Exprezz0/F-18C_Simulator/ECAD/PCBs/ABSIS/ABSIS_ALE/Assets/ABSIS_ALE-TOP_ISO.png

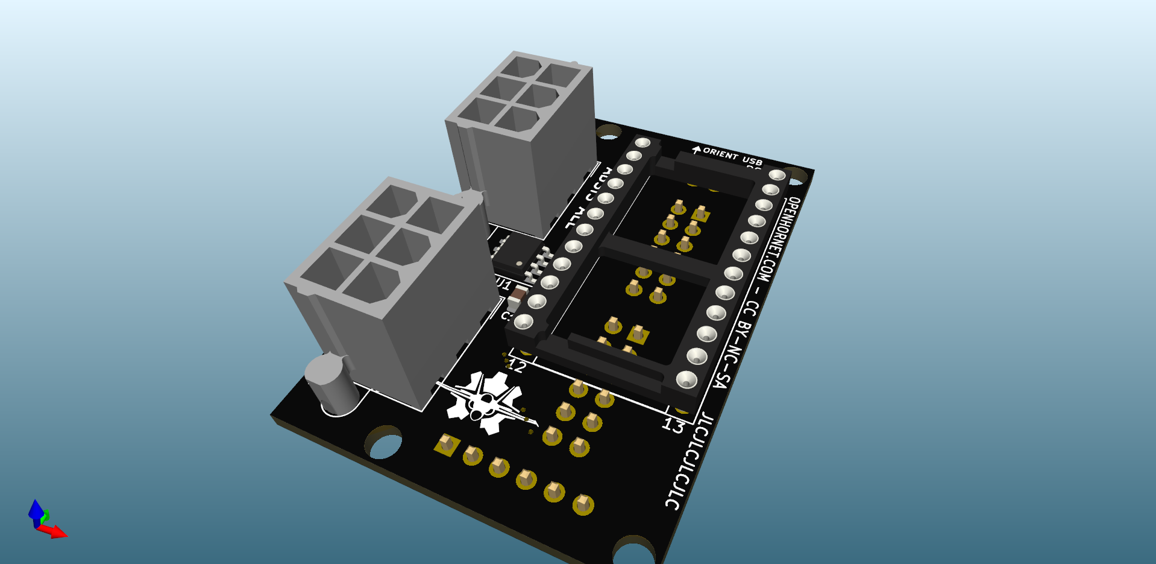
ECAD/PCBs/ABSIS/ABSIS_ALE/Assets/ABSIS_ALE-TOP_ISO.png
