Exprezz0/F-18C_Simulator/ECAD/PCBs/ABSIS/ABSIS_ALE_Relay_Module/meta/brd.png

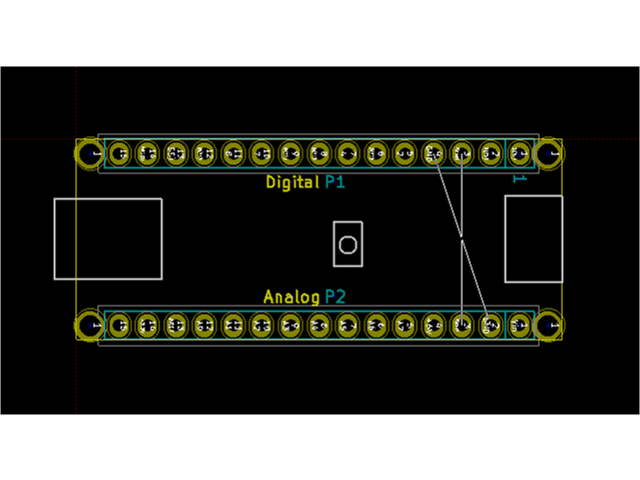
ECAD/PCBs/ABSIS/ABSIS_ALE_Relay_Module/meta/brd.png
