Exprezz0/F-18C_Simulator/ECAD/PCBs/ABSIS/ABSIS_Pit Management System/Assets/ABSIS_Pit Management System-BOT.png

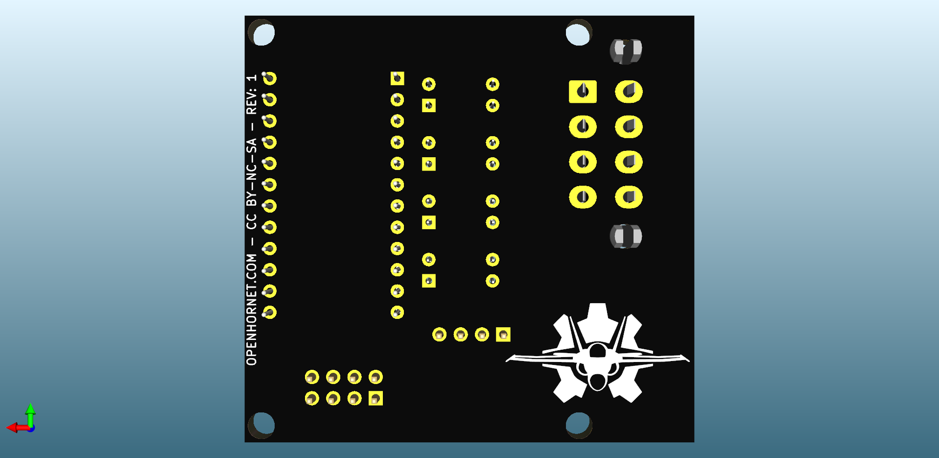
ECAD/PCBs/ABSIS/ABSIS_Pit Management System/Assets/ABSIS_Pit Management System-BOT.png
