Exprezz0/F-18C_Simulator/ECAD/PCBs/ABSIS/ABSIS_Pit Management System/Assets/ABSIS_Pit Management System-BOT_ISO.png

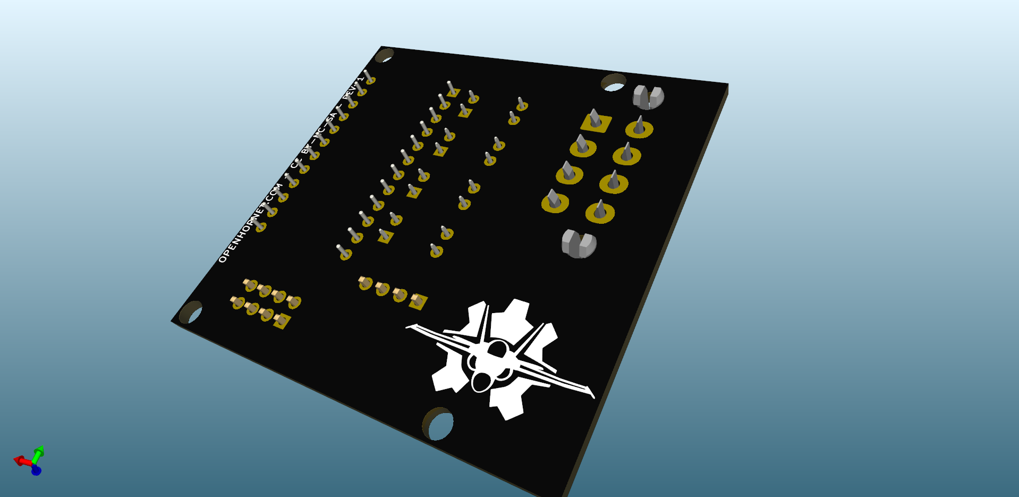
ECAD/PCBs/ABSIS/ABSIS_Pit Management System/Assets/ABSIS_Pit Management System-BOT_ISO.png
