Exprezz0/F-18C_Simulator/ECAD/PCBs/Backlight PCBs/Backlighting_Type A/ANT SEL PANEL/Assets/ANT SEL PANEL-TOP.png

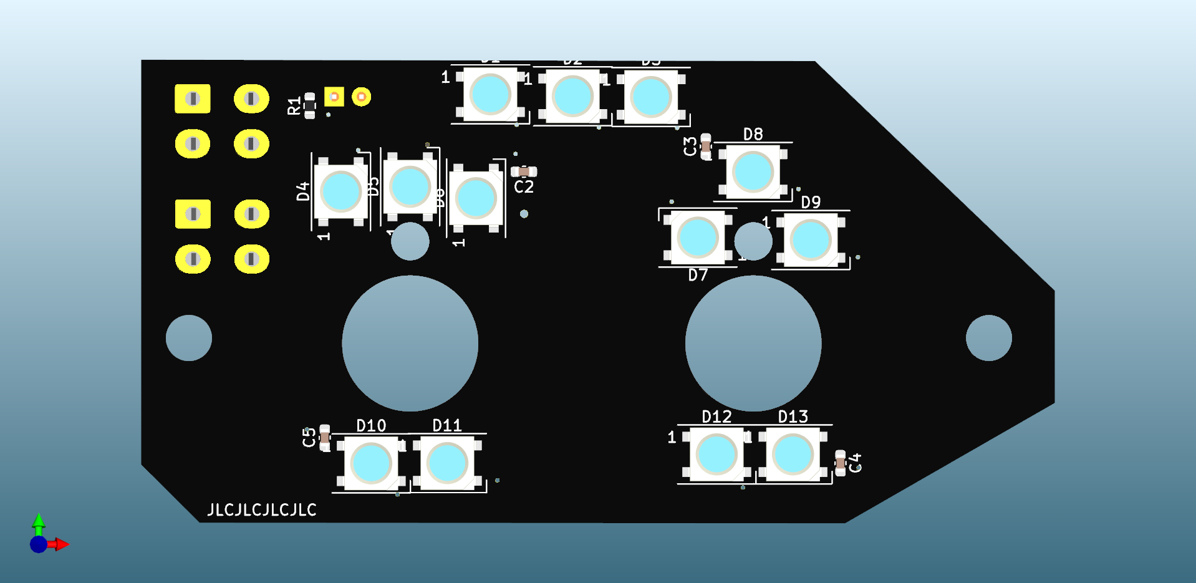
ECAD/PCBs/Backlight PCBs/Backlighting_Type A/ANT SEL PANEL/Assets/ANT SEL PANEL-TOP.png
