Exprezz0/F-18C_Simulator/ECAD/PCBs/Backlight PCBs/Backlighting_Type A/APU PANEL/Assets/APU PANEL-BOT_ISO.png

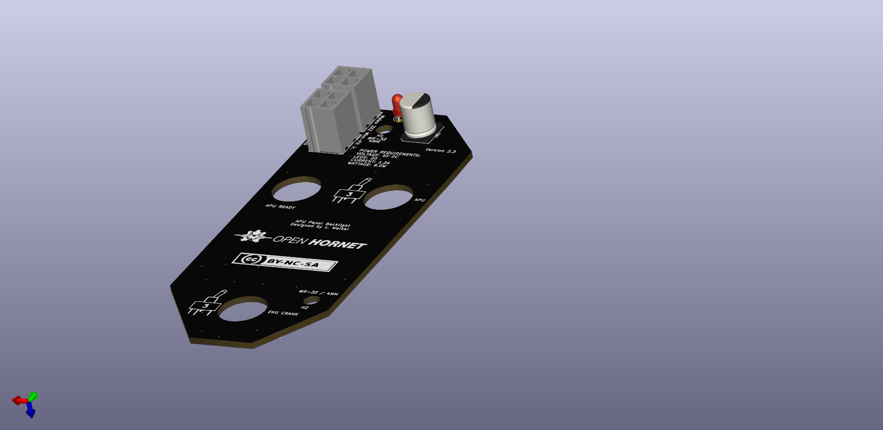
ECAD/PCBs/Backlight PCBs/Backlighting_Type A/APU PANEL/Assets/APU PANEL-BOT_ISO.png
