Exprezz0/F-18C_Simulator/ECAD/PCBs/Backlight PCBs/Backlighting_Type A/AV COOL PANEL/Assets/AV COOL PANEL-TOP_ISO.png

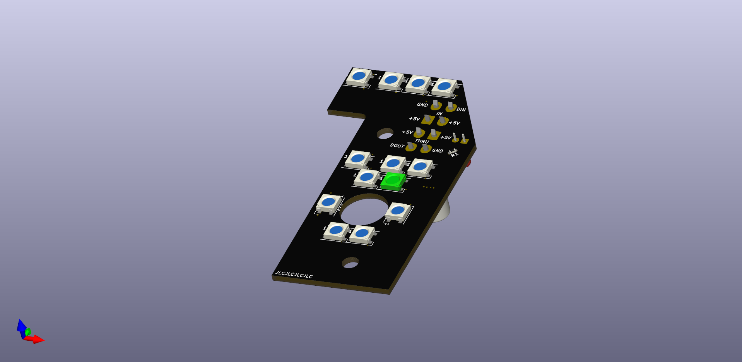
ECAD/PCBs/Backlight PCBs/Backlighting_Type A/AV COOL PANEL/Assets/AV COOL PANEL-TOP_ISO.png
