Exprezz0/F-18C_Simulator/ECAD/PCBs/Backlight PCBs/Backlighting_Type A/CAUTION LIGHTS PANEL/Assets/CAUTION LIGHTS PANEL-TOP.png

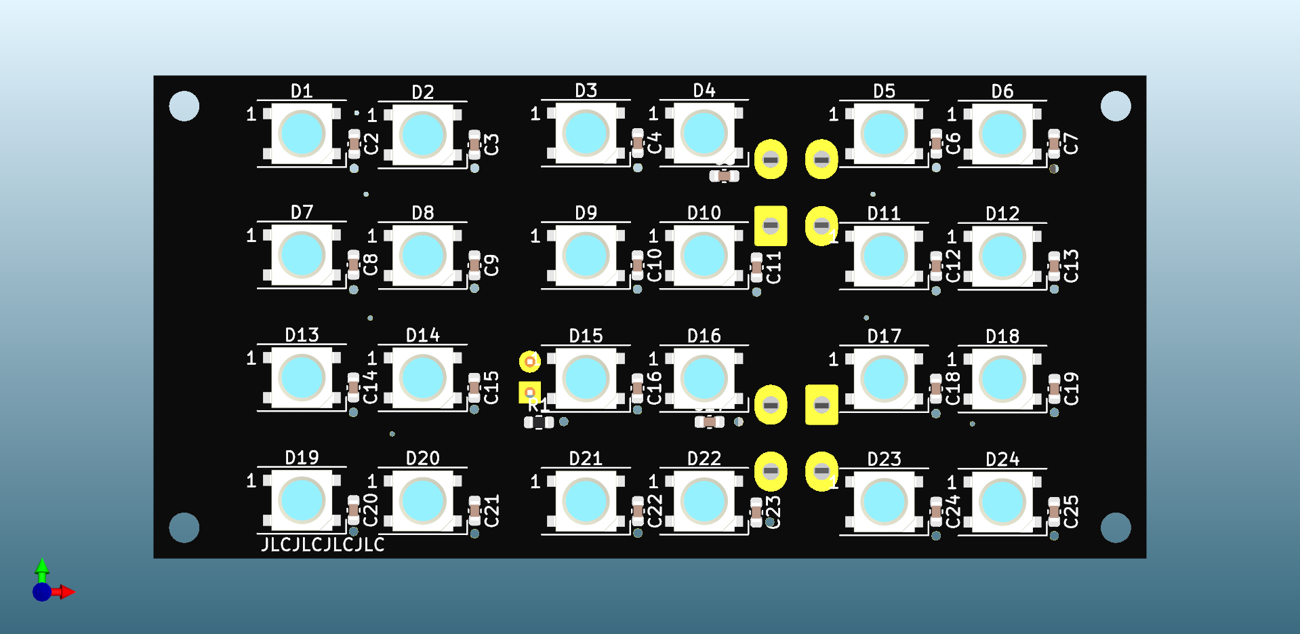
ECAD/PCBs/Backlight PCBs/Backlighting_Type A/CAUTION LIGHTS PANEL/Assets/CAUTION LIGHTS PANEL-TOP.png
