Exprezz0/F-18C_Simulator/ECAD/PCBs/Backlight PCBs/Backlighting_Type A/COMM PANEL/Assets/COMM PANEL-BOT.png

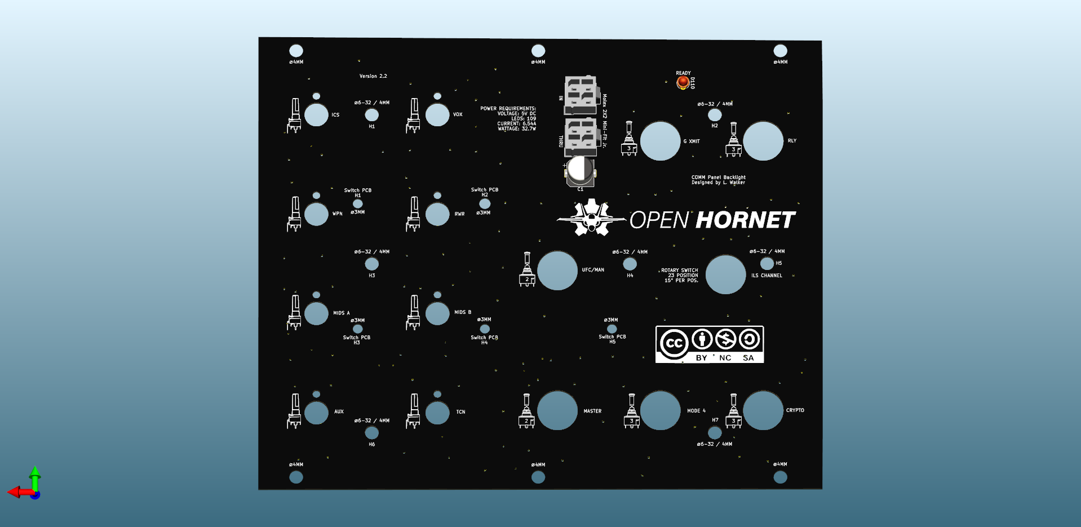
ECAD/PCBs/Backlight PCBs/Backlighting_Type A/COMM PANEL/Assets/COMM PANEL-BOT.png
