Exprezz0/F-18C_Simulator/ECAD/PCBs/Backlight PCBs/Backlighting_Type A/DEFOG PANEL/Assets/DEFOG PANEL_TOP-ISO.png

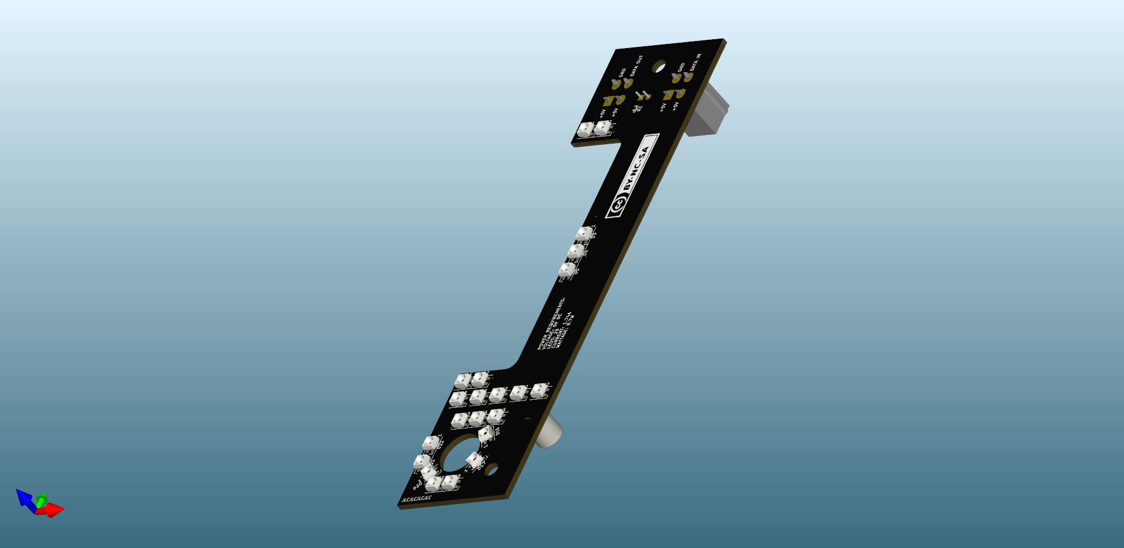
ECAD/PCBs/Backlight PCBs/Backlighting_Type A/DEFOG PANEL/Assets/DEFOG PANEL_TOP-ISO.png
