Exprezz0/F-18C_Simulator/ECAD/PCBs/Backlight PCBs/Backlighting_Type A/ECM DISP PANEL/Assets/ECM DISP PANEL_TOP-ISO.png

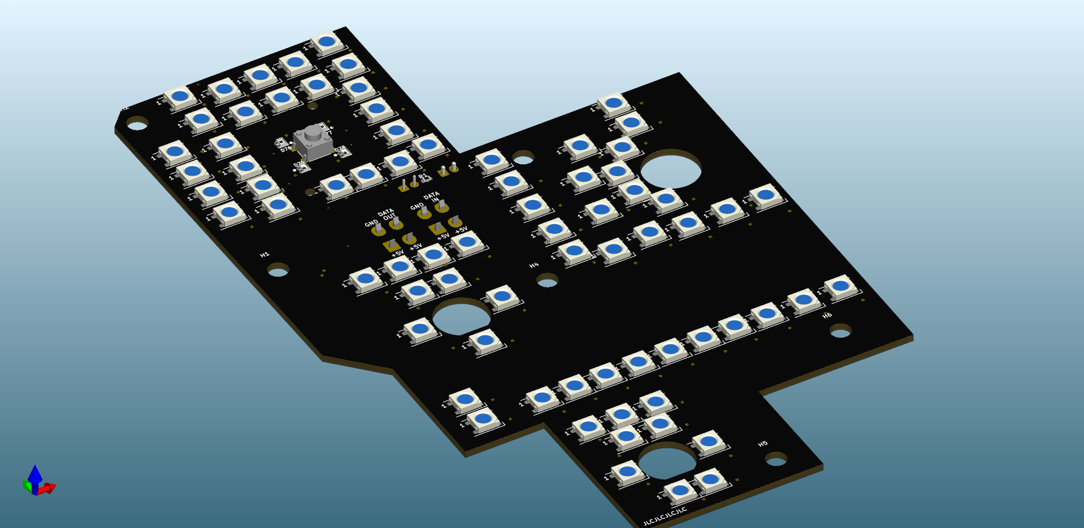
ECAD/PCBs/Backlight PCBs/Backlighting_Type A/ECM DISP PANEL/Assets/ECM DISP PANEL_TOP-ISO.png
