Exprezz0/F-18C_Simulator/ECAD/PCBs/Backlight PCBs/Backlighting_Type A/ELEC PANEL/Assets/ELEC PANEL_BOT.png

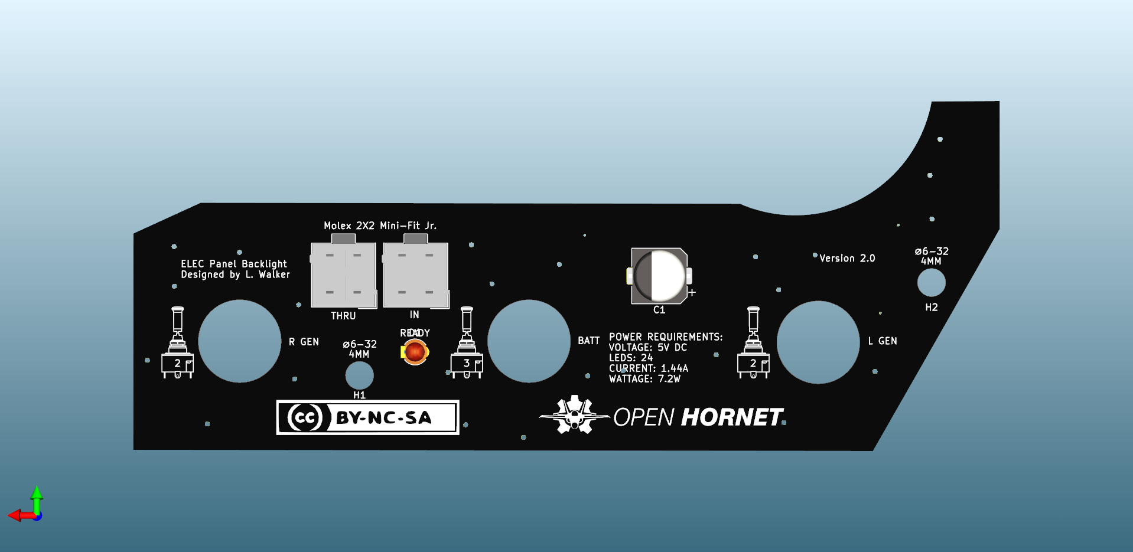
ECAD/PCBs/Backlight PCBs/Backlighting_Type A/ELEC PANEL/Assets/ELEC PANEL_BOT.png
