Exprezz0/F-18C_Simulator/ECAD/PCBs/Backlight PCBs/Backlighting_Type A/FUEL PANEL/Assets/FUEL PANEL_TOP-ISO.png

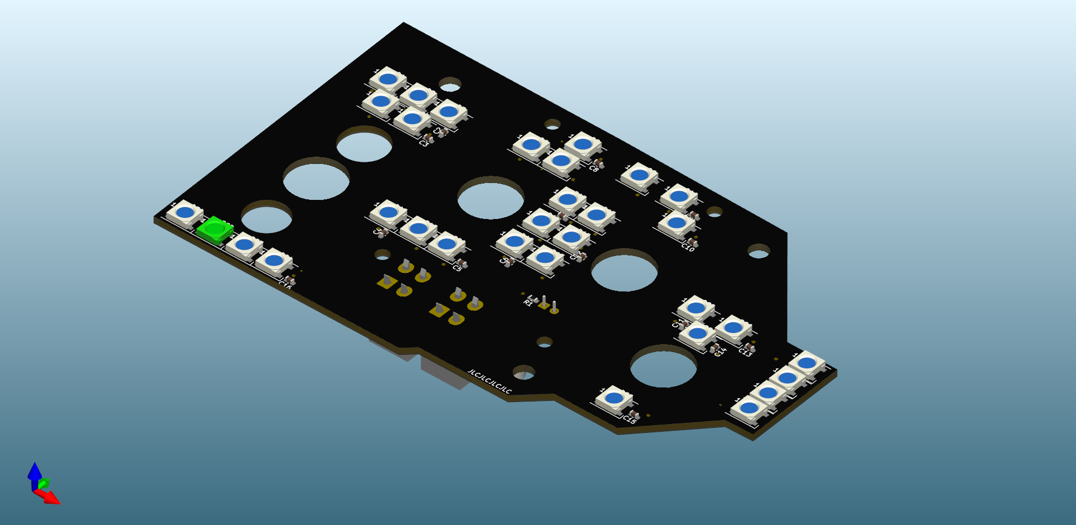
ECAD/PCBs/Backlight PCBs/Backlighting_Type A/FUEL PANEL/Assets/FUEL PANEL_TOP-ISO.png
