Exprezz0/F-18C_Simulator/ECAD/PCBs/Backlight PCBs/Backlighting_Type A/GEN TIE PANEL/Assets/GEN TIE PANEL_BOT.png

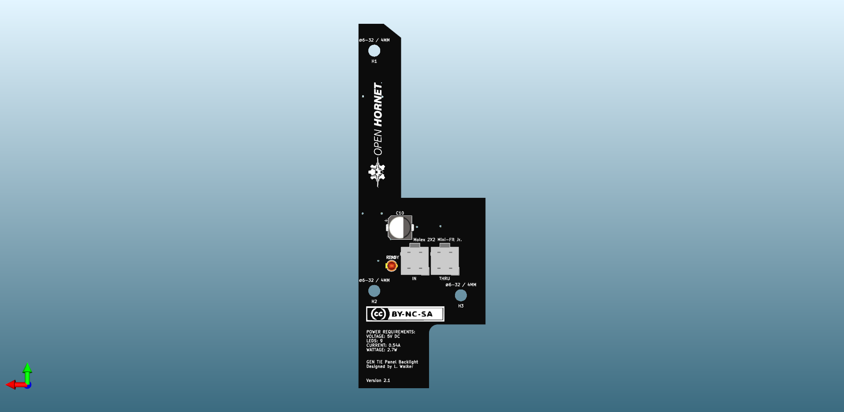
ECAD/PCBs/Backlight PCBs/Backlighting_Type A/GEN TIE PANEL/Assets/GEN TIE PANEL_BOT.png
