Exprezz0/F-18C_Simulator/ECAD/PCBs/Backlight PCBs/Backlighting_Type A/HUD PANEL/Assets/HUD PANEL_TOP.png

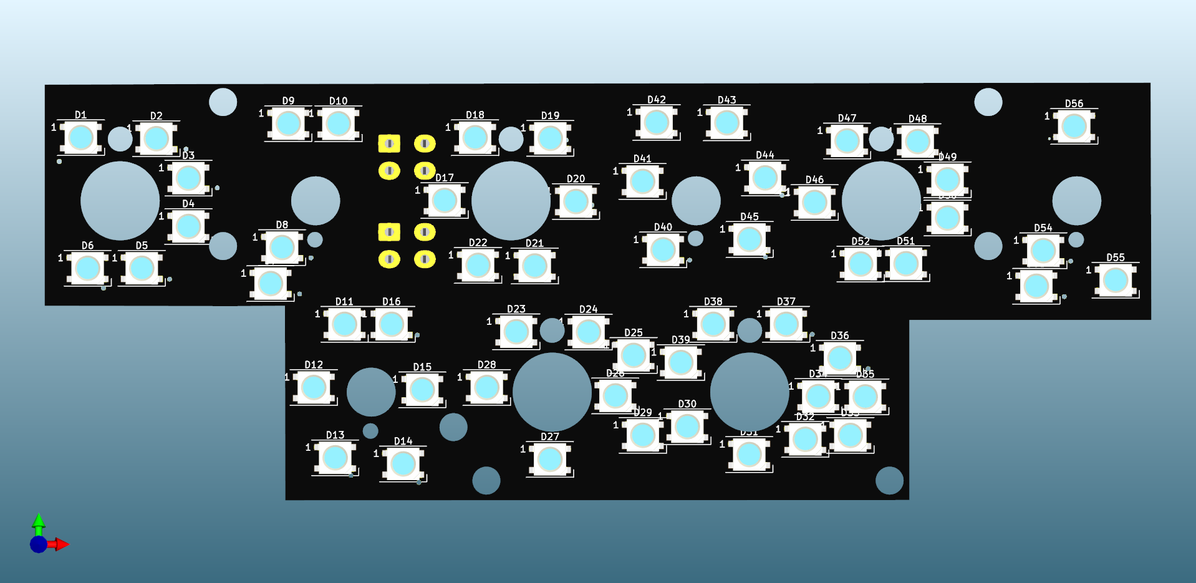
ECAD/PCBs/Backlight PCBs/Backlighting_Type A/HUD PANEL/Assets/HUD PANEL_TOP.png
