Exprezz0/F-18C_Simulator/ECAD/PCBs/Backlight PCBs/Backlighting_Type A/HUD VID RCD PANEL/Assets/HUD VID RCD PANEL_BOT.png

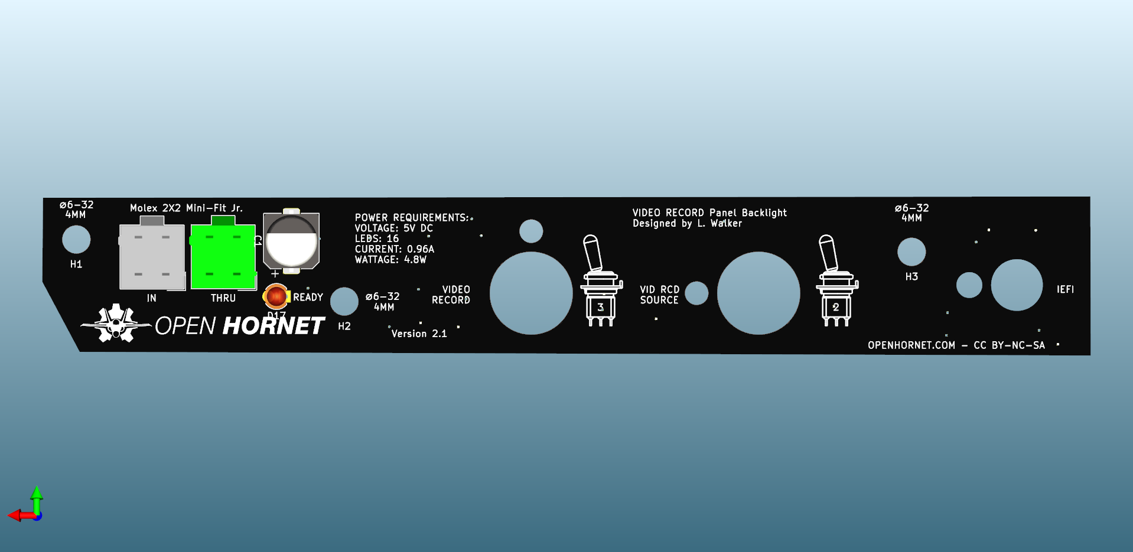
ECAD/PCBs/Backlight PCBs/Backlighting_Type A/HUD VID RCD PANEL/Assets/HUD VID RCD PANEL_BOT.png
