Exprezz0/F-18C_Simulator/ECAD/PCBs/Backlight PCBs/Backlighting_Type A/HYD ISO PANEL/Assets/HYD ISO PANEL_BOT.png

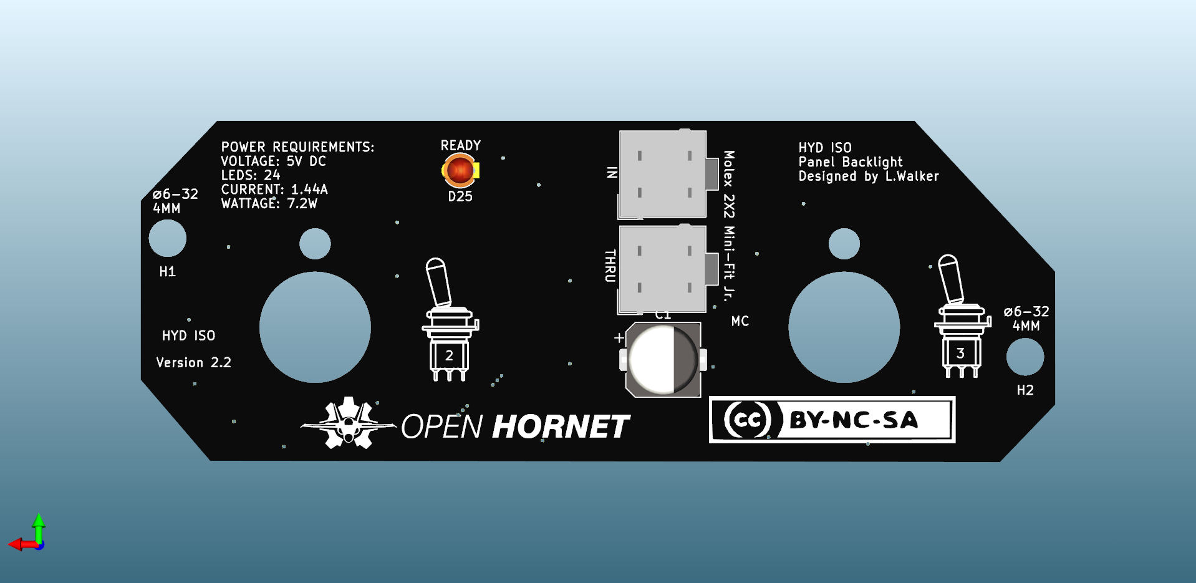
ECAD/PCBs/Backlight PCBs/Backlighting_Type A/HYD ISO PANEL/Assets/HYD ISO PANEL_BOT.png
