Exprezz0/F-18C_Simulator/ECAD/PCBs/Backlight PCBs/Backlighting_Type A/INTR LT PANEL/Assets/INTR LT PANEL-BOT_ISO.png

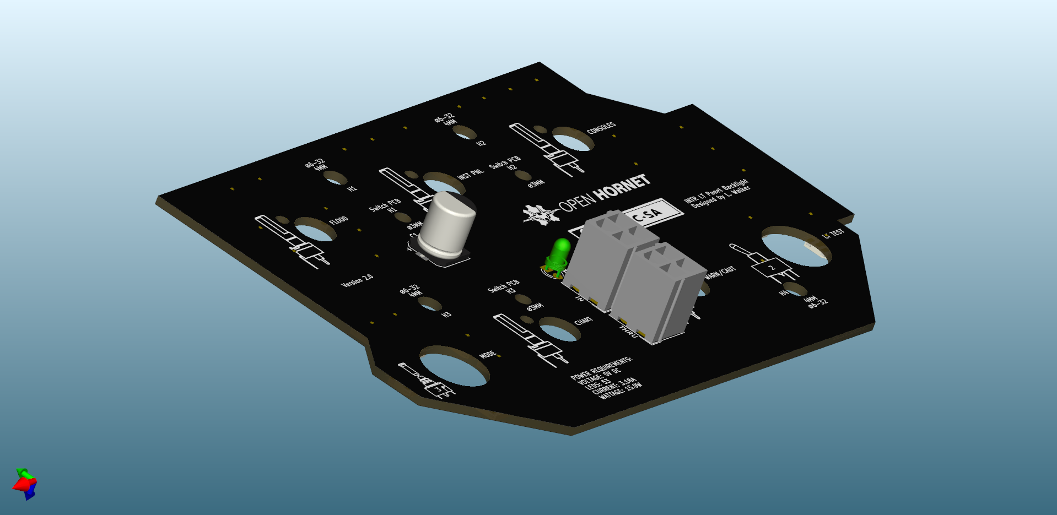
ECAD/PCBs/Backlight PCBs/Backlighting_Type A/INTR LT PANEL/Assets/INTR LT PANEL-BOT_ISO.png
