Exprezz0/F-18C_Simulator/ECAD/PCBs/Backlight PCBs/Backlighting_Type A/JETT STATION SELECT PLACARD/Assets/JETT STATION SELECT PLACARD_BOT.png

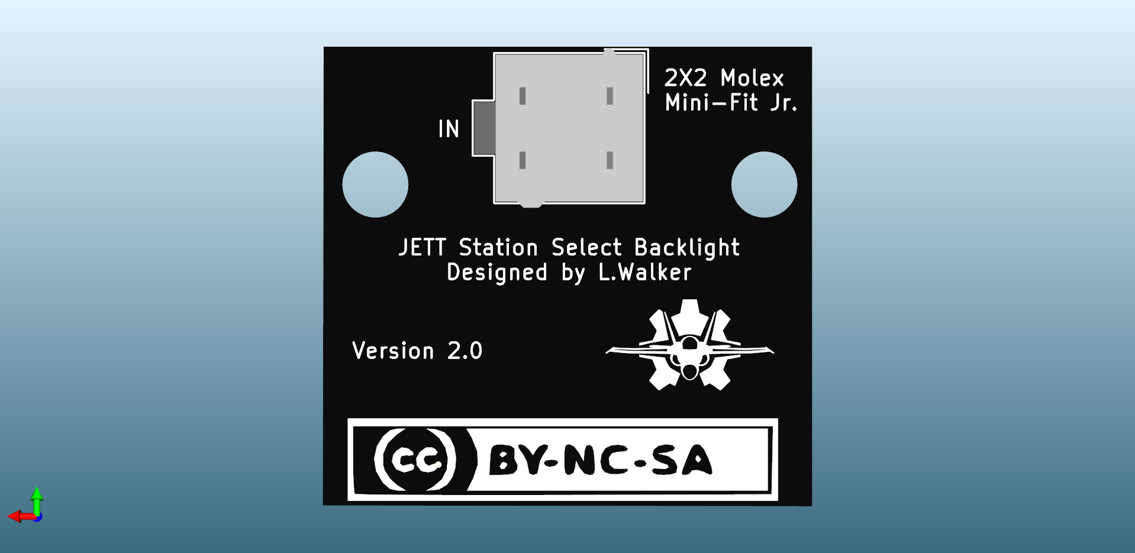
ECAD/PCBs/Backlight PCBs/Backlighting_Type A/JETT STATION SELECT PLACARD/Assets/JETT STATION SELECT PLACARD_BOT.png
