Exprezz0/F-18C_Simulator/ECAD/PCBs/Backlight PCBs/Backlighting_Type A/KY-58 PANEL/Assets/KY-58 PANEL_TOP-ISO.png

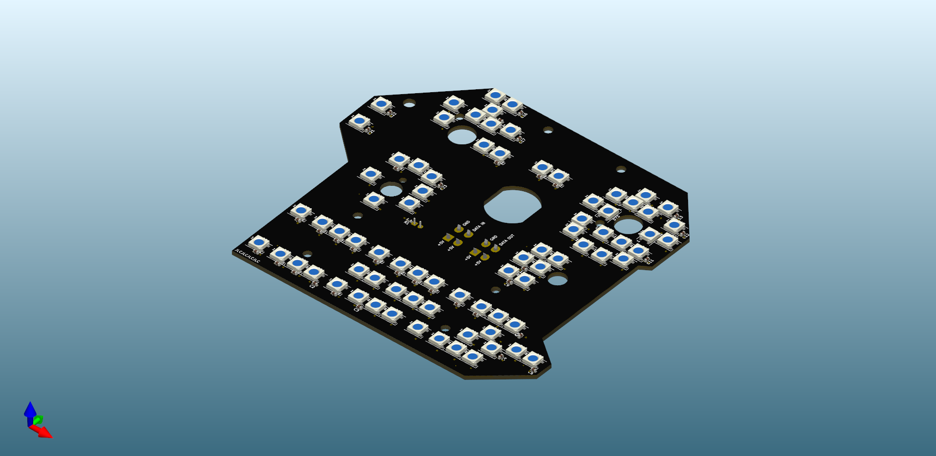
ECAD/PCBs/Backlight PCBs/Backlighting_Type A/KY-58 PANEL/Assets/KY-58 PANEL_TOP-ISO.png
