Exprezz0/F-18C_Simulator/ECAD/PCBs/Backlight PCBs/Backlighting_Type A/LANDING GEAR PANEL/Assets/LANDING GEAR PANEL_BOT.png

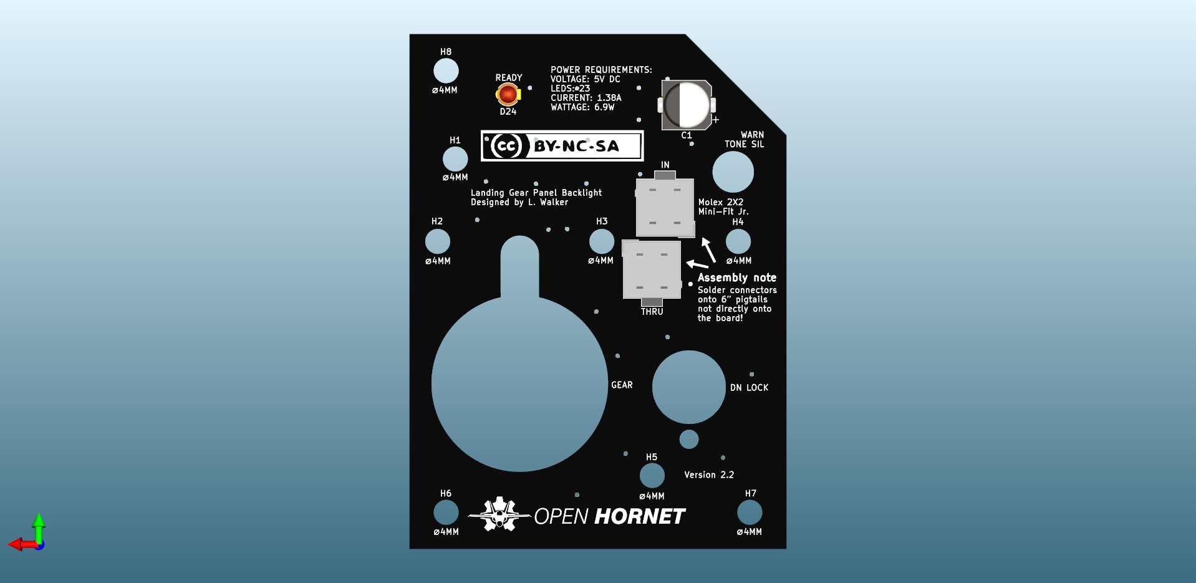
ECAD/PCBs/Backlight PCBs/Backlighting_Type A/LANDING GEAR PANEL/Assets/LANDING GEAR PANEL_BOT.png
