Exprezz0/F-18C_Simulator/ECAD/PCBs/Backlight PCBs/Backlighting_Type A/LDG WING FOLD PLACARD/Assets/LDG WING FOLD PLACARD_BOT-ISO.png

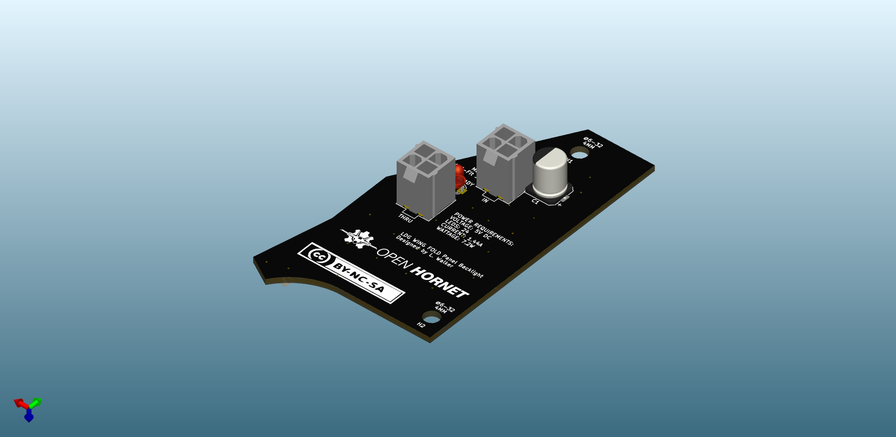
ECAD/PCBs/Backlight PCBs/Backlighting_Type A/LDG WING FOLD PLACARD/Assets/LDG WING FOLD PLACARD_BOT-ISO.png
