Exprezz0/F-18C_Simulator/ECAD/PCBs/Backlight PCBs/Backlighting_Type A/MASTER ARM PANEL/Assets/MASTER ARM PANEL_TOP-ISO.png

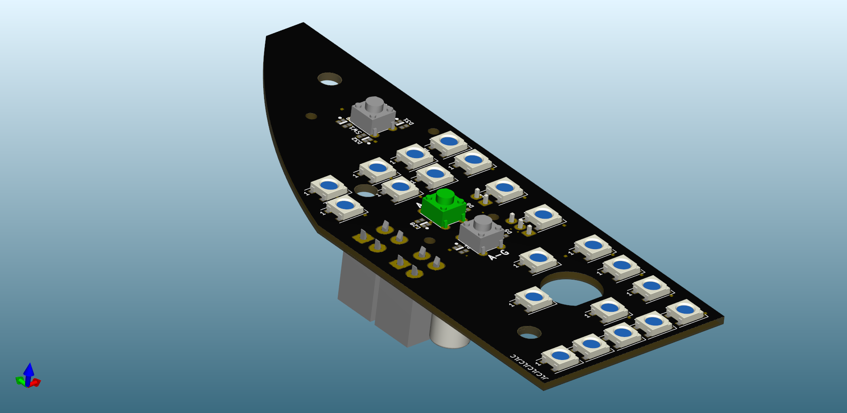
ECAD/PCBs/Backlight PCBs/Backlighting_Type A/MASTER ARM PANEL/Assets/MASTER ARM PANEL_TOP-ISO.png
