Exprezz0/F-18C_Simulator/ECAD/PCBs/Backlight PCBs/Backlighting_Type A/OBOGS PANEL/Assets/OBOGS PANEL_TOP-ISO.png

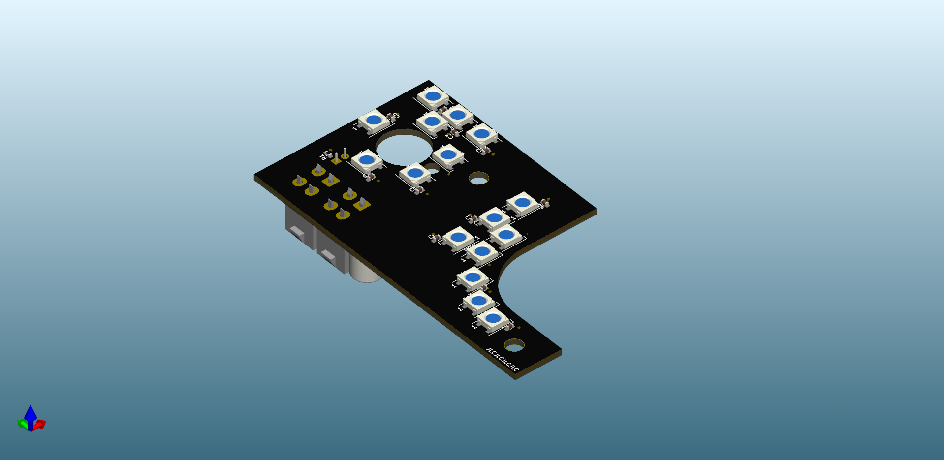
ECAD/PCBs/Backlight PCBs/Backlighting_Type A/OBOGS PANEL/Assets/OBOGS PANEL_TOP-ISO.png
