Exprezz0/F-18C_Simulator/ECAD/PCBs/Backlight PCBs/Backlighting_Type A/SELECT JETT PANEL/Assets/SELECT JETT PANEL_BOT-ISO.png

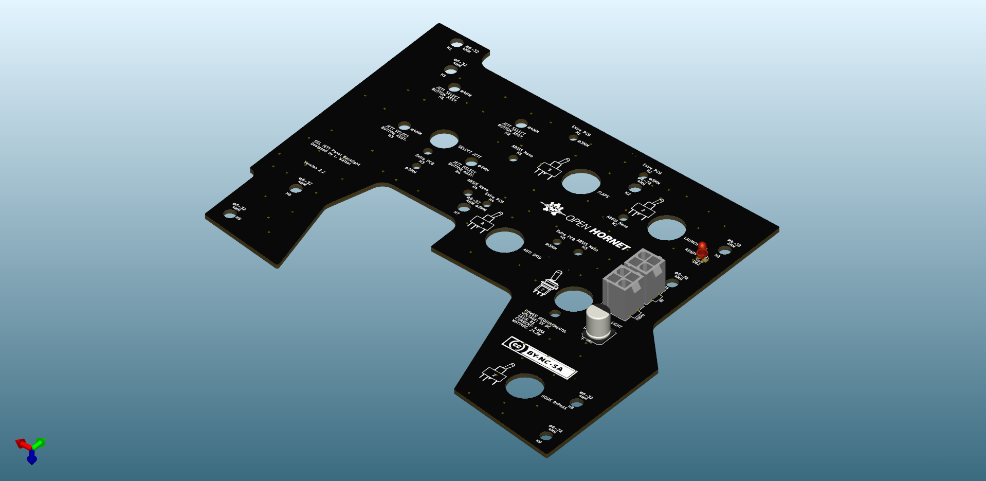
ECAD/PCBs/Backlight PCBs/Backlighting_Type A/SELECT JETT PANEL/Assets/SELECT JETT PANEL_BOT-ISO.png
