Exprezz0/F-18C_Simulator/ECAD/PCBs/Backlight PCBs/Backlighting_Type A/SIM CONTROL PANEL/Assets/SIM CONTROL PANEL_TOP-ISO.png

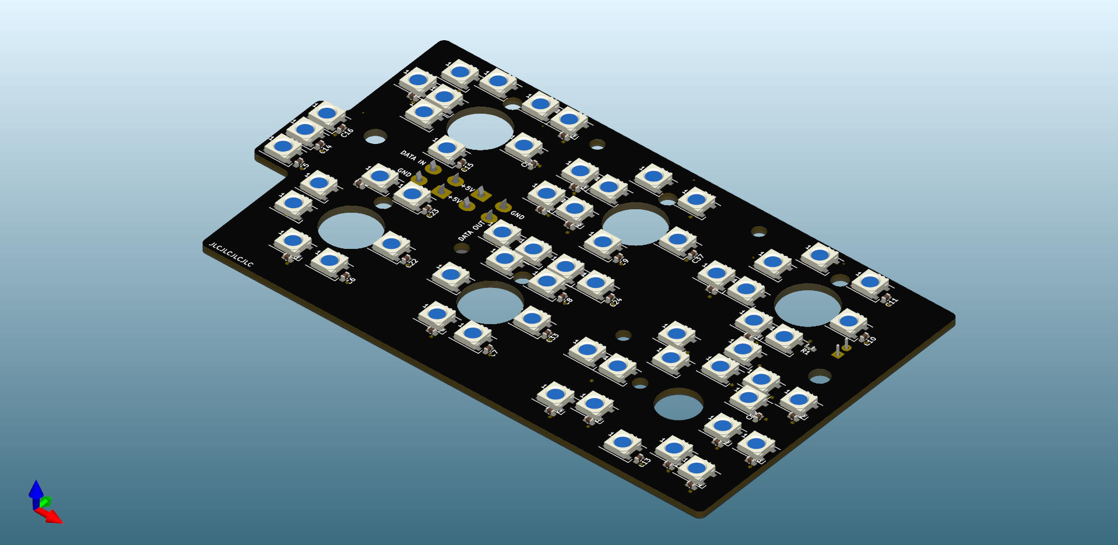
ECAD/PCBs/Backlight PCBs/Backlighting_Type A/SIM CONTROL PANEL/Assets/SIM CONTROL PANEL_TOP-ISO.png
