Exprezz0/F-18C_Simulator/ECAD/PCBs/Backlight PCBs/Backlighting_Type A/SIM POWER PANEL/Assets/SIM POWER PANEL_BOT-ISO.png

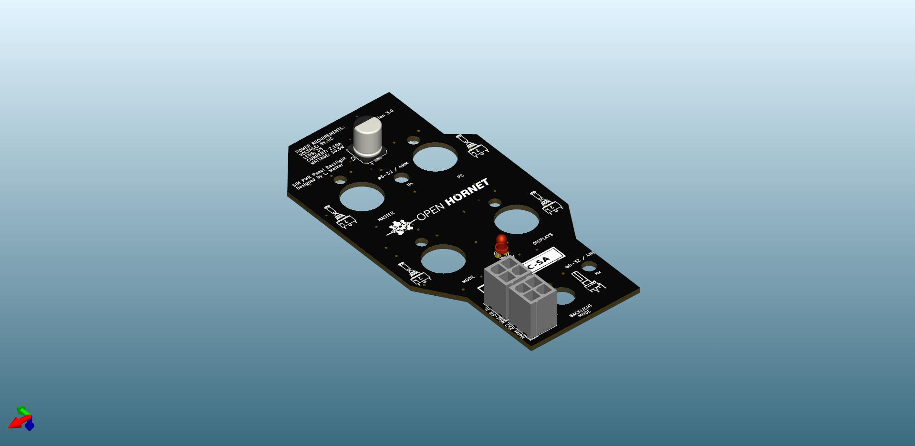
ECAD/PCBs/Backlight PCBs/Backlighting_Type A/SIM POWER PANEL/Assets/SIM POWER PANEL_BOT-ISO.png
