Exprezz0/F-18C_Simulator/ECAD/PCBs/Backlight PCBs/Backlighting_Type A/SPIN RCV PANEL/Assets/SPIN RCV PANEL_BOT-ISO.png

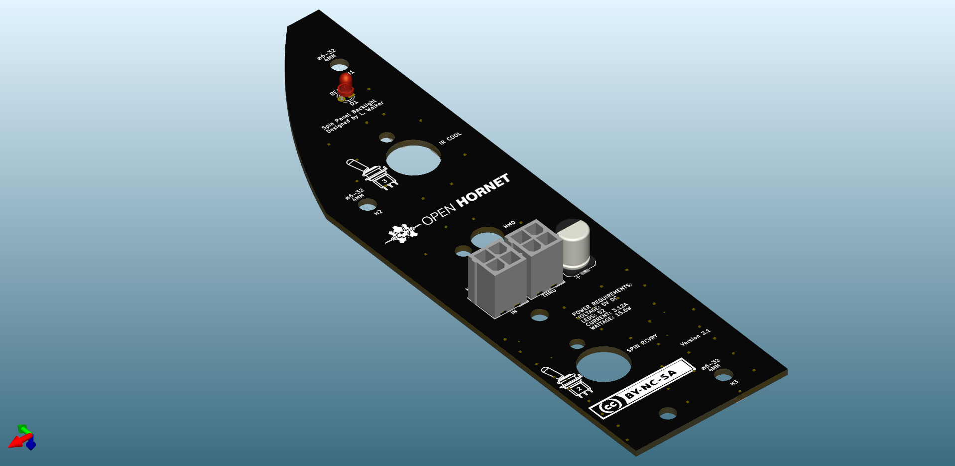
ECAD/PCBs/Backlight PCBs/Backlighting_Type A/SPIN RCV PANEL/Assets/SPIN RCV PANEL_BOT-ISO.png
