Exprezz0/F-18C_Simulator/ECAD/PCBs/Functional PCBs/AMPCD/Assets/AMPCD-BOT_ISO.png

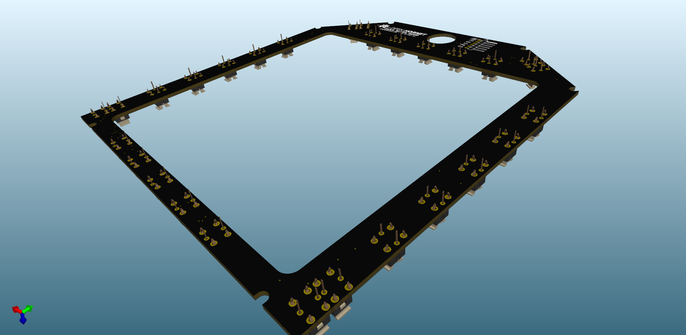
ECAD/PCBs/Functional PCBs/AMPCD/Assets/AMPCD-BOT_ISO.png
