Exprezz0/F-18C_Simulator/ECAD/PCBs/Functional PCBs/CONTROLLER_AMPCD DDI/Assets/CONTROLLER_AMPCD DDI-TOP.png

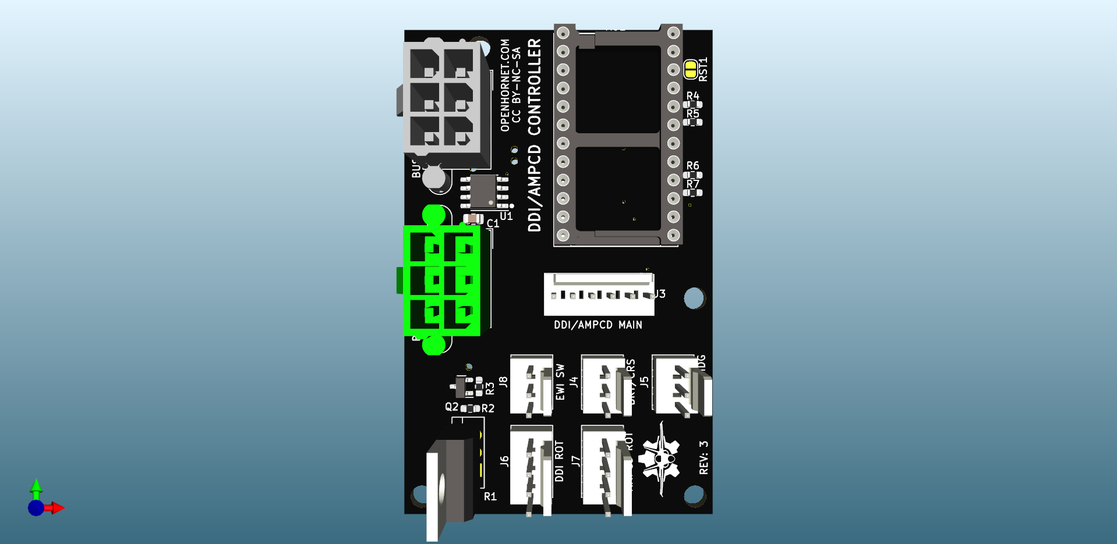
ECAD/PCBs/Functional PCBs/CONTROLLER_AMPCD DDI/Assets/CONTROLLER_AMPCD DDI-TOP.png
