Exprezz0/F-18C_Simulator/ECAD/PCBs/Functional PCBs/CONTROLLER_Radar Altimeter/Assets/CONTROLLER_Radar Altimeter-BOT_ISO.png

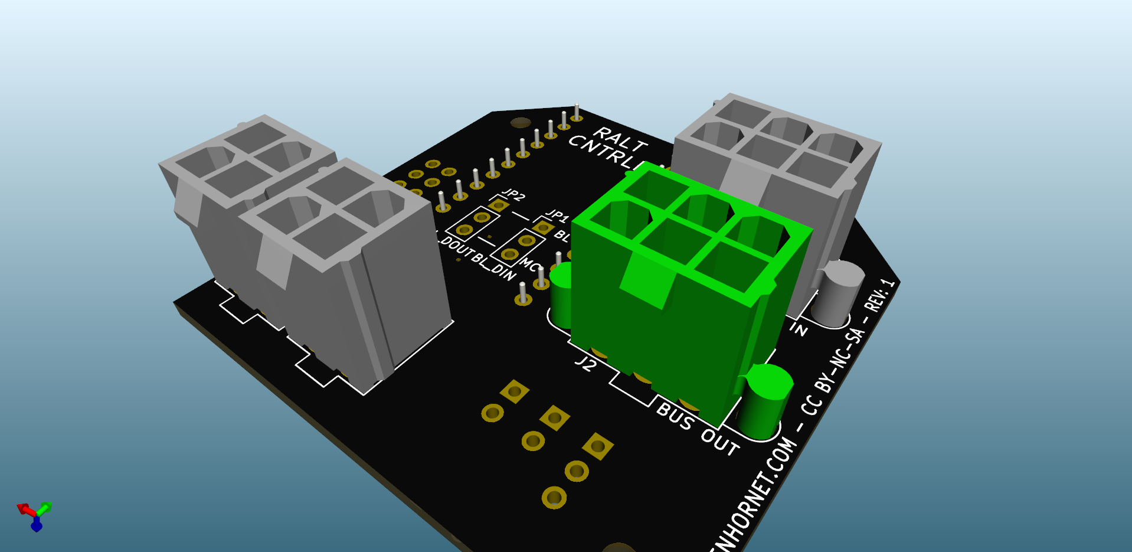
ECAD/PCBs/Functional PCBs/CONTROLLER_Radar Altimeter/Assets/CONTROLLER_Radar Altimeter-BOT_ISO.png
