Exprezz0/F-18C_Simulator/ECAD/PCBs/Functional PCBs/CONTROLLER_Standby Instrument/Assets/CONTROLLER_Standby Instrument-BOT.png

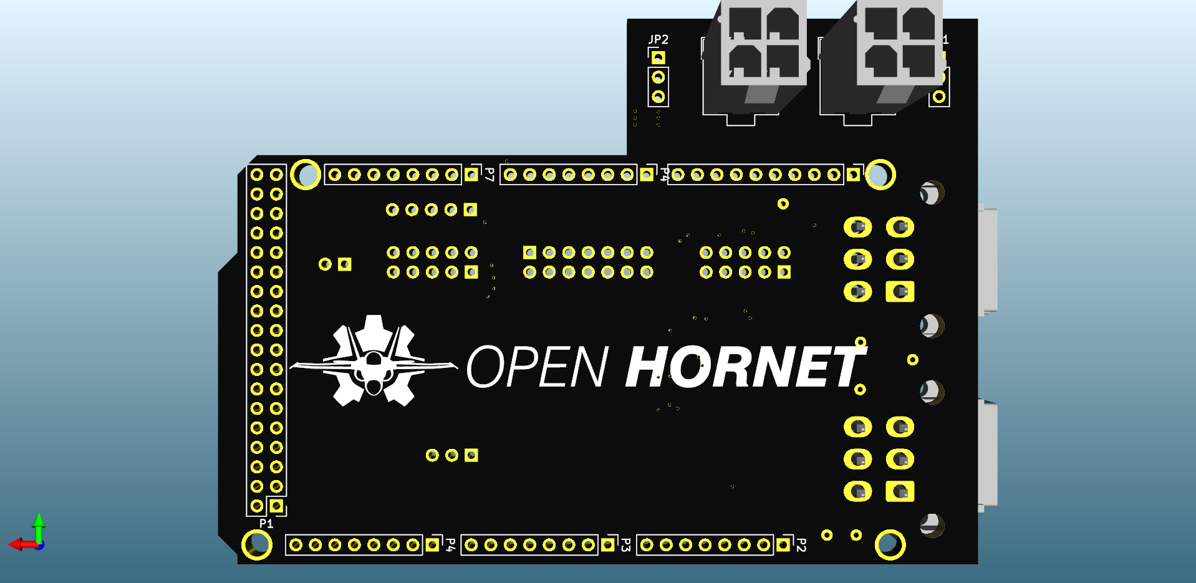
ECAD/PCBs/Functional PCBs/CONTROLLER_Standby Instrument/Assets/CONTROLLER_Standby Instrument-BOT.png
