Exprezz0/F-18C_Simulator/ECAD/PCBs/Functional PCBs/CONTROLLER_Stick/Assets/CONTROLLER_Stick-BOT_ISO.png

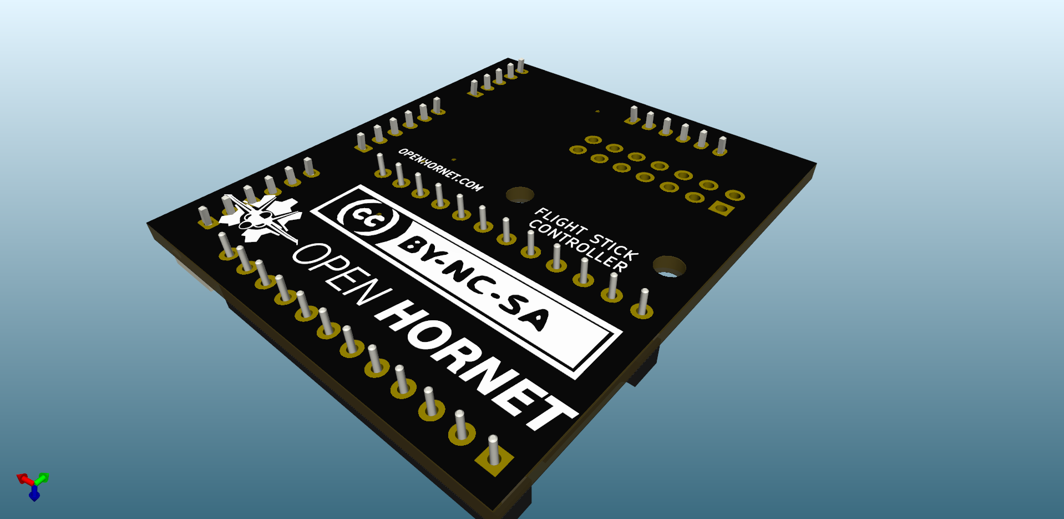
ECAD/PCBs/Functional PCBs/CONTROLLER_Stick/Assets/CONTROLLER_Stick-BOT_ISO.png
