Exprezz0/F-18C_Simulator/ECAD/PCBs/Functional PCBs/CONTROLLER_Throttle/Assets/CONTROLLER_Throttle-BOT_ISO.png

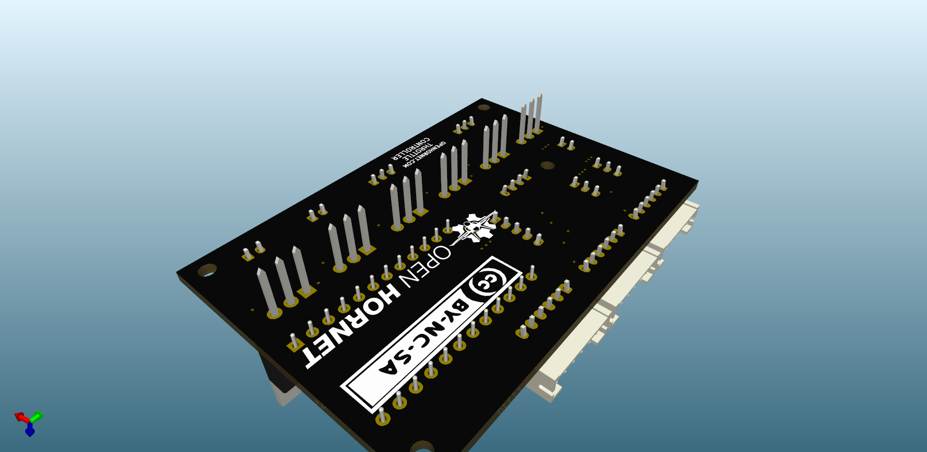
ECAD/PCBs/Functional PCBs/CONTROLLER_Throttle/Assets/CONTROLLER_Throttle-BOT_ISO.png
