Exprezz0/F-18C_Simulator/ECAD/PCBs/Functional PCBs/CONTROLLER_Throttle/Assets/CONTROLLER_Throttle-TOP.png

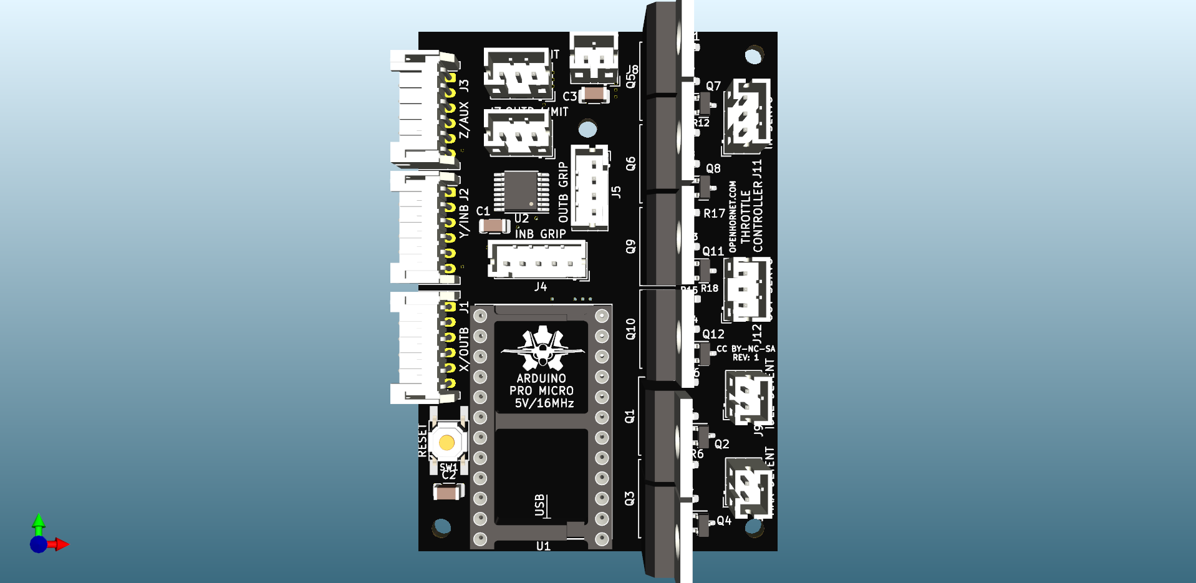
ECAD/PCBs/Functional PCBs/CONTROLLER_Throttle/Assets/CONTROLLER_Throttle-TOP.png
