Exprezz0/F-18C_Simulator/ECAD/PCBs/Functional PCBs/CONTROLLER_Throttle/Assets/CONTROLLER_Throttle-TOP_ISO.png

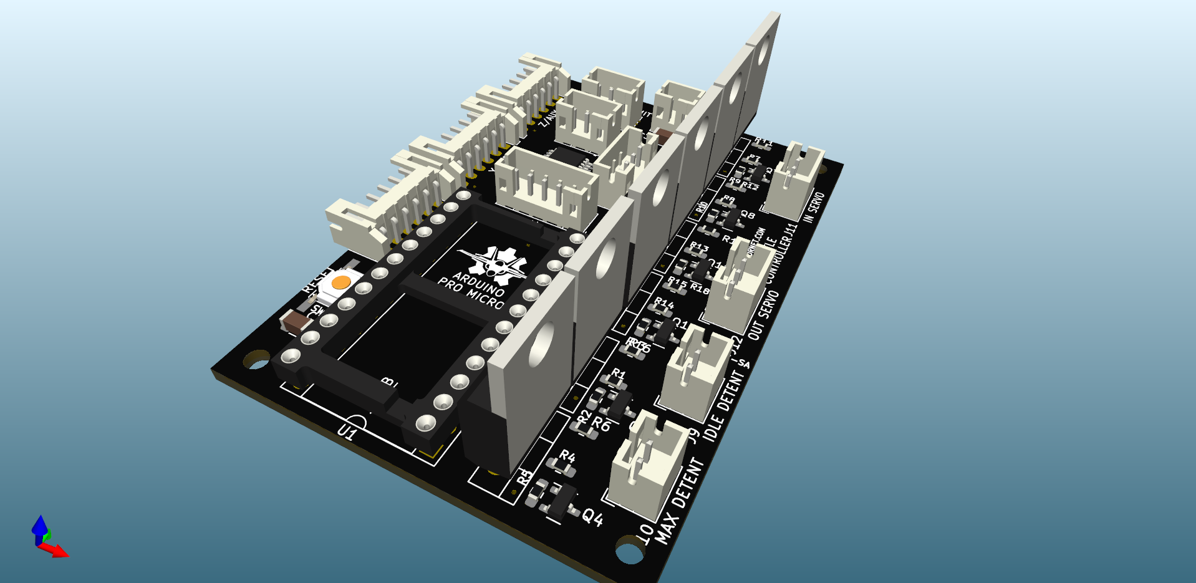
ECAD/PCBs/Functional PCBs/CONTROLLER_Throttle/Assets/CONTROLLER_Throttle-TOP_ISO.png
