Exprezz0/F-18C_Simulator/ECAD/PCBs/Functional PCBs/DDI/Assets/DDI-BOT_ISO.png

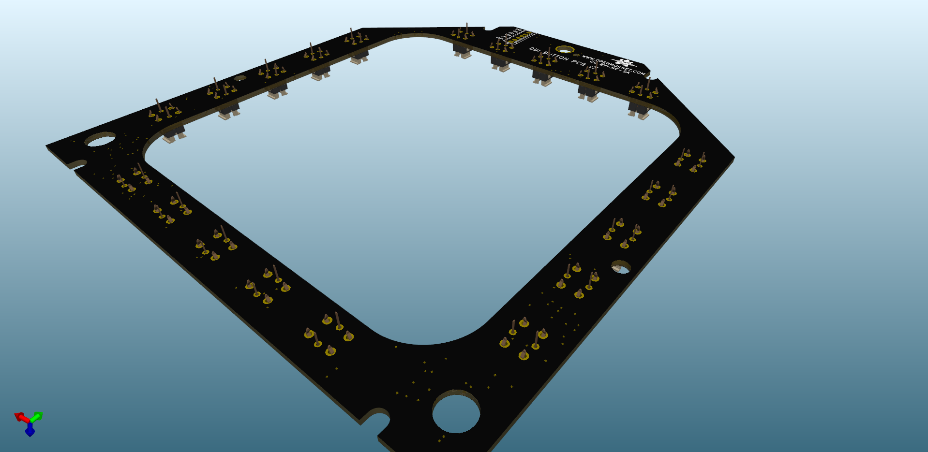
ECAD/PCBs/Functional PCBs/DDI/Assets/DDI-BOT_ISO.png
