Exprezz0/F-18C_Simulator/ECAD/PCBs/Functional PCBs/DDI/Assets/DDI-TOP_ISO.png

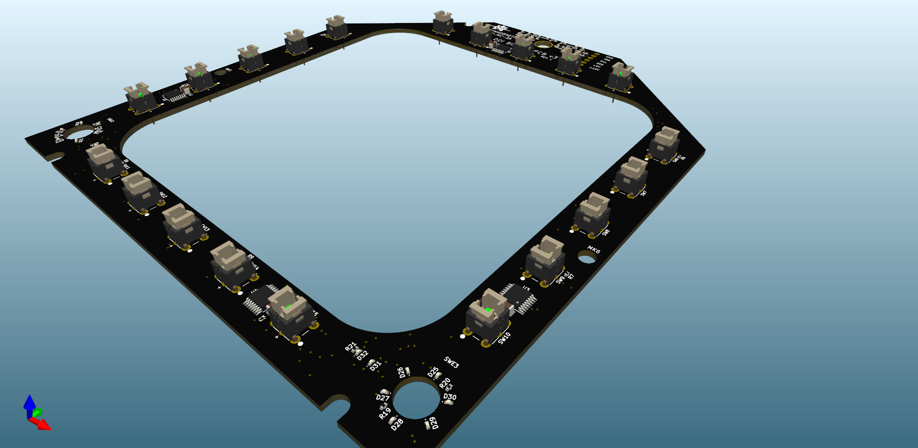
ECAD/PCBs/Functional PCBs/DDI/Assets/DDI-TOP_ISO.png
