Exprezz0/F-18C_Simulator/ECAD/PCBs/Functional PCBs/ewi_v3/ewi_v3 Left Front.png

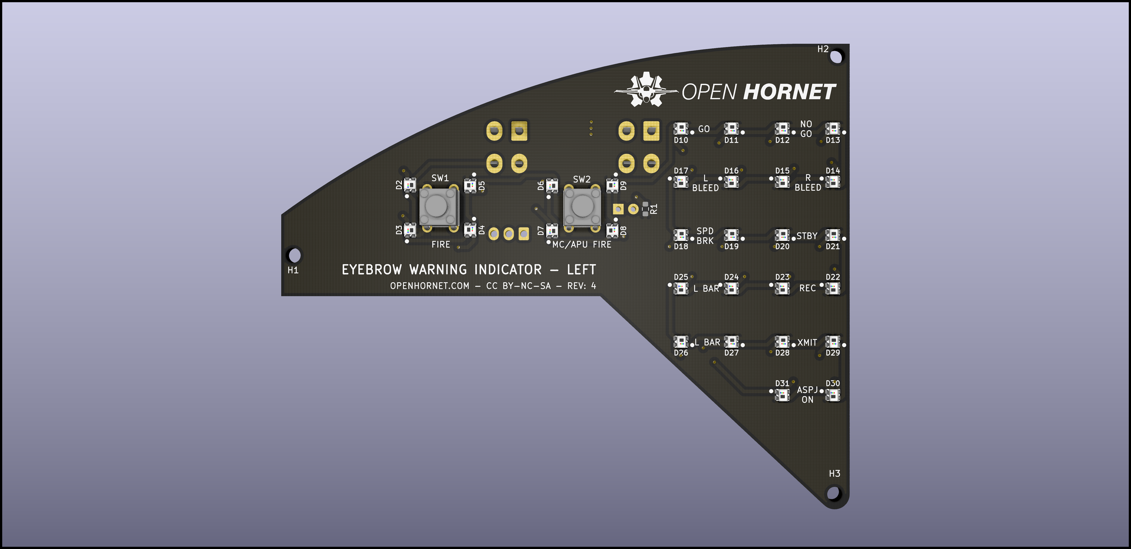
ECAD/PCBs/Functional PCBs/ewi_v3/ewi_v3 Left Front.png
