Exprezz0/F-18C_Simulator/ECAD/PCBs/Functional PCBs/EYEBROW WARNING INDICATOR_LEFT/Assets/EYEBROW WARNING INDICATOR_LEFT-TOP.png

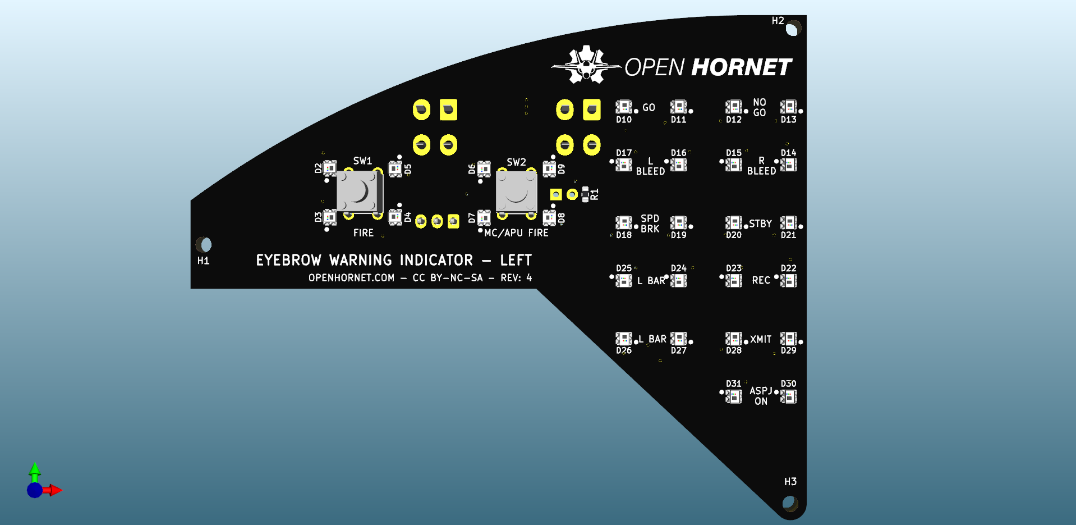
ECAD/PCBs/Functional PCBs/EYEBROW WARNING INDICATOR_LEFT/Assets/EYEBROW WARNING INDICATOR_LEFT-TOP.png
