Exprezz0/F-18C_Simulator/ECAD/PCBs/Functional PCBs/EYEBROW WARNING INDICATOR_RIGHT/Assets/EYEBROW WARNING INDICATOR_RIGHT-BOT.png

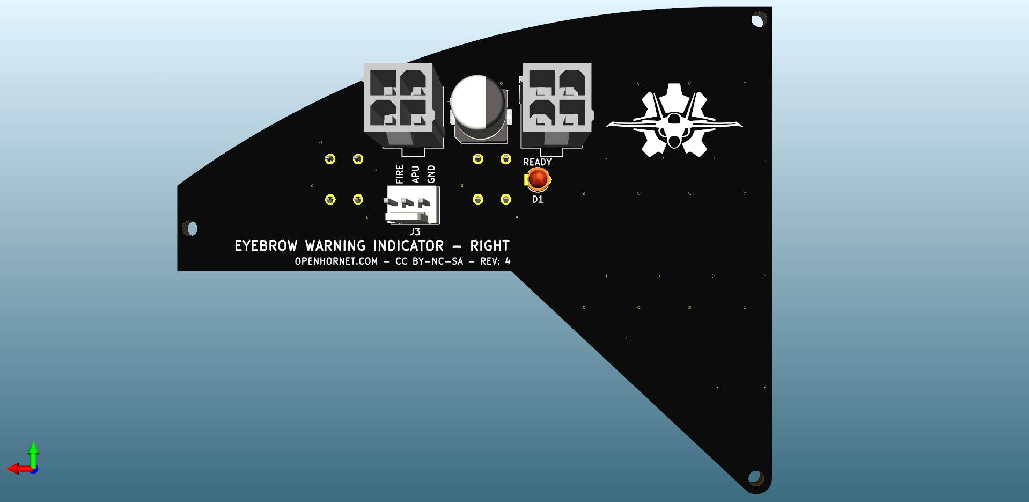
ECAD/PCBs/Functional PCBs/EYEBROW WARNING INDICATOR_RIGHT/Assets/EYEBROW WARNING INDICATOR_RIGHT-BOT.png
