Exprezz0/F-18C_Simulator/ECAD/PCBs/Functional PCBs/GAUGE_Analog Instruments/Assets/GAUGE_Analog Instruments-BOT_ISO.png

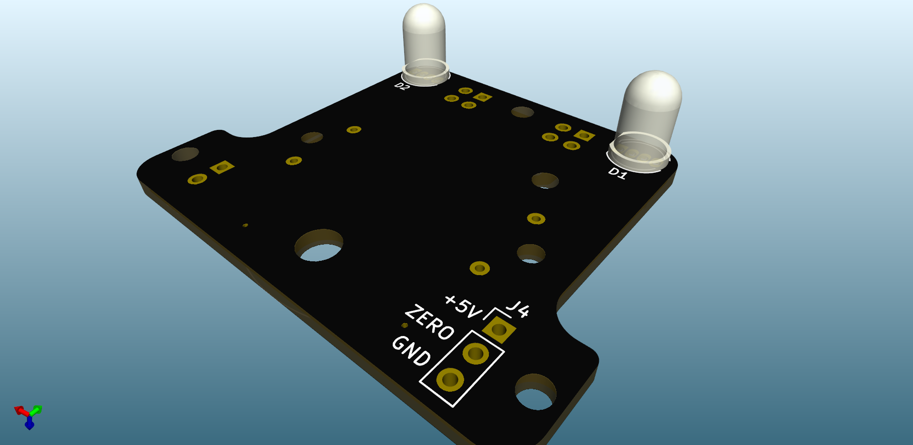
ECAD/PCBs/Functional PCBs/GAUGE_Analog Instruments/Assets/GAUGE_Analog Instruments-BOT_ISO.png
