Exprezz0/F-18C_Simulator/ECAD/PCBs/Functional PCBs/GAUGE_Dual Needle Instruments/Assets/GAUGE_Dual Needle Instruments-TOP.png

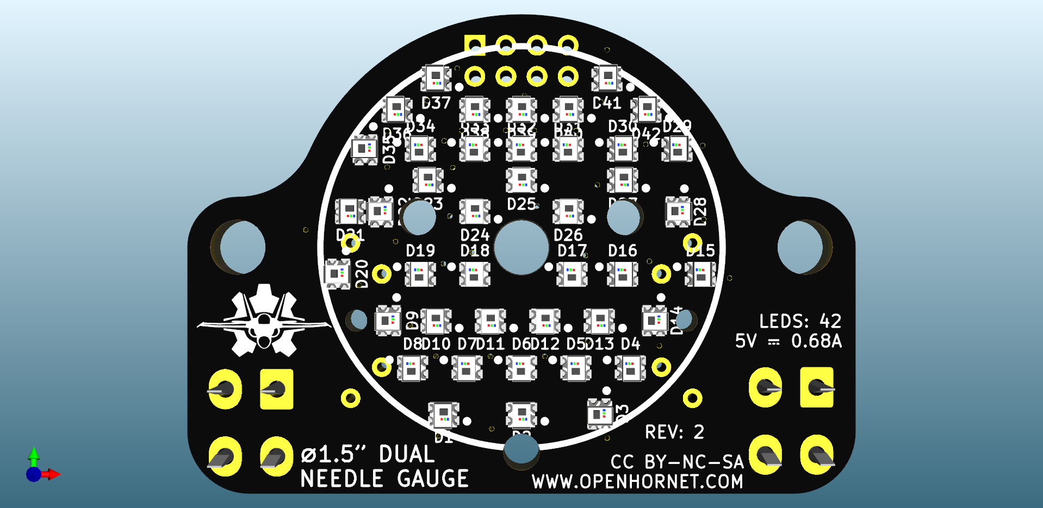
ECAD/PCBs/Functional PCBs/GAUGE_Dual Needle Instruments/Assets/GAUGE_Dual Needle Instruments-TOP.png
