Exprezz0/F-18C_Simulator/ECAD/PCBs/Functional PCBs/GAUGE_Standby Altimeter/Assets/GAUGE_Standby Altimeter-BOT_ISO.png

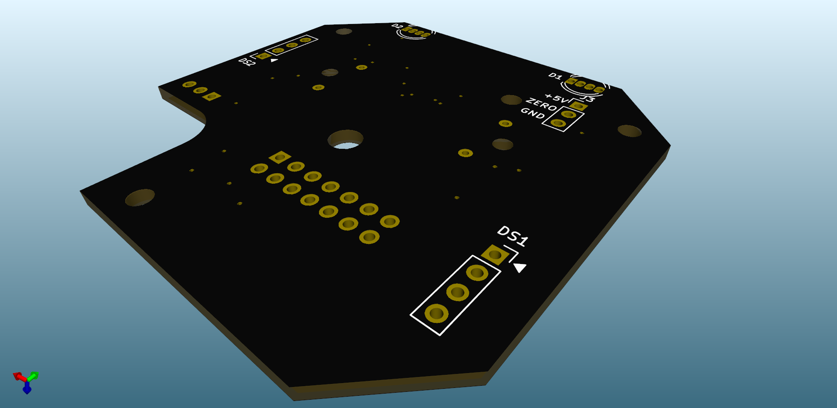
ECAD/PCBs/Functional PCBs/GAUGE_Standby Altimeter/Assets/GAUGE_Standby Altimeter-BOT_ISO.png
