Exprezz0/F-18C_Simulator/ECAD/PCBs/Functional PCBs/IFEI/Assets/IFEI-BOT_ISO.png

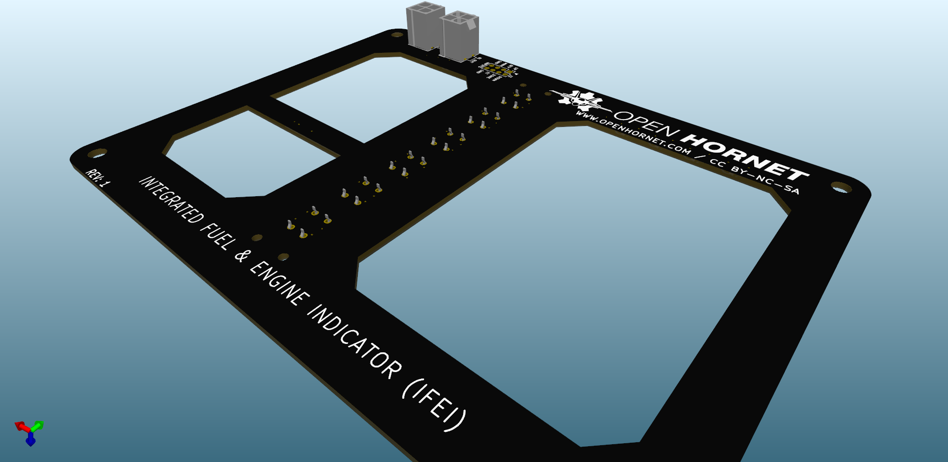
ECAD/PCBs/Functional PCBs/IFEI/Assets/IFEI-BOT_ISO.png
