Exprezz0/F-18C_Simulator/ECAD/PCBs/Functional PCBs/IFEI/Assets/IFEI-TOP.png

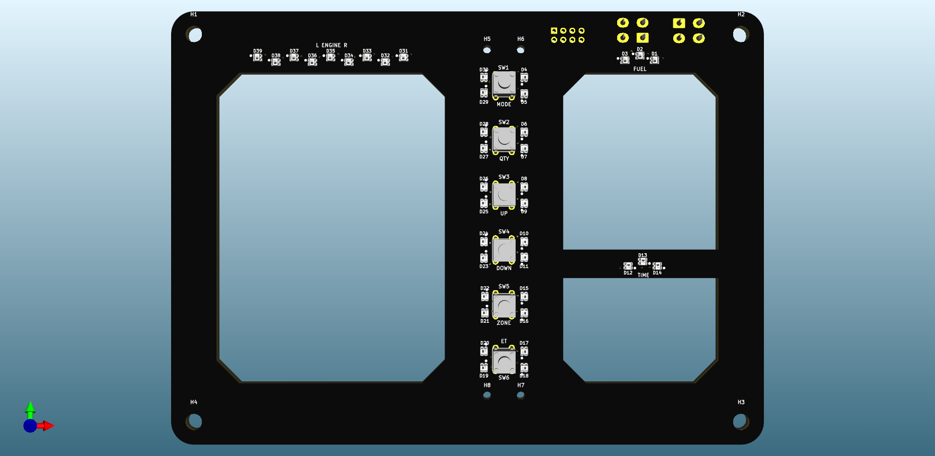
ECAD/PCBs/Functional PCBs/IFEI/Assets/IFEI-TOP.png
