Exprezz0/F-18C_Simulator/ECAD/PCBs/Functional PCBs/RWR CONTROL PANEL/Assets/RWR CONTROL PANEL-TOP.png

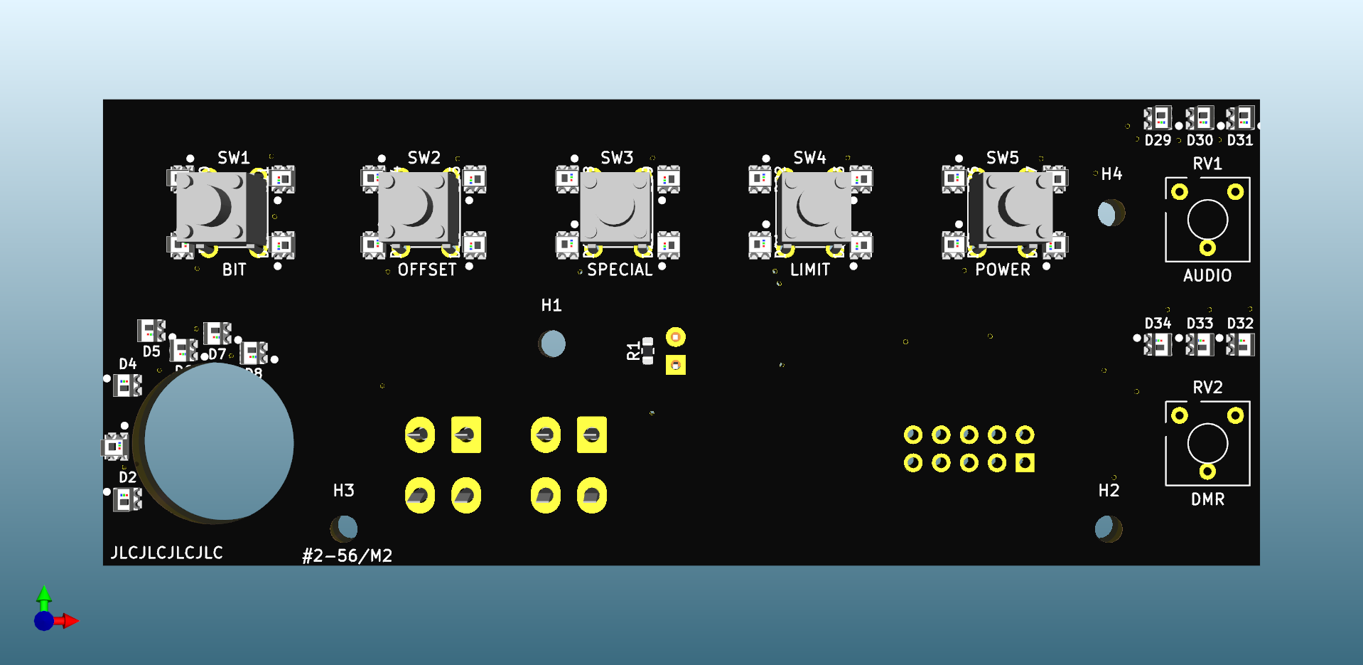
ECAD/PCBs/Functional PCBs/RWR CONTROL PANEL/Assets/RWR CONTROL PANEL-TOP.png
