Exprezz0/F-18C_Simulator/MCAD/ADDITIONAL RESOURCES/Dupont Connector Housing/images/Box_T.png

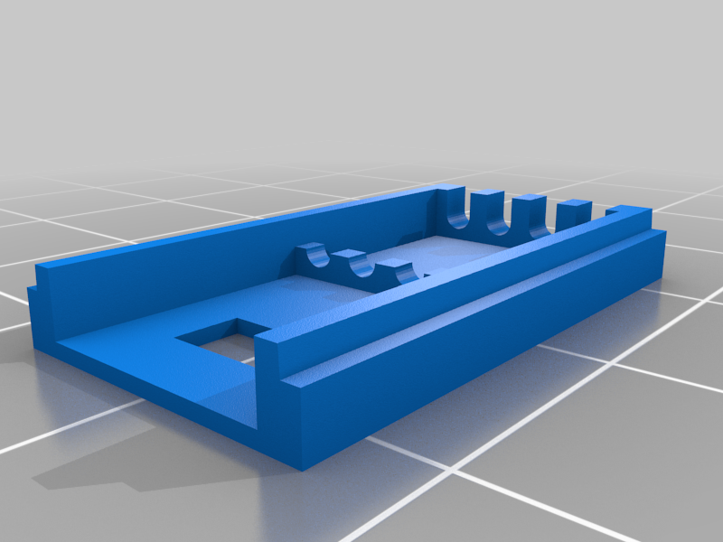
MCAD/ADDITIONAL RESOURCES/Dupont Connector Housing/images/Box_T.png
