Exprezz0/F-18C_Simulator/MCAD/ADDITIONAL RESOURCES/Dupont Connector Housing/images/cover.png

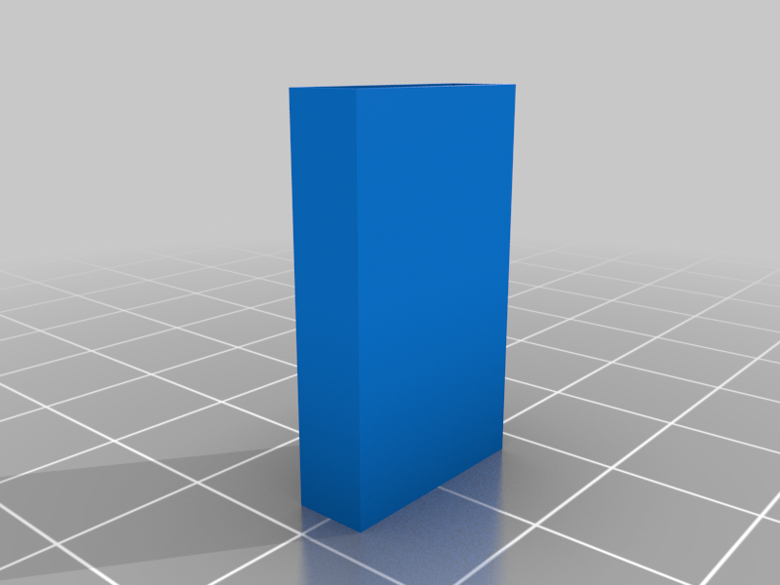
MCAD/ADDITIONAL RESOURCES/Dupont Connector Housing/images/cover.png
