Exprezz0/F-18C_Simulator/MCAD/ADDITIONAL RESOURCES/Dupont Connector Housing/images/d1_Resized.jpg

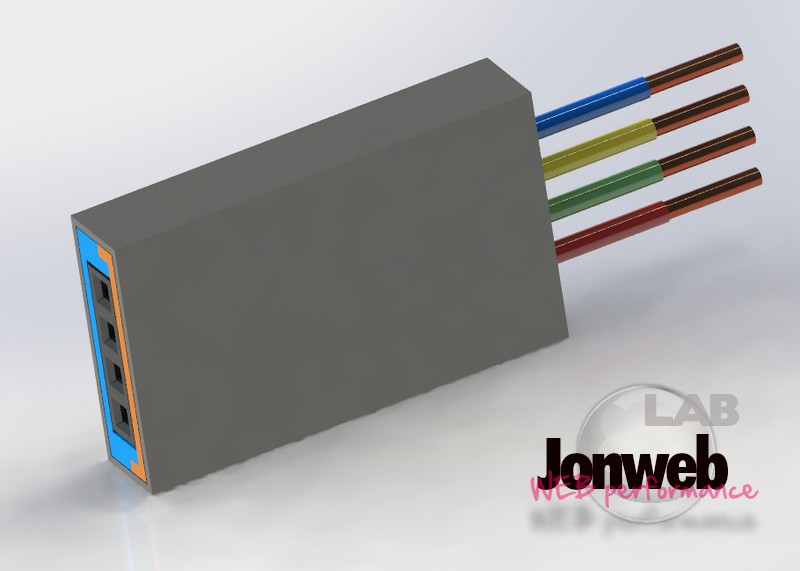
MCAD/ADDITIONAL RESOURCES/Dupont Connector Housing/images/d1_Resized.jpg
