Exprezz0/F-18C_Simulator/MCAD/ADDITIONAL RESOURCES/Dupont Connector Housing/images/d2_Resized.jpg

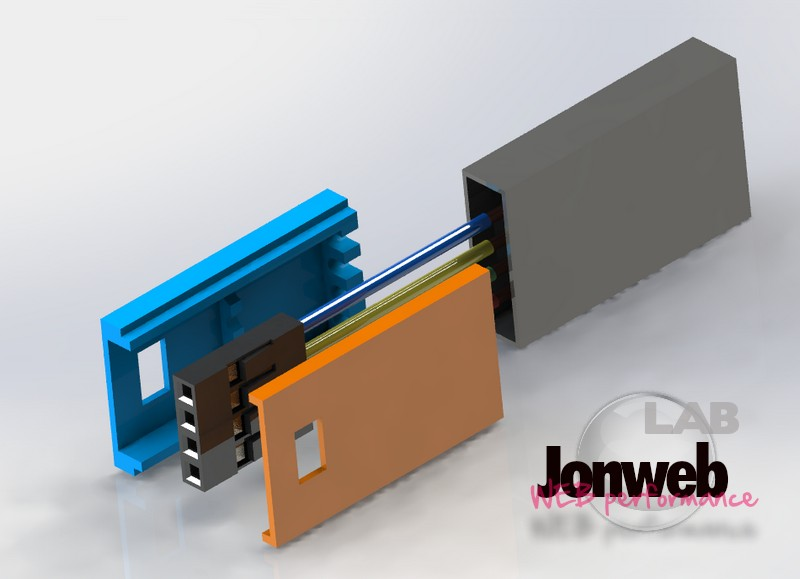
MCAD/ADDITIONAL RESOURCES/Dupont Connector Housing/images/d2_Resized.jpg
