Exprezz0/F-18C_Simulator/MCAD/ADDITIONAL RESOURCES/images/DSC05767.JPG

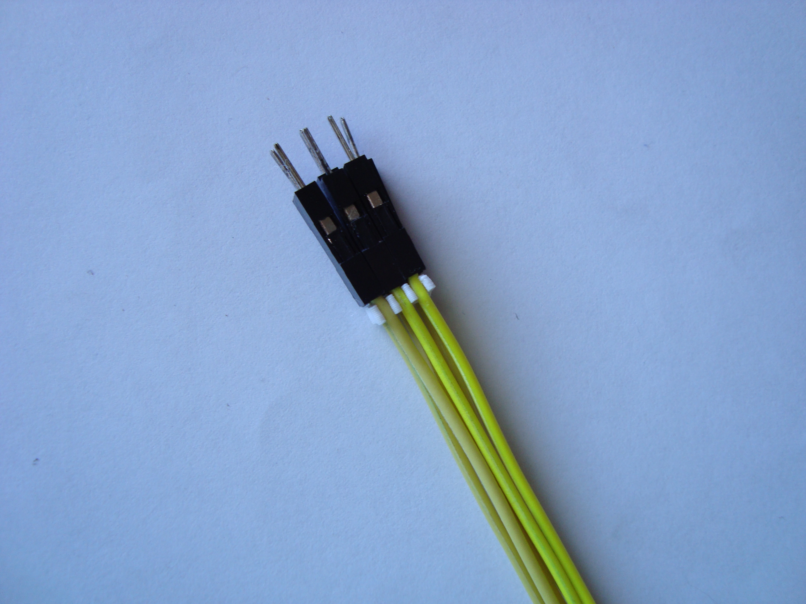
MCAD/ADDITIONAL RESOURCES/images/DSC05767.JPG
