Exprezz0/F-18C_Simulator/MCAD/ADDITIONAL RESOURCES/images/dupon3.jpg

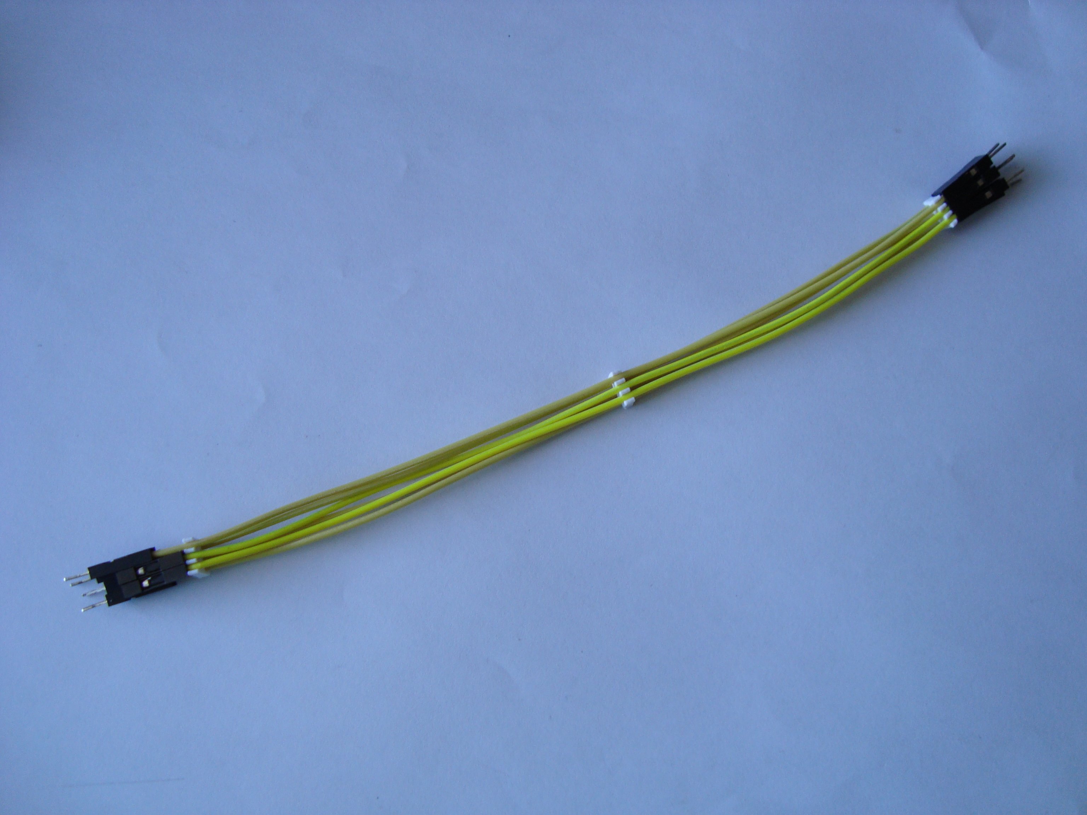
MCAD/ADDITIONAL RESOURCES/images/dupon3.jpg
