Exprezz0/F-18C_Simulator/MCAD/ADDITIONAL RESOURCES/images/dupont_organizer.png

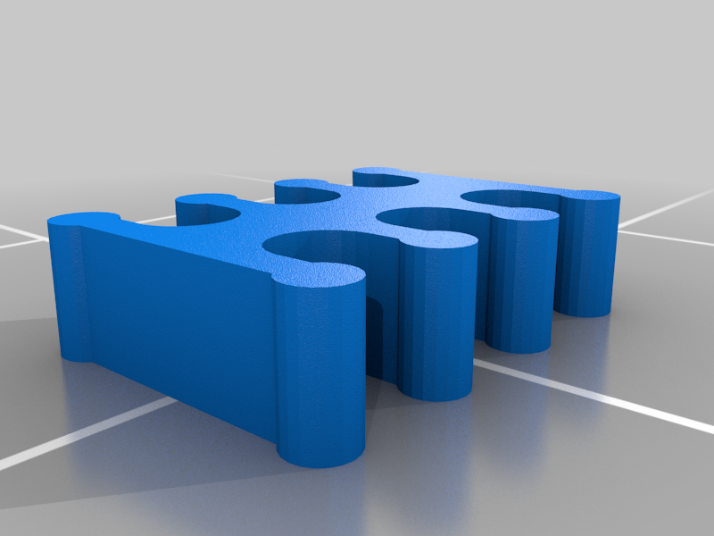
MCAD/ADDITIONAL RESOURCES/images/dupont_organizer.png
