Exprezz0/F-18C_Simulator/ECAD/PCBs/Functional PCBs/AMPCD/JLCPCB/production_files/BOM_BOTTOM-AMPCD.csv

Comment | Designator | Footprint | LCSC
Conn_01x06 | J1 | PinHeader_1x06_P2.54mm_Horizontal
