Exprezz0/F-18C_Simulator/ECAD/PCBs/Functional PCBs/CONTROLLER_Radar Altimeter/JLCPCB/production_files/BOM_BOTTOM-CONTROLLER_Radar Altimeter.csv

Comment | Designator | Footprint | LCSC
BL IN | J3,J4 | Molex_Mini-Fit_Jr_5566-04A_2x02_P4.20mm_Vertical | C293502
BUS IN | J1,J2 | Molex_Mini-Fit_Jr_5566-06A2_2x03_P4.20mm_Vertical | C505177
BL_DOUT | JP2 | PinHeader_1x03_P2.54mm_Vertical
BL_DIN | JP1 | PinHeader_1x03_P2.54mm_Vertical
