Exprezz0/F-18C_Simulator/ECAD/PCBs/Functional PCBs/CONTROLLER_Radar Altimeter/JLCPCB/production_files/BOM_TOP-CONTROLLER_Radar Altimeter.csv

Comment | Designator | Footprint | LCSC
MAX487EESA+T | U1 | SOIC-8_3.9x4.9mm_P1.27mm | C116539
120 | R1,R2 | R_0805_2012Metric | C17437
0.1uF | C1 | C_0805_2012Metric | C49678
ProMicro | U0 | DIP-24_W15.24mm_Socket | C72120
POT | J17 | PinHeader_1x03_P2.54mm_Vertical
PUSH | J16 | PinHeader_1x02_P2.54mm_Vertical
SERVO | J15 | PinHeader_1x03_P2.54mm_Vertical
RED LED | J14 | PinHeader_1x02_P2.54mm_Vertical
GRN LED | J13 | PinHeader_1x02_P2.54mm_Vertical
STEPPER | J5 | PinHeader_2x05_P2.54mm_Vertical
