Exprezz0/F-18C_Simulator/ECAD/PCBs/Functional PCBs/CONTROLLER_Standby Instrument/JLCPCB/production_files/BOM_BOTTOM-CONTROLLER_Standby Instrument.csv

Comment | Designator | Footprint | LCSC
BL IN | J3,J4 | Molex_Mini-Fit_Jr_5566-04A_2x02_P4.20mm_Vertical | C293502
BL_DOUT_SEL | JP2 | PinHeader_1x03_P2.54mm_Vertical
BL_DIN_SEL | JP1 | PinHeader_1x03_P2.54mm_Vertical
Digital | P1 | PinHeader_2x18_P2.54mm_Vertical
PWM | P5 | PinHeader_1x10_P2.54mm_Vertical
Communication | P7 | PinHeader_1x08_P2.54mm_Vertical
Power | P2 | PinHeader_1x08_P2.54mm_Vertical
Analog | P3 | PinHeader_1x08_P2.54mm_Vertical
PWM | P4 | PinHeader_1x08_P2.54mm_Vertical
