Exprezz0/F-18C_Simulator/ECAD/PCBs/Functional PCBs/DDI/JLCPCB/production_files/BOM_BOTTOM-DDI.csv

Comment | Designator | Footprint | LCSC
Conn_01x06 | J1 | Molex_KK-254_AE-6410-06A_1x06_P2.54mm_Vertical | C504992
