Exprezz0/F-18C_Simulator/ECAD/PCBs/Functional PCBs/EYEBROW WARNING INDICATOR_LEFT/JLCPCB/production_files/BOM_BOTTOM-EYEBROW WARNING INDICATOR_LEFT.csv

Comment | Designator | Footprint | LCSC
BL IN | J1,J2 | Molex_Mini-Fit_Jr_5566-04A_2x02_P4.20mm_Vertical | C293502
1000 nF | C1 | CP_Elec_8x10 | C445083
SW | J3 | Molex_KK-254_AE-6410-03A_1x03_P2.54mm_Vertical | C471416
PWR | D1 | LED_D3.0mm
