Exprezz0/F-18C_Simulator/ECAD/PCBs/Functional PCBs/EYEBROW WARNING INDICATOR_LEFT/JLCPCB/production_files/BOM_TOP-EYEBROW WARNING INDICATOR_LEFT.csv

Comment | Designator | Footprint | LCSC
R | R1 | R_0603_1608Metric | C23138
LED | D10,D11,D12,D13,D14,D15,D16,D17,D18,D19,D2,D20,D21,D22,D23,D24,D25,D26,D27,D28,D29,D3,D30,D31,D4,D5,D6,D7,D8,D9 | WS2812-2020 | C965555
MC/APU FIRE | SW2 | SW_TH_Tactile_Omron_B3F-10xx
FIRE | SW1 | SW_TH_Tactile_Omron_B3F-10xx
