Exprezz0/F-18C_Simulator/ECAD/PCBs/Functional PCBs/GAUGE_Analog Instruments/JLCPCB/production_files/BOM_BOTTOM-GAUGE_Analog Instruments.csv

Comment | Designator | Footprint | LCSC
1938 | D2 | LED_D5.0mm-4_RGB
1938 | D1 | LED_D5.0mm-4_RGB
ZERO | J4 | PinHeader_1x03_P2.54mm_Vertical
