Exprezz0/F-18C_Simulator/ECAD/PCBs/Functional PCBs/GAUGE_Dual Needle Instruments/JLCPCB/production_files/BOM_BOTTOM-GAUGE_Dual Needle Instruments.csv

Comment | Designator | Footprint | LCSC
BL IN | J1,J3 | Molex_Mini-Fit_Jr_5566-04A_2x02_P4.20mm_Vertical | C293502
DATA | J2 | PinHeader_2x04_P2.54mm_Vertical
