Exprezz0/F-18C_Simulator/ECAD/PCBs/Functional PCBs/HOTAS_Analog Stick Breakout/JLCPCB/production_files/BOM_BOTTOM-HOTAS_Analog Stick Breakout.csv

Comment | Designator | Footprint | LCSC
ANALOGSTICK_CENTERPUSH | JOY1 | RKJXV12 | C2687349
