Exprezz0/F-18C_Simulator/ECAD/PCBs/Functional PCBs/HOTAS_Analog Stick Breakout/JLCPCB/production_files/BOM_TOP-HOTAS_Analog Stick Breakout.csv

Comment | Designator | Footprint | LCSC
10k | R1 | R_0603_1608Metric | C25804
4.7uF | C1 | C_1206_3216Metric | C29823
