Exprezz0/F-18C_Simulator/ECAD/PCBs/Functional PCBs/HOTAS_Hat Switch Breakout/JLCPCB/production_files/BOM_BOTTOM-HOTAS_Hat Switch Breakout.csv

Comment | Designator | Footprint | LCSC
8WayHat_CenterPush | S1 | RKJXM10 | C97432
