Exprezz0/F-18C_Simulator/ECAD/PCBs/Functional PCBs/IFEI/JLCPCB/production_files/BOM_BOTTOM-IFEI.csv

Comment | Designator | Footprint | LCSC
BL IN | J1,J2 | Molex_Mini-Fit_Jr_5566-04A_2x02_P4.20mm_Vertical | C293502
INPUTS | J3 | PinHeader_2x04_P2.54mm_Vertical
