Exprezz0/F-18C_Simulator/ECAD/PCBs/Functional PCBs/JETT STATION SELECT/JLCPCB/production_files/BOM_BOTTOM-JETT STATION SELECT.csv

Comment | Designator | Footprint | LCSC
BL IN | J1,J2 | Molex_Mini-Fit_Jr_5566-04A_2x02_P4.20mm_Vertical | C293502
1000 nF | C1 | CP_Elec_8x10 | C445083
INPUTS | J3 | PinHeader_2x03_P2.54mm_Vertical
READY | D1 | LED_D3.0mm
