Exprezz0/F-18C_Simulator/ECAD/PCBs/Functional PCBs/RWR CONTROL PANEL/JLCPCB/production_files/BOM_BOTTOM-RWR CONTROL PANEL.csv

Comment | Designator | Footprint | LCSC
BL IN | J1,J2 | Molex_Mini-Fit_Jr_5566-04A_2x02_P4.20mm_Vertical | C293502
1000 nF | C1 | CP_Elec_8x10 | C445083
READY | D1 | LED_D3.0mm
INPUTS | J3 | PinHeader_2x05_P2.54mm_Vertical
