Exprezz0/F-18C_Simulator/ECAD/PCBs/ABSIS/ABSIS_ALE Relay Module/JLCPCB/production_files/BOM_BOTTOM-ABSIS_ALE Relay Module.csv

Comment | Designator | Footprint | LCSC
CH1 OUT | J3,J4 | JST_PH_B2B-PH-K_1x02_P2.00mm_Vertical | C131337
IRFB3206PBF | Q1,Q4 | TO-220-3_Vertical | C2642
CH1 PWR SEL | JP1 | PinHeader_1x03_P2.54mm_Vertical
CH1 SEL A | JP2 | PinHeader_1x03_P2.54mm_Vertical
CH2 SEL A | JP5 | PinHeader_1x03_P2.54mm_Vertical
CH2 PWR SEL | JP4 | PinHeader_1x03_P2.54mm_Vertical
