Exprezz0/F-18C_Simulator/ECAD/PCBs/ABSIS/ABSIS_ALE/JLCPCB/production_files/BOM_BOTTOM-ABSIS_ALE.csv

Comment | Designator | Footprint | LCSC
I/O #1 | J3,J4 | PinHeader_2x06_P2.54mm_Vertical | C124388
GND | J5 | PinHeader_1x06_P2.54mm_Vertical | C37208
ACC PWR | J6 | PinHeader_2x02_P2.54mm_Vertical | C66690
