Exprezz0/F-18C_Simulator/ECAD/PCBs/ABSIS/ABSIS_ALE/JLCPCB/production_files/BOM_TOP-ABSIS_ALE.csv

Comment | Designator | Footprint | LCSC
MAX487EESA+T | U1 | SOIC-8_3.9x4.9mm_P1.27mm | C116539
0.1uF | C1 | C_0805_2012Metric | C49678
BUS IN | J1,J2 | Molex_Mini-Fit_Jr_5566-06A2_2x03_P4.20mm_Vertical | C505177
ProMicro_5V/16Hz | XU1 | DIP-24_W15.24mm_Socket | C72120
RST | RST1 | SolderJumper-2_P1.3mm_Open_RoundedPad1.0x1.5mm
