Exprezz0/F-18C_Simulator/ECAD/PCBs/ABSIS/ABSIS_Backlight Controller/JLCPCB/production_files/BOM_BOTTOM-ABSIS_Backlight Controller.csv

Comment | Designator | Footprint | LCSC
Digital | P1 | PinHeader_2x18_P2.54mm_Vertical
Power | P2 | PinHeader_1x08_P2.54mm_Vertical
Analog | P3 | PinHeader_1x08_P2.54mm_Vertical
Analog | P4 | PinHeader_1x08_P2.54mm_Vertical
PWM | P5 | PinHeader_1x10_P2.54mm_Vertical
PWM | P6 | PinHeader_1x08_P2.54mm_Vertical
Communication | P7 | PinHeader_1x08_P2.54mm_Vertical
