Exprezz0/F-18C_Simulator/ECAD/PCBs/ABSIS/ABSIS_Hall Sensor/JLCPCB/production_files/BOM_BOTTOM-ABSIS_Hall Sensor.csv

Comment | Designator | Footprint | LCSC
IN | J1 | JST_PH_S6B-PH-K_1x06_P2.00mm_Horizontal | C265105
