Exprezz0/F-18C_Simulator/ECAD/PCBs/Backlight PCBs/Backlighting_Type B/ECS PANEL/Manufacturing/ECS Panel PCB V2 BOM.xlsx

Comment | Designator | Footprint | LCSC Part #
LED | D2-64 | LED-4_5050 | C114586
Resistor 470 ohm | R1 | 0603 | C23179
Capacitor | C2-62 | 0603 | C14663
