Exprezz0/F-18C_Simulator/ECAD/PCBs/OH_Specific/Backlighting_Type A/PCB, LEFT CIRCUIT BREAKER/Manufacturing/Left Circuit Breaker PCB V1 BOM.xlsx

Comment | Designator | Footprint | LCSC Part #
LED | D1-14 | LED-4_5050 | C114586
Capacitor | C2-7 | 0603 | C14663
