Exprezz0/F-18C_Simulator/ECAD/PCBs/Backlight PCBs/Backlighting_Type A/APU PANEL/JLCPCB/production_files/BOM_BOTTOM-APU PANEL.csv

Comment | Designator | Footprint | LCSC
Conn_01x04_Female | J1,J2 | Molex_Mini-Fit_Jr_5566-04A_2x02_P4.20mm_Vertical | C293502
C_Polarized | C1 | CP_Elec_8x10 | C445083
LED | D21 | LED_D3.0mm
