Exprezz0/F-18C_Simulator/ECAD/PCBs/Backlight PCBs/Backlighting_Type A/LEFT CIRCUIT BREAKER/JLCPCB/production_files/BOM_TOP-LEFT CIRCUIT BREAKER.csv

Comment | Designator | Footprint | LCSC
C | C10,C11,C12,C13,C14,C15,C2,C3,C4,C5,C6,C7,C8,C9 | C_0603_1608Metric | C14663
WS2812B | D1,D10,D11,D12,D13,D14,D2,D3,D4,D5,D6,D7,D8,D9 | LED_WS2812B_PLCC4_5.0x5.0mm_P3.2mm | C2761795
