Exprezz0/F-18C_Simulator/ECAD/PCBs/Functional PCBs/CONTROLLER_Stick/JLCPCB/production_files/BOM_TOP-CONTROLLER_Stick.csv

Comment | Designator | Footprint | LCSC
TM GRIP | J4 | JST_PH_S5B-PH-K_1x05_P2.00mm_Horizontal | C157923
33 | R2 | R_0402_1005Metric | C25105
10k | R1 | R_0603_1608Metric | C25804
IRLML6402TRPBF | Q1,Q2 | SOT-23 | C2593
X/ROLL | J1,J2,J3 | JST_PH_S6B-PH-K_1x06_P2.00mm_Horizontal | C265105
RESET | SW1 | SMD-SW-4_5.1x5.1 | C318884
ProMicro | U1 | DIP-24_W15.24mm_Socket | C72120
2N7002 | Q3 | SOT-23 | C8545
AUX I/O | J5 | PinHeader_2x07_P2.54mm_Vertical
