Exprezz0/F-18C_Simulator/ECAD/PCBs/Backlight PCBs/Backlighting_Type A/ECM DISP PANEL/MCAD/ECM DISP PANEL.step

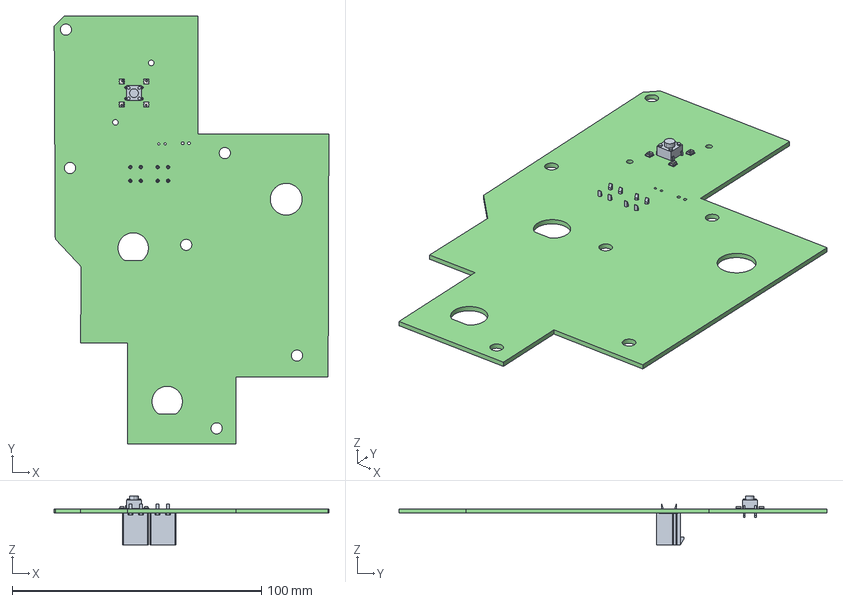
[picture p198: CAD file, 2023-01-10]
ECAD/PCBs/Backlight PCBs/Backlighting_Type A/ECM DISP PANEL/MCAD/ECM DISP PANEL.step
110.3 x 171.8 x 19.5 mm
ECM DISP PANEL PCB
