Exprezz0/F-18C_Simulator/ECAD/PCBs/Backlight PCBs/Backlighting_Type A/EXT LT PANEL/MCAD/EXT LT PANEL.step

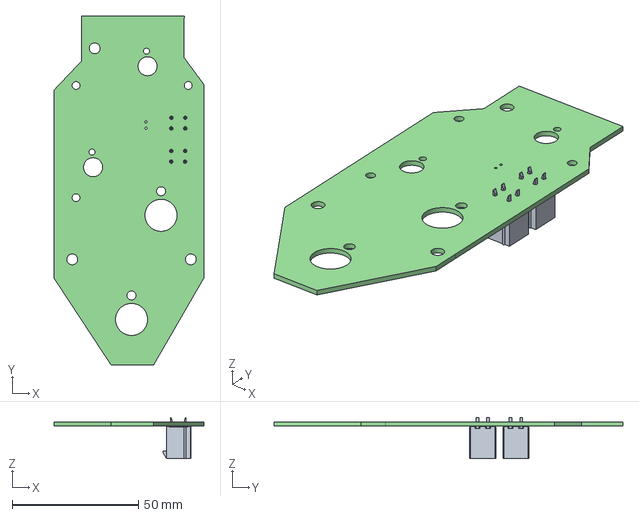
[picture p199: CAD file, 2023-01-10]
ECAD/PCBs/Backlight PCBs/Backlighting_Type A/EXT LT PANEL/MCAD/EXT LT PANEL.step
59.4 x 138.3 x 16.3 mm
EXT LT PANEL PCB
