Exprezz0/F-18C_Simulator/ECAD/PCBs/Backlight PCBs/Backlighting_Type A/FCS PANEL/MCAD/FCS PANEL.step

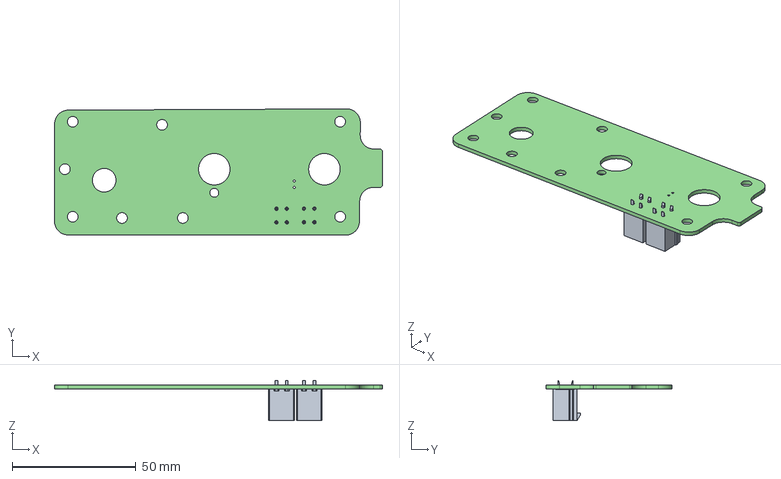
[picture p200: CAD file, 2023-01-10]
ECAD/PCBs/Backlight PCBs/Backlighting_Type A/FCS PANEL/MCAD/FCS PANEL.step
132.4 x 51.0 x 16.3 mm
FCS PANEL PCB
