Exprezz0/F-18C_Simulator/ECAD/PCBs/Backlight PCBs/Backlighting_Type A/HUD PANEL/MCAD/HUD PANEL.step

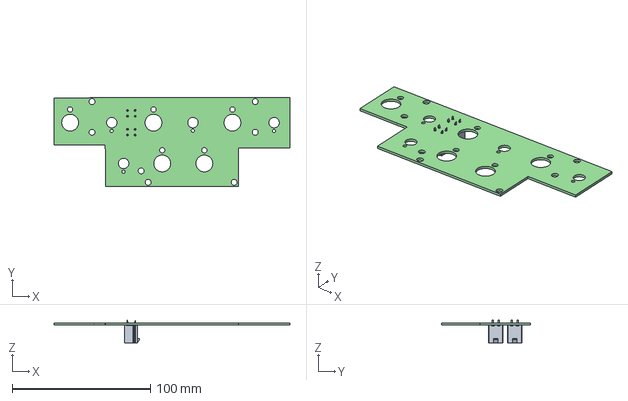
[picture p201: CAD file, 2023-01-10]
ECAD/PCBs/Backlight PCBs/Backlighting_Type A/HUD PANEL/MCAD/HUD PANEL.step
170.8 x 64.5 x 16.3 mm
HUD PANEL PCB
