Exprezz0/F-18C_Simulator/ECAD/PCBs/Backlight PCBs/Backlighting_Type A/JETT STATION SELECT PLACARD/MCAD/JETT STATION SELECT PLACARD.step

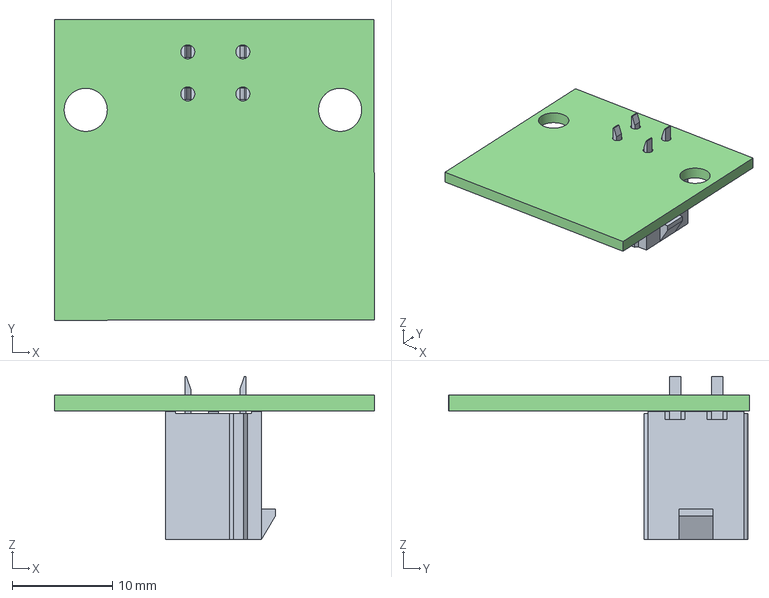
[picture p202: CAD file, 2023-01-10]
ECAD/PCBs/Backlight PCBs/Backlighting_Type A/JETT STATION SELECT PLACARD/MCAD/JETT STATION SELECT PLACARD.step
32.0 x 30.0 x 16.3 mm
JETT STATION SELECT PLACARD PCB
