Exprezz0/F-18C_Simulator/ECAD/PCBs/Backlight PCBs/Backlighting_Type A/KY-58 PANEL/MCAD/KY-58 PANEL.step

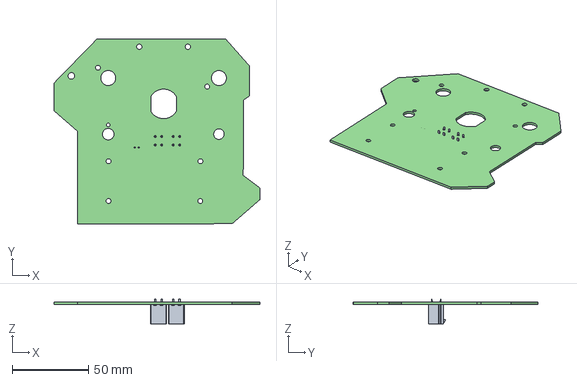
[picture p203: CAD file, 2023-01-10]
ECAD/PCBs/Backlight PCBs/Backlighting_Type A/KY-58 PANEL/MCAD/KY-58 PANEL.step
134.7 x 120.8 x 16.3 mm
KY-58 PANEL PCB
