Exprezz0/F-18C_Simulator/ECAD/PCBs/Backlight PCBs/Backlighting_Type A/LANDING GEAR PANEL/MCAD/LANDING GEAR PANEL.step

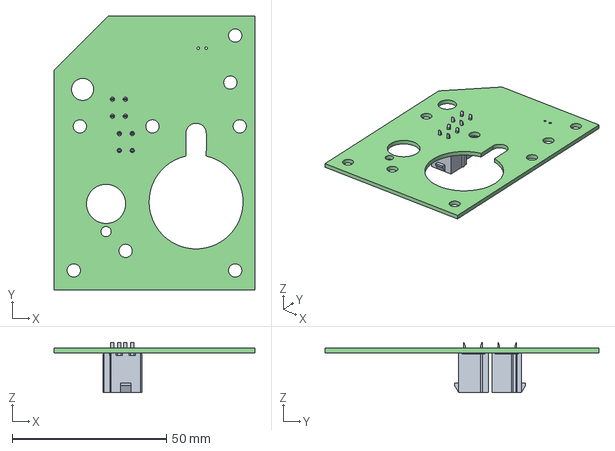
[picture p204: CAD file, 2023-01-10]
ECAD/PCBs/Backlight PCBs/Backlighting_Type A/LANDING GEAR PANEL/MCAD/LANDING GEAR PANEL.step
65.1 x 88.9 x 16.3 mm
_autosave-LANDING GEAR PANEL PCB
