Exprezz0/F-18C_Simulator/ECAD/PCBs/Backlight PCBs/Backlighting_Type A/LEFT CIRCUIT BREAKER/MCAD/LEFT CIRCUIT BREAKER.step

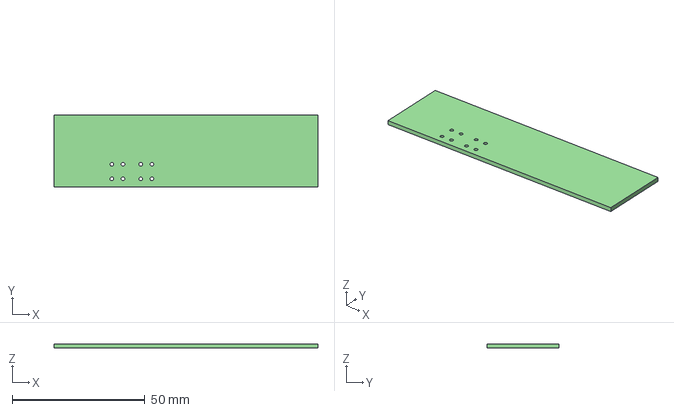
[picture p205: CAD file, 2023-01-10]
ECAD/PCBs/Backlight PCBs/Backlighting_Type A/LEFT CIRCUIT BREAKER/MCAD/LEFT CIRCUIT BREAKER.step
99.5 x 27.0 x 1.60 mm
