Exprezz0/F-18C_Simulator/ECAD/PCBs/Backlight PCBs/Backlighting_Type A/MASTER ARM PANEL/MCAD/MASTER ARM PANEL.step

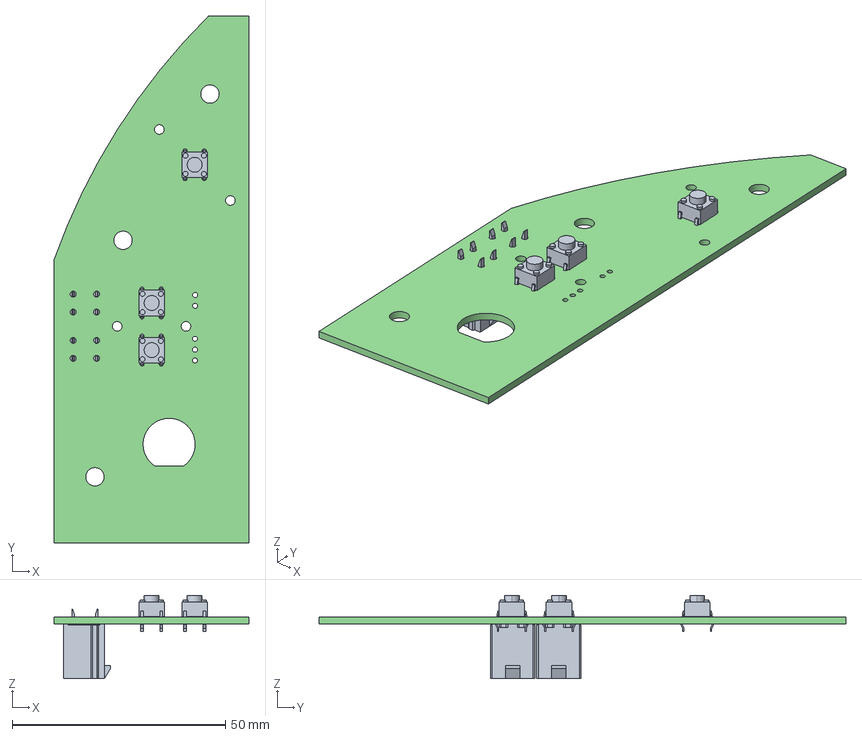
[picture p206: CAD file, 2023-01-10]
ECAD/PCBs/Backlight PCBs/Backlighting_Type A/MASTER ARM PANEL/MCAD/MASTER ARM PANEL.step
45.7 x 123.5 x 19.5 mm
MASTER ARM PANEL PCB
