Exprezz0/F-18C_Simulator/ECAD/PCBs/Backlight PCBs/Backlighting_Type A/SIM CONTROL PANEL/MCAD/SIM CONTROL PANEL.step

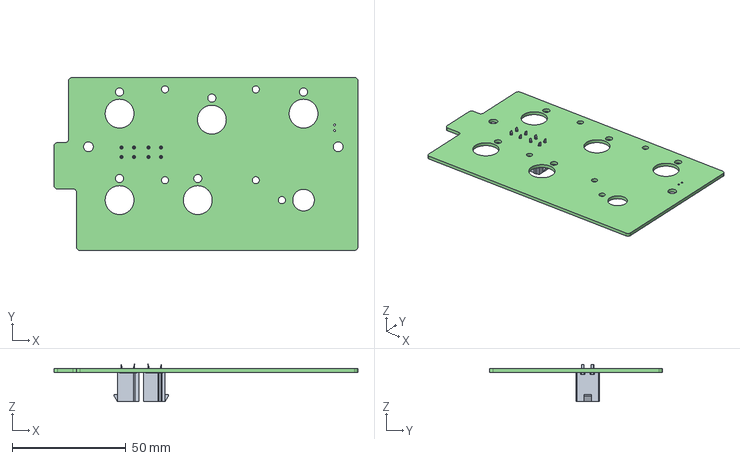
[picture p207: CAD file, 2023-01-10]
ECAD/PCBs/Backlight PCBs/Backlighting_Type A/SIM CONTROL PANEL/MCAD/SIM CONTROL PANEL.step
133.9 x 76.2 x 16.3 mm
SIM CONTROL PANEL PCB
