Exprezz0/F-18C_Simulator/ECAD/PCBs/Backlight PCBs/Backlighting_Type A/SIM POWER PANEL/MCAD/SIM POWER PANEL.step

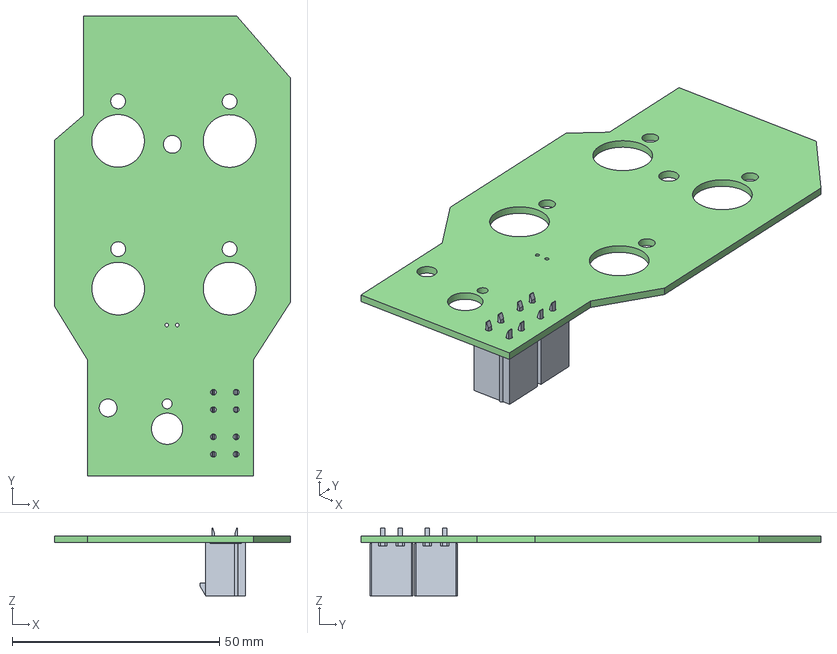
[picture p208: CAD file, 2023-01-10]
ECAD/PCBs/Backlight PCBs/Backlighting_Type A/SIM POWER PANEL/MCAD/SIM POWER PANEL.step
57.0 x 111.0 x 16.3 mm
SIM POWER PANEL PCB
