Exprezz0/F-18C_Simulator/ECAD/PCBs/Backlight PCBs/Backlighting_Type A/SNSR PANEL/MCAD/SNSR PANEL.step

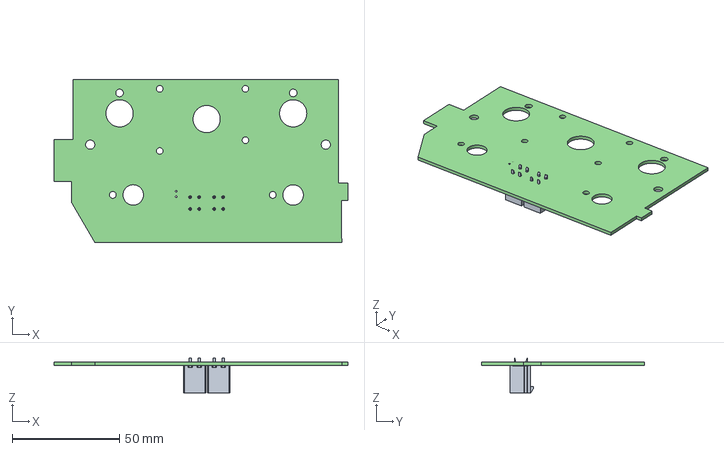
[picture p209: CAD file, 2023-01-10]
ECAD/PCBs/Backlight PCBs/Backlighting_Type A/SNSR PANEL/MCAD/SNSR PANEL.step
137.2 x 76.2 x 16.3 mm
SNSR PANEL PCB
