Exprezz0/F-18C_Simulator/ECAD/PCBs/Backlight PCBs/Backlighting_Type A/SPIN RCV PANEL/MCAD/SPIN RCV PANEL.step

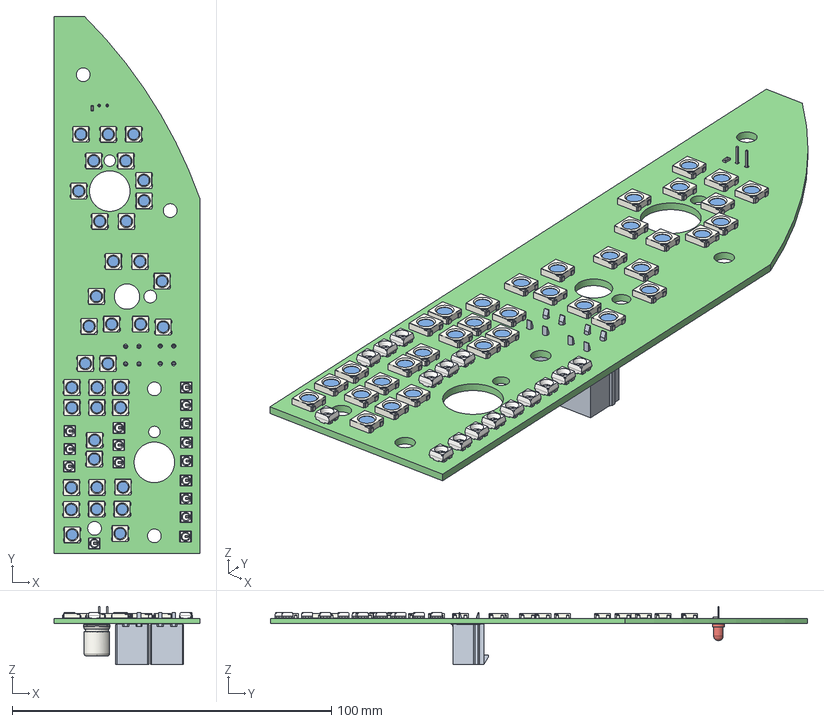
[picture p210: CAD file, 2023-04-01]
ECAD/PCBs/Backlight PCBs/Backlighting_Type A/SPIN RCV PANEL/MCAD/SPIN RCV PANEL.step
45.7 x 168.3 x 18.3 mm
SPIN RCV PANEL PCB
