Exprezz0/F-18C_Simulator/ECAD/PCBs/Backlight PCBs/Backlighting_Type B/ECS PANEL/Assets/ECS Panel Legend Plate.DXF

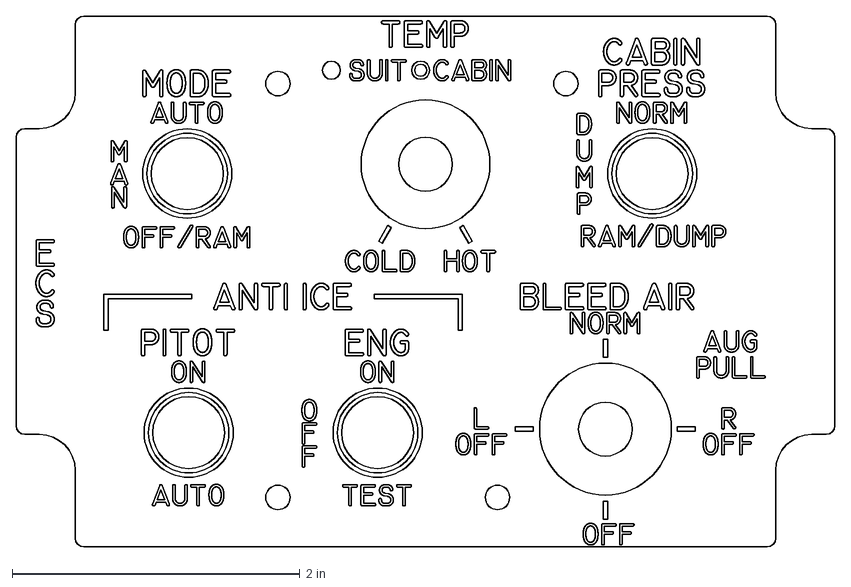
[picture p211: CAD file, 2023-01-02]
ECAD/PCBs/Backlight PCBs/Backlighting_Type B/ECS PANEL/Assets/ECS Panel Legend Plate.DXF
5.69 x 3.69 in
