Exprezz0/F-18C_Simulator/ECAD/PCBs/Functional PCBs/AMPCD/MCAD/AMPCD.step

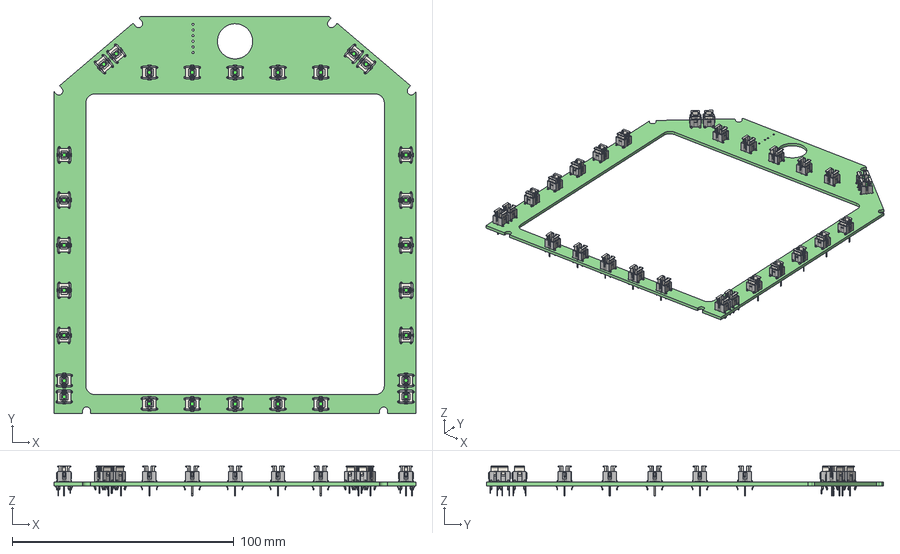
[picture p212: CAD file, 2023-02-10]
ECAD/PCBs/Functional PCBs/AMPCD/MCAD/AMPCD.step
162.9 x 178.9 x 13.4 mm
AMPCD PCB
