Exprezz0/F-18C_Simulator/ECAD/PCBs/Functional PCBs/CONTROLLER_AMPCD DDI/MCAD/CONTROLLER_AMPCD DDI.step

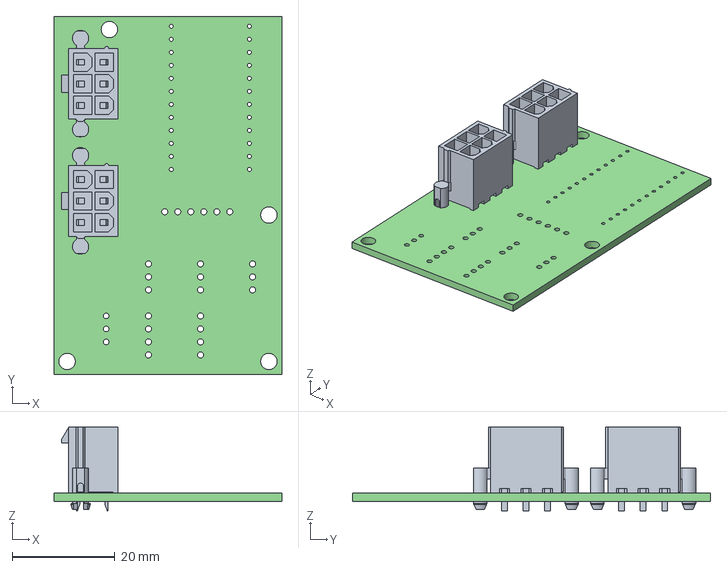
[picture p213: CAD file, 2023-02-10]
ECAD/PCBs/Functional PCBs/CONTROLLER_AMPCD DDI/MCAD/CONTROLLER_AMPCD DDI.step
44.5 x 69.8 x 16.3 mm
CONTROLLER, AMPCD_DDI PCB
