Exprezz0/F-18C_Simulator/ECAD/PCBs/Functional PCBs/CONTROLLER_Radar Altimeter/MCAD/CONTROLLER_Radar Altimeter.step

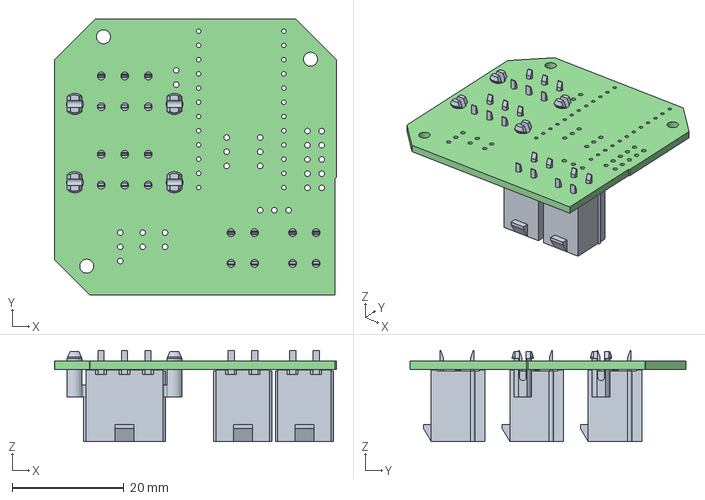
[picture p214: CAD file, 2023-02-10]
ECAD/PCBs/Functional PCBs/CONTROLLER_Radar Altimeter/MCAD/CONTROLLER_Radar Altimeter.step
50.4 x 49.4 x 16.3 mm
CONTROLLER_Radar Altimeter PCB
