Exprezz0/F-18C_Simulator/ECAD/PCBs/Functional PCBs/CONTROLLER_Standby Instrument/MCAD/CONTROLLER_Standby Instrument.step

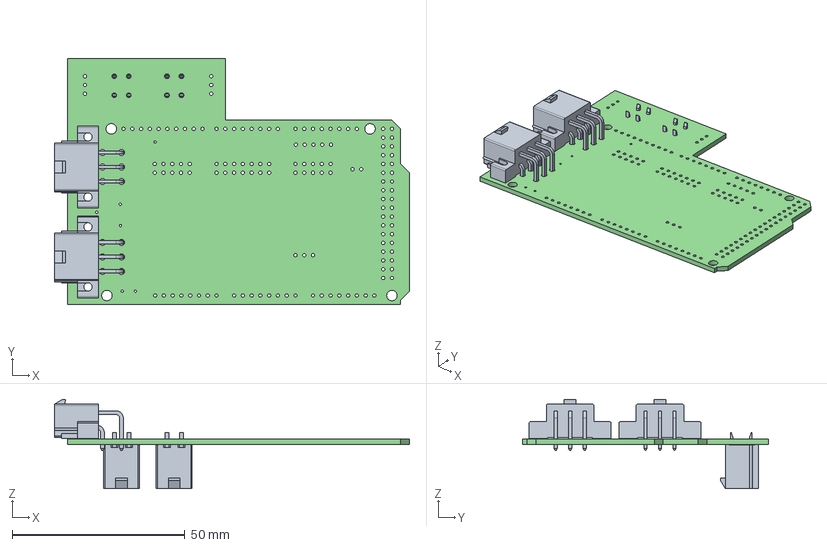
[picture p215: CAD file, 2023-02-10]
ECAD/PCBs/Functional PCBs/CONTROLLER_Standby Instrument/MCAD/CONTROLLER_Standby Instrument.step
102.8 x 71.1 x 25.9 mm
CONTROLLER_Standby Instrument PCB
