Exprezz0/F-18C_Simulator/ECAD/PCBs/Functional PCBs/CONTROLLER_Stick/MCAD/CONTROLLER_Stick.step

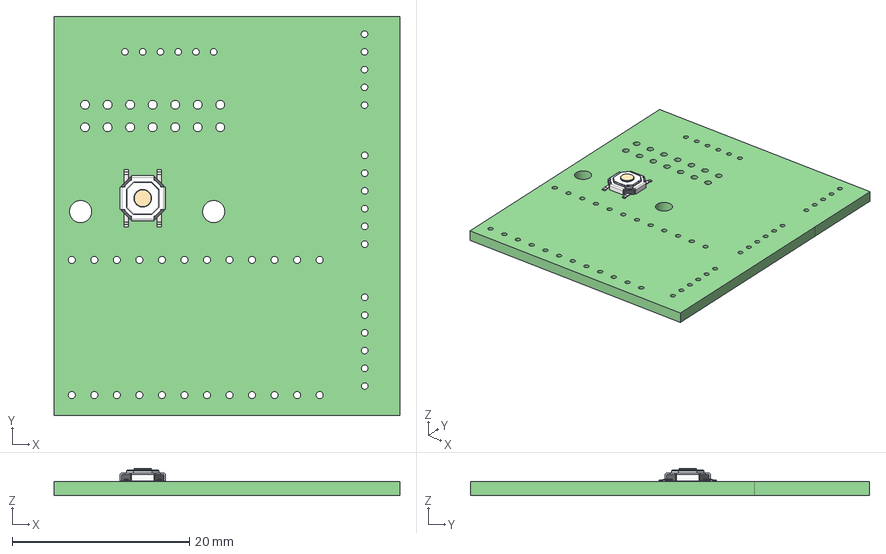
[picture p216: CAD file, 2023-02-10]
ECAD/PCBs/Functional PCBs/CONTROLLER_Stick/MCAD/CONTROLLER_Stick.step
39.0 x 45.0 x 3.05 mm
CONTROLLER_Stick PCB
