Exprezz0/F-18C_Simulator/ECAD/PCBs/Functional PCBs/CONTROLLER_Throttle/MCAD/CONTROLLER_Throttle.step

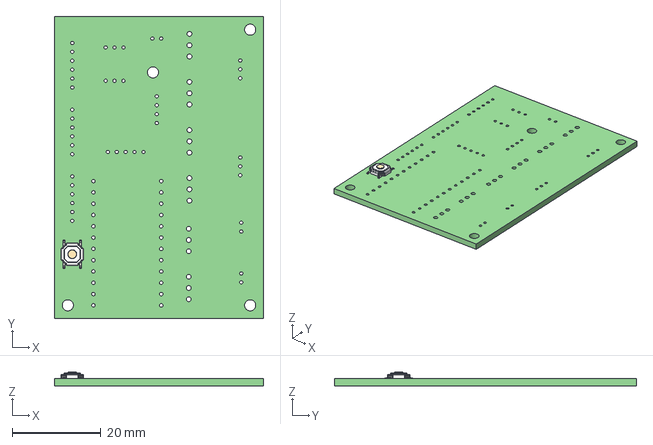
[picture p217: CAD file, 2023-02-10]
ECAD/PCBs/Functional PCBs/CONTROLLER_Throttle/MCAD/CONTROLLER_Throttle.step
47.0 x 68.0 x 3.05 mm
CONTROLLER_Throttle PCB
