Exprezz0/F-18C_Simulator/ECAD/PCBs/Functional PCBs/DDI/MCAD/DDI.step

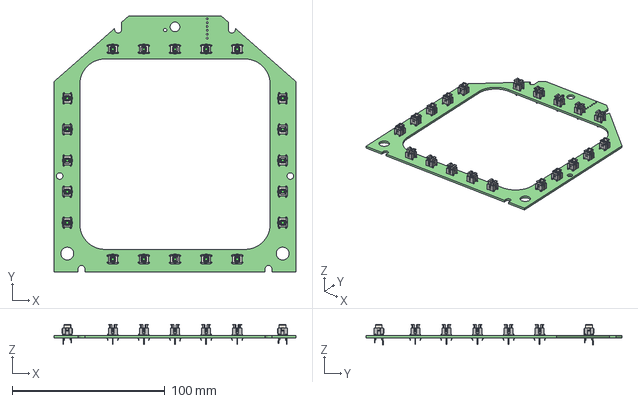
[picture p218: CAD file, 2023-02-10]
ECAD/PCBs/Functional PCBs/DDI/MCAD/DDI.step
158.2 x 167.4 x 13.4 mm
DDI PCB
