Exprezz0/F-18C_Simulator/ECAD/PCBs/Functional PCBs/ddi_button_board/docs/DDI_PCB.DXF

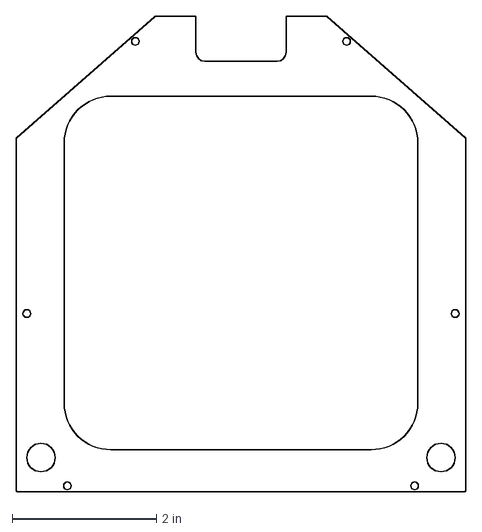
[picture p219: CAD file, 2023-01-02]
ECAD/PCBs/Functional PCBs/ddi_button_board/docs/DDI_PCB.DXF
6.23 x 6.59 in
