Exprezz0/F-18C_Simulator/ECAD/PCBs/Functional PCBs/dual_needle_gauge/dual_needle_gauge.step

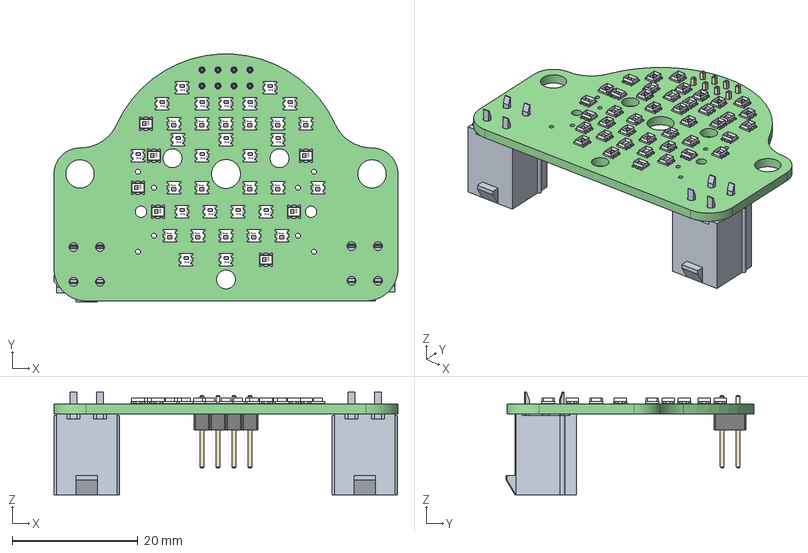
[picture p220: CAD file, 2023-01-02]
ECAD/PCBs/Functional PCBs/dual_needle_gauge/dual_needle_gauge.step
54.6 x 39.3 x 16.3 mm
_autosave-dual_needle_gauge PCB
