Exprezz0/F-18C_Simulator/ECAD/PCBs/Functional PCBs/dual_needle_gauge/ref/dual needle gauge.DXF

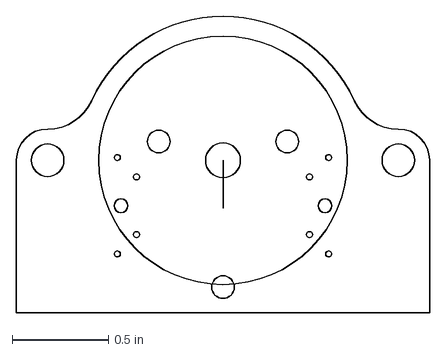
[picture p221: CAD file, 2023-01-02]
ECAD/PCBs/Functional PCBs/dual_needle_gauge/ref/dual needle gauge.DXF
2.15 x 1.54 in
