Exprezz0/F-18C_Simulator/ECAD/PCBs/Functional PCBs/ewi_v3/mcad/ewi_v3_right.step

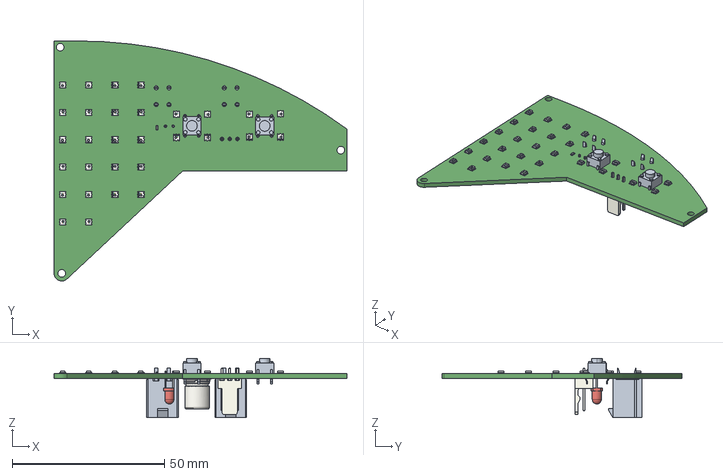
[picture p222: CAD file, 2023-01-02]
ECAD/PCBs/Functional PCBs/ewi_v3/mcad/ewi_v3_right.step
96.1 x 78.8 x 19.5 mm
