Exprezz0/F-18C_Simulator/ECAD/PCBs/Functional PCBs/ewi_v3/ref/EWI PCB - Left.DXF

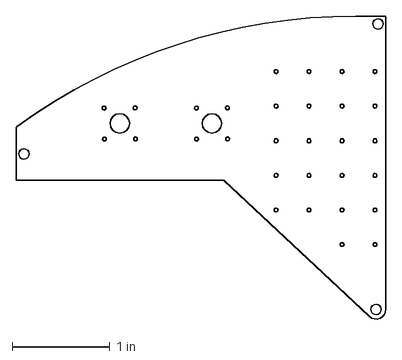
[picture p223: CAD file, 2023-01-02]
ECAD/PCBs/Functional PCBs/ewi_v3/ref/EWI PCB - Left.DXF
3.79 x 3.11 in
