Exprezz0/F-18C_Simulator/ECAD/PCBs/Functional PCBs/EYEBROW WARNING INDICATOR_LEFT/MCAD/EYEBROW WARNING INDICATOR_LEFT.step

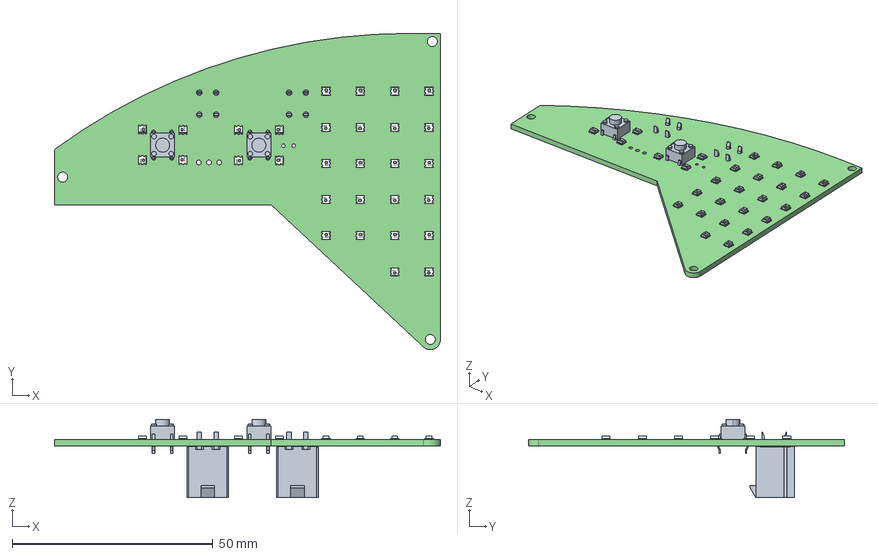
[picture p224: CAD file, 2023-02-10]
ECAD/PCBs/Functional PCBs/EYEBROW WARNING INDICATOR_LEFT/MCAD/EYEBROW WARNING INDICATOR_LEFT.step
96.1 x 78.8 x 19.5 mm
EYEBROW WARNING INDICATOR_LEFT PCB
