Exprezz0/F-18C_Simulator/ECAD/PCBs/Functional PCBs/GAUGE_Analog Instruments/MCAD/GAUGE_Analog Instruments.step

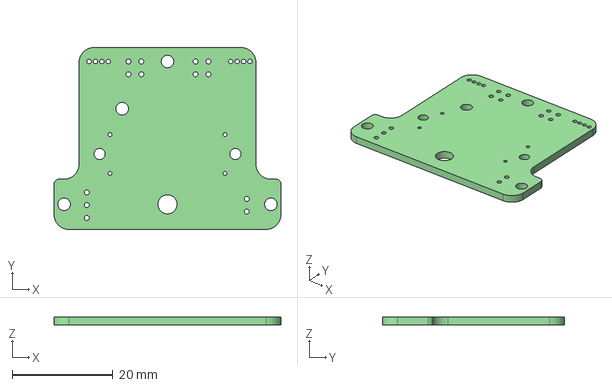
[picture p225: CAD file, 2023-02-10]
ECAD/PCBs/Functional PCBs/GAUGE_Analog Instruments/MCAD/GAUGE_Analog Instruments.step
45.1 x 36.2 x 1.60 mm
