Exprezz0/F-18C_Simulator/ECAD/PCBs/Functional PCBs/GAUGE_Dual Needle Instruments/MCAD/GAUGE_Dual Needle Instruments.step

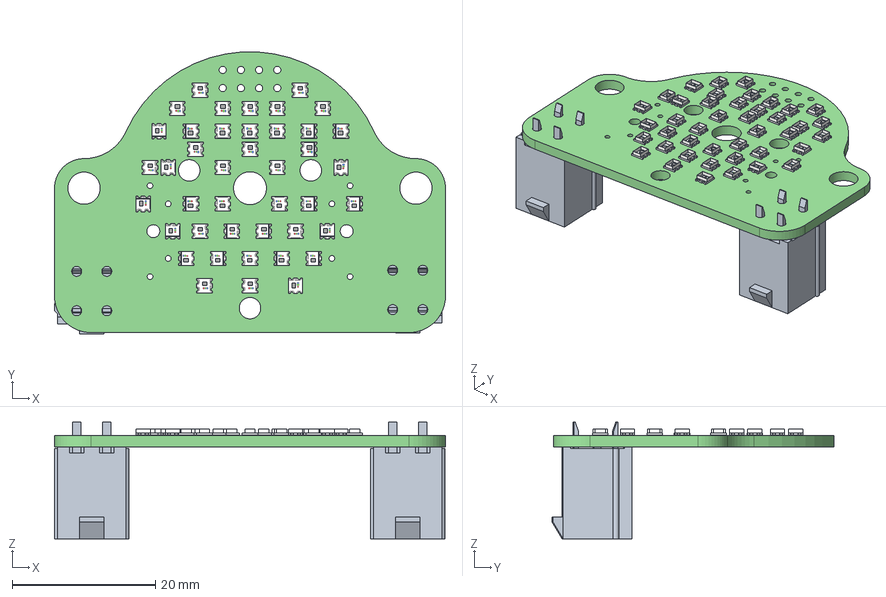
[picture p226: CAD file, 2023-02-10]
ECAD/PCBs/Functional PCBs/GAUGE_Dual Needle Instruments/MCAD/GAUGE_Dual Needle Instruments.step
54.6 x 39.4 x 16.3 mm
_autosave-GAUGE_Dual Needle Instruments PCB
