Exprezz0/F-18C_Simulator/ECAD/PCBs/Functional PCBs/GAUGE_Standby Altimeter/MCAD/GAUGE_Standby Altimeter.step

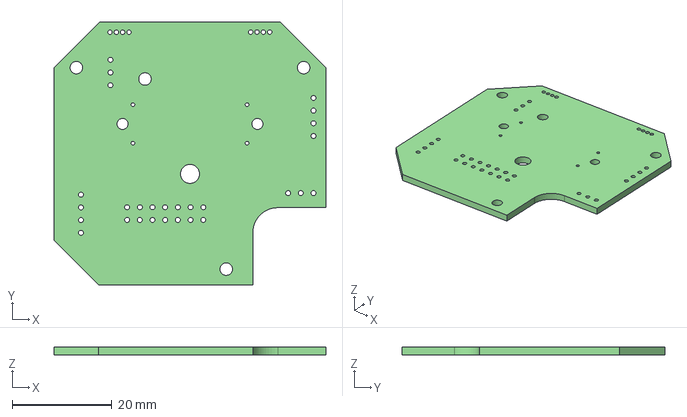
[picture p227: CAD file, 2023-02-10]
ECAD/PCBs/Functional PCBs/GAUGE_Standby Altimeter/MCAD/GAUGE_Standby Altimeter.step
54.4 x 52.6 x 1.60 mm
