Exprezz0/F-18C_Simulator/ECAD/PCBs/Functional PCBs/ifei/mcad/ifei.step

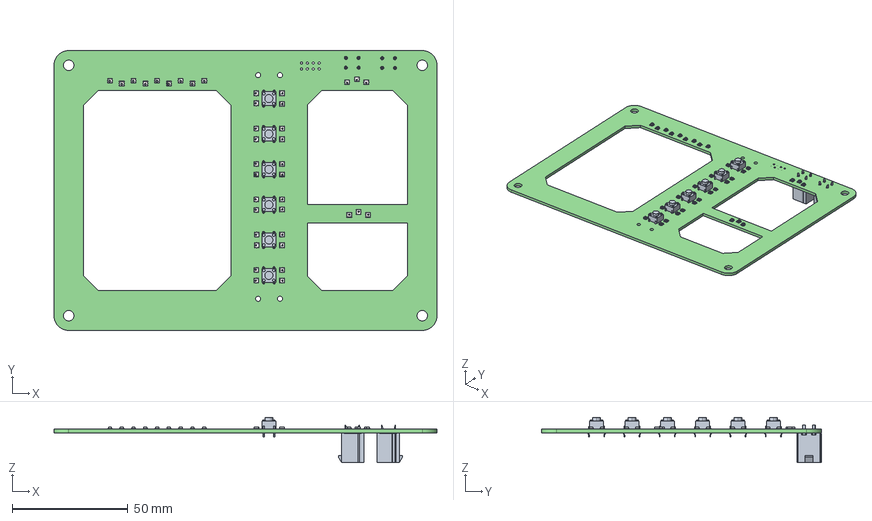
[picture p228: CAD file, 2023-02-10]
ECAD/PCBs/Functional PCBs/ifei/mcad/ifei.step
165.1 x 120.7 x 19.5 mm
_autosave-IFEI PCB
