Exprezz0/F-18C_Simulator/ECAD/PCBs/Functional PCBs/ifei/ref/IFEI.DXF

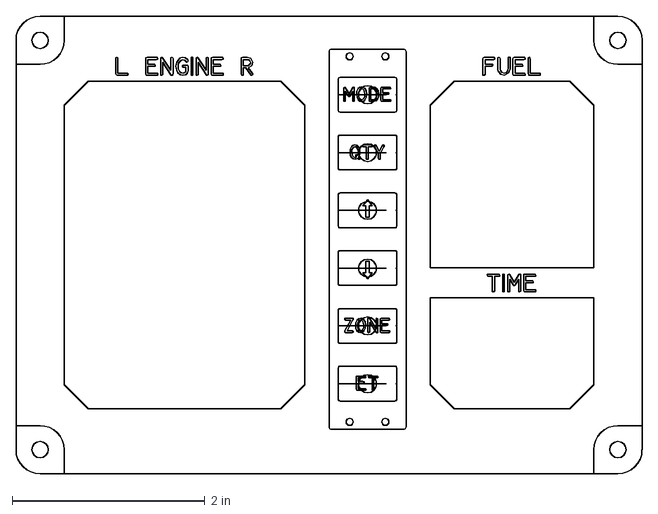
[picture p229: CAD file, 2023-01-02]
ECAD/PCBs/Functional PCBs/ifei/ref/IFEI.DXF
6.50 x 4.75 in
