Exprezz0/F-18C_Simulator/ECAD/PCBs/Functional PCBs/JETT STATION SELECT/MCAD/JETT STATION SELECT.step

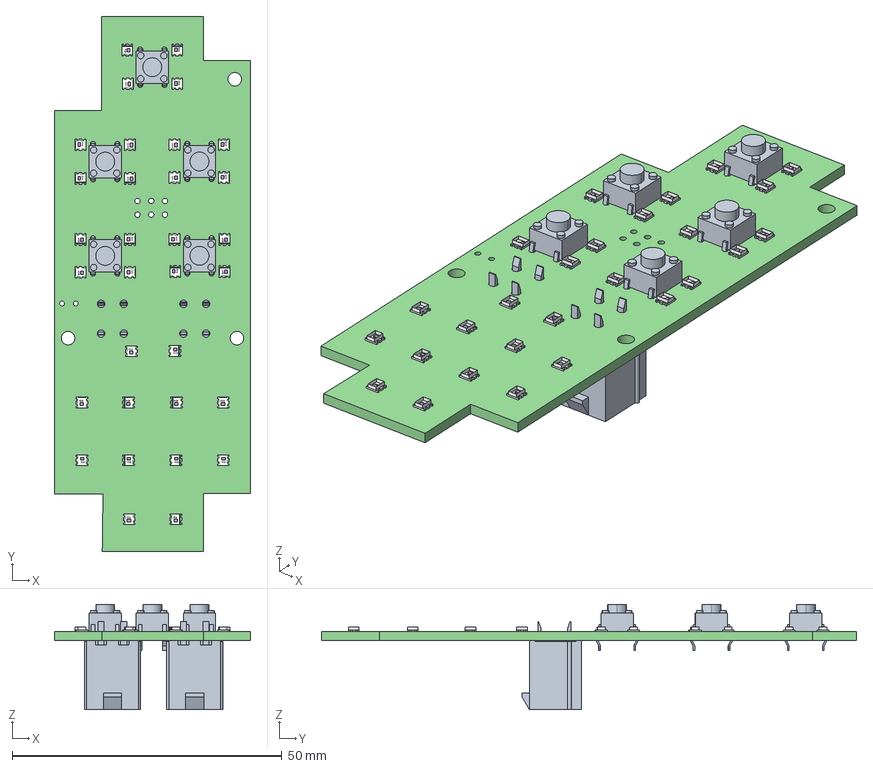
[picture p230: CAD file, 2023-02-10]
ECAD/PCBs/Functional PCBs/JETT STATION SELECT/MCAD/JETT STATION SELECT.step
36.3 x 99.1 x 19.5 mm
_autosave-JETT STATION SELECT PCB
