Exprezz0/F-18C_Simulator/ECAD/PCBs/Functional PCBs/jett_station_select/ref/JETT Select PCB.DXF

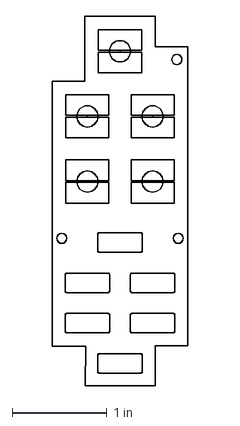
[picture p231: CAD file, 2023-01-02]
ECAD/PCBs/Functional PCBs/jett_station_select/ref/JETT Select PCB.DXF
1.43 x 3.90 in
