Exprezz0/F-18C_Simulator/ECAD/PCBs/Functional PCBs/ralt_controller/Radar Altimeter Case.DXF

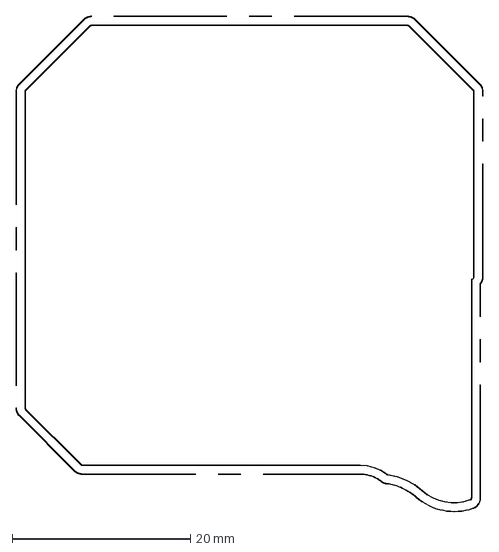
[picture p232: CAD file, 2023-01-02]
ECAD/PCBs/Functional PCBs/ralt_controller/Radar Altimeter Case.DXF
52.4 x 55.6 mm
