Exprezz0/F-18C_Simulator/ECAD/PCBs/Functional PCBs/RWR CONTROL PANEL/MCAD/RWR CONTROL PANEL.step

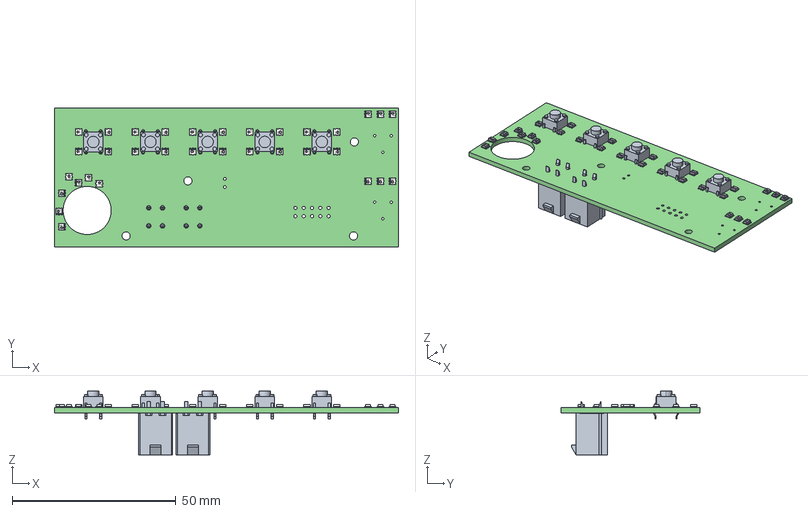
[picture p233: CAD file, 2023-02-10]
ECAD/PCBs/Functional PCBs/RWR CONTROL PANEL/MCAD/RWR CONTROL PANEL.step
105.2 x 42.4 x 19.5 mm
_autosave-RWR CONTROL PANEL PCB
