Exprezz0/F-18C_Simulator/ECAD/PCBs/Functional PCBs/RWR_Panel_PCB_V2/mcad/RWR_Control_Panel V2.5.step

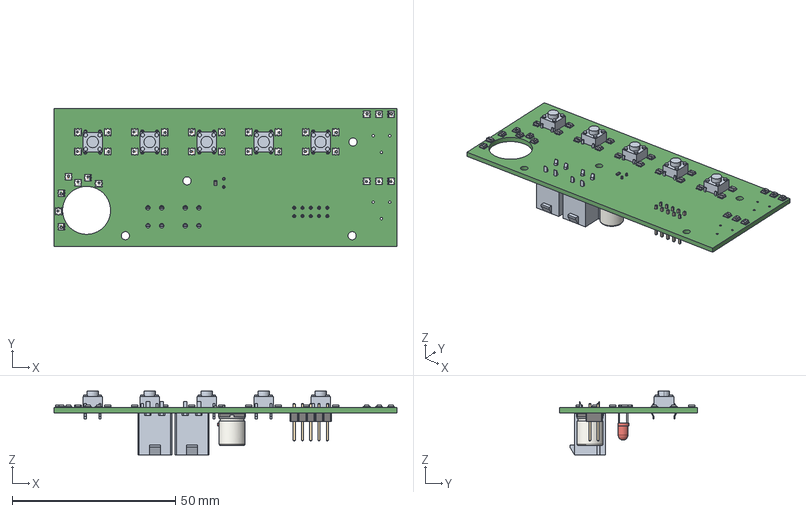
[picture p234: CAD file, 2023-01-02]
ECAD/PCBs/Functional PCBs/RWR_Panel_PCB_V2/mcad/RWR_Control_Panel V2.5.step
105.2 x 42.4 x 19.5 mm
