Exprezz0/F-18C_Simulator/ECAD/PCBs/Functional PCBs/RWR_Panel_PCB_V2/ref/Part9^RWR Control Panel.DXF

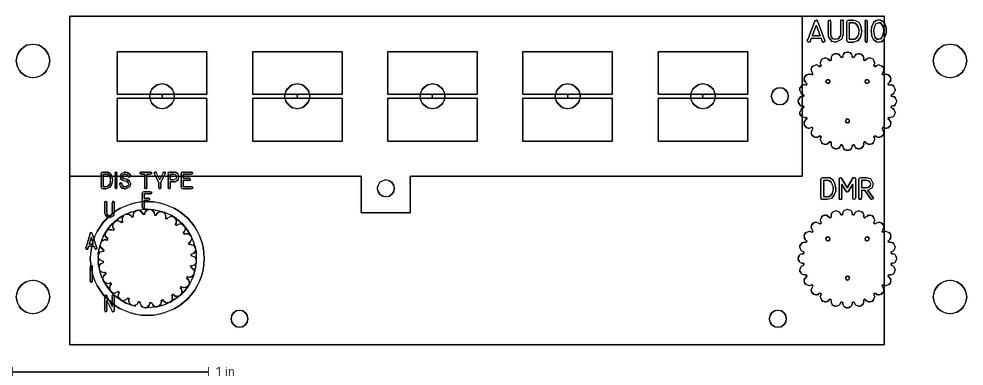
[picture p235: CAD file, 2023-01-02]
ECAD/PCBs/Functional PCBs/RWR_Panel_PCB_V2/ref/Part9^RWR Control Panel.DXF
4.83 x 1.67 in
