Exprezz0/F-18C_Simulator/ECAD/PCBs/Functional PCBs/standby_airspeed_vvi/mcad/standby_airspeed_vvi.step

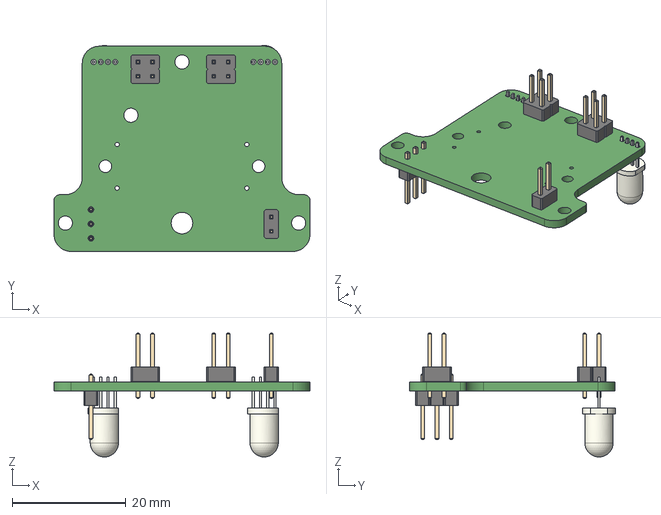
[picture p236: CAD file, 2023-01-02]
ECAD/PCBs/Functional PCBs/standby_airspeed_vvi/mcad/standby_airspeed_vvi.step
45.1 x 36.3 x 21.8 mm
