Exprezz0/F-18C_Simulator/ECAD/PCBs/Functional PCBs/standby_airspeed_vvi/ref/standby_airspeed_vvi.DXF

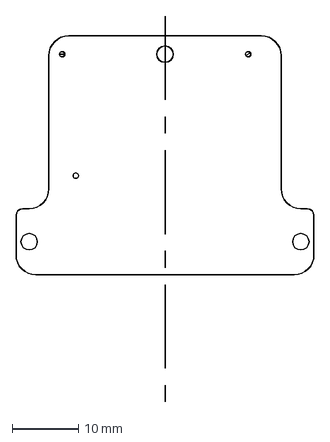
[picture p237: CAD file, 2023-01-02]
ECAD/PCBs/Functional PCBs/standby_airspeed_vvi/ref/standby_airspeed_vvi.DXF
45.1 x 58.4 mm
