Exprezz0/F-18C_Simulator/ECAD/PCBs/Functional PCBs/standby_altimeter/mcad/standby_altimeter.step

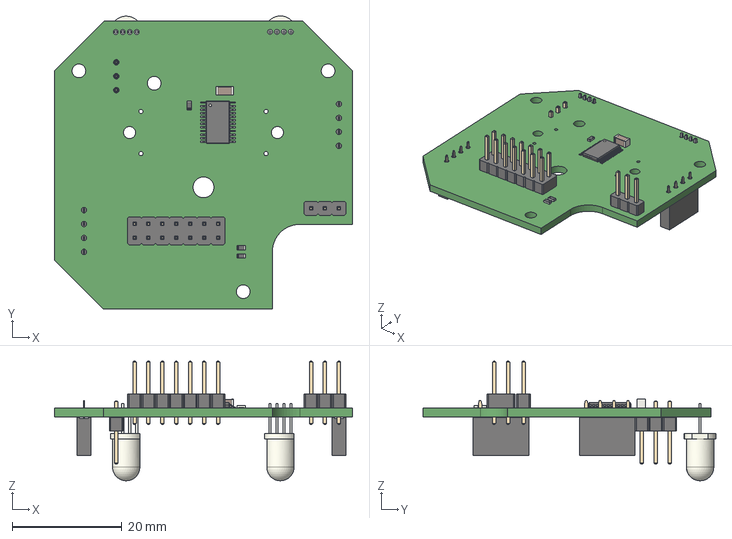
[picture p238: CAD file, 2023-01-02]
ECAD/PCBs/Functional PCBs/standby_altimeter/mcad/standby_altimeter.step
54.4 x 53.5 x 21.8 mm
