Exprezz0/F-18C_Simulator/ECAD/PCBs/Functional PCBs/standby_altimeter/ref/standby_altimeter.DXF

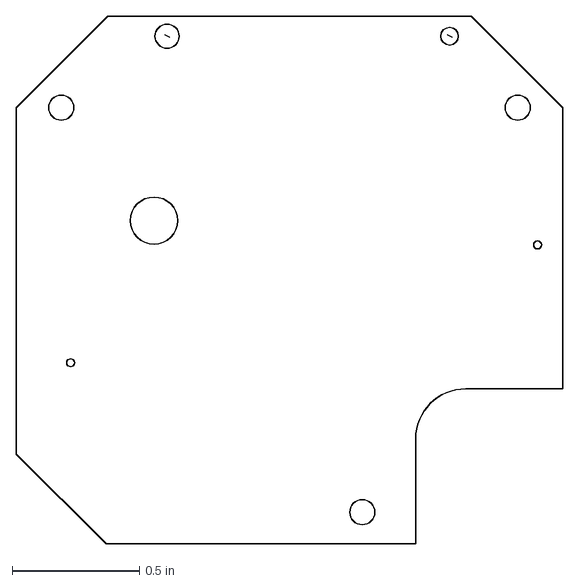
[picture p239: CAD file, 2023-01-02]
ECAD/PCBs/Functional PCBs/standby_altimeter/ref/standby_altimeter.DXF
2.14 x 2.07 in
