Exprezz0/F-18C_Simulator/ECAD/PCBs/Functional PCBs/ufc_v5_ap/ref/AP Switch Module.dxf

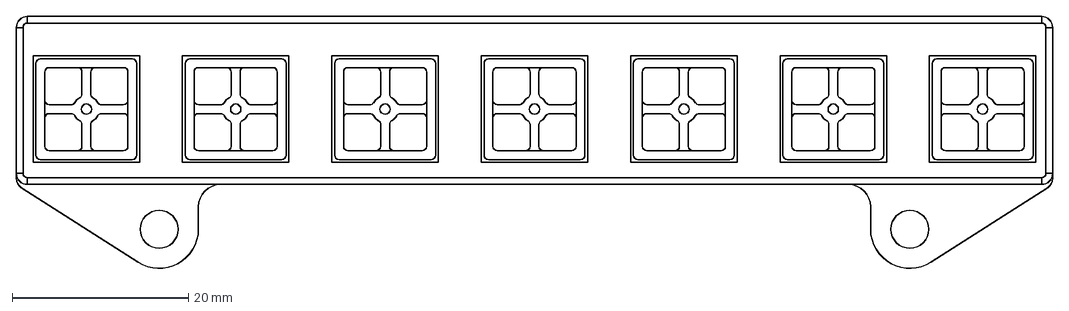
[picture p240: CAD file, 2023-01-02]
ECAD/PCBs/Functional PCBs/ufc_v5_ap/ref/AP Switch Module.dxf
117.5 x 28.8 mm
