Exprezz0/F-18C_Simulator/ECAD/PCBs/Functional PCBs/util_photoswitch/opb61x.DXF

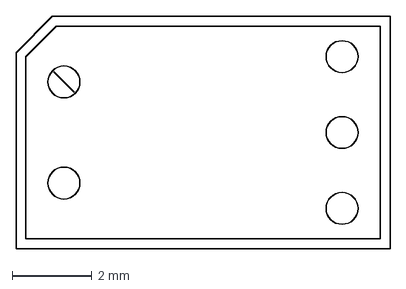
[picture p241: CAD file, 2023-01-02]
ECAD/PCBs/Functional PCBs/util_photoswitch/opb61x.DXF
9.39 x 5.83 mm
