Exprezz0/F-18C_Simulator/MCAD/ADDITIONAL RESOURCES/2.54 Pin Headers/22x1_Pin_Header_2.54mm.STEP

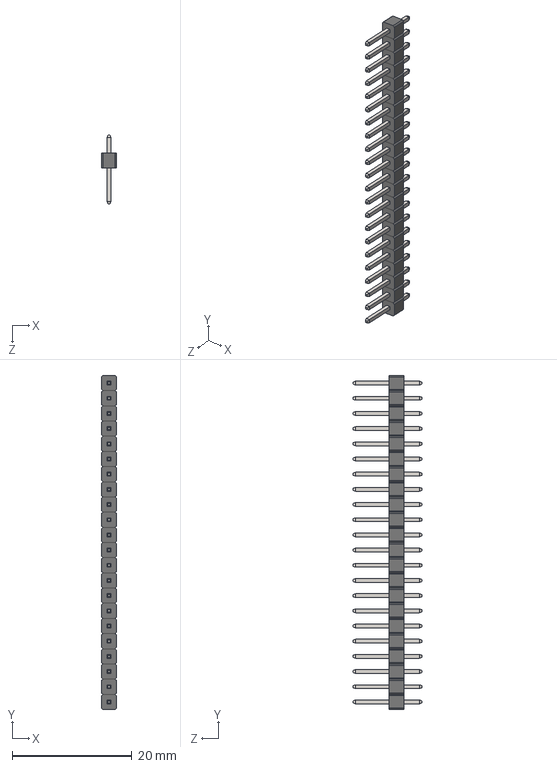
[picture p242: CAD file, 2023-01-02]
MCAD/ADDITIONAL RESOURCES/2.54 Pin Headers/22x1_Pin_Header_2.54mm.STEP
2.54 x 55.9 x 11.5 mm
1x1_Pin_Header_2.54mm x 22
