Exprezz0/F-18C_Simulator/MCAD/ADDITIONAL RESOURCES/Dupont Connector Housing/files/Box_T.STL

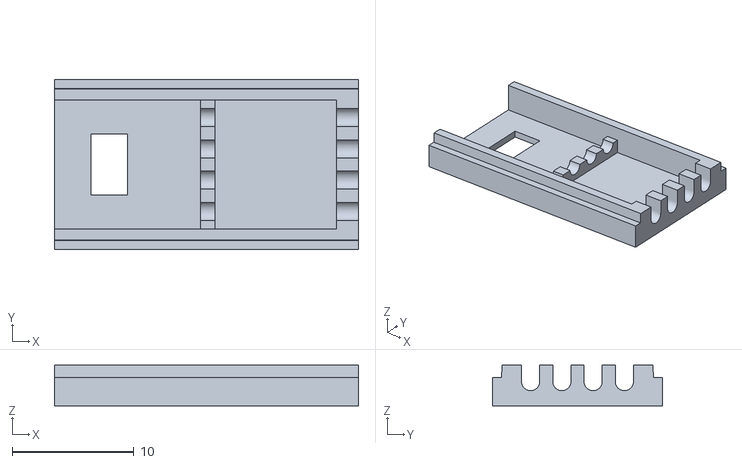
[picture p243: CAD file, 2023-01-02]
MCAD/ADDITIONAL RESOURCES/Dupont Connector Housing/files/Box_T.STL
25.0 x 14.0 x 3.35
