Exprezz0/F-18C_Simulator/MCAD/ADDITIONAL RESOURCES/DuPont/1.stl

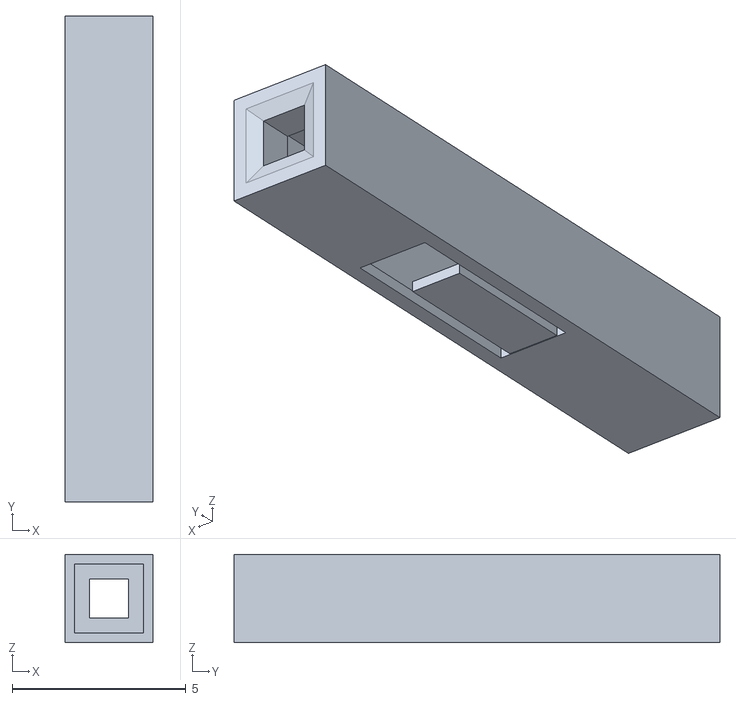
[picture p244: CAD file, 2023-01-02]
MCAD/ADDITIONAL RESOURCES/DuPont/1.stl
2.54 x 14.0 x 2.54
