Exprezz0/F-18C_Simulator/MCAD/ADDITIONAL RESOURCES/DuPont/DS1071-1xN (BLS)/DS1071-1x12.STEP

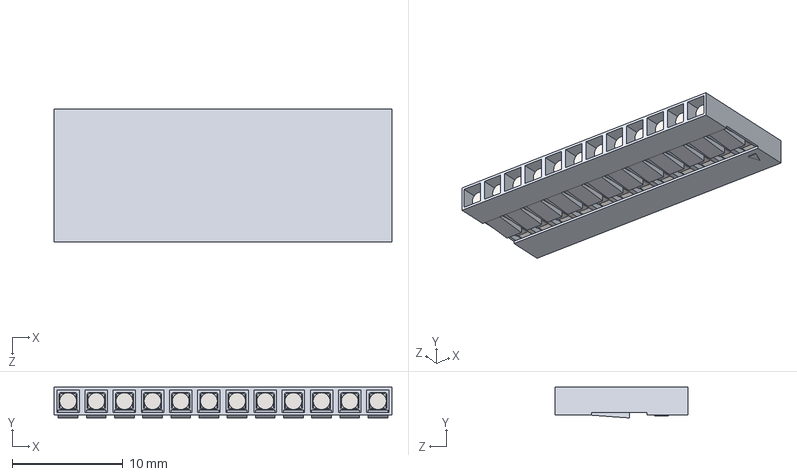
[picture p245: CAD file, 2023-01-02]
MCAD/ADDITIONAL RESOURCES/DuPont/DS1071-1xN (BLS)/DS1071-1x12.STEP
30.5 x 2.79 x 12.0 mm
