Exprezz0/F-18C_Simulator/MCAD/ADDITIONAL RESOURCES/DuPont/DS1071-2xN (BLD)/DS1071-2x8.STEP

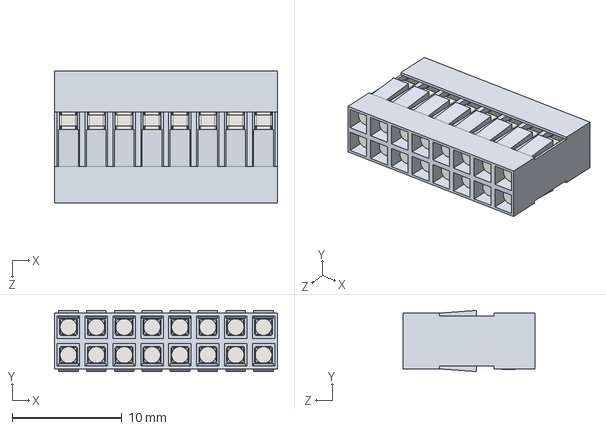
[picture p246: CAD file, 2023-01-02]
MCAD/ADDITIONAL RESOURCES/DuPont/DS1071-2xN (BLD)/DS1071-2x8.STEP
20.3 x 5.57 x 12.0 mm
