Exprezz0/F-18C_Simulator/MCAD/ADDITIONAL RESOURCES/dupont_organizer.stl

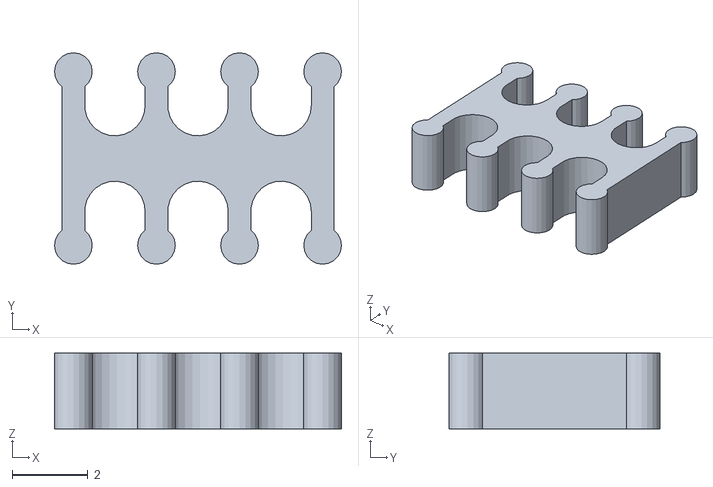
[picture p247: CAD file, 2023-01-02]
MCAD/ADDITIONAL RESOURCES/dupont_organizer.stl
7.60 x 5.60 x 2.00
