Exprezz0/F-18C_Simulator/MCAD/ADDITIONAL RESOURCES/Housing for connectors/Bottom 2x5.stl

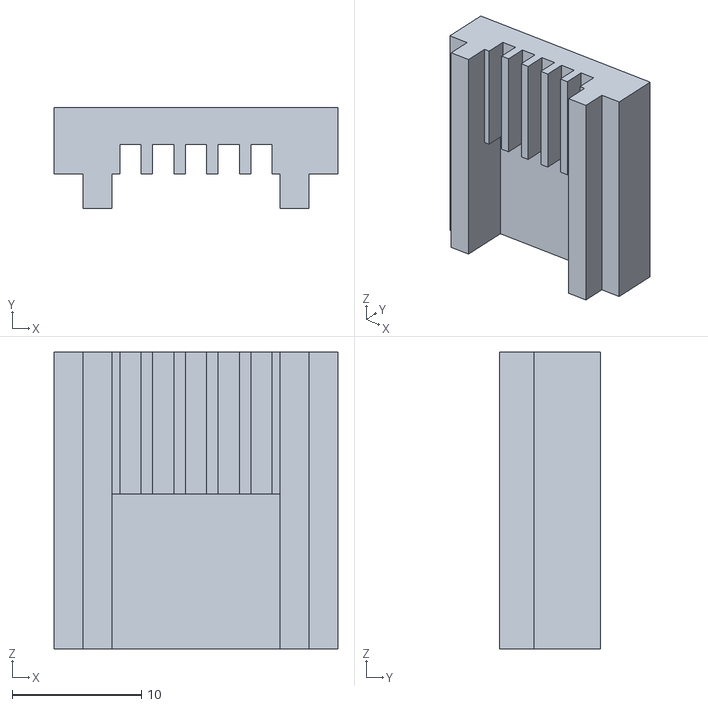
[picture p248: CAD file, 2023-01-02]
MCAD/ADDITIONAL RESOURCES/Housing for connectors/Bottom 2x5.stl
22.0 x 7.80 x 23.0
