Exprezz0/F-18C_Simulator/MCAD/ADDITIONAL RESOURCES/Housing for connectors/files/Dupont_holder_x5.stl

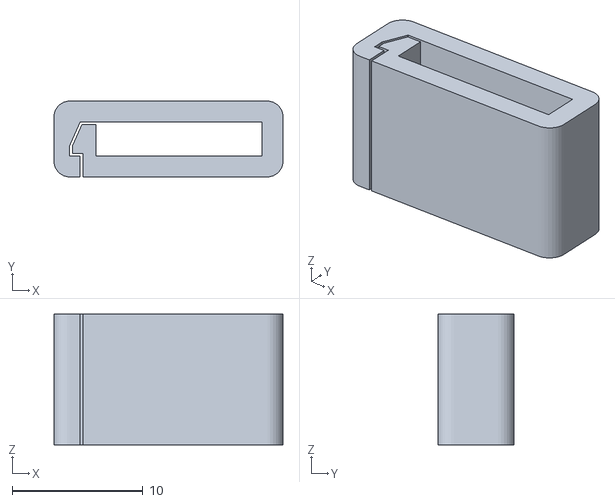
[picture p249: CAD file, 2023-01-02]
MCAD/ADDITIONAL RESOURCES/Housing for connectors/files/Dupont_holder_x5.stl
17.5 x 5.80 x 10.0
