Exprezz0/F-18C_Simulator/MCAD/ASSY, LEFT CONSOLE/ALL KNOBS/LDG GEAR PANEL, Warn Tone Silence Switch Cap.stl

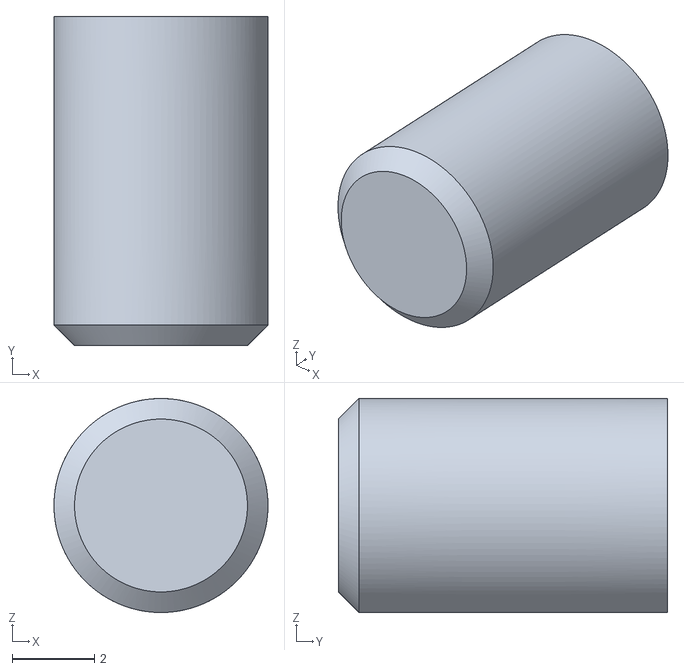
[picture p250: CAD file, 2023-01-02]
MCAD/ASSY, LEFT CONSOLE/ALL KNOBS/LDG GEAR PANEL, Warn Tone Silence Switch Cap.stl
5.20 x 8.00 x 5.20
