Exprezz0/F-18C_Simulator/MCAD/ASSY, LEFT CONSOLE/ALL PANEL PLATES/BACK PLATE (.125)/OH4A3A1-11 - SELECT JETT BACKPLATE.dxf

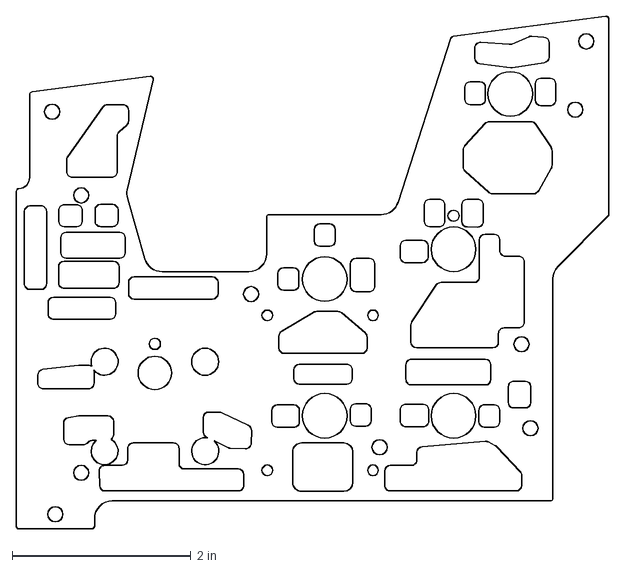
[picture p251: CAD file, 2023-04-01]
MCAD/ASSY, LEFT CONSOLE/ALL PANEL PLATES/BACK PLATE (.125)/OH4A3A1-11 - SELECT JETT BACKPLATE.dxf
6.63 x 5.73 in
