Exprezz0/F-18C_Simulator/MCAD/ASSY, LEFT CONSOLE/ALL PANEL PLATES/LEGEND PLATE (.0625)/OH4A7A4-13 - ANT SEL LEGEND PLATE.dxf

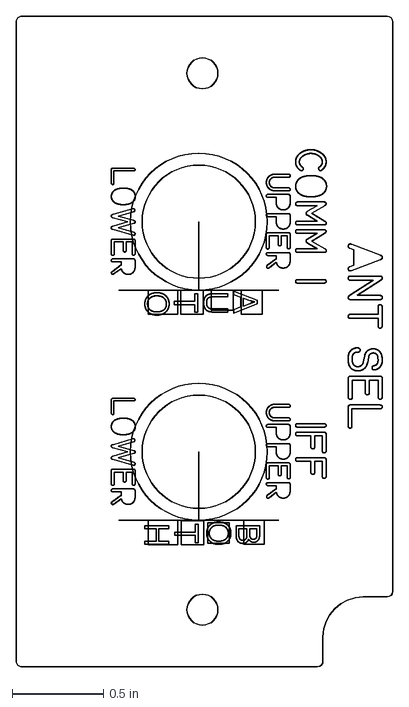
[picture p252: CAD file, 2023-04-22]
MCAD/ASSY, LEFT CONSOLE/ALL PANEL PLATES/LEGEND PLATE (.0625)/OH4A7A4-13 - ANT SEL LEGEND PLATE.dxf
2.06 x 3.56 in
