Exprezz0/F-18C_Simulator/MCAD/ASSY, LEFT CONSOLE/ALL PANEL PLATES/LIGHT PLATE (.1875)/OH4A1A1-12 - SEL JETT PANEL LIGHTPLATE.dxf

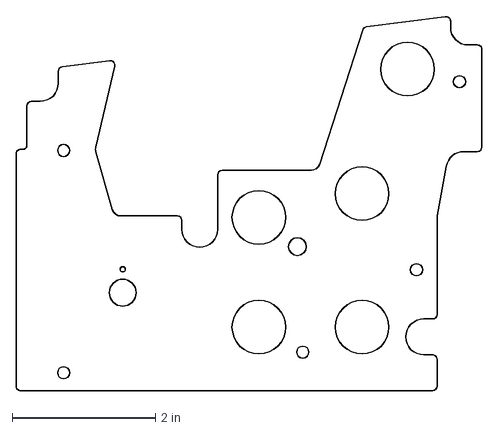
[picture p253: CAD file, 2023-01-02]
MCAD/ASSY, LEFT CONSOLE/ALL PANEL PLATES/LIGHT PLATE (.1875)/OH4A1A1-12 - SEL JETT PANEL LIGHTPLATE.dxf
6.50 x 5.22 in
