Exprezz0/F-18C_Simulator/MCAD/ASSY, LEFT CONSOLE/OH4A1A1-1 - ASSY, LEFT CONSOLE STRUCTURE/ACRYLIC/Left AUX Panel_2ACRYLIC.DXF

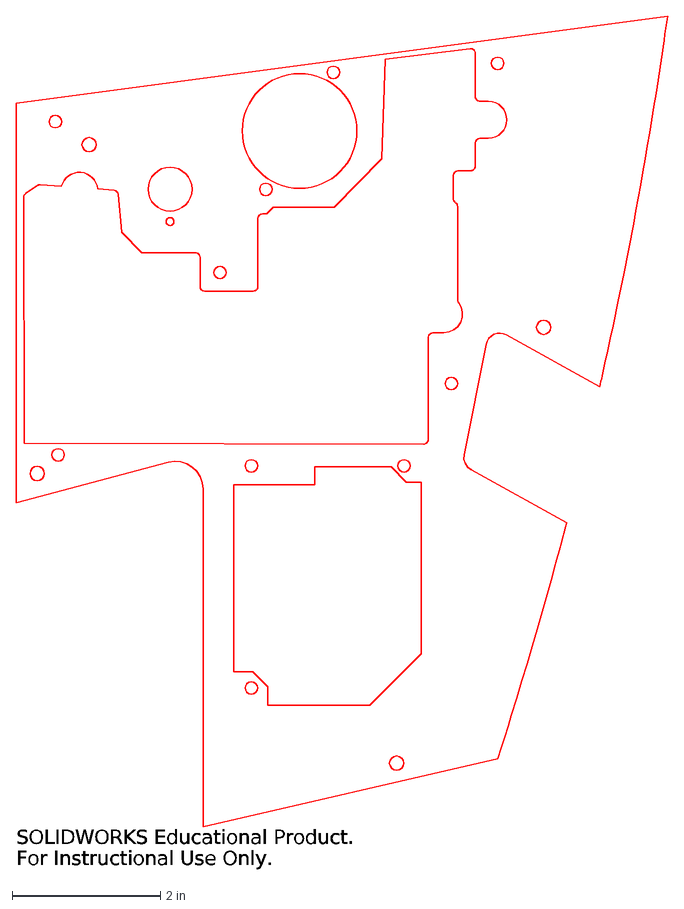
[picture p254: CAD file, 2023-01-02]
MCAD/ASSY, LEFT CONSOLE/OH4A1A1-1 - ASSY, LEFT CONSOLE STRUCTURE/ACRYLIC/Left AUX Panel_2ACRYLIC.DXF
SOLIDWORKS Educational Product.
For Instructional Use Only.
