Exprezz0/F-18C_Simulator/MCAD/ASSY, LEFT CONSOLE/OH4A1A1-1 - ASSY, LEFT CONSOLE STRUCTURE/MDF/.25/Left AUX Panel Edge Test (Entity_0).DXF

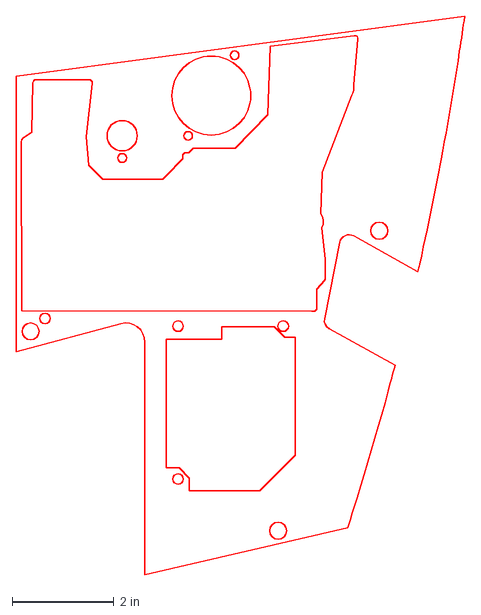
[picture p255: CAD file, 2023-01-02]
MCAD/ASSY, LEFT CONSOLE/OH4A1A1-1 - ASSY, LEFT CONSOLE STRUCTURE/MDF/.25/Left AUX Panel Edge Test (Entity_0).DXF
8.80 x 11.0 in
