Exprezz0/F-18C_Simulator/MCAD/ASSY, LEFT CONSOLE/OH4A1A1-1 - ASSY, LEFT CONSOLE STRUCTURE/MDF/.75/Primary Rib E.DXF

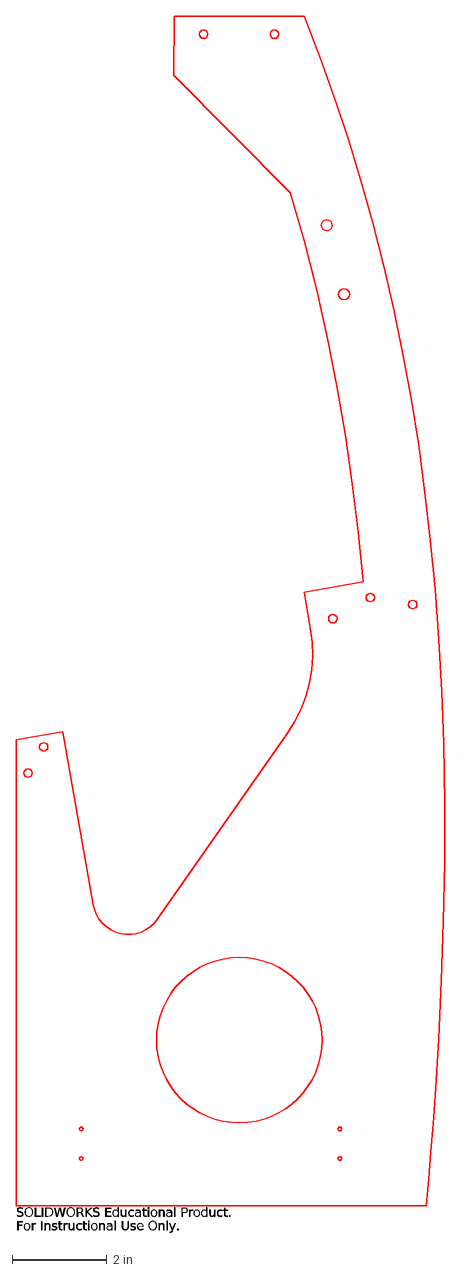
[picture p256: CAD file, 2023-01-02]
MCAD/ASSY, LEFT CONSOLE/OH4A1A1-1 - ASSY, LEFT CONSOLE STRUCTURE/MDF/.75/Primary Rib E.DXF
SOLIDWORKS Educational Product.
For Instructional Use Only.
