Exprezz0/F-18C_Simulator/MCAD/ASSY, LEFT CONSOLE/OH4A1A1-1 - ASSY, LEFT CONSOLE STRUCTURE/OH4A1A1-37 - INBOARD WALL SUPPORT.stl

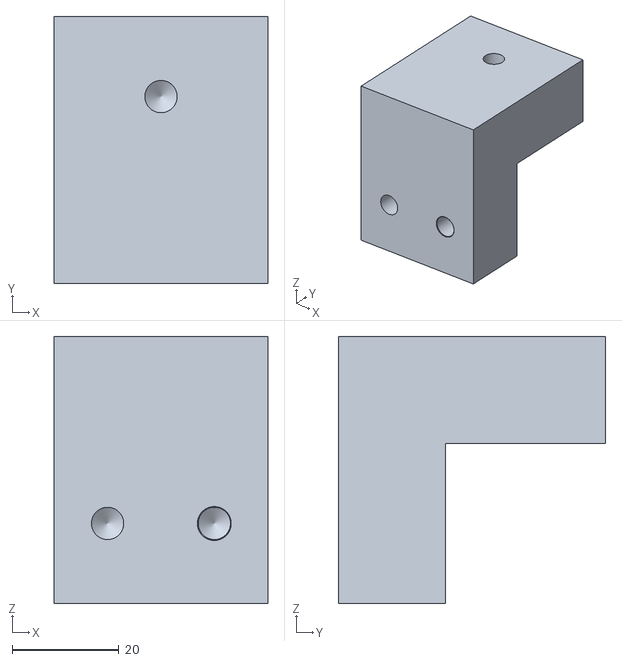
[picture p257: CAD file, 2023-01-03]
MCAD/ASSY, LEFT CONSOLE/OH4A1A1-1 - ASSY, LEFT CONSOLE STRUCTURE/OH4A1A1-37 - INBOARD WALL SUPPORT.stl
40.0 x 50.0 x 50.0
