Exprezz0/F-18C_Simulator/MCAD/ASSY, LEFT CONSOLE/OH4A1A1-1 - ASSY, LEFT CONSOLE STRUCTURE/PETG/C-D Left Outboard Spacer.STL

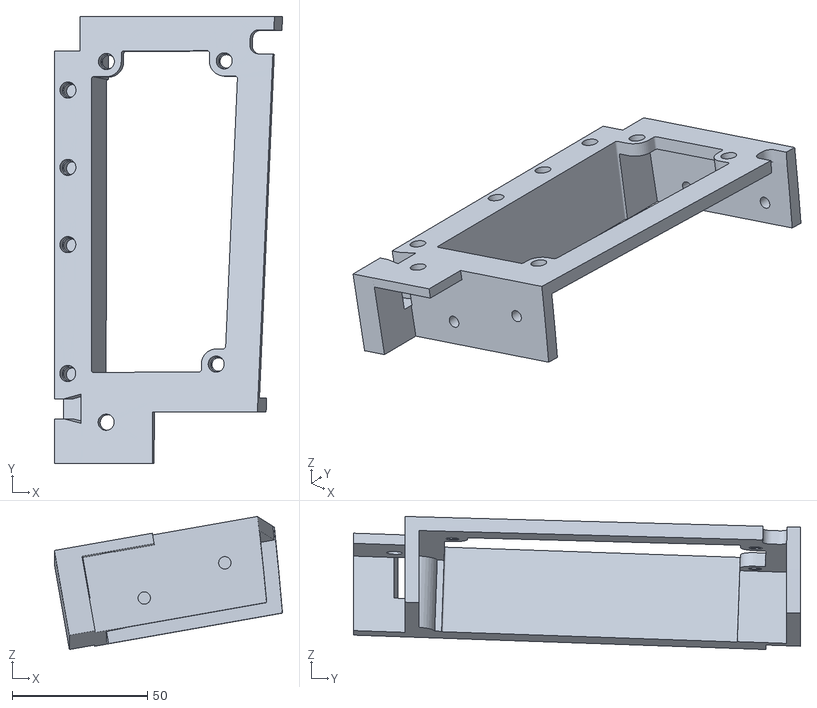
[picture p258: CAD file, 2023-01-02]
MCAD/ASSY, LEFT CONSOLE/OH4A1A1-1 - ASSY, LEFT CONSOLE STRUCTURE/PETG/C-D Left Outboard Spacer.STL
84.3 x 165.2 x 49.2
