Exprezz0/F-18C_Simulator/MCAD/ASSY, LEFT CONSOLE/OH4A1A1-1 - ASSY, LEFT CONSOLE STRUCTURE/WINWING Throttle Mod/OH4A1A1-48 - LEFT AUX SUPPORT BRACKET, LOWER, OUTBOARD.stl

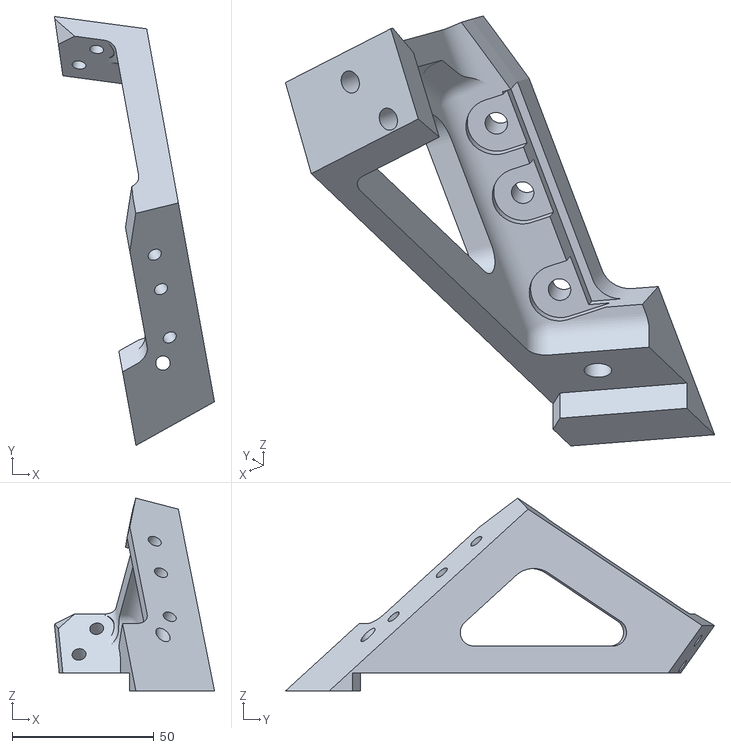
[picture p259: CAD file, 2023-01-03]
MCAD/ASSY, LEFT CONSOLE/OH4A1A1-1 - ASSY, LEFT CONSOLE STRUCTURE/WINWING Throttle Mod/OH4A1A1-48 - LEFT AUX SUPPORT BRACKET, LOWER, OUTBOARD.stl
56.5 x 151.5 x 68.1
