Exprezz0/F-18C_Simulator/MCAD/ASSY, LEFT CONSOLE/OH4A2A1-1 - ASSY, LANDING GEAR LEVER PANEL/landing gear_upper tube.stl

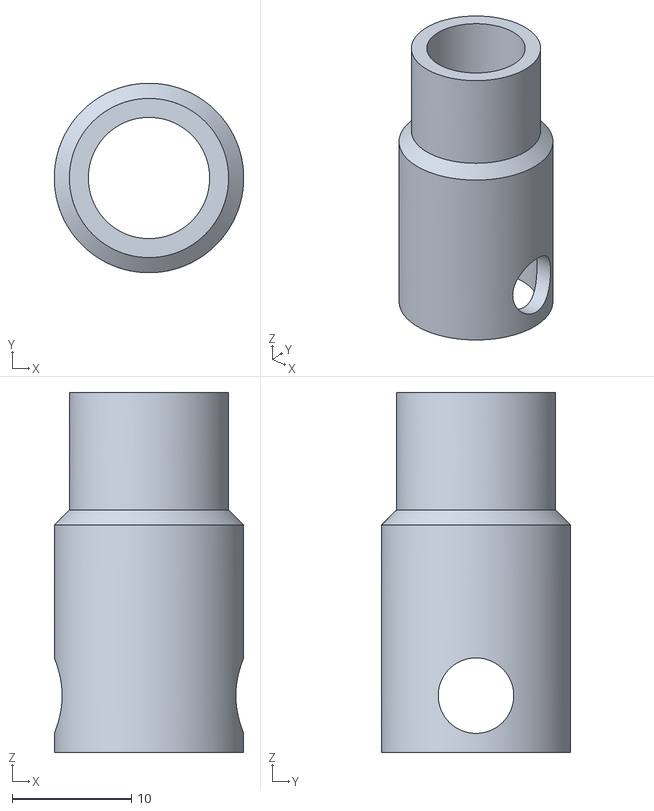
[picture p260: CAD file, 2023-01-02]
MCAD/ASSY, LEFT CONSOLE/OH4A2A1-1 - ASSY, LANDING GEAR LEVER PANEL/landing gear_upper tube.stl
15.9 x 15.9 x 30.2
