Exprezz0/F-18C_Simulator/MCAD/ASSY, LEFT CONSOLE/OH4A2A1-1 - ASSY, LANDING GEAR LEVER PANEL/RESIN/Landing Gear Level Lollipop Cover.STL

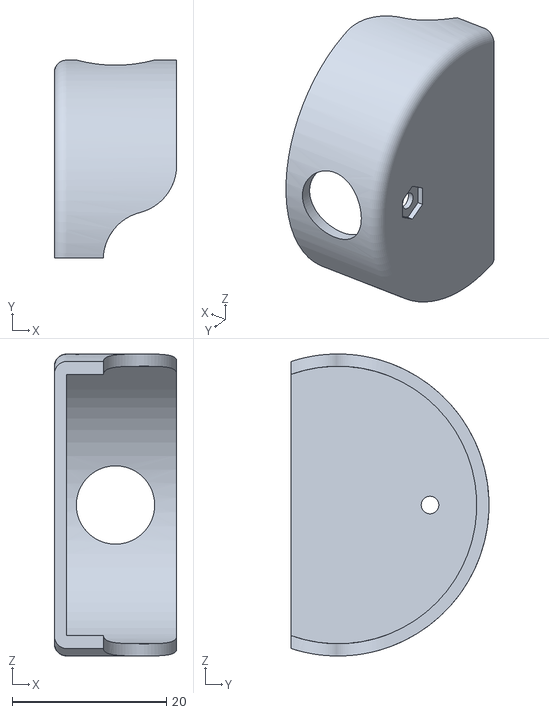
[picture p261: CAD file, 2023-01-02]
MCAD/ASSY, LEFT CONSOLE/OH4A2A1-1 - ASSY, LANDING GEAR LEVER PANEL/RESIN/Landing Gear Level Lollipop Cover.STL
15.9 x 25.7 x 39.2
