Exprezz0/F-18C_Simulator/MCAD/ASSY, LEFT CONSOLE/OH4A3A1-1 - ASSY, SELECT JETT PANEL/RESIN/OH4A3A1-103 - SELECT JETT SWITCH BRACKET_v2.stl

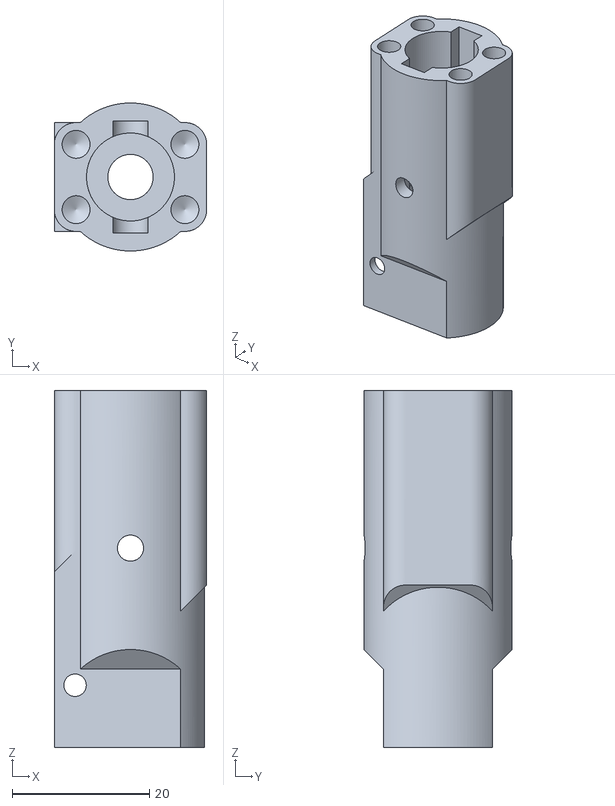
[picture p262: CAD file, 2023-01-02]
MCAD/ASSY, LEFT CONSOLE/OH4A3A1-1 - ASSY, SELECT JETT PANEL/RESIN/OH4A3A1-103 - SELECT JETT SWITCH BRACKET_v2.stl
22.2 x 21.6 x 52.1
