Exprezz0/F-18C_Simulator/MCAD/ASSY, LEFT CONSOLE/OH4A3A3-1 - ASSY, BRAKE PRESSURE INDICATOR/PETG/OH4A3A3-10 - 1.5 IN Case.stl

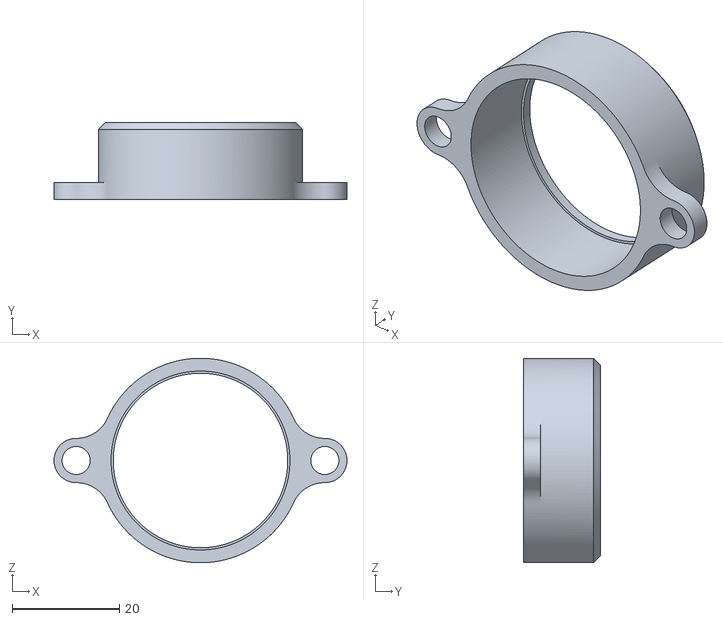
[picture p263: CAD file, 2023-01-02]
MCAD/ASSY, LEFT CONSOLE/OH4A3A3-1 - ASSY, BRAKE PRESSURE INDICATOR/PETG/OH4A3A3-10 - 1.5 IN Case.stl
54.6 x 14.3 x 38.1
