Exprezz0/F-18C_Simulator/MCAD/ASSY, LEFT CONSOLE/OH4A3A3-1 - ASSY, BRAKE PRESSURE INDICATOR/RESIN/OH4A3A3-13 - BRAKE PRESSURE INDICATOR SPACER.stl

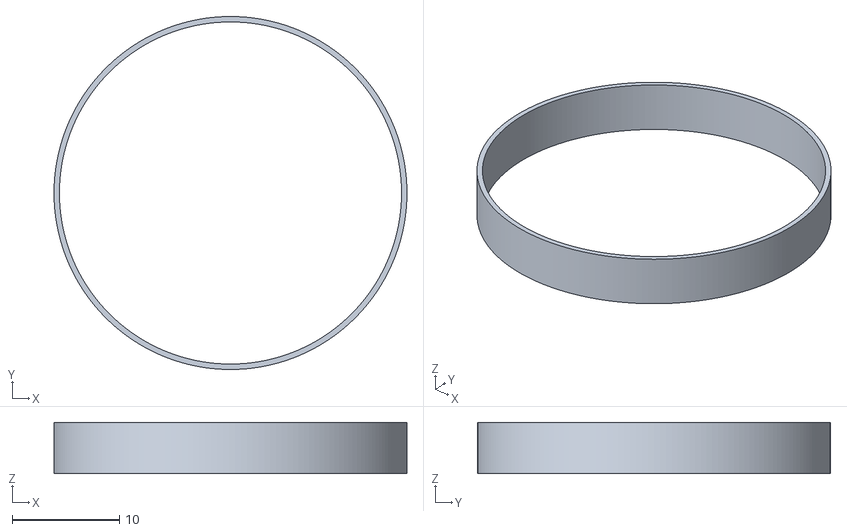
[picture p264: CAD file, 2023-01-02]
MCAD/ASSY, LEFT CONSOLE/OH4A3A3-1 - ASSY, BRAKE PRESSURE INDICATOR/RESIN/OH4A3A3-13 - BRAKE PRESSURE INDICATOR SPACER.stl
32.8 x 32.8 x 4.76
