Exprezz0/F-18C_Simulator/MCAD/ASSY, LEFT CONSOLE/OH4A4A2-1 - ASSY, EXTERNAL LT PANEL/OH4A4A2-14 - EXT LT ABSIS ADAPTER PLATE.stl

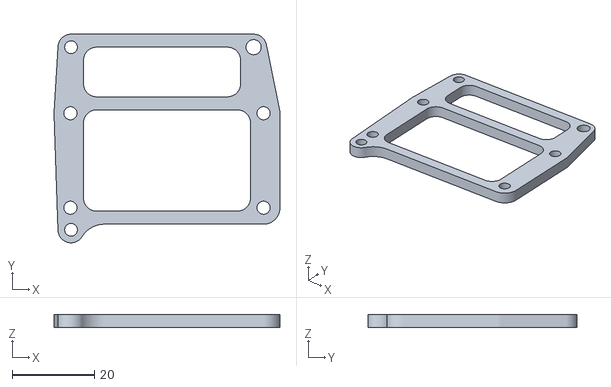
[picture p265: CAD file, 2023-01-02]
MCAD/ASSY, LEFT CONSOLE/OH4A4A2-1 - ASSY, EXTERNAL LT PANEL/OH4A4A2-14 - EXT LT ABSIS ADAPTER PLATE.stl
55.0 x 50.8 x 3.17
