Exprezz0/F-18C_Simulator/MCAD/ASSY, LEFT CONSOLE/OH4A5A1-1 - ASSY, FUEL PANEL/OH4A5A1-15 - FUEL ABSIS ADAPTER PLATE.stl

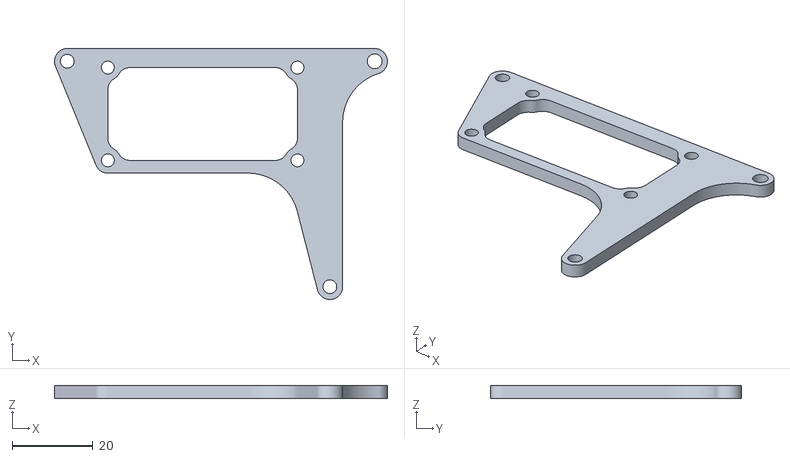
[picture p266: CAD file, 2023-01-02]
MCAD/ASSY, LEFT CONSOLE/OH4A5A1-1 - ASSY, FUEL PANEL/OH4A5A1-15 - FUEL ABSIS ADAPTER PLATE.stl
82.5 x 62.2 x 3.17
