Exprezz0/F-18C_Simulator/MCAD/ASSY, LEFT CONSOLE/OH4A6A1-1 - ASSY, FCS PANEL/OH4A6A1-102-RUD TRIM, UPPER BRACKET.stl

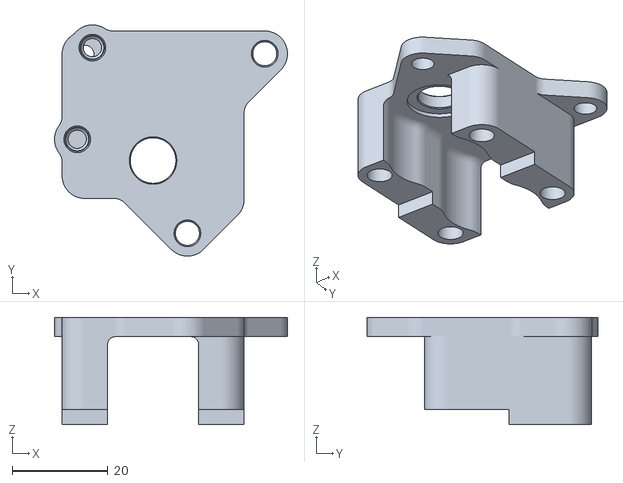
[picture p267: CAD file, 2023-01-02]
MCAD/ASSY, LEFT CONSOLE/OH4A6A1-1 - ASSY, FCS PANEL/OH4A6A1-102-RUD TRIM, UPPER BRACKET.stl
48.8 x 48.4 x 22.5
