Exprezz0/F-18C_Simulator/MCAD/ASSY, LEFT CONSOLE/OH4A6A1-1 - ASSY, FCS PANEL/RESIN/TO_Trim Button.stl

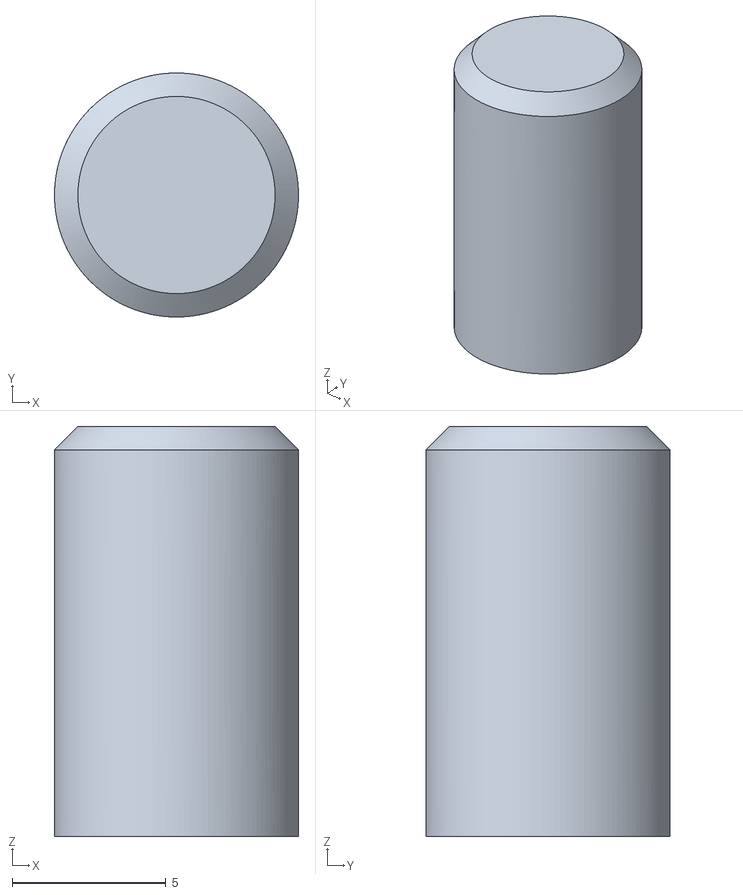
[picture p268: CAD file, 2023-01-02]
MCAD/ASSY, LEFT CONSOLE/OH4A6A1-1 - ASSY, FCS PANEL/RESIN/TO_Trim Button.stl
7.94 x 7.94 x 13.3
