Exprezz0/F-18C_Simulator/MCAD/ASSY, LEFT CONSOLE/OH4A7A1-1 - ASSY, COMM PANEL/comm_adapter_plate.stl

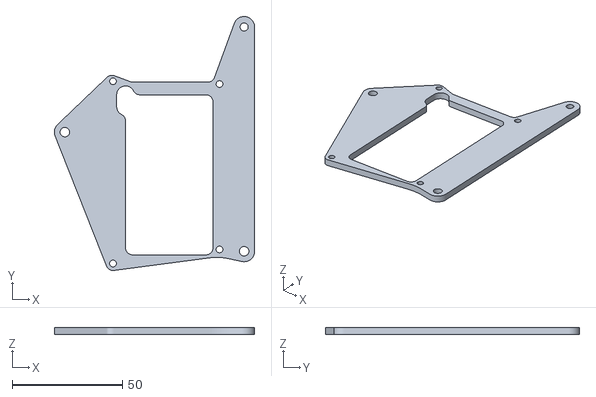
[picture p269: CAD file, 2023-01-02]
MCAD/ASSY, LEFT CONSOLE/OH4A7A1-1 - ASSY, COMM PANEL/comm_adapter_plate.stl
90.7 x 115.1 x 3.18
