Exprezz0/F-18C_Simulator/MCAD/ASSY, LEFT CONSOLE/OH4A7A2-1 - ASSY, OBOGS PANEL/obogs_adapter_plate.stl

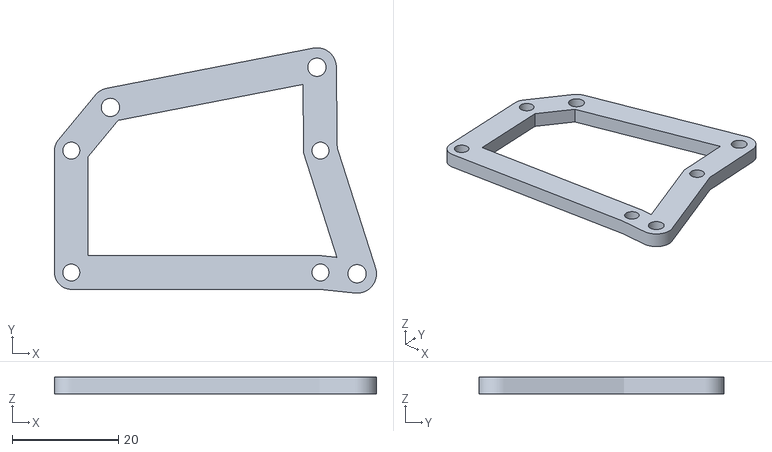
[picture p270: CAD file, 2023-01-02]
MCAD/ASSY, LEFT CONSOLE/OH4A7A2-1 - ASSY, OBOGS PANEL/obogs_adapter_plate.stl
60.7 x 46.3 x 3.18
