Exprezz0/F-18C_Simulator/MCAD/ASSY, LEFT CONSOLE/OH4A7A2-1 - ASSY, OBOGS PANEL/RESIN/OBOGS Regulator.stl

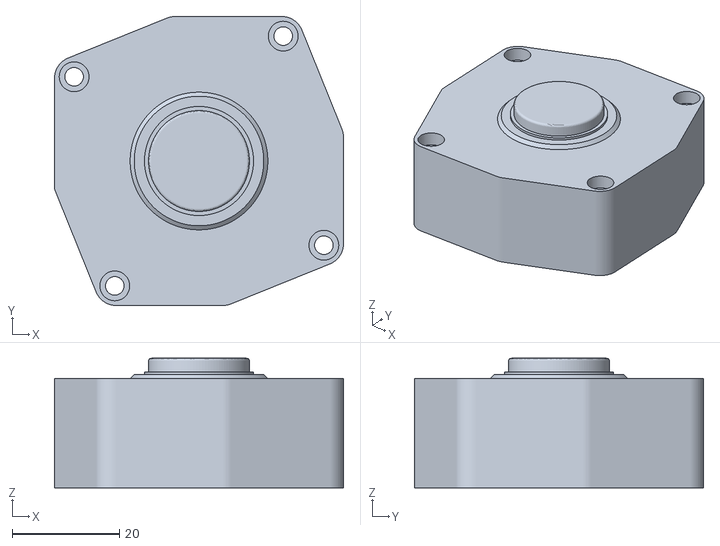
[picture p271: CAD file, 2023-01-02]
MCAD/ASSY, LEFT CONSOLE/OH4A7A2-1 - ASSY, OBOGS PANEL/RESIN/OBOGS Regulator.stl
53.8 x 53.8 x 24.1
