Exprezz0/F-18C_Simulator/MCAD/ASSY, LEFT CONSOLE/OH4A8A1-10 - LEFT CIRCUIT BREAKER/PETG/OH4A8A1-10 - LEFT CIRCUIT BREAKER BRACKET.stl

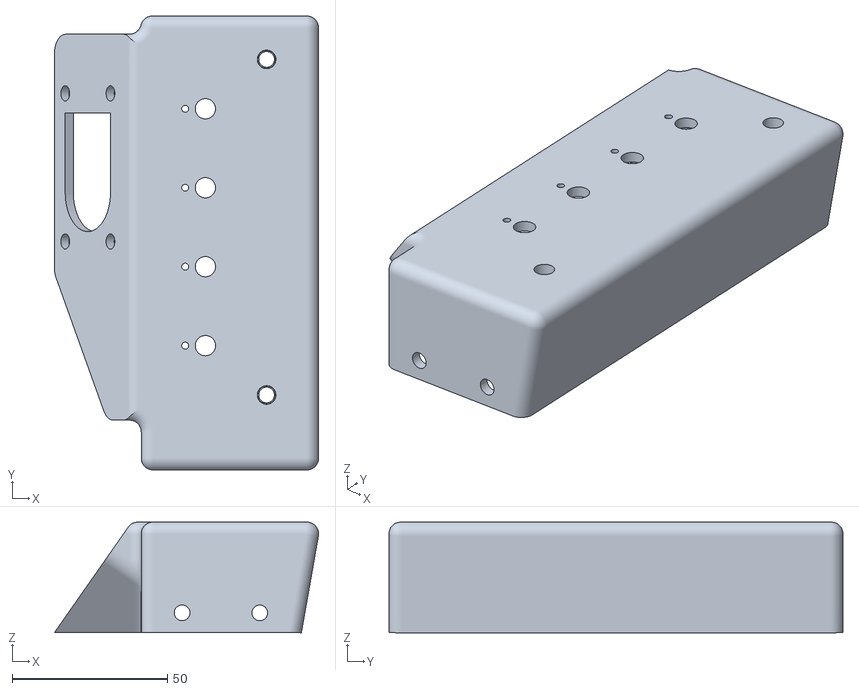
[picture p272: CAD file, 2023-01-02]
MCAD/ASSY, LEFT CONSOLE/OH4A8A1-10 - LEFT CIRCUIT BREAKER/PETG/OH4A8A1-10 - LEFT CIRCUIT BREAKER BRACKET.stl
85.0 x 146.0 x 35.7
