Exprezz0/F-18C_Simulator/MCAD/ASSY, LEFT CONSOLE/OH4A8A2-1 - ASSY, DISPENSE BUTTON/RESIN/OH4A8A2-100 - DISP_BUTTON_HEAD (1).stl

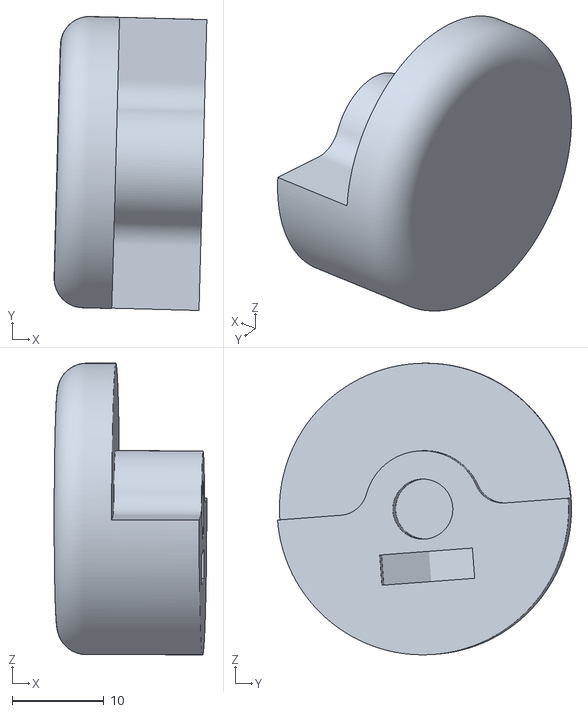
[picture p273: CAD file, 2023-01-02]
MCAD/ASSY, LEFT CONSOLE/OH4A8A2-1 - ASSY, DISPENSE BUTTON/RESIN/OH4A8A2-100 - DISP_BUTTON_HEAD (1).stl
16.6 x 32.0 x 31.8
