Exprezz0/F-18C_Simulator/MCAD/ASSY, LEFT CONSOLE/RANDOM COTS PARTS/Hex Standoff 3D Print.stl

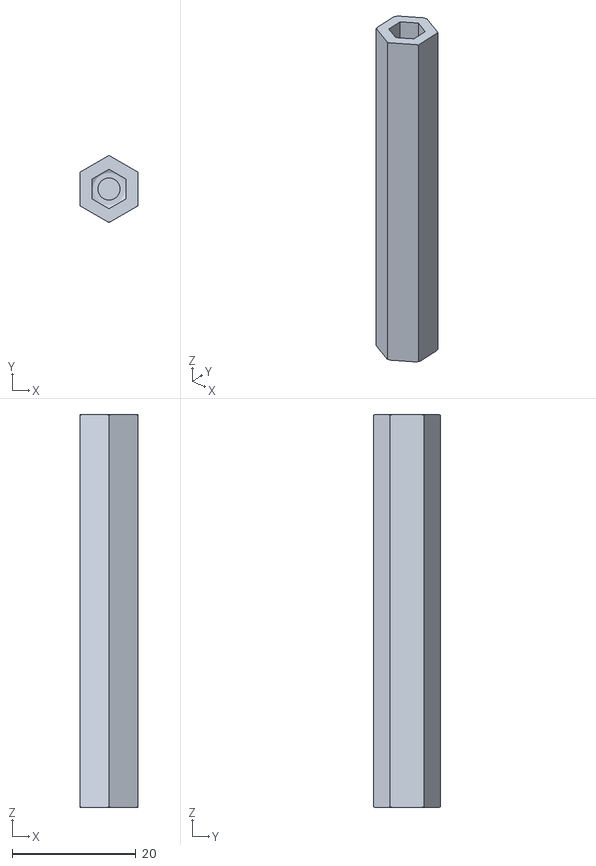
[picture p274: CAD file, 2023-01-02]
MCAD/ASSY, LEFT CONSOLE/RANDOM COTS PARTS/Hex Standoff 3D Print.stl
9.40 x 10.9 x 63.5
