Exprezz0/F-18C_Simulator/MCAD/ASSY, LOWER INSTRUMENT PANEL/ACRYLIC/BACKLIGHT PLATE (.125)/JETT Station Select Backplate.DXF

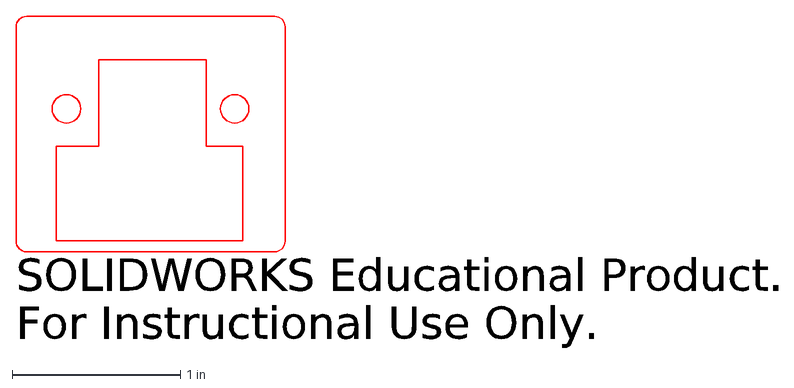
[picture p275: CAD file, 2023-01-02]
MCAD/ASSY, LOWER INSTRUMENT PANEL/ACRYLIC/BACKLIGHT PLATE (.125)/JETT Station Select Backplate.DXF
SOLIDWORKS Educational Product.
For Instructional Use Only.
