Exprezz0/F-18C_Simulator/MCAD/ASSY, LOWER INSTRUMENT PANEL/ACRYLIC/LEGEND PLATE (.0625)/CABIN PRESS Dial Face.DXF

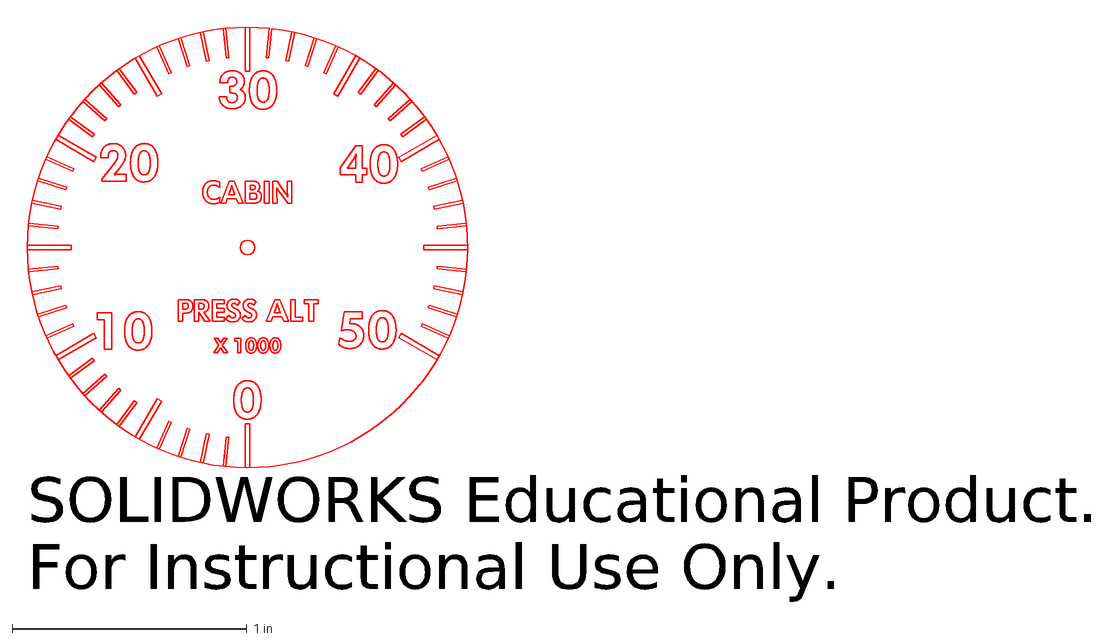
[picture p276: CAD file, 2023-01-02]
MCAD/ASSY, LOWER INSTRUMENT PANEL/ACRYLIC/LEGEND PLATE (.0625)/CABIN PRESS Dial Face.DXF
SOLIDWORKS Educational Product.
For Instructional Use Only.
