Exprezz0/F-18C_Simulator/MCAD/ASSY, LOWER INSTRUMENT PANEL/ACRYLIC/LEGEND PLATE (.0625)/no words/DISP-EMC Panel Legendplate_no words.DXF

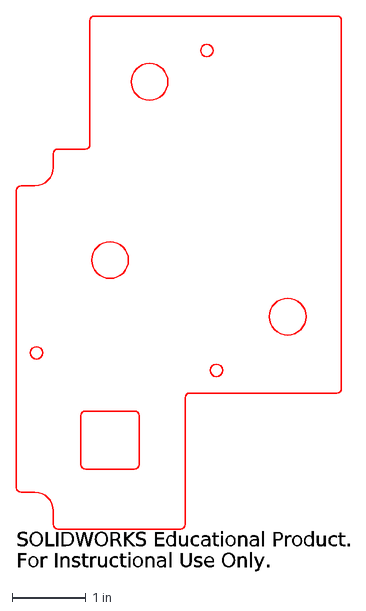
[picture p277: CAD file, 2023-01-02]
MCAD/ASSY, LOWER INSTRUMENT PANEL/ACRYLIC/LEGEND PLATE (.0625)/no words/DISP-EMC Panel Legendplate_no words.DXF
SOLIDWORKS Educational Product.
For Instructional Use Only.
