Exprezz0/F-18C_Simulator/MCAD/ASSY, LOWER INSTRUMENT PANEL/ACRYLIC/LIGHT PLATE (.1875)/HDG-CRS Set Spacer Lightplate.DXF

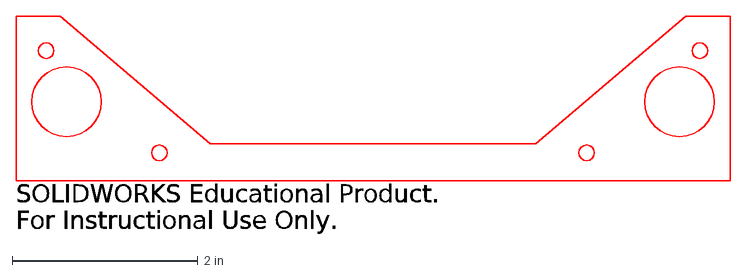
[picture p278: CAD file, 2023-01-02]
MCAD/ASSY, LOWER INSTRUMENT PANEL/ACRYLIC/LIGHT PLATE (.1875)/HDG-CRS Set Spacer Lightplate.DXF
SOLIDWORKS Educational Product.
For Instructional Use Only.
