Exprezz0/F-18C_Simulator/MCAD/ASSY, LOWER INSTRUMENT PANEL/MDF/.50in/Left Outboard Bulkhead.DXF

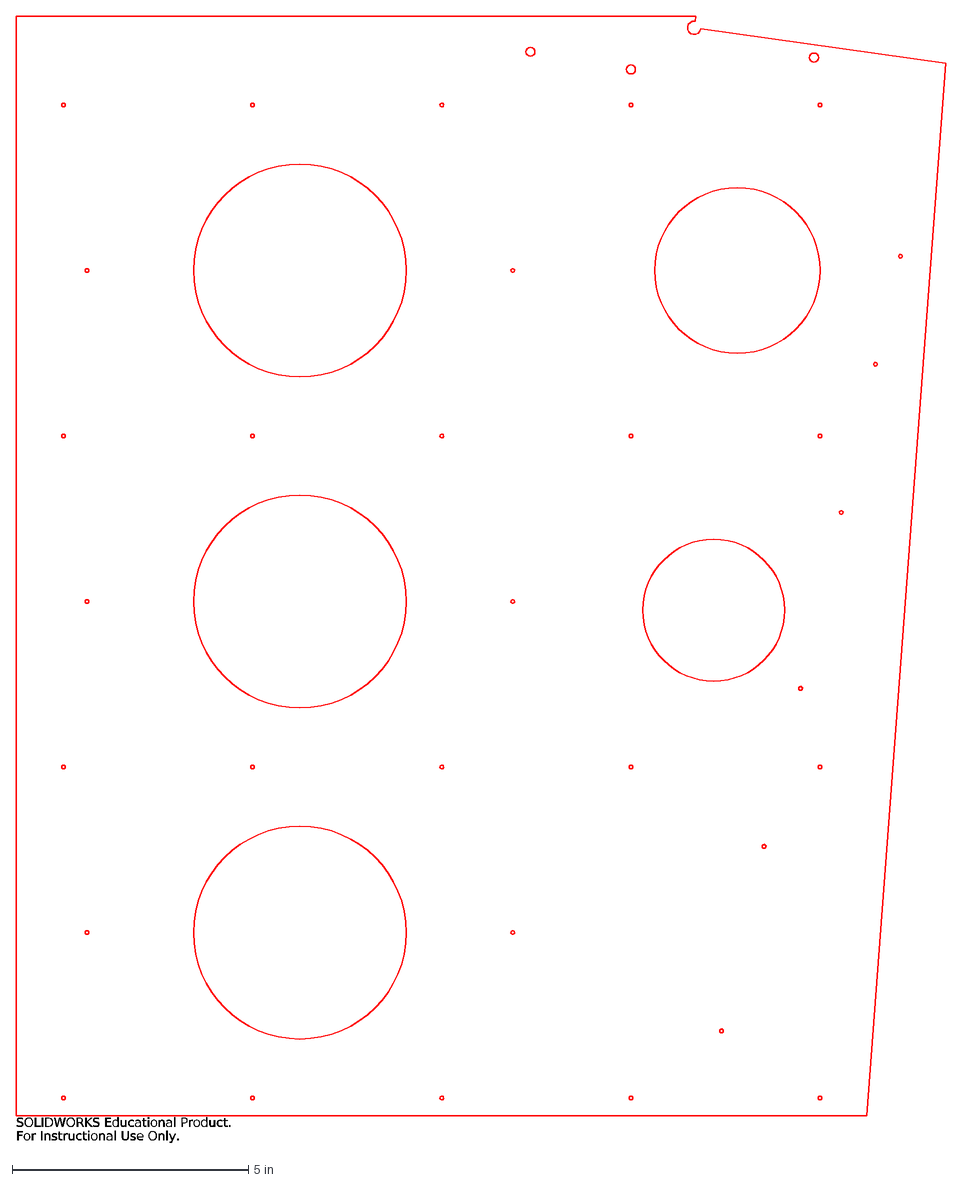
[picture p279: CAD file, 2023-01-02]
MCAD/ASSY, LOWER INSTRUMENT PANEL/MDF/.50in/Left Outboard Bulkhead.DXF
SOLIDWORKS Educational Product.
For Instructional Use Only.
