Exprezz0/F-18C_Simulator/MCAD/ASSY, LOWER INSTRUMENT PANEL/MDF/.75in/Upper Instrument Panel Mount.DXF

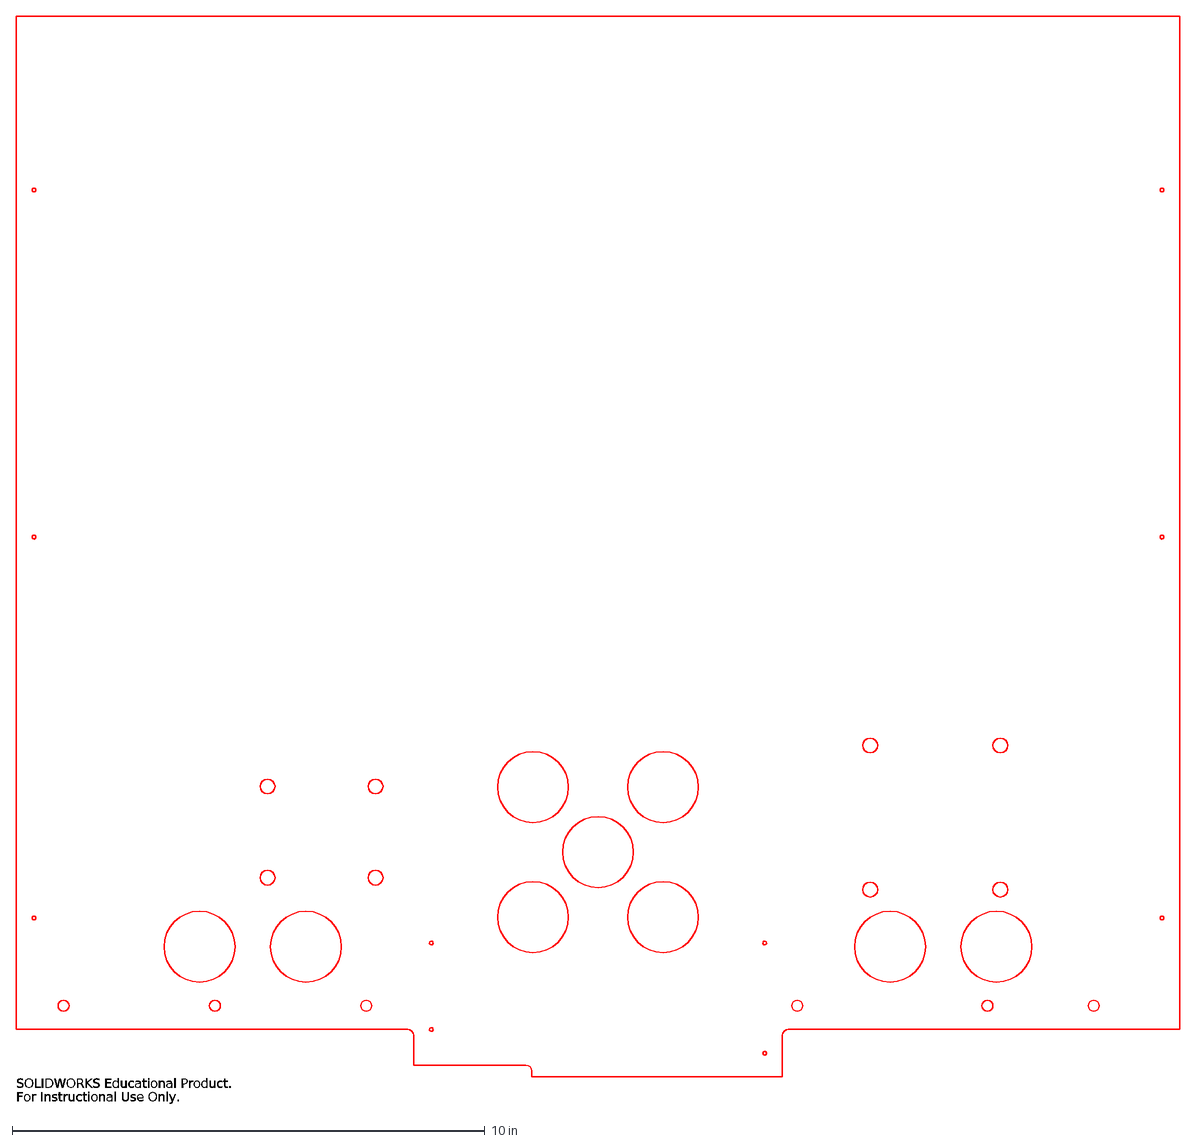
[picture p280: CAD file, 2023-01-02]
MCAD/ASSY, LOWER INSTRUMENT PANEL/MDF/.75in/Upper Instrument Panel Mount.DXF
SOLIDWORKS Educational Product.
For Instructional Use Only.
