Exprezz0/F-18C_Simulator/MCAD/ASSY, LOWER INSTRUMENT PANEL/PETG/Lower Right LIP AUX Support Bracket.STL

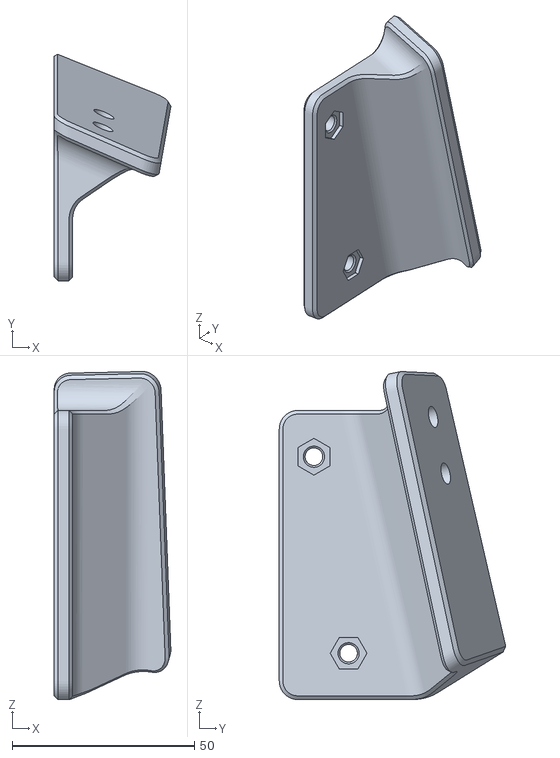
[picture p281: CAD file, 2023-01-02]
MCAD/ASSY, LOWER INSTRUMENT PANEL/PETG/Lower Right LIP AUX Support Bracket.STL
32.0 x 62.2 x 90.1
