Exprezz0/F-18C_Simulator/MCAD/ASSY, LOWER INSTRUMENT PANEL/RESIN/.55 SQ Indicator Actuator.STL

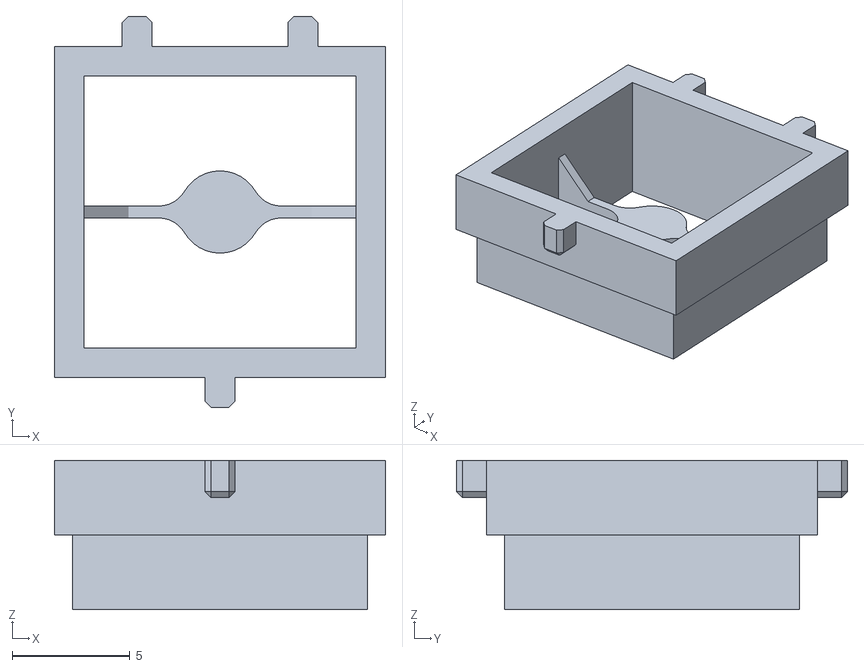
[picture p282: CAD file, 2023-01-02]
MCAD/ASSY, LOWER INSTRUMENT PANEL/RESIN/.55 SQ Indicator Actuator.STL
14.1 x 16.6 x 6.35
