Exprezz0/F-18C_Simulator/MCAD/ASSY, MAIN CENTER TUB/MDF/.75/OH3A1-106 - Center Tub FWD Bulkhead.stl

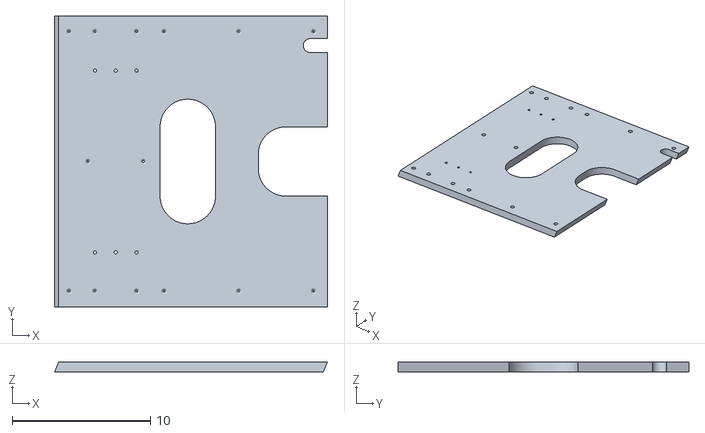
[picture p283: CAD file, 2023-01-09]
MCAD/ASSY, MAIN CENTER TUB/MDF/.75/OH3A1-106 - Center Tub FWD Bulkhead.stl
19.7 x 21.0 x 0.75
