Exprezz0/F-18C_Simulator/MCAD/ASSY, RIGHT CONSOLE/ALL KNOBS/SNSR PANEL, INS Blackground.stl

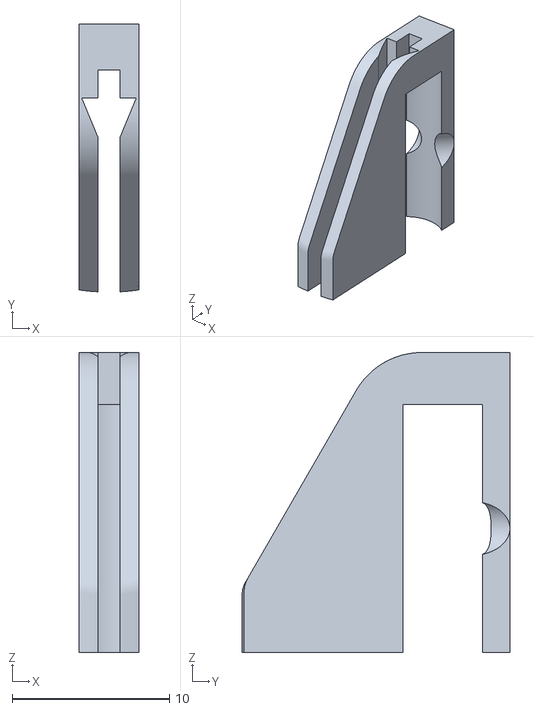
[picture p284: CAD file, 2023-01-13]
MCAD/ASSY, RIGHT CONSOLE/ALL KNOBS/SNSR PANEL, INS Blackground.stl
3.81 x 17.0 x 19.0
