Exprezz0/F-18C_Simulator/MCAD/ASSY, RIGHT CONSOLE/ALL PANEL PLATES/LIGHT PLATE (.1875)/BUNO Placard Lightplate.DXF

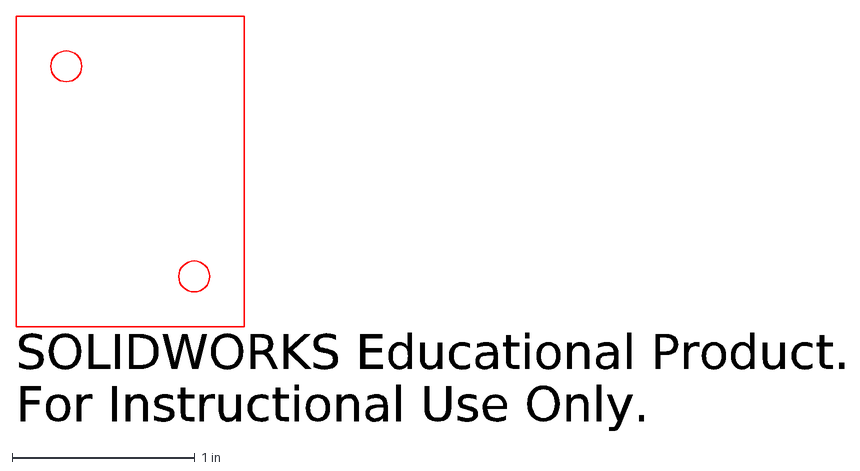
[picture p285: CAD file, 2023-01-02]
MCAD/ASSY, RIGHT CONSOLE/ALL PANEL PLATES/LIGHT PLATE (.1875)/BUNO Placard Lightplate.DXF
SOLIDWORKS Educational Product.
For Instructional Use Only.
