Exprezz0/F-18C_Simulator/MCAD/ASSY, RIGHT CONSOLE/ALL PANEL PLATES/Resin Printed - Gauge Faces/OH5A2A4-13 - RALT DIAL FACE.stl

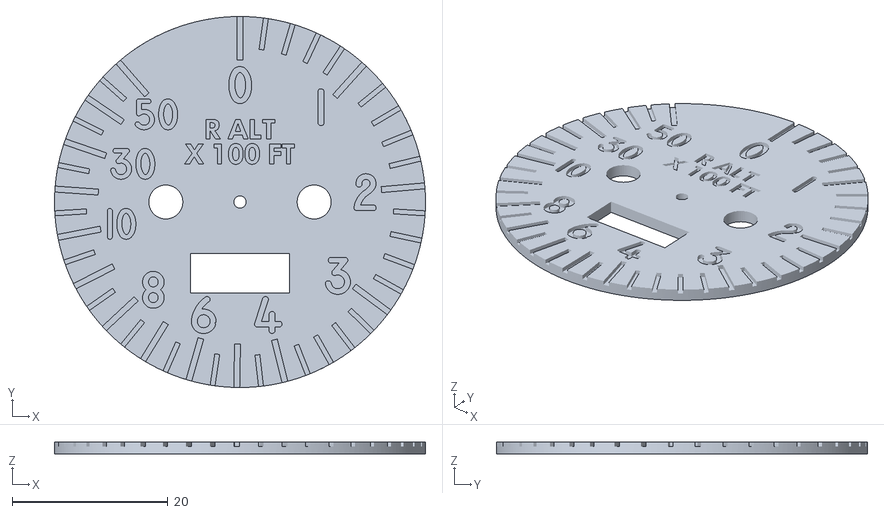
[picture p286: CAD file, 2023-01-04]
MCAD/ASSY, RIGHT CONSOLE/ALL PANEL PLATES/Resin Printed - Gauge Faces/OH5A2A4-13 - RALT DIAL FACE.stl
47.7 x 47.7 x 1.59
