Exprezz0/F-18C_Simulator/MCAD/ASSY, RIGHT CONSOLE/OH5A10A1-1 - ASSY, RIGHT CIRCUIT BREAKERS/PETG/OH5A10A1-12 - CIRCUIT BREAKER BRACKET.stl

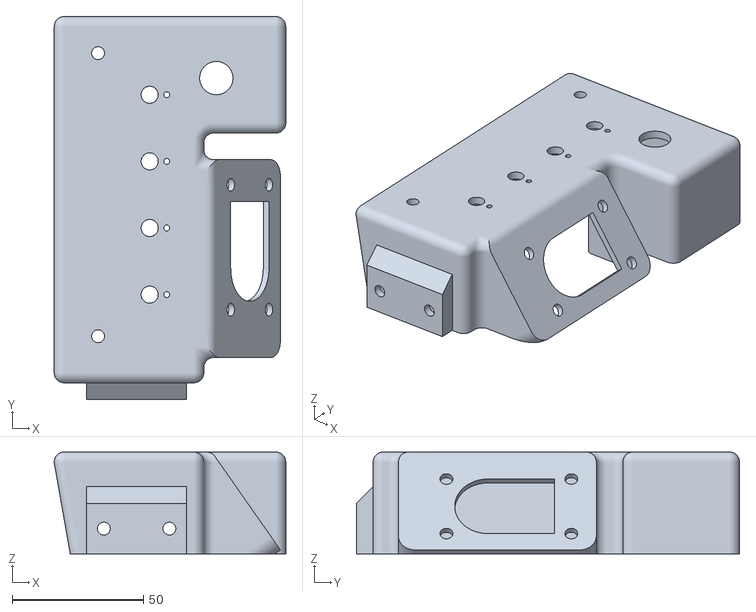
[picture p287: CAD file, 2023-01-02]
MCAD/ASSY, RIGHT CONSOLE/OH5A10A1-1 - ASSY, RIGHT CIRCUIT BREAKERS/PETG/OH5A10A1-12 - CIRCUIT BREAKER BRACKET.stl
88.3 x 146.0 x 38.9
