Exprezz0/F-18C_Simulator/MCAD/ASSY, RIGHT CONSOLE/OH5A1A1-1 - ASSY, RIGHT CONSOLE STRUCTURE/ACRYLIC/Right AUX Panel.STL

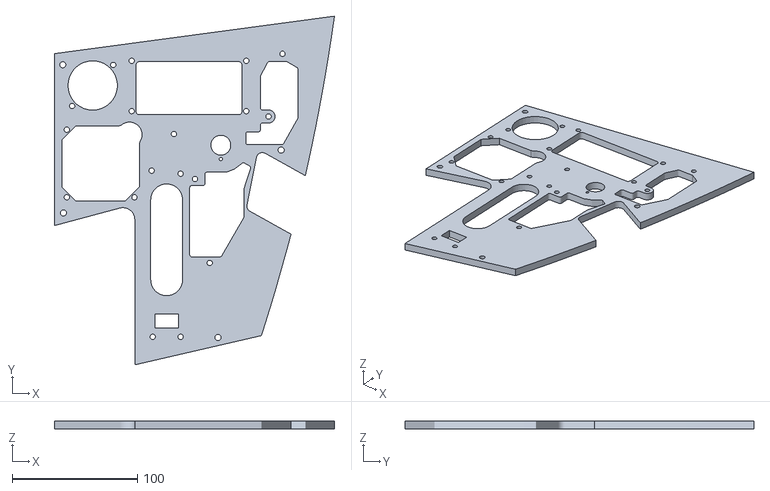
[picture p288: CAD file, 2023-01-02]
MCAD/ASSY, RIGHT CONSOLE/OH5A1A1-1 - ASSY, RIGHT CONSOLE STRUCTURE/ACRYLIC/Right AUX Panel.STL
223.4 x 278.2 x 6.35
