Exprezz0/F-18C_Simulator/MCAD/ASSY, RIGHT CONSOLE/OH5A1A1-1 - ASSY, RIGHT CONSOLE STRUCTURE/MDF/.25/Right Console Inboard Wall.DXF

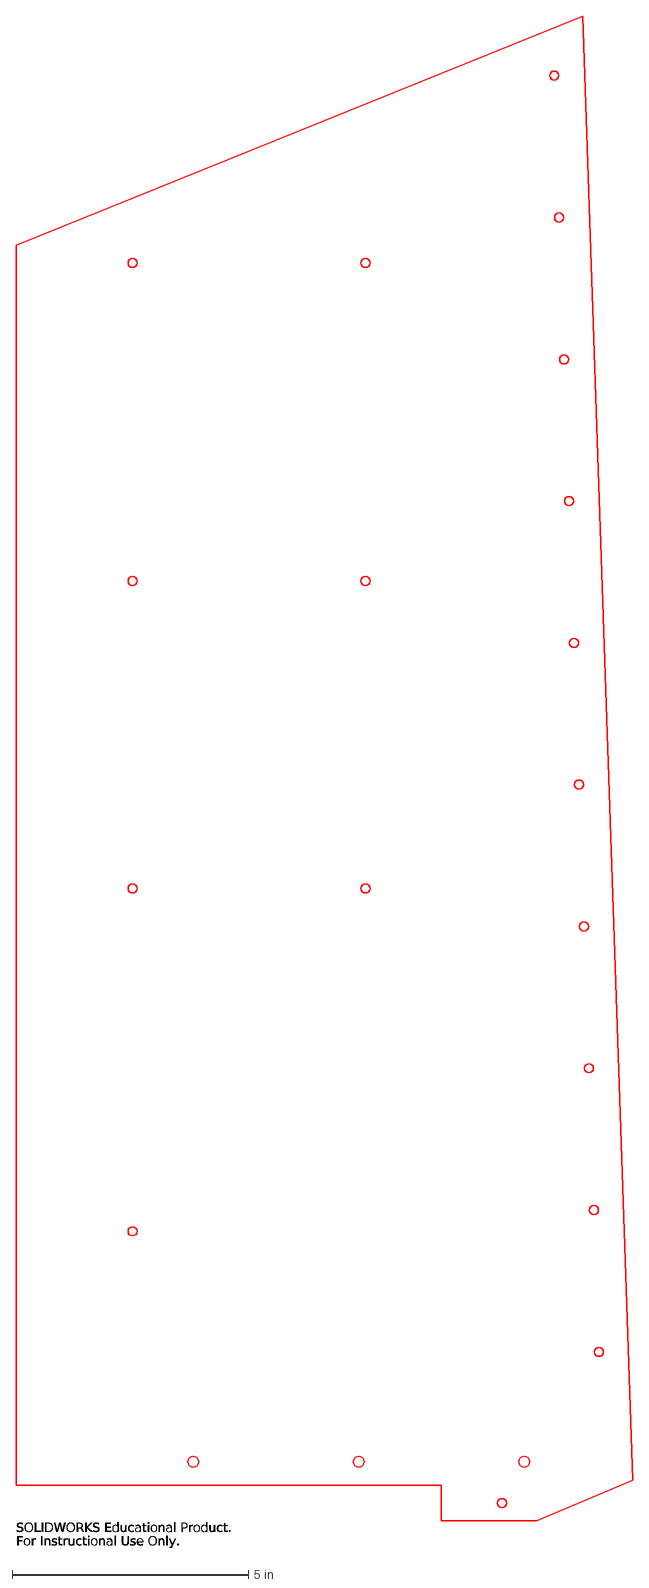
[picture p289: CAD file, 2023-01-02]
MCAD/ASSY, RIGHT CONSOLE/OH5A1A1-1 - ASSY, RIGHT CONSOLE STRUCTURE/MDF/.25/Right Console Inboard Wall.DXF
SOLIDWORKS Educational Product.
For Instructional Use Only.
