Exprezz0/F-18C_Simulator/MCAD/ASSY, RIGHT CONSOLE/OH5A1A1-1 - ASSY, RIGHT CONSOLE STRUCTURE/MDF/.75/Primary Rib G.DXF

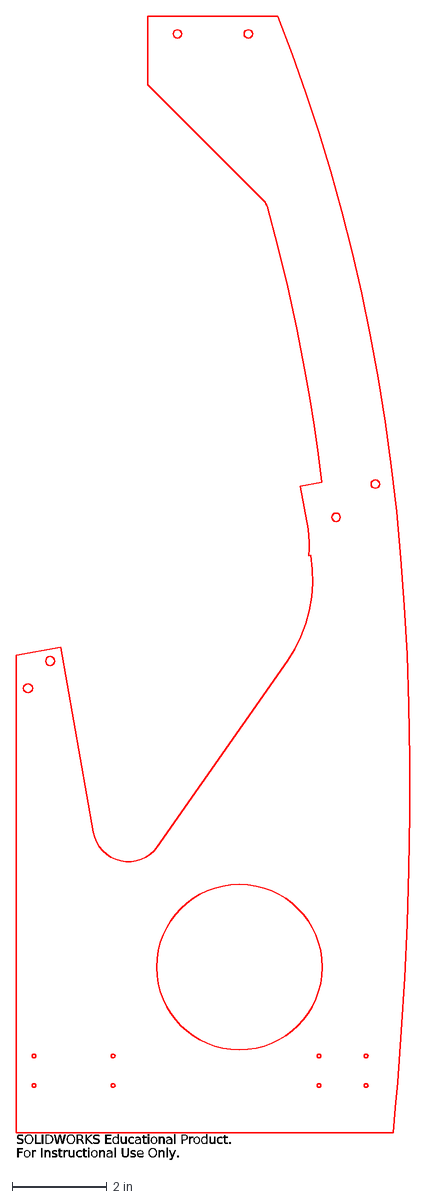
[picture p290: CAD file, 2023-01-02]
MCAD/ASSY, RIGHT CONSOLE/OH5A1A1-1 - ASSY, RIGHT CONSOLE STRUCTURE/MDF/.75/Primary Rib G.DXF
SOLIDWORKS Educational Product.
For Instructional Use Only.
