Exprezz0/F-18C_Simulator/MCAD/ASSY, RIGHT CONSOLE/OH5A1A1-1 - ASSY, RIGHT CONSOLE STRUCTURE/PETG/I-J Right Outboard Spacer.STL

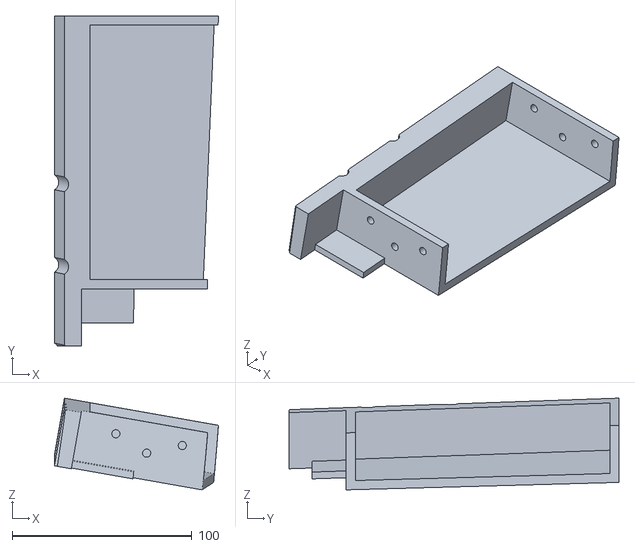
[picture p291: CAD file, 2023-01-02]
MCAD/ASSY, RIGHT CONSOLE/OH5A1A1-1 - ASSY, RIGHT CONSOLE STRUCTURE/PETG/I-J Right Outboard Spacer.STL
91.3 x 183.6 x 51.1
