Exprezz0/F-18C_Simulator/MCAD/ASSY, RIGHT CONSOLE/OH5A2A1-1 - ASSY, HOOK LEVER & INDICATOR/Hook Lever Chassis Body-Left.STL

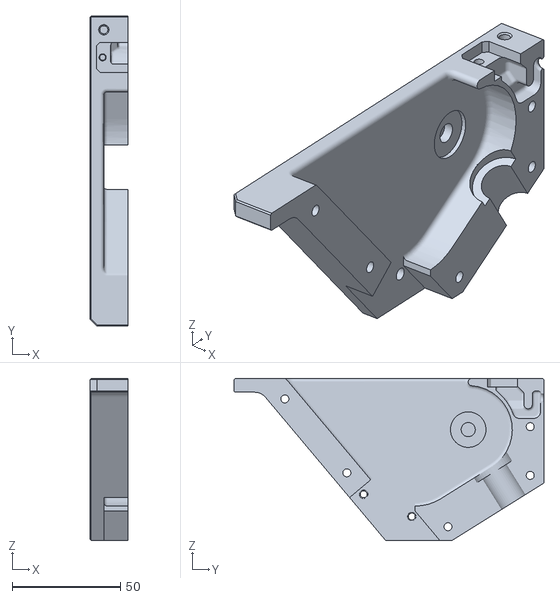
[picture p292: CAD file, 2023-01-02]
MCAD/ASSY, RIGHT CONSOLE/OH5A2A1-1 - ASSY, HOOK LEVER & INDICATOR/Hook Lever Chassis Body-Left.STL
17.5 x 142.9 x 74.7
