Exprezz0/F-18C_Simulator/MCAD/ASSY, RIGHT CONSOLE/OH5A2A2-1 - ASSY, WING FOLD HANDLE/Wing Fold Mechanism Rotary Detents.STL

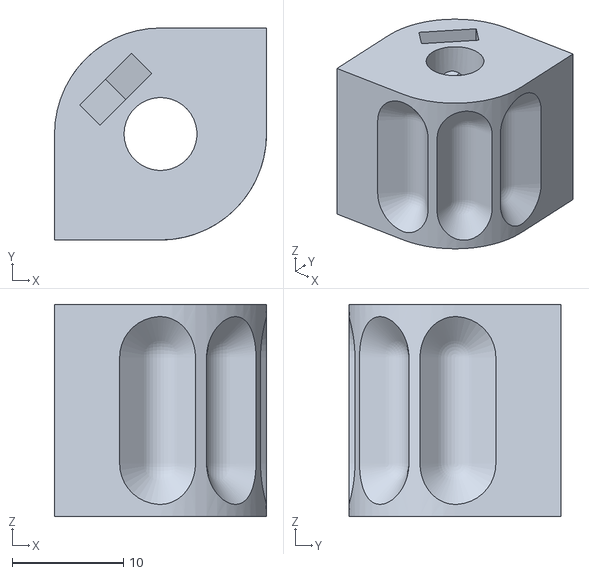
[picture p293: CAD file, 2023-01-02]
MCAD/ASSY, RIGHT CONSOLE/OH5A2A2-1 - ASSY, WING FOLD HANDLE/Wing Fold Mechanism Rotary Detents.STL
19.1 x 19.1 x 19.1
