Exprezz0/F-18C_Simulator/MCAD/ASSY, RIGHT CONSOLE/OH5A2A4-1 - ASSY, RADAR ALTIMETER GAUGE/PETG/Radar Altimeter Bezel.STL

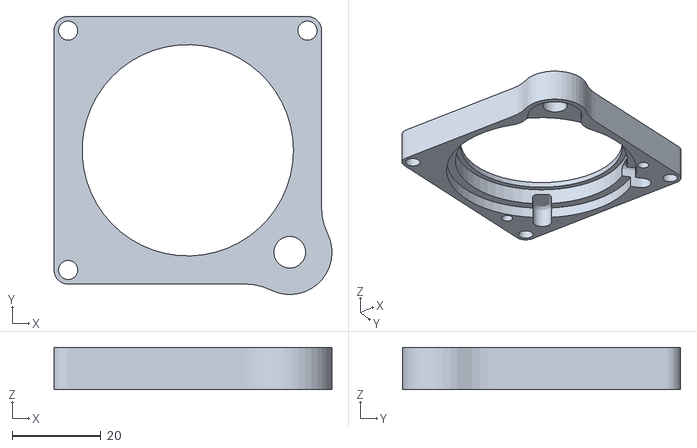
[picture p294: CAD file, 2023-01-02]
MCAD/ASSY, RIGHT CONSOLE/OH5A2A4-1 - ASSY, RADAR ALTIMETER GAUGE/PETG/Radar Altimeter Bezel.STL
62.7 x 62.7 x 9.53
