Exprezz0/F-18C_Simulator/MCAD/ASSY, RIGHT CONSOLE/OH5A4A1-100 - BATTERY VOLTAGE INDICATOR/PETG or RESIN/OH5A4A1-106 - BATT VOLT NEEDLE #2.stl

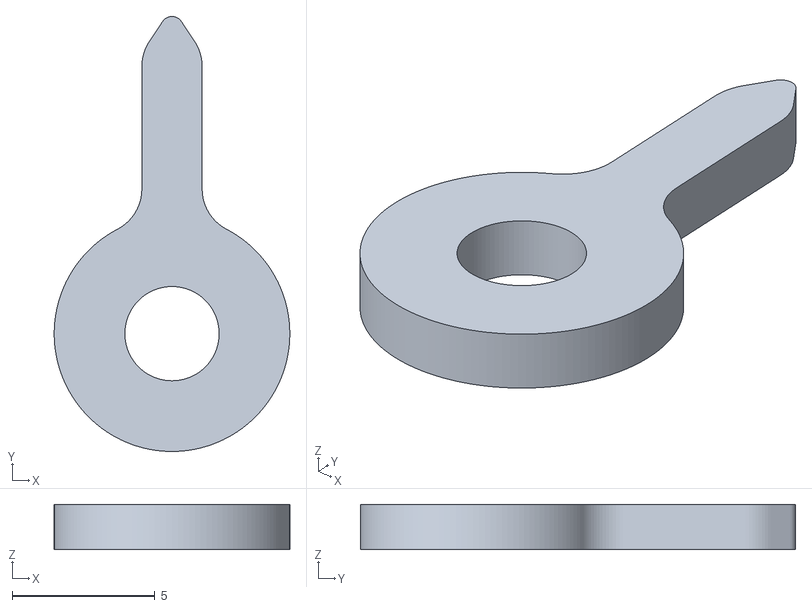
[picture p295: CAD file, 2023-04-02]
MCAD/ASSY, RIGHT CONSOLE/OH5A4A1-100 - BATTERY VOLTAGE INDICATOR/PETG or RESIN/OH5A4A1-106 - BATT VOLT NEEDLE #2.stl
8.25 x 15.2 x 1.59
