Exprezz0/F-18C_Simulator/MCAD/ASSY, RIGHT CONSOLE/OH5A5A1-100 - ASSY, DUAL CONCENTRIC SHAFT POTENTIOMETER/OH5A5A1-106 - UPPER MOUNT PLATE.stl

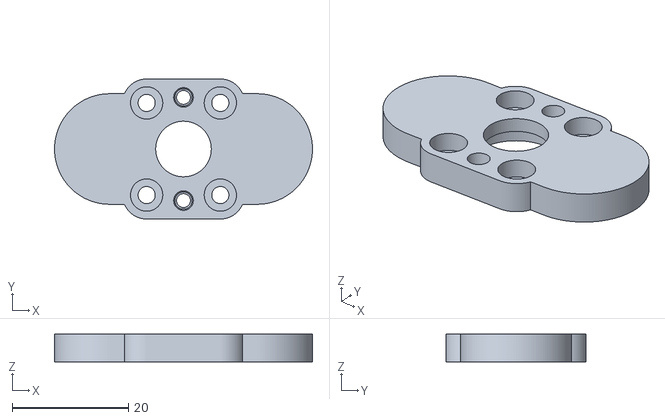
[picture p296: CAD file, 2023-01-03]
MCAD/ASSY, RIGHT CONSOLE/OH5A5A1-100 - ASSY, DUAL CONCENTRIC SHAFT POTENTIOMETER/OH5A5A1-106 - UPPER MOUNT PLATE.stl
44.5 x 24.1 x 4.76
