Exprezz0/F-18C_Simulator/MCAD/ASSY, RIGHT CONSOLE/OH5A5A1-200 - ASSY, BLEED AIR KNOB MECHANISM/OH5A5A1-208 - PULL SHAFT COUPLER.stl

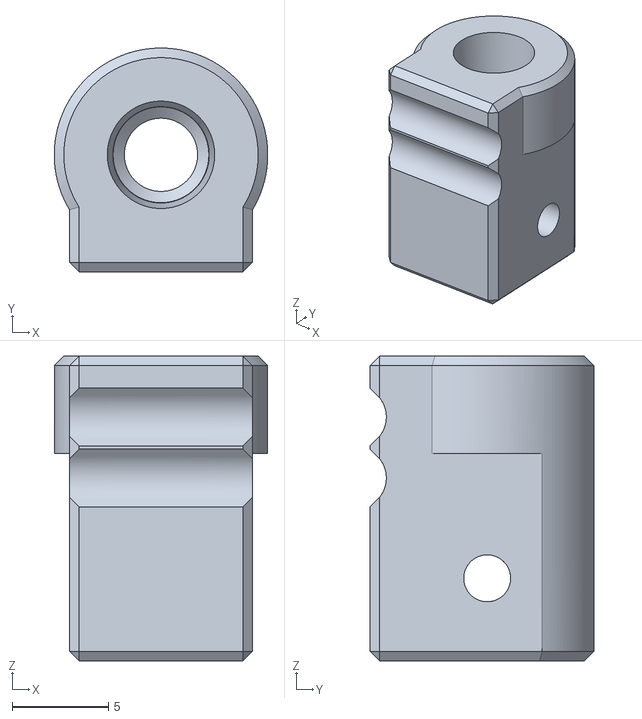
[picture p297: CAD file, 2023-04-25]
MCAD/ASSY, RIGHT CONSOLE/OH5A5A1-200 - ASSY, BLEED AIR KNOB MECHANISM/OH5A5A1-208 - PULL SHAFT COUPLER.stl
11.1 x 11.7 x 15.9
