Exprezz0/F-18C_Simulator/MCAD/ASSY, RIGHT CONSOLE/RANDOM COTS PARTS/COTS - OH5A5A1-100/OH5A5A1-104 - SPACER BUSHING, .125 ID, .25 OD.stl

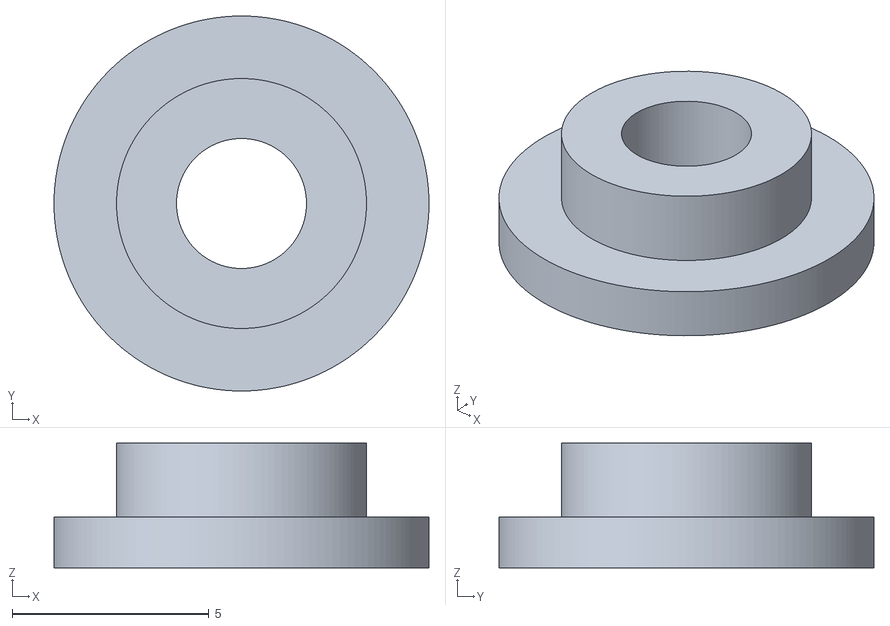
[picture p298: CAD file, 2023-01-03]
MCAD/ASSY, RIGHT CONSOLE/RANDOM COTS PARTS/COTS - OH5A5A1-100/OH5A5A1-104 - SPACER BUSHING, .125 ID, .25 OD.stl
9.52 x 9.52 x 3.17
