Exprezz0/F-18C_Simulator/MCAD/ASSY, RIGHT CONSOLE/Switch Bats/OHC0001-20 - BAT, CONICAL, FOR NKK SxAL SWITCH v1.stl

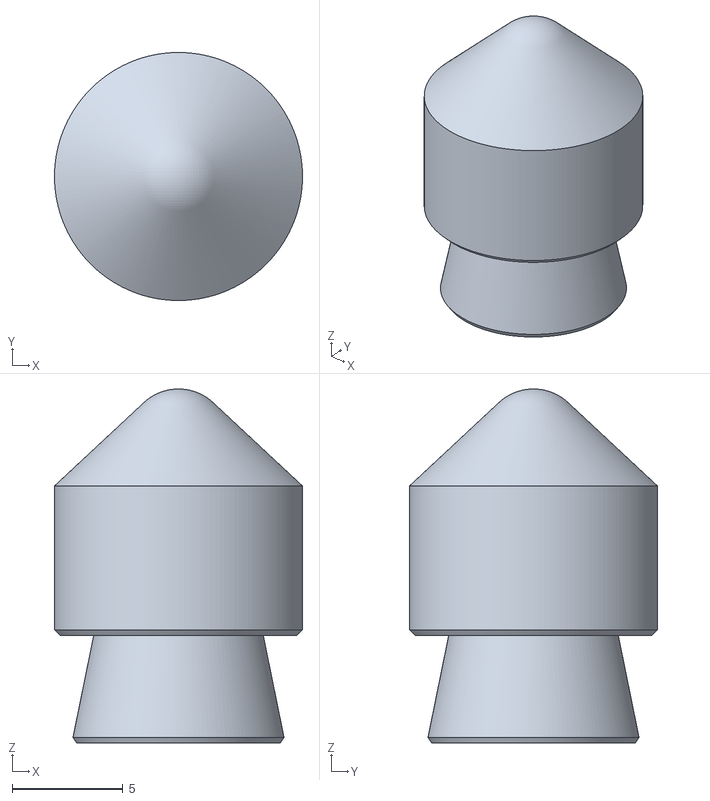
[picture p299: CAD file, 2023-01-02]
MCAD/ASSY, RIGHT CONSOLE/Switch Bats/OHC0001-20 - BAT, CONICAL, FOR NKK SxAL SWITCH v1.stl
11.2 x 11.2 x 15.9
