Exprezz0/F-18C_Simulator/MCAD/ASSY, UPPER INSTRUMENT PANEL/ALL PANEL PLATES/BACKLIGHT PLATE (.125)/UFC Backplate.DXF

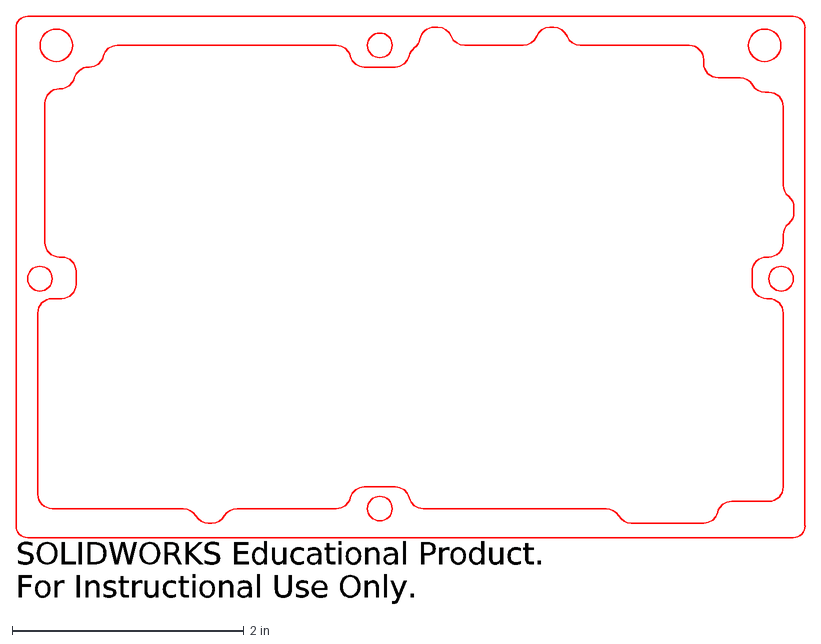
[picture p300: CAD file, 2023-01-02]
MCAD/ASSY, UPPER INSTRUMENT PANEL/ALL PANEL PLATES/BACKLIGHT PLATE (.125)/UFC Backplate.DXF
SOLIDWORKS Educational Product.
For Instructional Use Only.
