Exprezz0/F-18C_Simulator/MCAD/ASSY, UPPER INSTRUMENT PANEL/ALL PANEL PLATES/LEGEND PLATE (.0625)/Master Arm Legend Plate.DXF

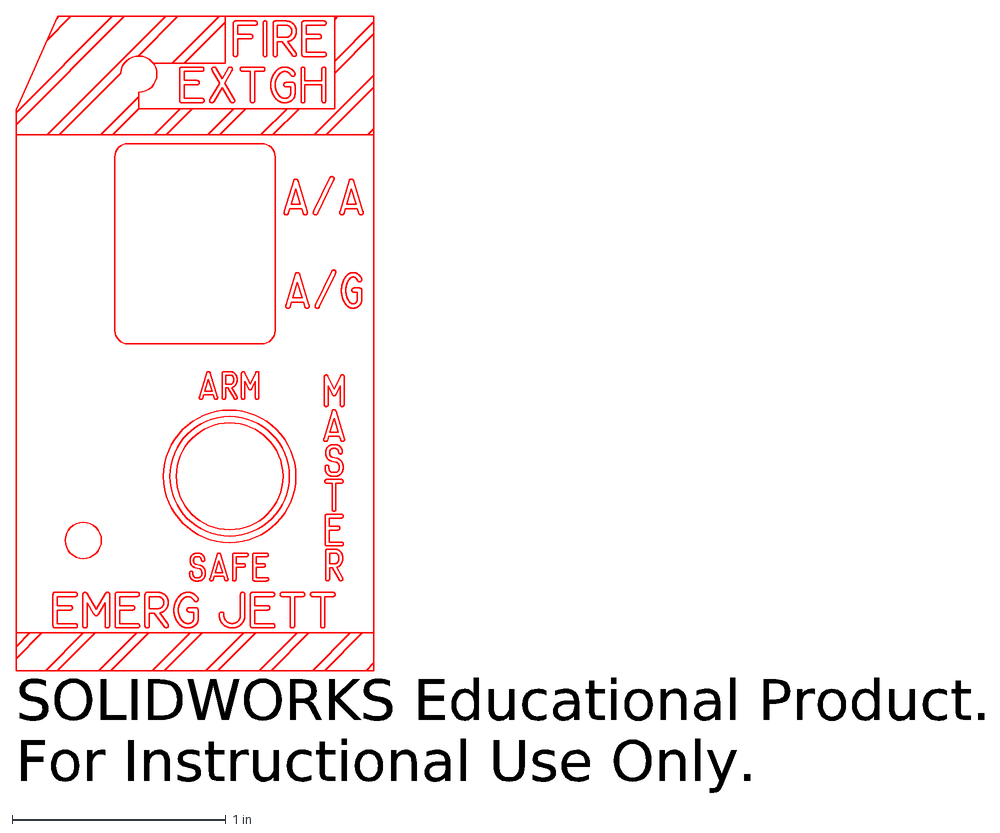
[picture p301: CAD file, 2023-01-02]
MCAD/ASSY, UPPER INSTRUMENT PANEL/ALL PANEL PLATES/LEGEND PLATE (.0625)/Master Arm Legend Plate.DXF
SOLIDWORKS Educational Product.
For Instructional Use Only.
