Exprezz0/F-18C_Simulator/MCAD/ASSY, UPPER INSTRUMENT PANEL/ALL PANEL PLATES/LEGEND PLATE (.0625)/no words/Master Arm Legend Plate_no words.DXF

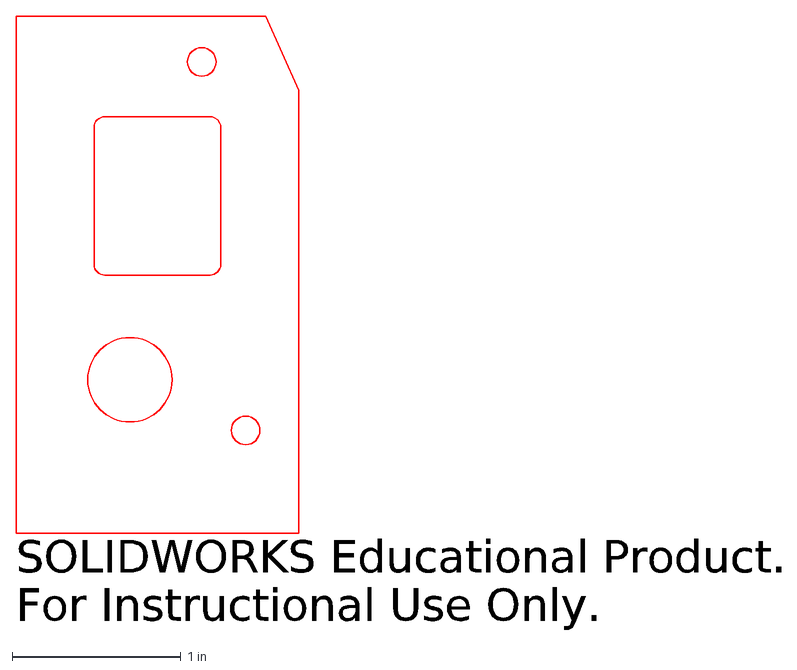
[picture p302: CAD file, 2023-01-02]
MCAD/ASSY, UPPER INSTRUMENT PANEL/ALL PANEL PLATES/LEGEND PLATE (.0625)/no words/Master Arm Legend Plate_no words.DXF
SOLIDWORKS Educational Product.
For Instructional Use Only.
