Exprezz0/F-18C_Simulator/MCAD/ASSY, UPPER INSTRUMENT PANEL/ALL PANEL PLATES/LIGHT PLATE (.1875)/UFC Inner Spacer Plate.DXF

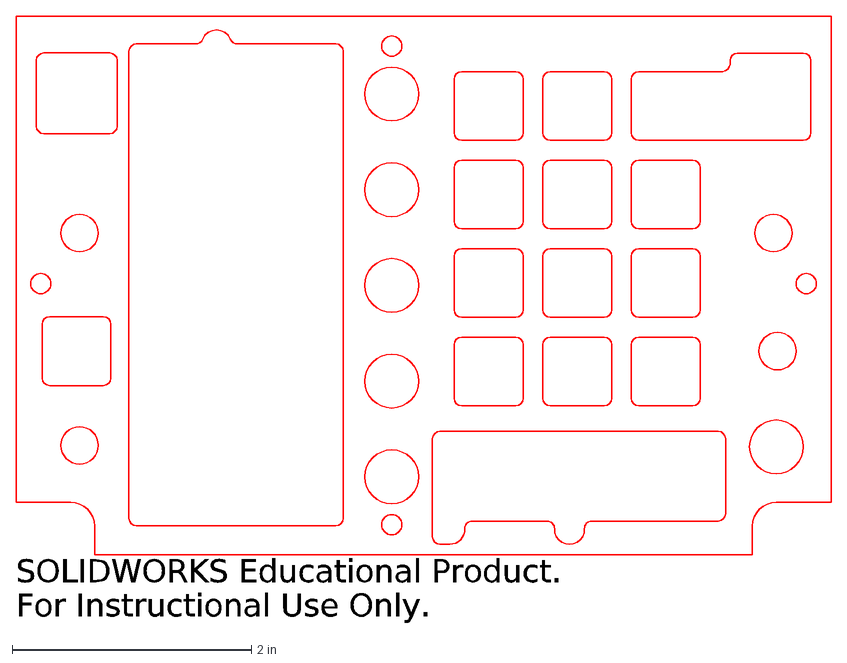
[picture p303: CAD file, 2023-01-02]
MCAD/ASSY, UPPER INSTRUMENT PANEL/ALL PANEL PLATES/LIGHT PLATE (.1875)/UFC Inner Spacer Plate.DXF
SOLIDWORKS Educational Product.
For Instructional Use Only.
