Exprezz0/F-18C_Simulator/MCAD/ASSY, UPPER INSTRUMENT PANEL/MDF/.25/Upper Instrument Panel Face.DXF

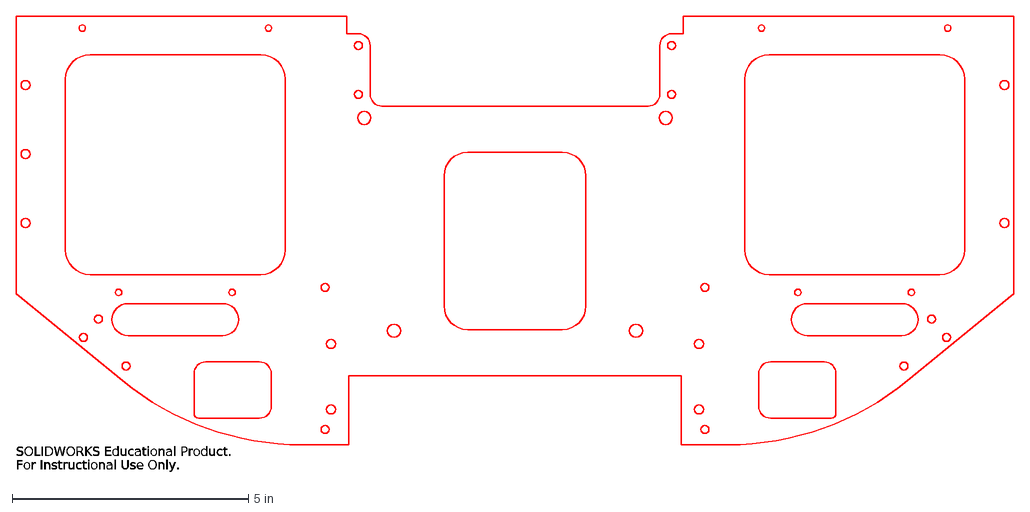
[picture p304: CAD file, 2023-01-02]
MCAD/ASSY, UPPER INSTRUMENT PANEL/MDF/.25/Upper Instrument Panel Face.DXF
SOLIDWORKS Educational Product.
For Instructional Use Only.
