Exprezz0/F-18C_Simulator/MCAD/ASSY, UPPER INSTRUMENT PANEL/MDF/.50/UIP Left Outboard Longeron.DXF

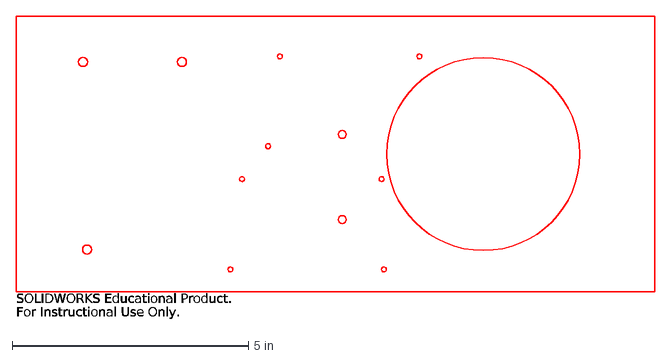
[picture p305: CAD file, 2023-01-02]
MCAD/ASSY, UPPER INSTRUMENT PANEL/MDF/.50/UIP Left Outboard Longeron.DXF
SOLIDWORKS Educational Product.
For Instructional Use Only.
