Exprezz0/F-18C_Simulator/MCAD/ASSY, UPPER INSTRUMENT PANEL/MDF/.75/UIP Right Inboard Longeron.DXF

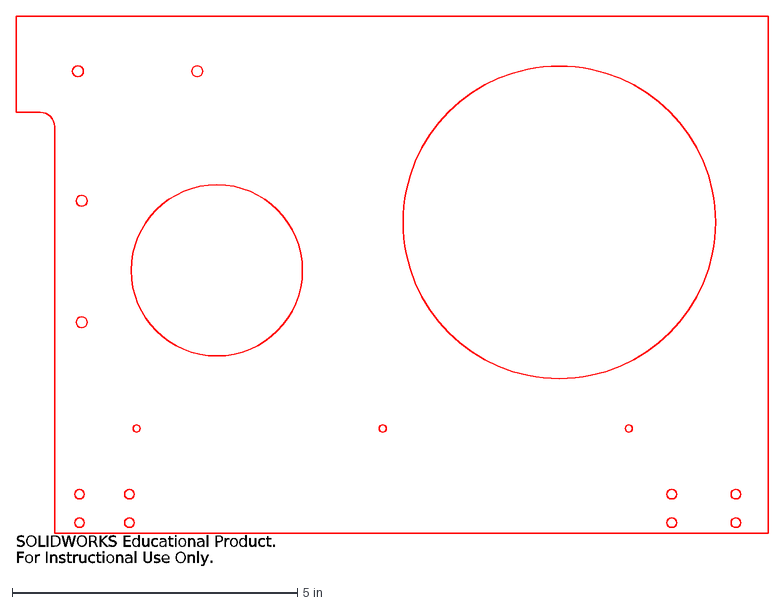
[picture p306: CAD file, 2023-01-02]
MCAD/ASSY, UPPER INSTRUMENT PANEL/MDF/.75/UIP Right Inboard Longeron.DXF
SOLIDWORKS Educational Product.
For Instructional Use Only.
