Exprezz0/F-18C_Simulator/MCAD/ASSY, UPPER INSTRUMENT PANEL/PETG/UFC Panel Support Structure.STL

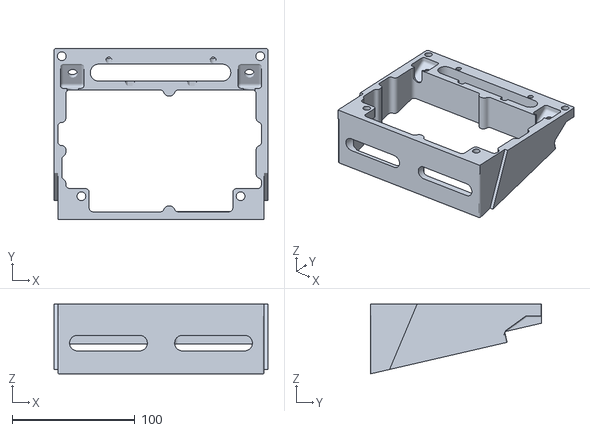
[picture p307: CAD file, 2023-01-02]
MCAD/ASSY, UPPER INSTRUMENT PANEL/PETG/UFC Panel Support Structure.STL
174.6 x 139.7 x 56.8
