Exprezz0/F-18C_Simulator/ECAD/PCBs/ABSIS/ABSIS_Hall Sensor/MCAD/ABSIS_Hall Sensor.step

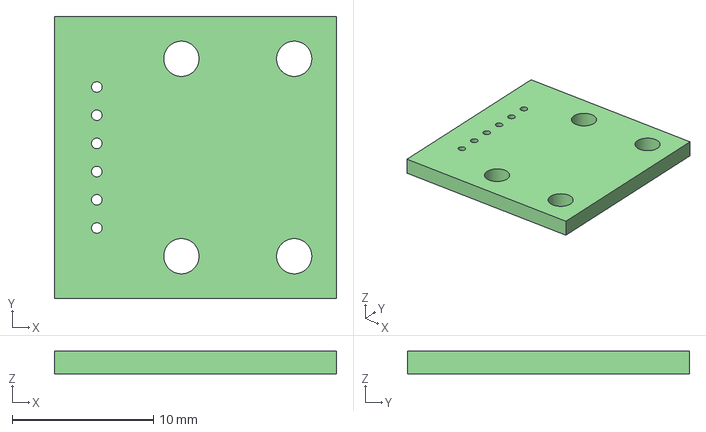
[picture p308: CAD file, 2023-01-10]
ECAD/PCBs/ABSIS/ABSIS_Hall Sensor/MCAD/ABSIS_Hall Sensor.step
20.0 x 20.0 x 1.60 mm
