Exprezz0/F-18C_Simulator/ECAD/PCBs/ABSIS/ABSIS_Pit Management System/MCAD/ABSIS_Pit Management System.step

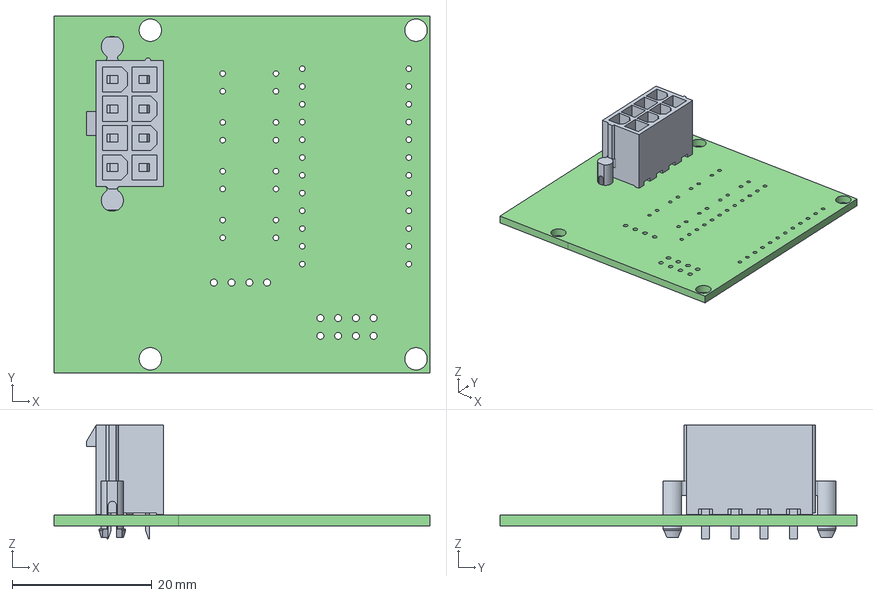
[picture p309: CAD file, 2023-01-10]
ECAD/PCBs/ABSIS/ABSIS_Pit Management System/MCAD/ABSIS_Pit Management System.step
53.8 x 51.0 x 16.3 mm
ABSIS_Pit Management System PCB
