Exprezz0/F-18C_Simulator/ECAD/PCBs/Backlight PCBs/Backlighting_Type A/FIRE TEST PANEL/Assets/FIRE TEST PANEL_TOP-ISO.png

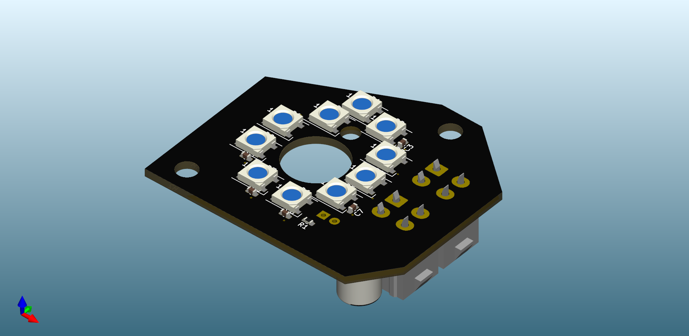
ECAD/PCBs/Backlight PCBs/Backlighting_Type A/FIRE TEST PANEL/Assets/FIRE TEST PANEL_TOP-ISO.png
