Exprezz0/F-18C_Simulator/ECAD/PCBs/ABSIS/ABSIS_Mega/ABSIS_Mega.kicad_pcb

## KiCad design ECAD/PCBs/ABSIS/ABSIS_Mega/ABSIS_Mega.kicad_pcb (2023-02-10)

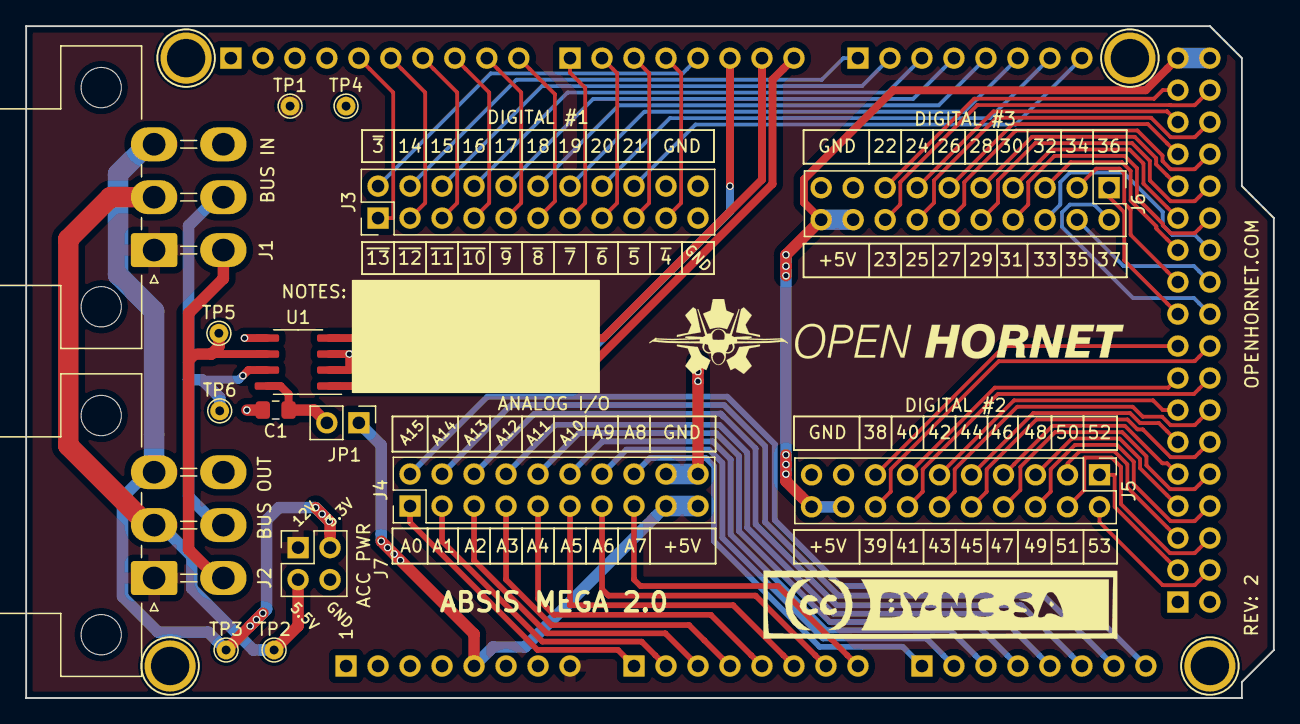
[picture p327: board ABSIS_Mega.kicad_pcb from above]

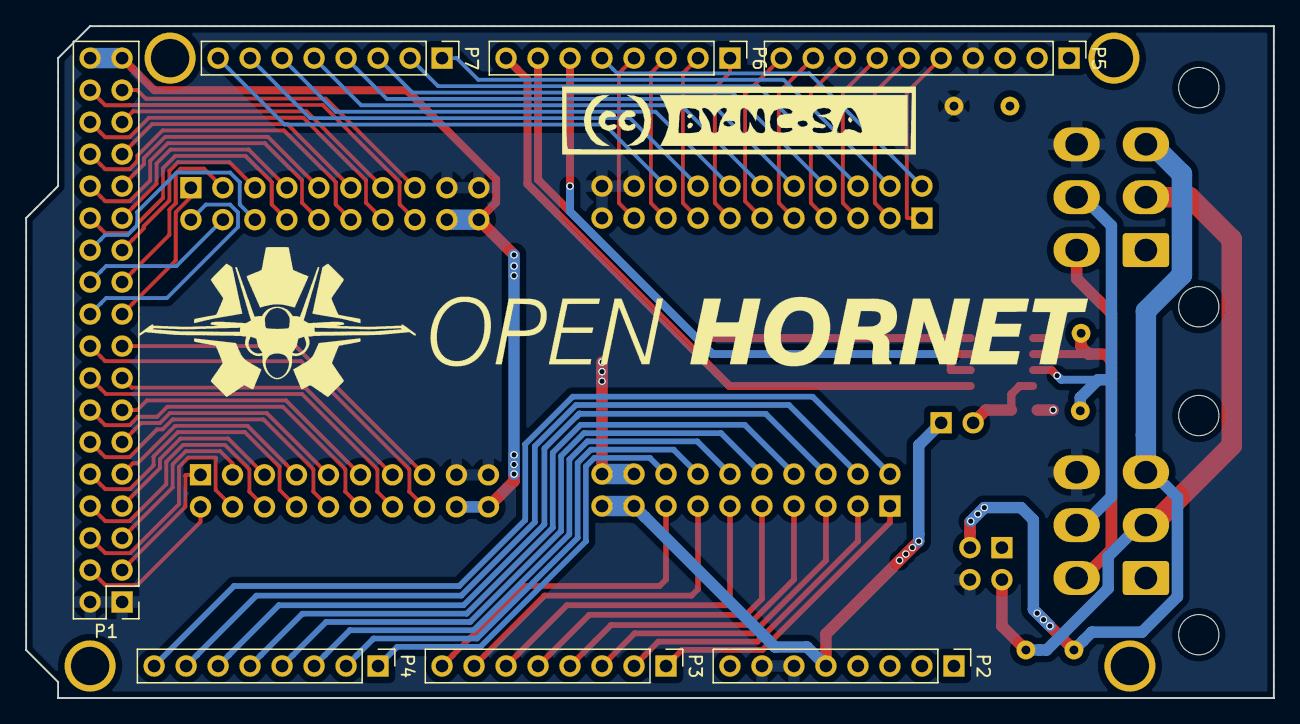
[picture p328: board ABSIS_Mega.kicad_pcb from below]

Board: 2 copper layers, 99.1 x 53.3 mm, 27 parts (7 on the bottom side), 79 nets.

Parts:
C1: 0.1uF; C_0805_2012Metric_Pad1.15x1.40mm_HandSolder
J1: BUS IN; Molex_Mini-Fit_Jr_5569-06A1_2x03_P4.20mm_Horizontal
J2: BUS OUT; Molex_Mini-Fit_Jr_5569-06A1_2x03_P4.20mm_Horizontal
J3: DIGITAL #1; PinHeader_2x11_P2.54mm_Vertical
J4: ANALOG I/O; PinHeader_2x10_P2.54mm_Vertical
J5: DIGITAL #2; PinHeader_2x10_P2.54mm_Vertical
J6: DIGITAL #3; PinHeader_2x10_P2.54mm_Vertical
J7: ACC PWR; PinHeader_2x02_P2.54mm_Vertical
JP1: BUS ENABLE; PinHeader_1x02_P2.54mm_Vertical
MK1, MK3, MK4, MK6: MH; Arduino_1pin
P1: Digital; PinHeader_2x18_P2.54mm_Vertical
P2: Power; PinHeader_1x08_P2.54mm_Vertical
P3, P4: Analog; PinHeader_1x08_P2.54mm_Vertical
P5: PWM; PinHeader_1x10_P2.54mm_Vertical
P6: PWM; PinHeader_1x08_P2.54mm_Vertical
P7: Communication; PinHeader_1x08_P2.54mm_Vertical
TP1: TP-12; TestPoint_THTPad_D1.5mm_Drill0.7mm
TP2: TP-5V; TestPoint_THTPad_D1.5mm_Drill0.7mm
TP3: TP-3.3V; TestPoint_THTPad_D1.5mm_Drill0.7mm
TP4: TP-GND; TestPoint_THTPad_D1.5mm_Drill0.7mm
TP5: TP-A; TestPoint_THTPad_D1.5mm_Drill0.7mm
TP6: TP-B; TestPoint_THTPad_D1.5mm_Drill0.7mm
U1: MAX487EESA+T; SOIC-8_3.9x4.9mm_P1.27mm

Connections:
+5V: J4.17, J4.19, JP1.1, P2.5
+5VD: J5.18, J5.20, J6.18, J6.20, P1.35, P1.36
/0(Rx0): P6.8, U1.1
/1(Tx0): P6.7, U1.4
/2(**): P6.6, U1.2, U1.3
/3(**): J3.2, P6.5
/4(**): J3.19, P6.4
/5(**): J3.17, P6.3
/6(**): J3.15, P6.2
/7(**): J3.13, P6.1
/8(**): J3.11, P5.10
/9(**): J3.9, P5.9
/10(**): J3.7, P5.8
/11(**): J3.5, P5.7
/12(**): J3.3, P5.6
/13(**): J3.1, P5.5
/14(Tx3): J3.4, P7.1
/15(Rx3): J3.6, P7.2
/16(Tx2): J3.8, P7.3
/17(Rx2): J3.10, P7.4
/18(Tx1): J3.12, P7.5
/19(Rx1): J3.14, P7.6
/20(SDA): J3.16, P7.7
/21(SCL): J3.18, P7.8
/22: J6.15, P1.33
/23: J6.16, P1.34
/24: J6.13, P1.31
/25: J6.14, P1.32
/26: J6.11, P1.29
/27: J6.12, P1.30
/28: J6.9, P1.27
/29: J6.10, P1.28
/30: J6.7, P1.25
/31: J6.8, P1.26
/32: J6.5, P1.23
/33: J6.6, P1.24
/34: J6.3, P1.21
/35: J6.4, P1.22
/36: J6.1, P1.19
/37: J6.2, P1.20
/38: J5.15, P1.17
/39: J5.16, P1.18
/40: J5.13, P1.15
/41: J5.14, P1.16
/42: J5.11, P1.13
/43: J5.12, P1.14
/44: J5.9, P1.11
/45: J5.10, P1.12
/46: J5.7, P1.9
/47: J5.8, P1.10
/48: J5.5, P1.7
/49: J5.6, P1.8
/50(MISO): J5.3, P1.5
/51(MOSI): J5.4, P1.6
/52(SCK): J5.1, P1.3
/53(SS): J5.2, P1.4
/+3.3V_SUPPLY: J1.3, J2.3, J7.2, TP3.1
/+5V_SUPPLY: J1.2, J2.2, J7.3, TP2.1
/+12V_SUPPLY: J1.1, J2.1, J7.1, P2.8, TP1.1
/A0: J4.1, P3.1
/A1: J4.3, P3.2
/A2: J4.5, P3.3
/A3: J4.7, P3.4
/A4: J4.9, P3.5
/A5: J4.11, P3.6
/A6: J4.13, P3.7
/A7: J4.15, P3.8
/A8: J4.16, P4.1
/A9: J4.14, P4.2
/A10: J4.12, P4.3
/A11: J4.10, P4.4
/A12: J4.8, P4.5
/A13: J4.6, P4.6
/A14: J4.4, P4.7
/A15: J4.2, P4.8
/BUS-A: J1.4, J2.4, TP5.1, U1.6
/BUS-B: J1.5, J2.5, TP6.1, U1.7
/BUS-ENABLE: C1.1, JP1.2, U1.8
GND: C1.2, J1.6, J2.6, J3.20, J3.21, J3.22, J4.18, J4.20, J5.17, J5.19, J6.17, J6.19, J7.4, P1.1, P1.2, P2.6, P2.7, P5.4, TP4.1, U1.5
