Exprezz0/F-18C_Simulator/ECAD/PCBs/Functional PCBs/CONTROLLER_Radar Altimeter/CONTROLLER_Radar Altimeter.kicad_pcb

## KiCad design ECAD/PCBs/Functional PCBs/CONTROLLER_Radar Altimeter/CONTROLLER_Radar Altimeter.kicad_pcb (2023-02-10)

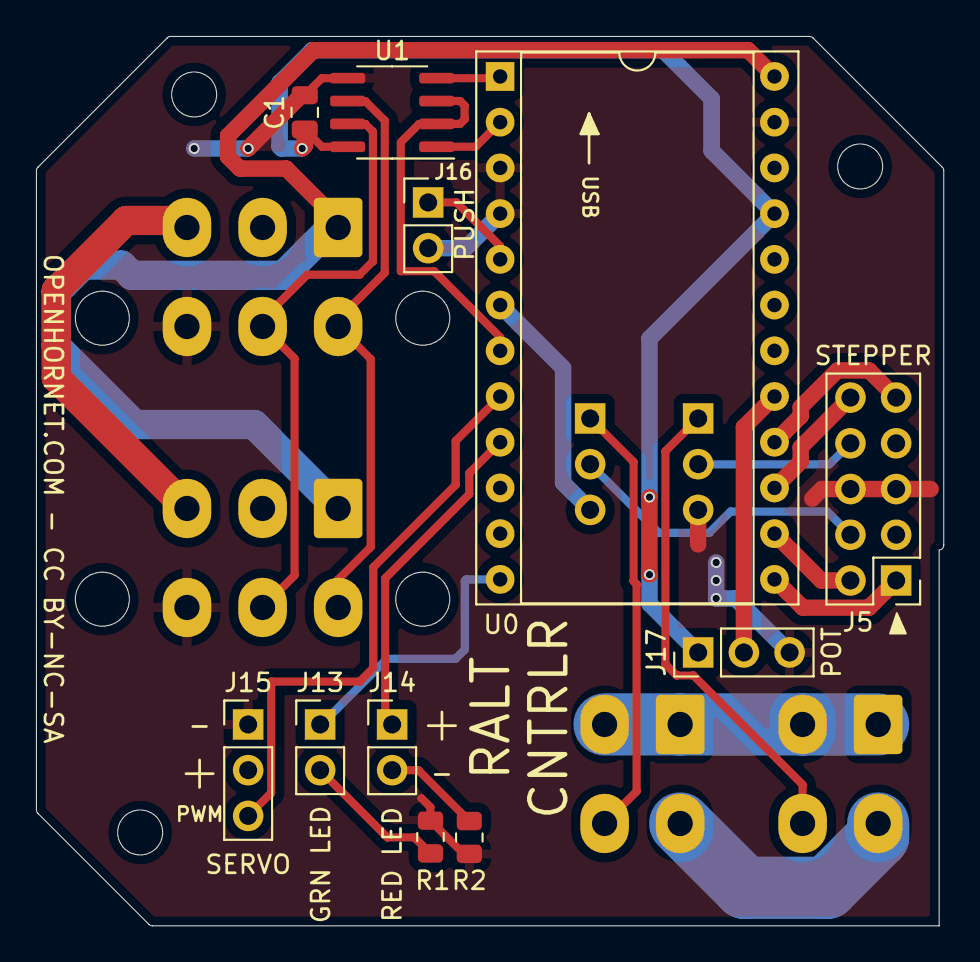
[picture p329: board CONTROLLER_Radar Altimeter.kicad_pcb from above]

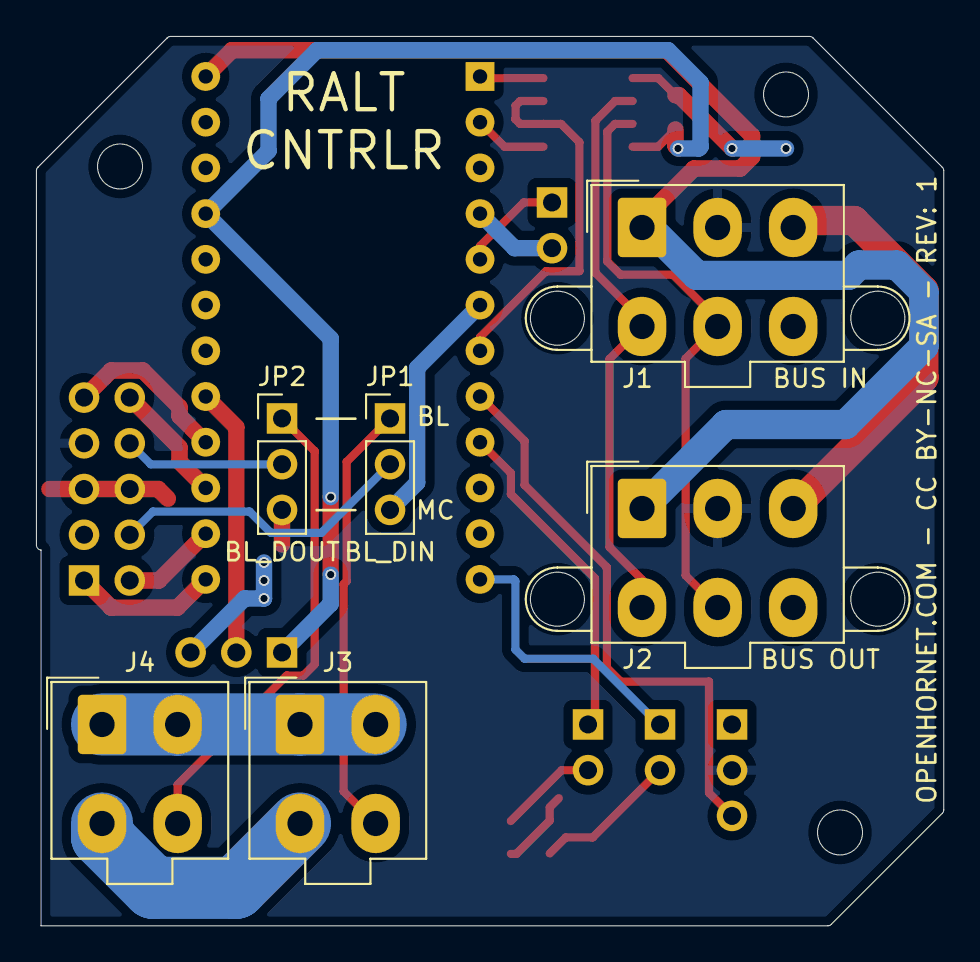
[picture p330: board CONTROLLER_Radar Altimeter.kicad_pcb from below]

Board: 2 copper layers, 50.4 x 49.4 mm, 20 parts (6 on the bottom side), 28 nets.

Parts:
C1: 0.1uF; C_0805_2012Metric
J1: BUS IN; Molex_Mini-Fit_Jr_5566-06A2_2x03_P4.20mm_Vertical
J2: BUS OUT; Molex_Mini-Fit_Jr_5566-06A2_2x03_P4.20mm_Vertical
J3: BL IN; Molex_Mini-Fit_Jr_5566-04A_2x02_P4.20mm_Vertical
J4: BL OUT; Molex_Mini-Fit_Jr_5566-04A_2x02_P4.20mm_Vertical
J5: STEPPER; PinHeader_2x05_P2.54mm_Vertical
J13: GRN LED; PinHeader_1x02_P2.54mm_Vertical
J14: RED LED; PinHeader_1x02_P2.54mm_Vertical
J15: SERVO; PinHeader_1x03_P2.54mm_Vertical
J16: PUSH; PinHeader_1x02_P2.54mm_Vertical
J17: POT; PinHeader_1x03_P2.54mm_Vertical
JP1: BL_DIN; PinHeader_1x03_P2.54mm_Vertical
JP2: BL_DOUT; PinHeader_1x03_P2.54mm_Vertical
MK1, MK2, MK3: MH; MountingHole_2.5mm
R1, R2: 120; R_0805_2012Metric
U0: ProMicro; DIP-24_W15.24mm_Socket
U1: MAX487EESA+T; SOIC-8_3.9x4.9mm_P1.27mm

Connections:
+5V: C1.1, J17.1, U0.21, U1.8
/+3.3V_SUPPLY: J1.3, J2.3
/+5V_SUPPLY: J1.2, J2.2, J5.7, J15.2
/+12V_SUPPLY: J1.1, J2.1, U0.24
/A0: J17.2, U0.17
/BUS-A: J1.4, J2.4, U1.6
/BUS-B: J1.5, J2.5, U1.7
/D4A6: U0.7, U1.2, U1.3
/D14MISO: J5.10, U0.15
/D15SCK: J5.9, U0.16
/D16MOSI: J5.2, U0.14
/DATAIN: J3.4, JP1.1
/DATAOUT: J4.4, JP2.1
/LED+5V: J3.1, J3.2, J4.1, J4.2
/LEDGND: J3.3, J4.3
/LED_DIN: J5.4, JP1.2
/LED_DOUT: J5.8, JP2.2
/RX1D0: U0.2, U1.1
/SDAD2: J16.1, U0.5
/TX0D1: U0.1, U1.4
/~D5: J15.3, U0.8
/~D6A7: J14.1, U0.9
/~D9A9: J13.1, U0.12
/~D10A10: J5.1, U0.13
/~SCLD3: JP1.3, U0.6
GND: C1.2, J1.6, J2.6, J5.5, J5.6, J15.1, J16.2, J17.3, JP2.3, R1.1, R2.1, U0.3, U0.4, U0.23, U1.5
unnamed: J13.2, R1.2
unnamed: J14.2, R2.2
