Exprezz0/F-18C_Simulator/ECAD/PCBs/Functional PCBs/GAUGE_Standby Altimeter/GAUGE_Standby Altimeter.kicad_pcb

## KiCad design ECAD/PCBs/Functional PCBs/GAUGE_Standby Altimeter/GAUGE_Standby Altimeter.kicad_pcb (2023-02-10)

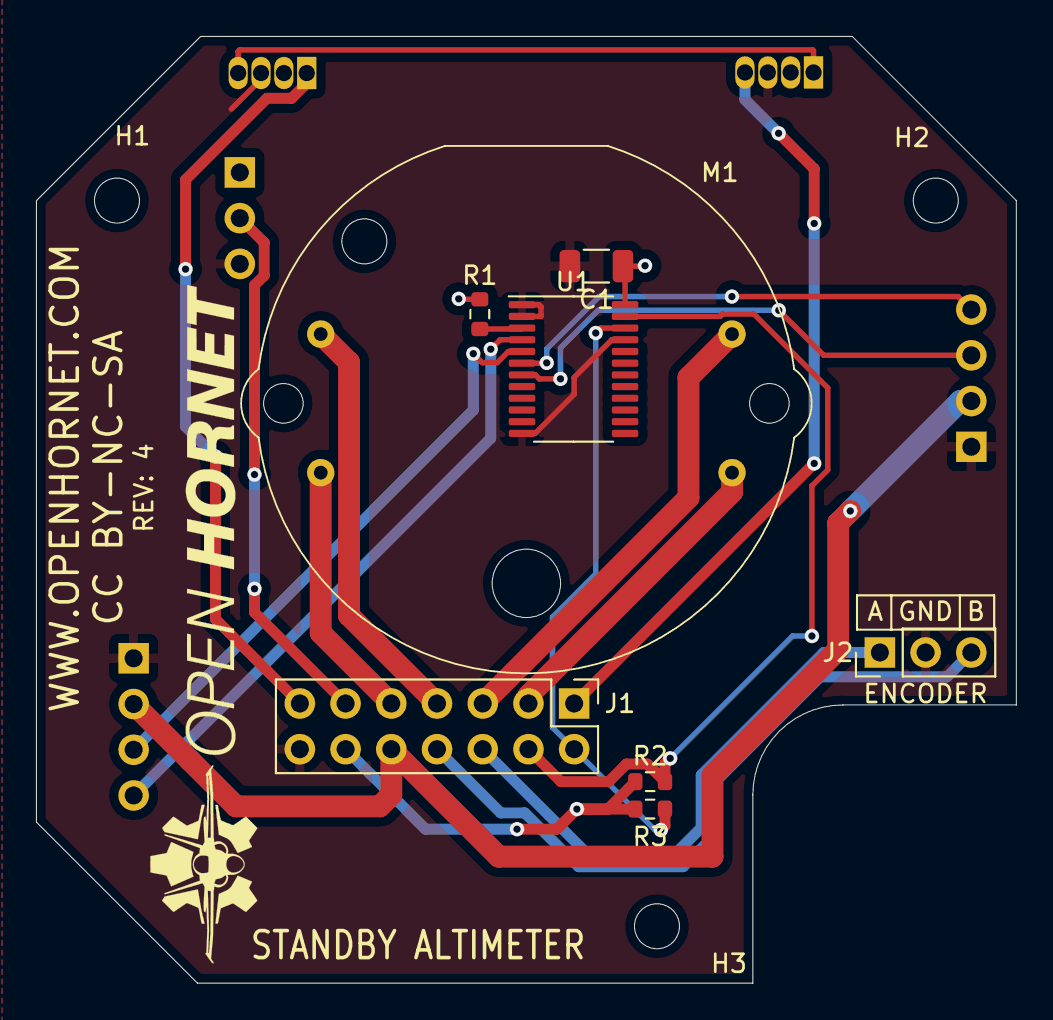
[picture p333: board GAUGE_Standby Altimeter.kicad_pcb from above]

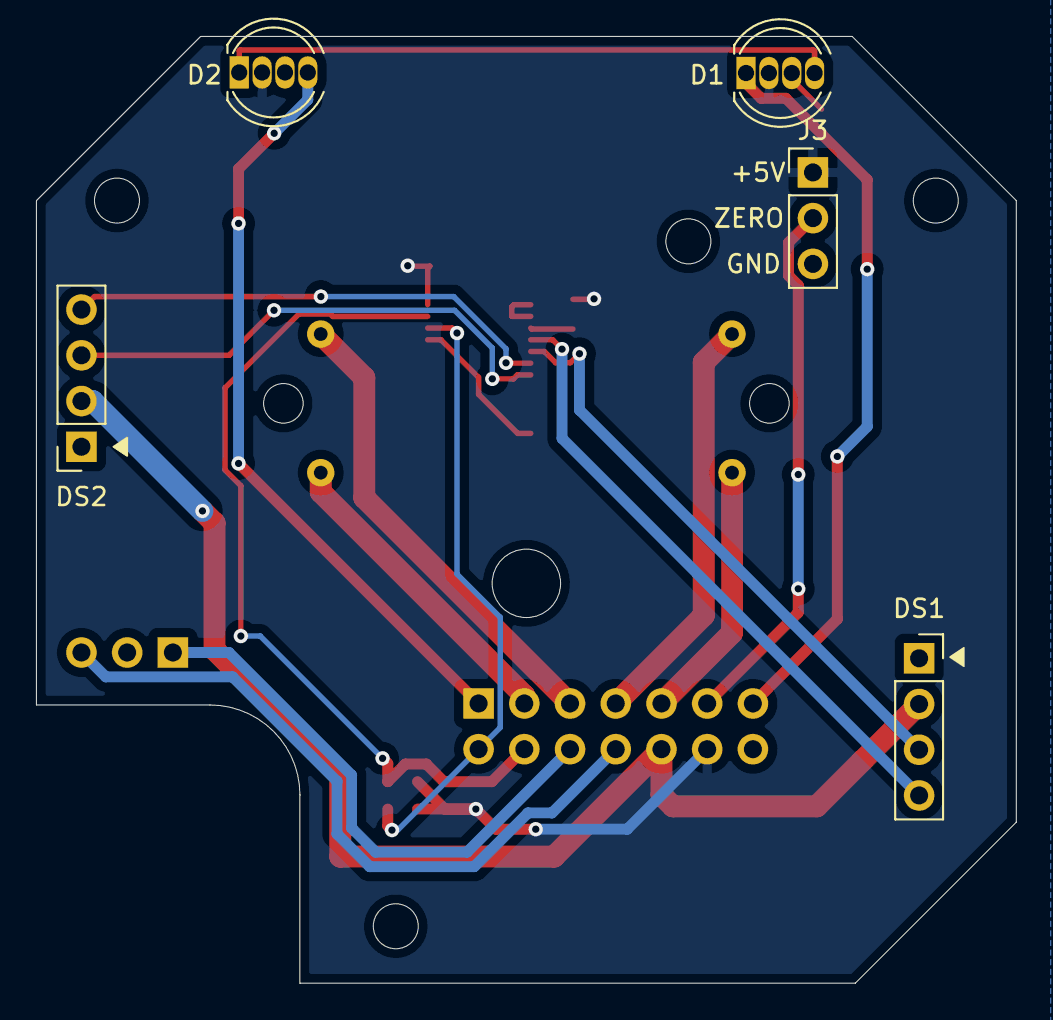
[picture p334: board GAUGE_Standby Altimeter.kicad_pcb from below]

Board: 2 copper layers, 54.4 x 52.6 mm, 16 parts (5 on the bottom side), 20 nets.

Parts:
C1: 47uF; C_1206_3216Metric
D1, D2: 1938; LED_D5.0mm-4_RGB
DS1: 10K_ALT_DISP; PinSocket_1x04_P2.54mm_Vertical
DS2: PRESS_DISP; PinSocket_1x04_P2.54mm_Vertical
H1, H2, H3: MountingHole; MountingHole_2.5mm
J1: ALT_CONN; PinHeader_2x07_P2.54mm_Vertical
J2: ENCODER; PinHeader_1x03_P2.54mm_Vertical
J3: ZERO; PinHeader_1x03_P2.54mm_Vertical
M1: VID29-02
R1, R2, R3: 10K; R_0603_1608Metric
U1: TCA9548APWR; TSSOP-24_4.4x7.8mm_P0.65mm

Connections:
+3V3: DS1.2, DS2.2, J1.10
+5V: C1.1, D1.2, D2.2, J1.12, J3.1, R1.1, R2.1, R3.1, U1.24
/CH_A: J1.6, J2.1
/CH_B: J1.8, J2.3
/COIL1: J1.7, M1.1
/COIL2: J1.9, M1.2
/COIL3: J1.3, M1.3
/COIL4: J1.5, M1.4
/LED_DIN: D1.1, J1.13
/LED_DOUT: D2.4, J1.1
/SC0: DS1.3, U1.5
/SC1: DS2.3, U1.7
/SCL: J1.2, R3.2, U1.22
/SD0: DS1.4, U1.4
/SD1: DS2.4, U1.6
/SDA: J1.4, R2.2, U1.23
/ZERO_DETECT: J1.11, J3.2
GND: C1.2, D1.3, D2.3, DS1.1, DS2.1, J1.14, J2.2, J3.3, U1.1, U1.2, U1.12, U1.21
unnamed: D1.4, D2.1
unnamed: R1.2, U1.3
