Exprezz0/F-18C_Simulator/ECAD/PCBs/Functional PCBs/JETT STATION SELECT/JETT STATION SELECT.kicad_pcb

## KiCad design ECAD/PCBs/Functional PCBs/JETT STATION SELECT/JETT STATION SELECT.kicad_pcb (2023-02-10)

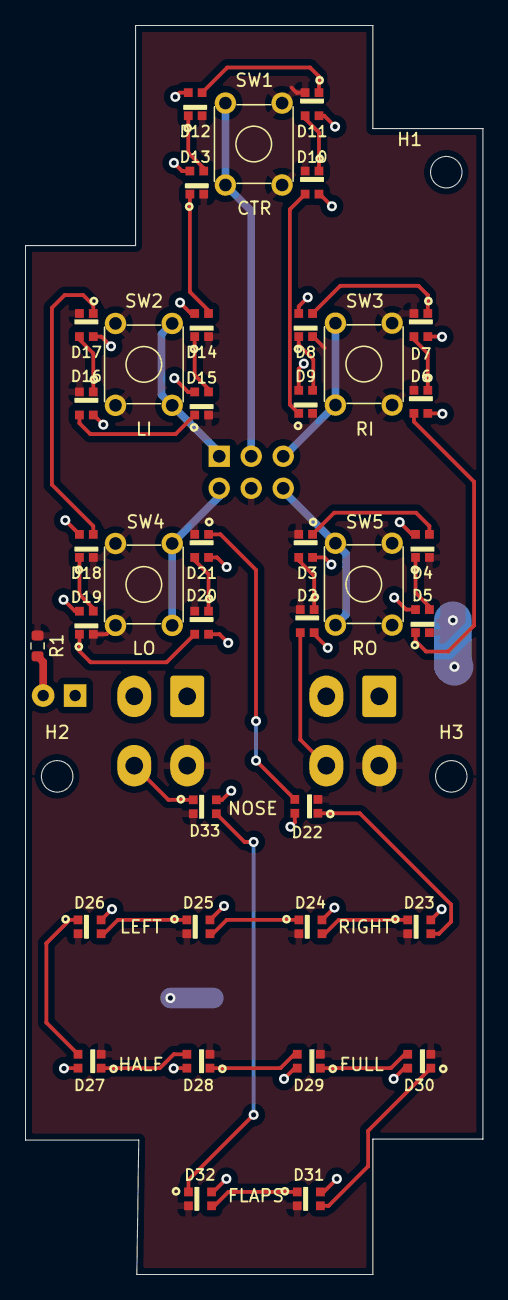
[picture p335: board JETT STATION SELECT.kicad_pcb from above]

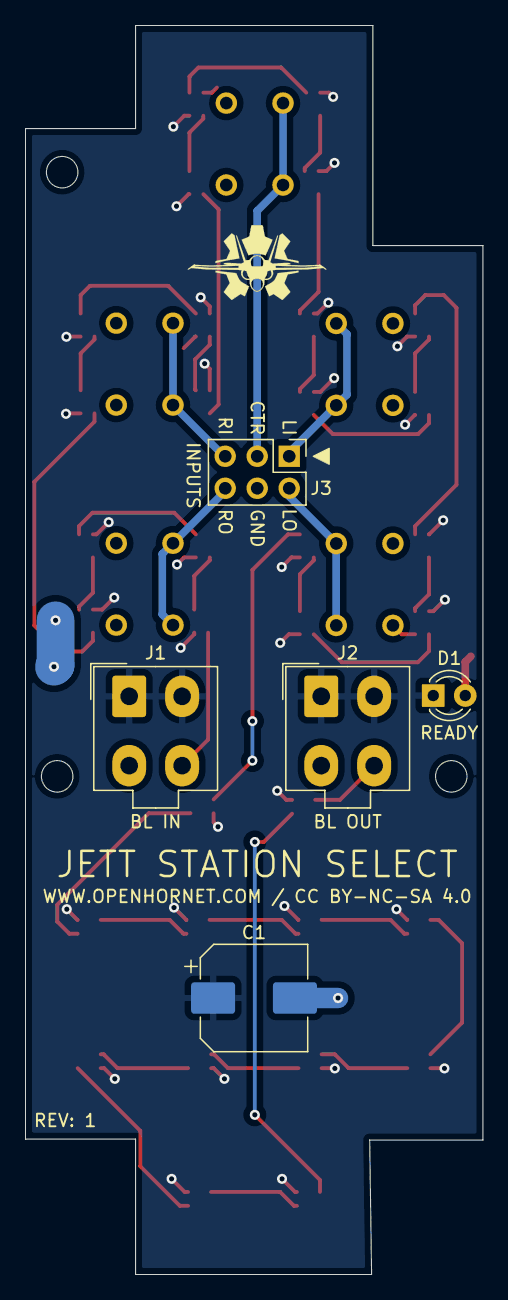
[picture p336: board JETT STATION SELECT.kicad_pcb from below]

Board: 2 copper layers, 36.3 x 99.1 mm, 47 parts (6 on the bottom side), 41 nets.

Parts:
C1: 1000 nF; CP_Elec_8x10
D1: READY; LED_D3.0mm
D2, D3, D4, D5, D6, D7, D8, D9, D10, D11, D12, D13, D14, D15, D16, D17, D18, D19, D20, D21, D22, D23, D24, D25, D26, D27, D28, D29, D30, D31, D32, D33: LED; WS2812-2020
H1, H2, H3: MountingHole; MountingHole_2.5mm
J1: BL IN; Molex_Mini-Fit_Jr_5566-04A_2x02_P4.20mm_Vertical
J2: BL OUT; Molex_Mini-Fit_Jr_5566-04A_2x02_P4.20mm_Vertical
J3: INPUTS; PinHeader_2x03_P2.54mm_Vertical
LOGO1: OpenHornetLogoSmall; OH_LOGO_ONLY_11x6mm
R1: R; R_0603_1608Metric
SW1: CTR; SW_TH_Tactile_Omron_B3F-10xx
SW2: LI; SW_TH_Tactile_Omron_B3F-10xx
SW3: RI; SW_TH_Tactile_Omron_B3F-10xx
SW4: LO; SW_TH_Tactile_Omron_B3F-10xx
SW5: RO; SW_TH_Tactile_Omron_B3F-10xx

Connections:
/BL_+5V: C1.1, D1.1, D2.4, D3.4, D4.4, D5.4, D6.4, D7.4, D8.4, D9.4, D10.4, D11.4, D12.4, D13.4, D14.4, D15.4, D16.4, D17.4, D18.4, D19.4, D20.4, D21.4, D22.4, D23.4, D24.4, D25.4, D26.4, D27.4, D28.4, D29.4, D30.4, D31.4, D32.4, D33.4, J1.1, J1.2, J2.1, J2.2
/BL_DATA1: D9.1, D10.3
/BL_DATA2: D17.1, D18.3
/BL_DATA3: D25.1, D26.3
/BL_DIN: D2.3, J1.4
/BL_DOUT: D33.1, J2.4
/CTR_SW: J3.3, SW1.1, SW1.2
/LI_SW: J3.1, SW2.1, SW2.2
/LO_SW: J3.2, SW4.1, SW4.2
/RI_SW: J3.5, SW3.1, SW3.2
/RO_SW: J3.6, SW5.1, SW5.2
GND: C1.2, D2.2, D3.2, D4.2, D5.2, D6.2, D7.2, D8.2, D9.2, D10.2, D11.2, D12.2, D13.2, D14.2, D15.2, D16.2, D17.2, D18.2, D19.2, D20.2, D21.2, D22.2, D23.2, D24.2, D25.2, D26.2, D27.2, D28.2, D29.2, D30.2, D31.2, D32.2, D33.2, J1.3, J2.3, J3.4, R1.2, SW1.3, SW1.4, SW2.3, SW2.4, SW3.3, SW3.4, SW4.3, SW4.4, SW5.3, SW5.4
unnamed: D1.2, R1.1
unnamed: D2.1, D3.3
unnamed: D3.1, D4.3
unnamed: D4.1, D5.3
unnamed: D5.1, D6.3
unnamed: D6.1, D7.3
unnamed: D7.1, D8.3
unnamed: D8.1, D9.3
unnamed: D10.1, D11.3
unnamed: D11.1, D12.3
unnamed: D12.1, D13.3
unnamed: D13.1, D14.3
unnamed: D14.1, D15.3
unnamed: D15.1, D16.3
unnamed: D16.1, D17.3
unnamed: D18.1, D19.3
unnamed: D19.1, D20.3
unnamed: D20.1, D21.3
unnamed: D21.1, D22.3
unnamed: D22.1, D23.3
unnamed: D23.1, D24.3
unnamed: D24.1, D25.3
unnamed: D26.1, D27.3
unnamed: D27.1, D28.3
unnamed: D28.1, D29.3
unnamed: D29.1, D30.3
unnamed: D30.1, D31.3
unnamed: D31.1, D32.3
unnamed: D32.1, D33.3
