Exprezz0/F-18C_Simulator/ECAD/PCBs/Functional PCBs/AMPCD/AMPCD.kicad_pcb

## KiCad design ECAD/PCBs/Functional PCBs/AMPCD/AMPCD.kicad_pcb (2023-02-10)

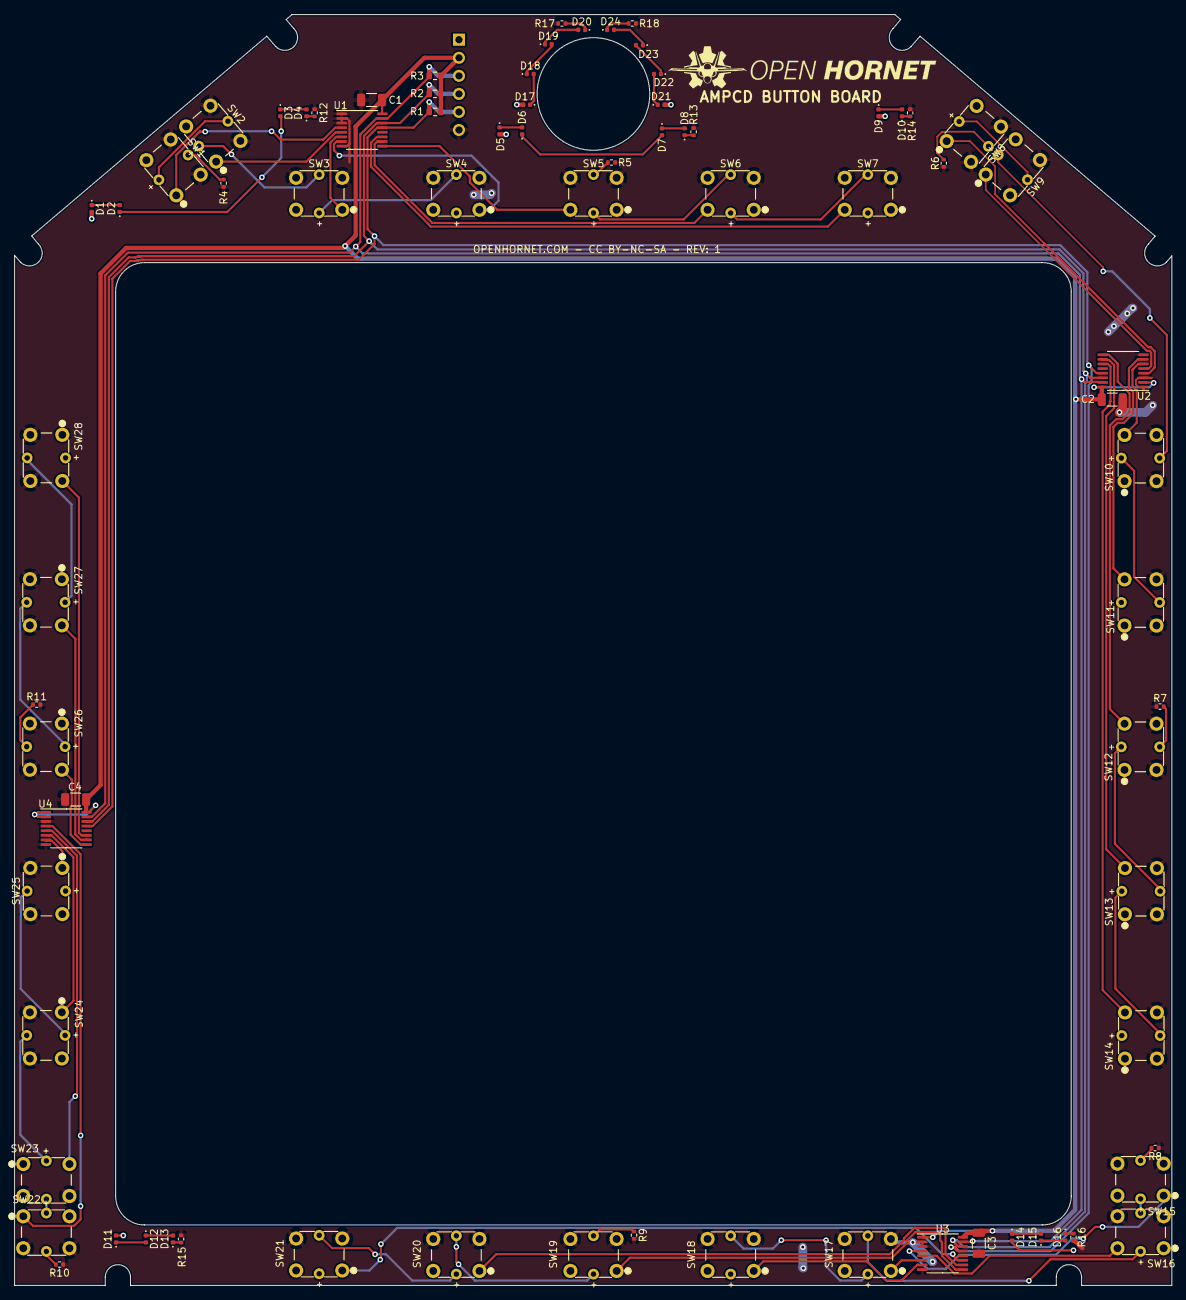
[picture p343: board AMPCD.kicad_pcb from above]

Board: 2 copper layers, 162.9 x 178.9 mm, 79 parts (1 on the bottom side), 72 nets.

Parts:
C1, C2, C3, C4: 47uF; C_1206_3216Metric
D1, D2, D3, D4, D5, D6, D7, D8, D9, D10, D11, D12, D13, D14, D15, D16, D17, D18, D19, D20, D21, D22, D23, D24: LED; LED_0402_1005Metric
J1: Conn_01x06; PinHeader_1x06_P2.54mm_Horizontal
R1, R2, R3: 10K; R_0603_1608Metric
R4, R6, R8, R10, R12, R13, R17, R18: 33; R_0402_1005Metric
R5, R7, R9, R11, R15, R16: 150; R_0402_1005Metric
R14: 270; R_0402_1005Metric
SW1, SW2, SW3, SW4, SW5, SW6, SW7, SW8, SW9, SW10, SW11, SW12, SW13, SW14, SW15, SW16, SW17, SW18, SW19, SW20, SW21, SW22, SW23, SW24, SW25, SW26, SW27, SW28: TL1240GQ_old
U1, U2, U3, U4: TCA9554PWR; TSSOP-16_4.4x5mm_P0.65mm

Connections:
+5V: C1.1, C2.1, C3.1, C4.1, J1.2, R1.1, R2.1, R3.1, U1.16, U2.2, U2.16, U3.1, U3.16, U4.1, U4.2, U4.16
/U1P3: SW4.1, U1.7
/U1P4: SW5.1, U1.9
/U1P5: SW6.1, U1.10
/U1P6: SW7.1, U1.11
/U2P0: SW8.1, U2.4
/U2P1: SW9.1, U2.5
/U2P4: SW12.1, U2.9
/U2P5: SW13.1, U2.10
/U2P6: SW14.1, U2.11
/U3P4: SW19.1, U3.9
/U3P5: SW20.1, U3.10
/U3P6: SW21.1, U3.11
/U4P0: SW22.1, U4.4
/U4P1: SW23.1, U4.5
GND: C1.2, C2.2, C3.2, C4.2, J1.6, R4.1, R5.1, R6.1, R7.1, R8.1, R9.1, R10.1, R11.1, R12.2, R13.2, R14.2, R15.2, R16.2, R17.2, R18.2, SW1.2, SW2.2, SW3.2, SW4.2, SW5.2, SW6.2, SW7.2, SW8.2, SW9.2, SW10.2, SW11.2, SW12.2, SW13.2, SW14.2, SW15.2, SW16.2, SW17.2, SW18.2, SW19.2, SW20.2, SW21.2, SW22.2, SW23.2, SW24.2, SW25.2, SW26.2, SW27.2, SW28.2, U1.1, U1.2, U1.3, U1.8, U2.1, U2.3, U2.8, U3.2, U3.3, U3.8, U4.3, U4.8
IRQ: J1.5, R1.2, U1.13, U2.13, U3.13, U4.13
unnamed: D1.1, D2.2
unnamed: D2.1, D3.2
unnamed: D3.1, D4.2
unnamed: D4.1, R12.1
unnamed: D5.1, D6.2
unnamed: D6.1, D7.2
unnamed: D7.1, D8.2
unnamed: D8.1, R13.1
unnamed: D10.1, R14.1
unnamed: D9.1, D10.2
unnamed: D11.1, D12.2
unnamed: D12.1, D13.2
unnamed: D13.1, R15.1
unnamed: D14.1, D15.2
unnamed: D15.1, D16.2
unnamed: D16.1, R16.1
unnamed: D17.1, D18.2
unnamed: D18.1, D19.2
unnamed: D19.1, D20.2
unnamed: D20.1, R17.1
unnamed: D21.1, D22.2
unnamed: D22.1, D23.2
unnamed: D23.1, D24.2
unnamed: D24.1, R18.1
unnamed: R4.2, SW1.3
unnamed: R5.2, SW5.3
unnamed: R6.2, SW8.3
unnamed: R7.2, SW12.3
unnamed: R8.2, SW15.3
unnamed: R9.2, SW19.3
unnamed: R10.2, SW22.3
unnamed: R11.2, SW26.3
unnamed: SW1.4, SW2.3
unnamed: SW2.4, SW3.3
unnamed: SW3.4, SW4.3
unnamed: SW5.4, SW6.3
unnamed: SW6.4, SW7.3
unnamed: SW8.4, SW9.3
unnamed: SW9.4, SW10.3
unnamed: SW10.4, SW11.3
unnamed: SW12.4, SW13.3
unnamed: SW13.4, SW14.3
unnamed: SW15.4, SW16.3
unnamed: SW16.4, SW17.3
unnamed: SW17.4, SW18.3
unnamed: SW19.4, SW20.3
unnamed: SW20.4, SW21.3
unnamed: SW22.4, SW23.3
unnamed: SW23.4, SW24.3
unnamed: SW24.4, SW25.3
unnamed: SW26.4, SW27.3
unnamed: SW27.4, SW28.3
SCL: J1.4, R2.2, U1.14, U2.14, U3.14, U4.14
SDA: J1.3, R3.2, U1.15, U2.15, U3.15, U4.15
VCC: D1.2, D5.2, D9.2, D11.2, D14.2, D17.2, D21.2, J1.1, SW4.4, SW7.4, SW11.4, SW14.4, SW18.4, SW21.4, SW25.4, SW28.4
