Exprezz0/F-18C_Simulator/ECAD/PCBs/Functional PCBs/DDI/DDI.kicad_pcb

## KiCad design ECAD/PCBs/Functional PCBs/DDI/DDI.kicad_pcb (2023-02-10)

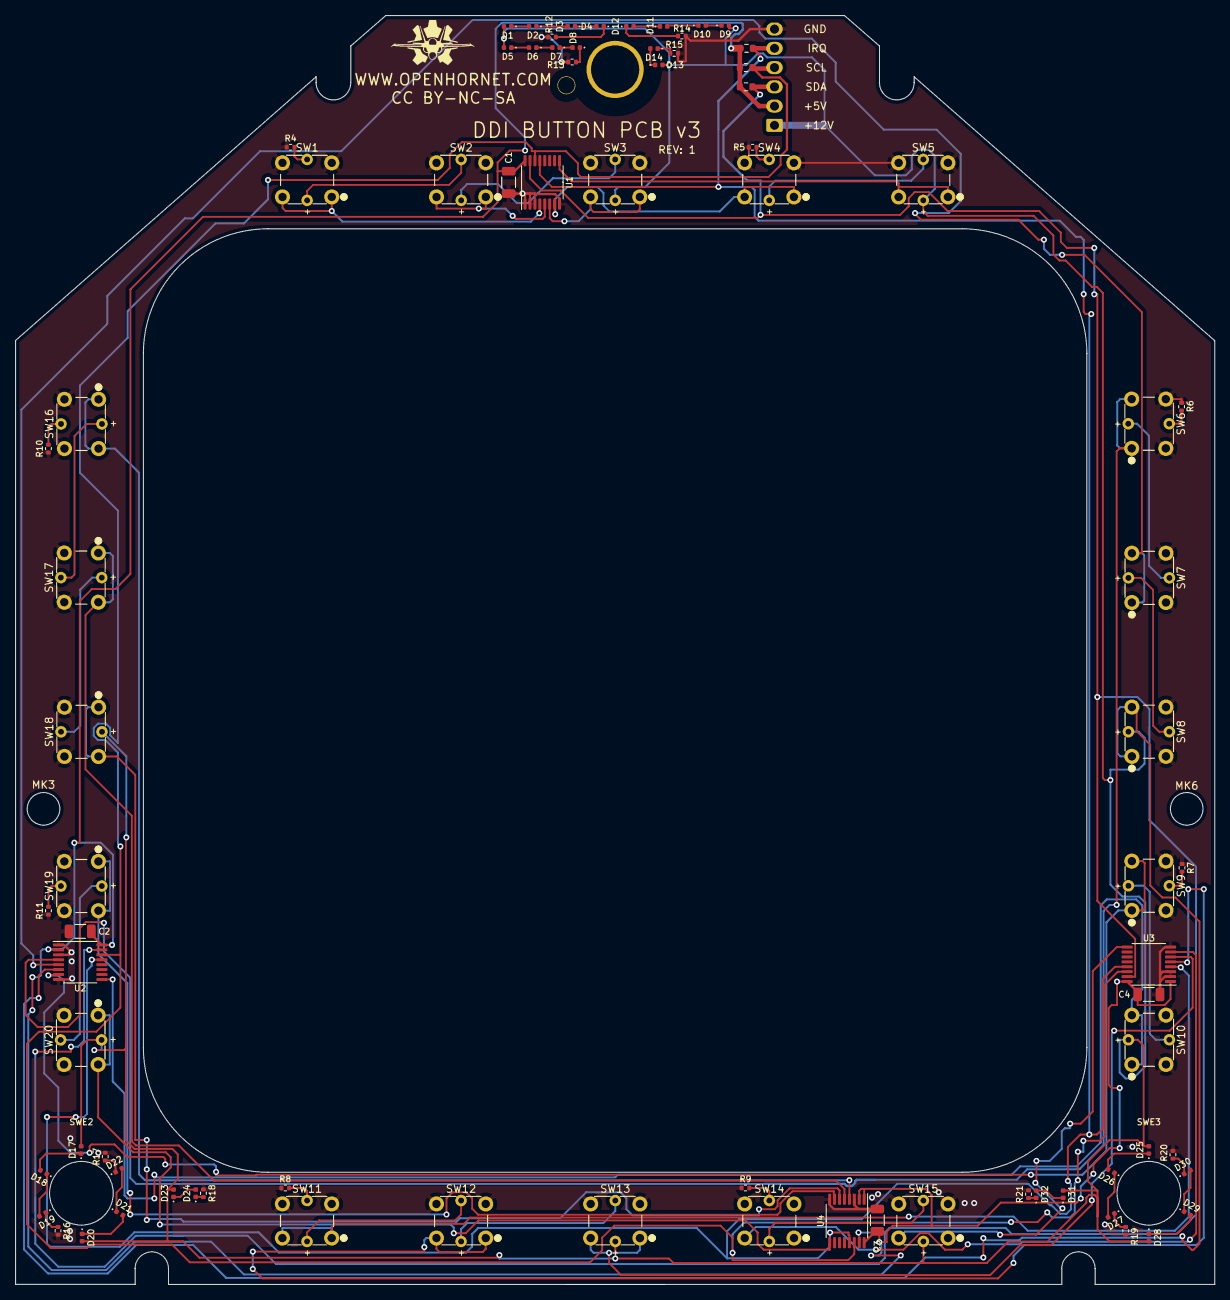
[picture p344: board DDI.kicad_pcb from above]

Board: 2 copper layers, 158.2 x 167.4 mm, 85 parts (1 on the bottom side), 56 nets.

Parts:
C1, C2, C3, C4: 47uF; C_1206_3216Metric
D1, D2, D3, D4, D5, D6, D7, D8, D9, D10, D11, D12, D13, D14, D17, D18, D19, D20, D21, D22, D23, D24, D25, D26, D27, D28, D29, D30, D31, D32: LED; LED_0402_1005Metric
J1: Conn_01x06; Molex_KK-254_AE-6410-06A_1x06_P2.54mm_Vertical
MK3, MK6: MH; MountingHole_4.3mm_M4
R1, R2, R3: 10K; R_0603_1608Metric
R4, R6, R8, R10, R16, R17, R19, R20: 150; R_0402_1005Metric
R5, R7, R9, R11, R15, R18, R21: 270; R_0402_1005Metric
R12, R13, R14: 33; R_0402_1005Metric
SW1, SW2, SW3, SW4, SW5, SW6, SW7, SW8, SW9, SW10, SW11, SW12, SW13, SW14, SW15, SW16, SW17, SW18, SW19, SW20: TL1240GQ
SWE1: MRY106_RotarySW
SWE2, SWE3: MountingHole_8.4mm_M8
U1, U2, U3, U4: TCA9554PWR; TSSOP-16_4.4x5mm_P0.65mm

Connections:
+5V: C1.1, C2.1, C3.1, C4.1, J1.2, R1.1, R2.1, R3.1, U1.16, U2.2, U2.16, U3.1, U3.16, U4.1, U4.2, U4.16
/U1P0: SW1.1, U1.4
/U1P1: SW2.1, U1.5
/U1P2: SW3.1, U1.6
/U1P3: SW4.1, U1.7
/U1P4: SW5.1, U1.9
/U2P0: SW6.1, U2.4
/U2P1: SW7.1, U2.5
/U2P2: SW8.1, U2.6
/U2P3: SW9.1, U2.7
/U2P4: SW10.1, U2.9
/U3P0: SW11.1, U3.4
/U3P1: SW12.1, U3.5
/U3P2: SW13.1, U3.6
/U3P3: SW14.1, U3.7
/U3P4: SW15.1, U3.9
/U4P0: SW16.1, U4.4
/U4P1: SW17.1, U4.5
/U4P2: SW18.1, U4.6
/U4P3: SW19.1, U4.7
/U4P4: SW20.1, U4.9
GND: C1.2, C2.2, C3.2, C4.2, J1.6, R4.1, R5.1, R6.1, R7.1, R8.1, R9.1, R10.1, R11.1, R12.2, R13.2, R14.2, R15.2, R16.2, R17.2, R18.2, R19.2, R20.2, R21.2, SW1.2, SW2.2, SW3.2, SW4.2, SW5.2, SW6.2, SW7.2, SW8.2, SW9.2, SW10.2, SW11.2, SW12.2, SW13.2, SW14.2, SW15.2, SW16.2, SW17.2, SW18.2, SW19.2, SW20.2, U1.1, U1.2, U1.3, U1.8, U2.1, U2.3, U2.8, U3.2, U3.3, U3.8, U4.3, U4.8
IRQ: J1.5, R1.2, U1.13, U2.13, U3.13, U4.13
unnamed: D1.1, D2.2
unnamed: D2.1, D3.2
unnamed: D3.1, D4.2
unnamed: D4.1, R12.1
unnamed: D5.1, D6.2
unnamed: D6.1, D7.2
unnamed: D7.1, D8.2
unnamed: D8.1, R13.1
unnamed: D10.1, D11.2
unnamed: D9.1, D10.2
unnamed: D11.1, D12.2
unnamed: D12.1, R14.1
unnamed: D13.1, D14.2
unnamed: D14.1, R15.1
unnamed: D17.1, D18.2
unnamed: D18.1, D19.2
unnamed: D19.1, R16.1
unnamed: D20.1, D21.2
unnamed: D21.1, D22.2
unnamed: D22.1, R17.1
unnamed: D23.1, D24.2
unnamed: D24.1, R18.1
unnamed: D25.1, D26.2
unnamed: D26.1, D27.2
unnamed: D27.1, R19.1
unnamed: D28.1, D29.2
unnamed: D29.1, D30.2
unnamed: D30.1, R20.1
unnamed: D31.1, D32.2
unnamed: D32.1, R21.1
SCL: J1.4, R2.2, U1.14, U2.14, U3.14, U4.14
SDA: J1.3, R3.2, U1.15, U2.15, U3.15, U4.15
VCC: D1.2, D5.2, D9.2, D13.2, D17.2, D20.2, D23.2, D25.2, D28.2, D31.2, J1.1
