Exprezz0/F-18C_Simulator/ECAD/PCBs/Functional PCBs/GAUGE_Analog Instruments/GAUGE_Analog Instruments.kicad_pcb

## KiCad design ECAD/PCBs/Functional PCBs/GAUGE_Analog Instruments/GAUGE_Analog Instruments.kicad_pcb (2023-02-10)

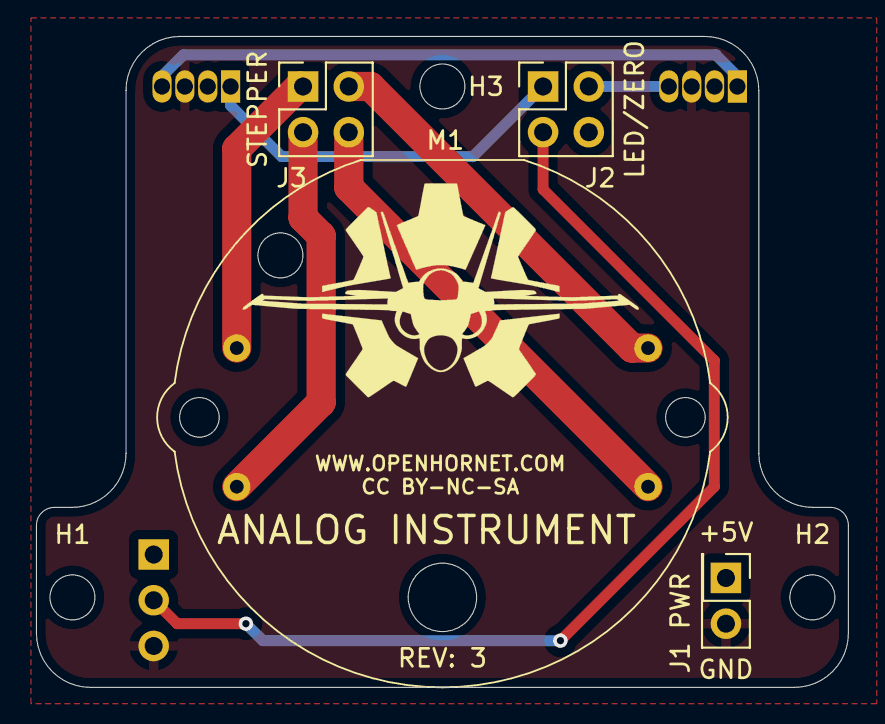
[picture p345: board GAUGE_Analog Instruments.kicad_pcb from above]

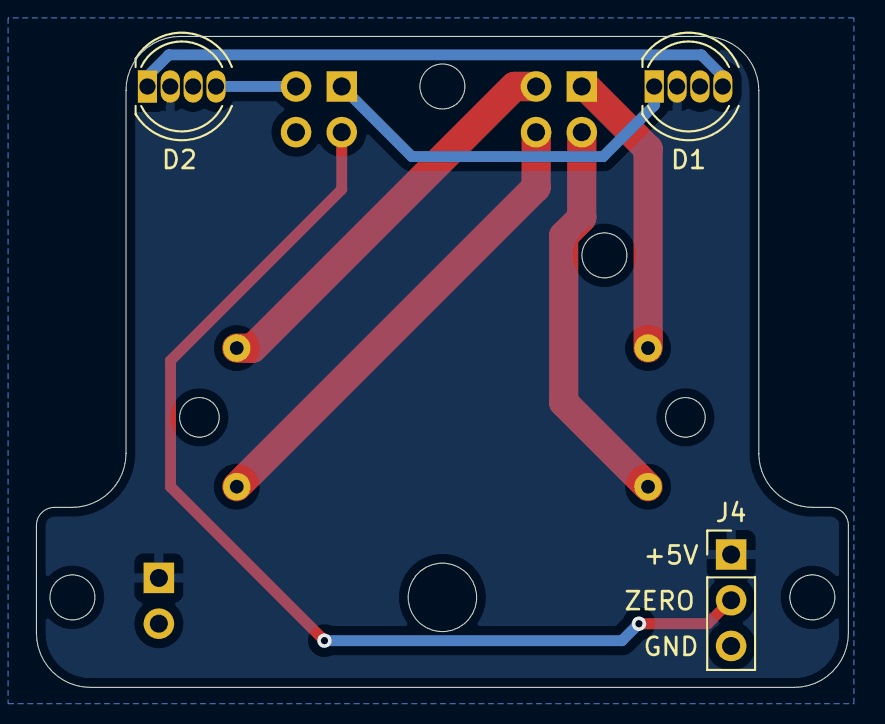
[picture p346: board GAUGE_Analog Instruments.kicad_pcb from below]

Board: 2 copper layers, 45.1 x 36.2 mm, 10 parts (3 on the bottom side), 10 nets.

Parts:
D1, D2: 1938; LED_D5.0mm-4_RGB
H1, H2, H3: MountingHole; MountingHole_2.5mm
J1: PWR; PinHeader_2x01_P2.54mm_Vertical
J2: LED/ZERO; PinHeader_2x02_P2.54mm_Vertical
J3: STEPPER; PinHeader_2x02_P2.54mm_Vertical
J4: ZERO; PinHeader_1x03_P2.54mm_Vertical
M1: VID29-02

Connections:
+5V: D1.2, D2.2, J1.1, J4.1
/COIL1: J3.1, M1.1
/COIL2: J3.3, M1.2
/COIL3: J3.4, M1.3
/COIL4: J3.2, M1.4
/LED_DIN: D1.1, J2.1
/LED_DOUT: D2.4, J2.2
/ZERO_DETECT: J2.3, J4.2
GND: D1.3, D2.3, J1.2, J4.3
unnamed: D1.4, D2.1
