Exprezz0/F-18C_Simulator/ECAD/PCBs/Functional PCBs/CONTROLLER_Stick/CONTROLLER_Stick.kicad_pcb

## KiCad design ECAD/PCBs/Functional PCBs/CONTROLLER_Stick/CONTROLLER_Stick.kicad_pcb (2023-02-10)

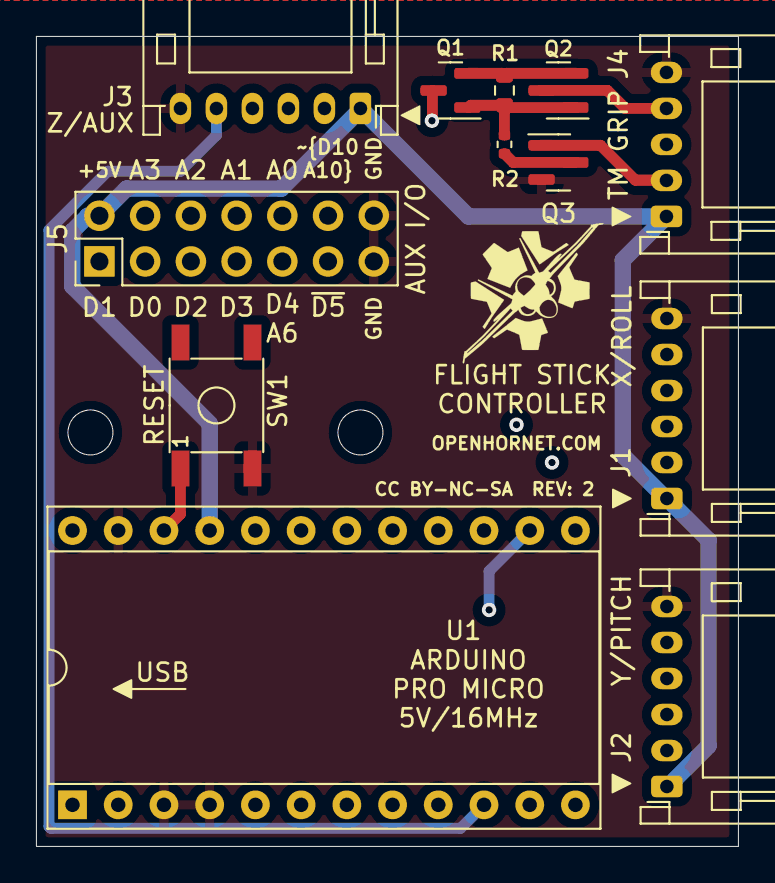
[picture p347: board CONTROLLER_Stick.kicad_pcb from above]

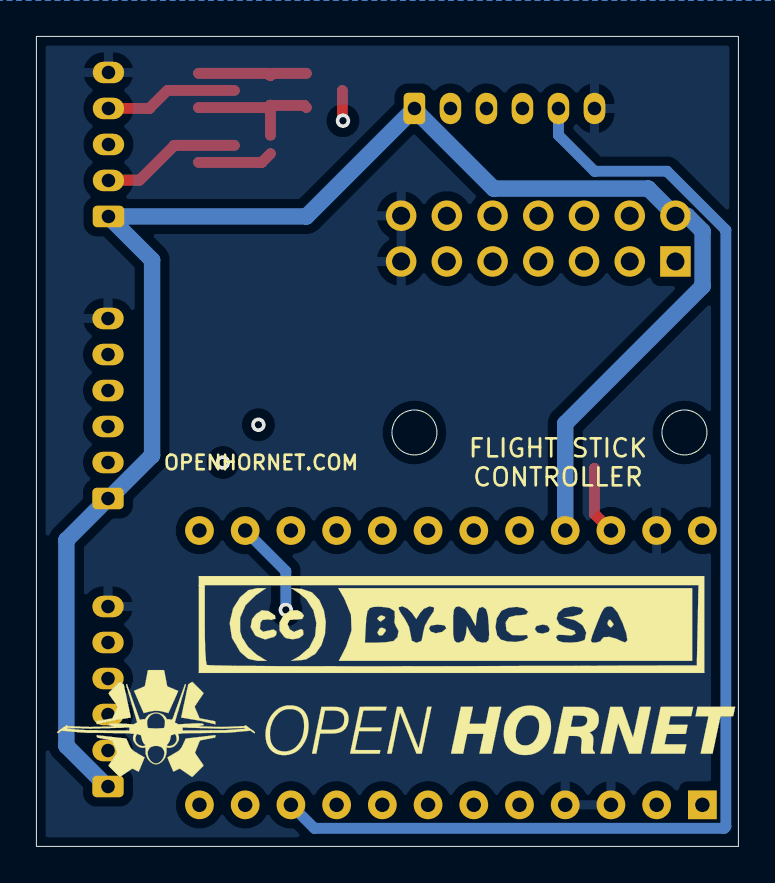
[picture p348: board CONTROLLER_Stick.kicad_pcb from below]

Board: 4 copper layers, 39.0 x 45.0 mm, 17 parts (2 on the bottom side), 25 nets.

Parts:
H1, H2: MountingHole; MountingHole_2.5mm
J1: X/ROLL; JST_PH_S6B-PH-K_1x06_P2.00mm_Horizontal
J2: Y/PITCH; JST_PH_S6B-PH-K_1x06_P2.00mm_Horizontal
J3: Z/AUX; JST_PH_S6B-PH-K_1x06_P2.00mm_Horizontal
J4: TM GRIP; JST_PH_S5B-PH-K_1x05_P2.00mm_Horizontal
J5: AUX I/O; PinHeader_2x07_P2.54mm_Vertical
LOGO1: OpenHornetLogoSmall; OH_LOGO_37.7mm_5.9mm
LOGO2: OpenHornetLogoSmall; CC-BY-NC-SA-Small
LOGO3: OpenHornetLogoSmall; OH_LOGO_ONLY_11x6mm
Q1, Q2: IRLML6402TRPBF; SOT-23
Q3: 2N7002; SOT-23
R1: 10k; R_0603_1608Metric
R2: 33; R_0402_1005Metric
SW1: RESET; SMD-SW-4_5.1x5.1
U1: ProMicro; DIP-24_W15.24mm_Socket

Connections:
+5V: J1.1, J2.1, J3.1, J4.1, J5.2, U1.21
/A0: J5.10, U1.17
/A1: J5.8, U1.18
/A2: J5.6, U1.19
/A3: J5.4, U1.20
/CSg: J4.2, Q3.1, U1.9
/CSx: J1.5, U1.12
/CSy: J2.5, U1.11
/CSz: J3.5, U1.10
/D0: J5.3, U1.2
/D1: J5.1, U1.1
/D2: J5.5, U1.5
/D4A6: J5.9, U1.7
/MISO: J1.2, J2.2, J3.2, Q1.3, U1.15
/MISOg: J4.4, Q2.3
/MOSI: J1.3, J2.3, J3.3, U1.14
/RST: SW1.1, U1.22
/SCK: J1.4, J2.4, J3.4, J4.3, U1.16
/~D3: J5.7, U1.6
/~D5: J5.11, U1.8
/~D10A10: J5.12, U1.13
GND: J1.6, J2.6, J3.6, J4.5, J5.13, J5.14, Q3.2, SW1.3, U1.3, U1.4, U1.23
unnamed: Q1.1, Q2.1, R1.2, R2.1
unnamed: Q1.2, Q2.2, R1.1
unnamed: Q3.3, R2.2
