Exprezz0/F-18C_Simulator/ECAD/PCBs/ABSIS/ABSIS_Pit Management System/ABSIS_Pit Management System.kicad_pcb

## KiCad design ECAD/PCBs/ABSIS/ABSIS_Pit Management System/ABSIS_Pit Management System.kicad_pcb (2023-01-10)

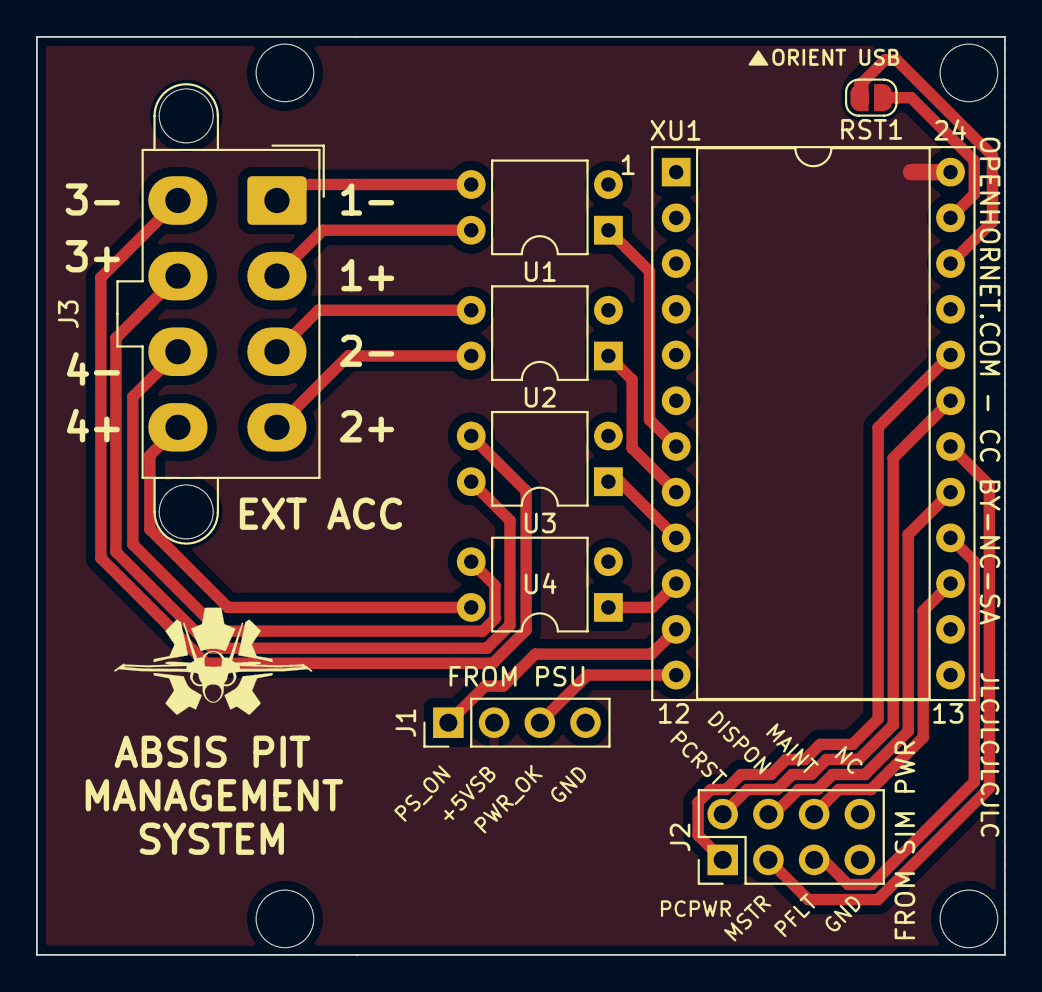
[picture p349: board ABSIS_Pit Management System.kicad_pcb from above]

Board: 2 copper layers, 53.8 x 51.0 mm, 15 parts (1 on the bottom side), 23 nets.

Parts:
H1, H2, H3, H4: MH; MountingHole_3.2mm_M3_DIN965
J1: FROM PSU; PinHeader_1x04_P2.54mm_Vertical
J2: FROM SIM PWR; PinHeader_2x04_P2.54mm_Vertical
J3: EXT ACC OUT; Molex_Mini-Fit_Jr_5566-08A2_2x04_P4.20mm_Vertical
LOGO1: OpenHornetLogoSmall; OH_LOGO_ONLY_11x6mm
LOGO2: OpenHornetLogoSmall; OH_LOGO_ONLY_22mm_12mm
RST1: RST; SolderJumper-2_P1.3mm_Open_RoundedPad1.0x1.5mm
U1, U2, U3, U4: 140817140010; DIP-4_W7.62mm
XU1: ProMicro_5V/16Hz; DIP-24_W15.24mm_Socket

Connections:
/+5VSB: J1.2, XU1.24
/A0: J2.4, XU1.17
/A1: J2.3, XU1.18
/A2: J2.2, XU1.19
/A3: J2.1, XU1.20
/D4_A6: U1.1, XU1.7
/D7: U4.1, XU1.10
/D8_A8: J1.1, XU1.11
/D14_MISO: J2.6, XU1.15
/D15_SCK: J2.5, XU1.16
/EXT_ACC1+: J3.2, U1.4
/EXT_ACC1-: J3.1, U1.3
/EXT_ACC2+: J3.4, U2.4
/EXT_ACC2-: J3.3, U2.3
/EXT_ACC3+: J3.6, U3.4
/EXT_ACC3-: J3.5, U3.3
/EXT_ACC4+: J3.8, U4.4
/EXT_ACC4-: J3.7, U4.3
/PWR_OK: J1.3, XU1.12
/RST: RST1.2, XU1.22
/~D5: U2.1, XU1.8
/~D6_A7: U3.1, XU1.9
GND: J1.4, J2.7, RST1.1, U1.2, U2.2, U3.2, U4.2, XU1.3, XU1.4, XU1.23
