Exprezz0/F-18C_Simulator/ECAD/PCBs/ABSIS/ABSIS_Hall Sensor/ABSIS_Hall Sensor.kicad_pcb

## KiCad design ECAD/PCBs/ABSIS/ABSIS_Hall Sensor/ABSIS_Hall Sensor.kicad_pcb (2023-01-10)

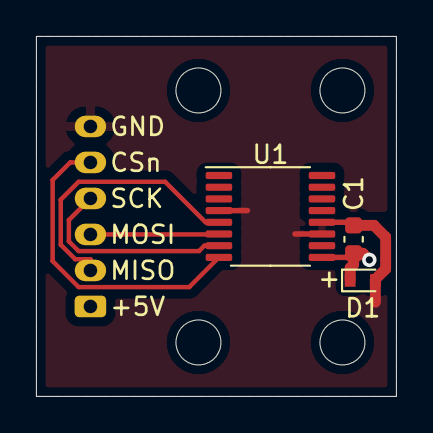
[picture p350: board ABSIS_Hall Sensor.kicad_pcb from above]

Board: 2 copper layers, 20.0 x 20.0 mm, 8 parts (1 on the bottom side), 6 nets.

Parts:
C1: 0.1uF; C_0603_1608Metric
D1: ESD5Z5V0; D_SOD-523
H1, H2, H3, H4: MountingHole; MountingHole_2.5mm
J1: IN; JST_PH_S6B-PH-K_1x06_P2.00mm_Horizontal
U1: MT6825GT; TSSOP-16_4.4x5mm_P0.65mm

Connections:
+5V: C1.1, D1.1, J1.1, U1.9
/CSN: J1.5, U1.8
/MISO: J1.2, U1.5
/MOSI: J1.3, U1.6
/SCK: J1.4, U1.7
GND: C1.2, D1.2, J1.6, U1.4, U1.11, U1.12
