Exprezz0/F-18C_Simulator/ECAD/PCBs/ABSIS/ABSIS_HID Bus Master/ABSIS_HID Bus Master.kicad_pcb

## KiCad design ECAD/PCBs/ABSIS/ABSIS_HID Bus Master/ABSIS_HID Bus Master.kicad_pcb (2023-01-10)

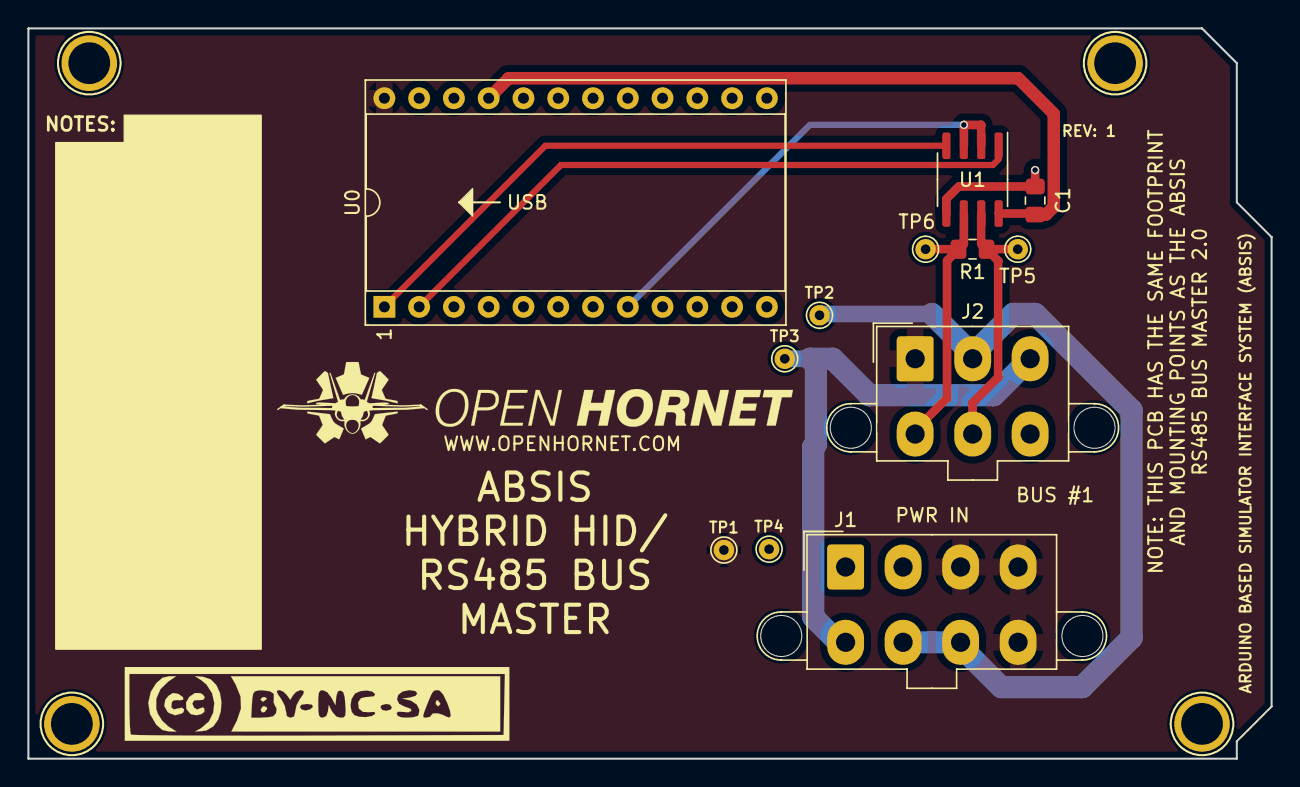
[picture p351: board ABSIS_HID Bus Master.kicad_pcb from above]

Board: 2 copper layers, 90.8 x 53.3 mm, 19 parts (1 on the bottom side), 10 nets.

Parts:
C1: 0.1uF; C_0805_2012Metric_Pad1.15x1.40mm_HandSolder
J1: PWR IN; Molex_Mini-Fit_Jr_5566-08A2_2x04_P4.20mm_Vertical
J2: BUS #1; Molex_Mini-Fit_Jr_5566-06A2_2x03_P4.20mm_Vertical
LOGO1: OpenHornetLogoSmall; OH_LOGO_37.7mm_5.9mm
LOGO3: OpenHornetLogoSmall; CC-BY-NC-SA-Small
LOGO4: OpenHornetLogoSmall; OH_LOGO_LARGE
MK1, MK3, MK4, MK6: MH; Arduino_1pin
R1: 120; R_0805_2012Metric_Pad1.15x1.40mm_HandSolder
TP1: TP-12; TestPoint_THTPad_D1.5mm_Drill0.7mm
TP2: TP-5V; TestPoint_THTPad_D1.5mm_Drill0.7mm
TP3: TP-3.3V; TestPoint_THTPad_D1.5mm_Drill0.7mm
TP4: TP-GND; TestPoint_THTPad_D1.5mm_Drill0.7mm
TP5: TP-B1B; TestPoint_THTPad_D1.5mm_Drill0.7mm
TP6: TP-B1A; TestPoint_THTPad_D1.5mm_Drill0.7mm
U0: ProMicro; DIP-24_W15.24mm_Socket
U1: MAX487EESA+T; SOIC-8_3.9x4.9mm_P1.27mm

Connections:
+5V: C1.1, U0.21, U1.8
/+3.3V_SUPPLY: J1.5, J2.3, TP3.1
/+5V_SUPPLY: J1.6, J1.7, J2.2, TP2.1
/+12V_SUPPLY: J1.3, J1.4, J1.8, J2.1, TP1.1, U0.24
/BUS1-A: J2.4, R1.2, TP6.1, U1.6
/BUS1-B: J2.5, R1.1, TP5.1, U1.7
/RX1_D0: U0.2, U1.1
/TX0_D1: U0.1, U1.4
/~D5: U0.8, U1.2, U1.3
GND: C1.2, J1.1, J1.2, J2.6, TP4.1, U0.3, U0.4, U0.23, U1.5
