Exprezz0/F-18C_Simulator/ECAD/interconnects/OH_Center_Tub.sch

## KiCad design ECAD/interconnects/OH_Center_Tub.sch (2023-01-02)

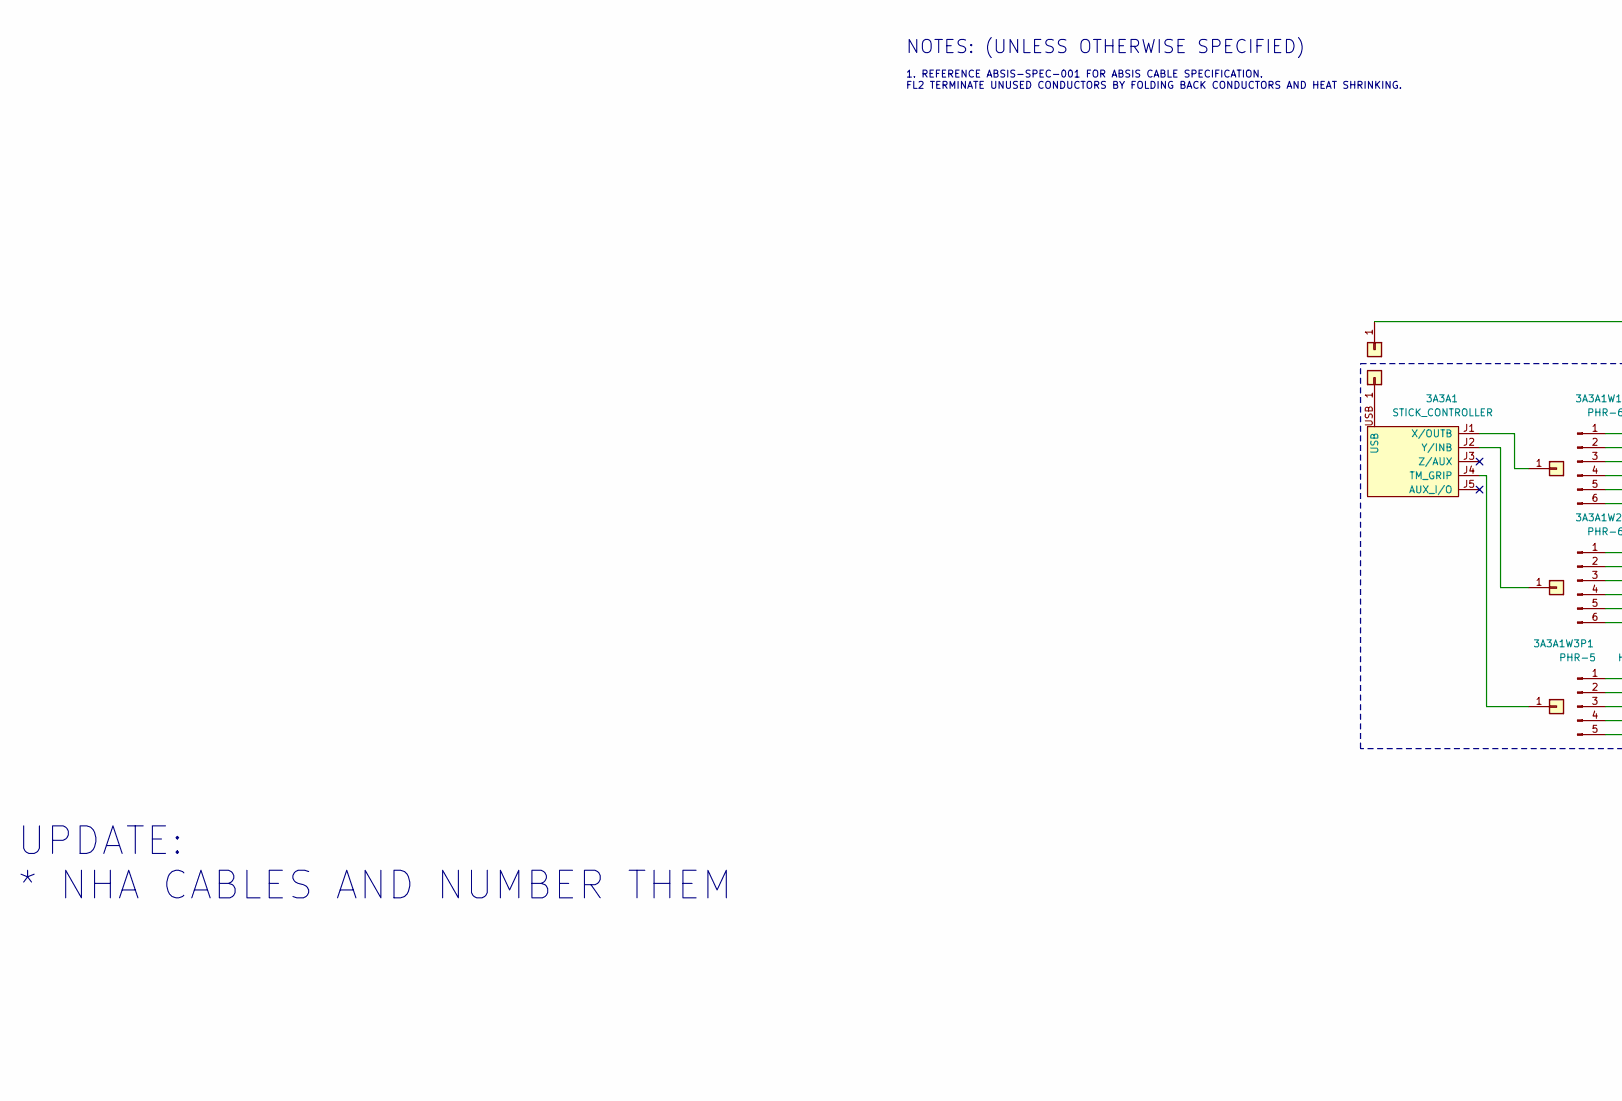
[picture p352: schematic OH_Center_Tub.sch, part in row 1, column 1]

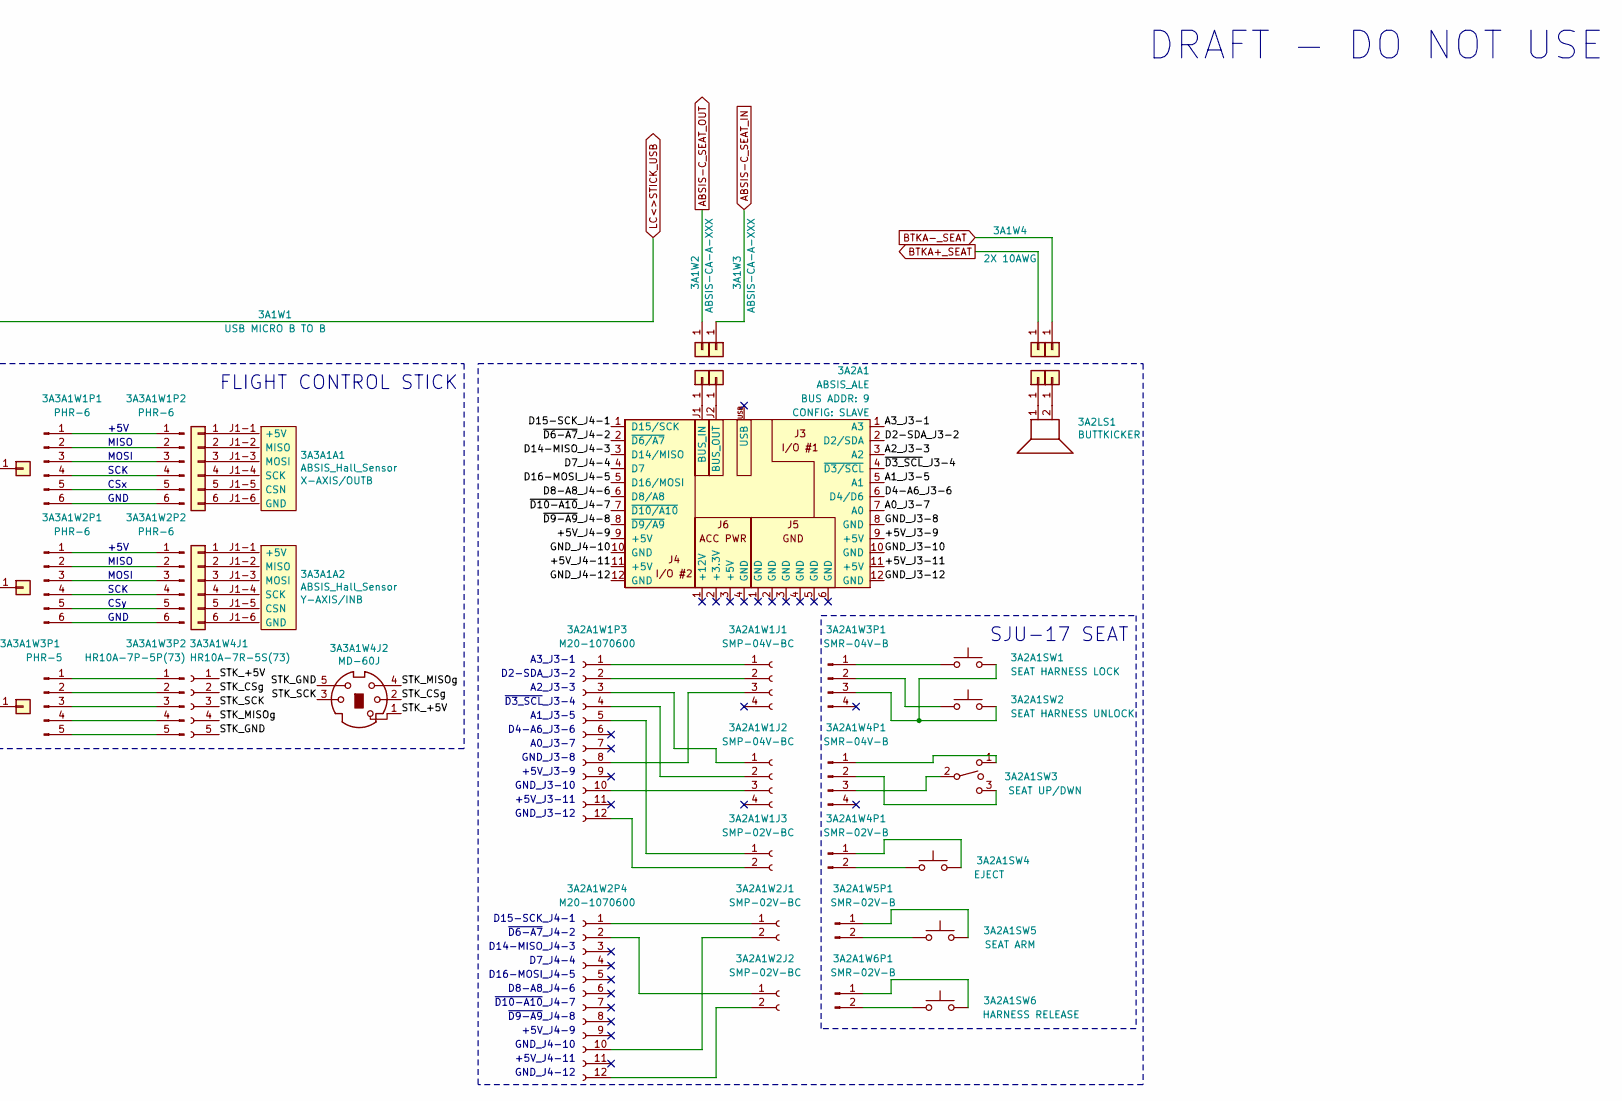
[picture p353: schematic OH_Center_Tub.sch, part in row 1, column 2]

Parts:
3A1W1: USB MICRO B TO B
3A1W2, 3A1W3: ABSIS-CA-A-XXX
3A1W4: 2X 10AWG
3A2A1: ABSIS_ALE
3A2A1SW1: SEAT HARNESS LOCK
3A2A1SW2: SEAT HARNESS UNLOCK
3A2A1SW3: SEAT UP/DWN
3A2A1SW4: EJECT
3A2A1SW5: SEAT ARM
3A2A1SW6: HARNESS RELEASE
3A2A1W1J1, 3A2A1W1J2: SMP-04V-BC
3A2A1W1J3, 3A2A1W2J1, 3A2A1W2J2: SMP-02V-BC
3A2A1W1P3, 3A2A1W2P4: M20-1070600
3A2A1W3P1, 3A2A1W4P1: SMR-04V-B
3A2A1W5P1, 3A2A1W6P1: SMR-02V-B
3A2LS1: BUTTKICKER
3A3A1: STICK_CONTROLLER
3A3A1A1, 3A3A1A2: ABSIS_Hall_Sensor
3A3A1W1P1, 3A3A1W1P2, 3A3A1W2P1, 3A3A1W2P2: PHR-6
3A3A1W3P1: PHR-5
3A3A1W3P2: HR10A-7P-5P(73)
3A3A1W4J1: HR10A-7R-5S(73)
3A3A1W4J2: MD-60J
4A2A1~: (no value)
~: (no value)

Connections:
+5V_J3-9: 3A2A1.9 (+5V)
+5V_J3-11: 3A2A1.11 (+5V)
+5V_J4-9: 3A2A1.9 (+5V)
+5V_J4-11: 3A2A1.11 (+5V)
A0_J3-7: 3A2A1.7 (A0)
A1_J3-5: 3A2A1.5 (A1)
A2_J3-3: 3A2A1.3 (+5V)
A3_J3-1: 3A2A1.1 (+12V)
ABSIS-C_SEAT_IN: 3A1W3.1
ABSIS-C_SEAT_OUT: 3A1W2.1
BTKA+_SEAT: 3A1W4.1
D2-SDA_J3-2: 3A2A1.2 (+3.3V)
D4-A6_J3-6: 3A2A1.6 (D4/D6)
D7_J4-4: 3A2A1.4 (D7)
D8-A8_J4-6: 3A2A1.6 (D4/D6)
D14-MISO_J4-3: 3A2A1.3 (+5V)
D15-SCK_J4-1: 3A2A1.1 (+12V)
D16-MOSI_J4-5: 3A2A1.5 (A1)
GND_J3-8: 3A2A1.8 (GND)
GND_J3-10: 3A2A1.10 (GND)
GND_J3-12: 3A2A1.12 (GND)
GND_J4-10: 3A2A1.10 (GND)
GND_J4-12: 3A2A1.12 (GND)
LC<>STICK_USB: 3A1W1.1
unnamed: 3A2A1.J1 (BUS_IN), ~.1
unnamed: 3A2A1.J2 (BUS_OUT), ~.1
unnamed: 3A2A1SW1.1, 3A2A1W3P1.1
unnamed: 3A2A1SW1.2, 3A2A1SW2.2, 3A2A1W3P1.3
unnamed: 3A2A1SW2.1, 3A2A1W3P1.2
unnamed: 3A2A1SW3.1, 3A2A1W4P1.1
unnamed: 3A2A1SW3.2, 3A2A1W4P1.3
unnamed: 3A2A1SW3.3, 3A2A1W4P1.2
unnamed: 3A2A1SW4.1, 3A2A1W4P1.2
unnamed: 3A2A1SW4.2, 3A2A1W4P1.1
unnamed: 3A2A1SW5.1, 3A2A1W5P1.2
unnamed: 3A2A1SW5.2, 3A2A1W5P1.1
unnamed: 3A2A1SW6.1, 3A2A1W6P1.2
unnamed: 3A2A1SW6.2, 3A2A1W6P1.1
unnamed: 3A2A1W1J1.1, 3A2A1W1P3.1
unnamed: 3A2A1W1J1.2, 3A2A1W1P3.2
unnamed: 3A2A1W1J1.3, 3A2A1W1P3.8
unnamed: 3A2A1W1J2.1, 3A2A1W1P3.3
unnamed: 3A2A1W1J2.2, 3A2A1W1P3.4
unnamed: 3A2A1W1J2.3, 3A2A1W1P3.10
unnamed: 3A2A1W1J3.1, 3A2A1W1P3.5
unnamed: 3A2A1W1J3.2, 3A2A1W1P3.12
unnamed: 3A2A1W2J1.1, 3A2A1W2P4.1
unnamed: 3A2A1W2J1.2, 3A2A1W2P4.10
unnamed: 3A2A1W2J2.1, 3A2A1W2P4.2
unnamed: 3A2A1W2J2.2, 3A2A1W2P4.12
unnamed: 3A3A1.J1 (X/OUTB), ~.1
unnamed: 3A3A1.J2 (Y/INB), ~.1
unnamed: 3A3A1.J4 (TM_GRIP), ~.1
unnamed: 3A3A1.USB, 4A2A1~.1
unnamed: 3A3A1A1.J1-1 (+5V), ~.1
unnamed: 3A3A1A1.J1-2 (MISO), ~.2
unnamed: 3A3A1A1.J1-3 (MOSI), ~.3
unnamed: 3A3A1A1.J1-4 (SCK), ~.4
unnamed: 3A3A1A1.J1-5 (CSN), ~.5
unnamed: 3A3A1A1.J1-6 (GND), ~.6
unnamed: 3A3A1A2.J1-1 (+5V), ~.1
unnamed: 3A3A1A2.J1-2 (MISO), ~.2
unnamed: 3A3A1A2.J1-3 (MOSI), ~.3
unnamed: 3A3A1A2.J1-4 (SCK), ~.4
unnamed: 3A3A1A2.J1-5 (CSN), ~.5
unnamed: 3A3A1A2.J1-6 (GND), ~.6
unnamed: 3A3A1W1P1.1, 3A3A1W1P2.1
unnamed: 3A3A1W1P1.2, 3A3A1W1P2.2
unnamed: 3A3A1W1P1.3, 3A3A1W1P2.3
unnamed: 3A3A1W1P1.4, 3A3A1W1P2.4
unnamed: 3A3A1W1P1.5, 3A3A1W1P2.5
unnamed: 3A3A1W1P1.6, 3A3A1W1P2.6
unnamed: 3A3A1W2P1.1, 3A3A1W2P2.1
unnamed: 3A3A1W2P1.2, 3A3A1W2P2.2
unnamed: 3A3A1W2P1.3, 3A3A1W2P2.3
unnamed: 3A3A1W2P1.4, 3A3A1W2P2.4
unnamed: 3A3A1W2P1.5, 3A3A1W2P2.5
unnamed: 3A3A1W2P1.6, 3A3A1W2P2.6
unnamed: 3A3A1W3P1.1, 3A3A1W3P2.1
unnamed: 3A3A1W3P1.2, 3A3A1W3P2.2
unnamed: 3A3A1W3P1.3, 3A3A1W3P2.3
unnamed: 3A3A1W3P1.4, 3A3A1W3P2.4
unnamed: 3A3A1W3P1.5, 3A3A1W3P2.5
STK_+5V: 3A3A1W4J1.1, 3A3A1W4J2.1
STK_CSg: 3A3A1W4J1.2, 3A3A1W4J2.2
STK_GND: 3A3A1W4J1.5, 3A3A1W4J2.5
STK_MISOg: 3A3A1W4J1.4, 3A3A1W4J2.4
STK_SCK: 3A3A1W4J1.3, 3A3A1W4J2.3
~D3_SCL~_J3-4: 3A2A1.4 (D7)
~D6-A7~_J4-2: 3A2A1.2 (+3.3V)
~D9-A9~_J4-8: 3A2A1.8 (GND)
~D10-A10~_J4-7: 3A2A1.7 (A0)

Notes on the sheet:
UPDATE: * NHA CABLES AND NUMBER THEM
DRAFT - DO NOT USE
D15-SCK_J4-1
~D6-A7~_J4-2
D14-MISO_J4-3
D7_J4-4
D16-MOSI_J4-5
D8-A8_J4-6
~D10-A10~_J4-7
~D9-A9~_J4-8
+5V_J4-9
GND_J4-10
+5V_J4-11
GND_J4-12
A3_J3-1
D2-SDA_J3-2
A2_J3-3
~D3_SCL~_J3-4
A1_J3-5
D4-A6_J3-6
A0_J3-7
GND_J3-8
+5V_J3-9
GND_J3-10
+5V_J3-11
GND_J3-12
SJU-17 SEAT
+5V
MISO
MOSI
SCK
CSx
GND
CSy
FLIGHT CONTROL STICK
NOTES: (UNLESS OTHERWISE SPECIFIED)
1. REFERENCE ABSIS-SPEC-001 FOR ABSIS CABLE SPECIFICATION. FL2 TERMINATE UNUSED CONDUCTORS BY FOLDING BACK CONDUCTORS AND HEAT SHRINKING.
