Exprezz0/F-18C_Simulator/ECAD/interconnects/OH_Lower_Instrument_Panel.sch

## KiCad design ECAD/interconnects/OH_Lower_Instrument_Panel.sch (2023-01-02)

Schematic: OH_Lower_Instrument_Panel.sch

Parts:
2A1A1: ABSIS HID BUS MASTER
2A2A1: ABSIS_ALE
2A2A1A1: JETT_STATION_SELECT
2A2A1A2: IFEI
2A2A1A3: VID RECORD BL
2A2A1A3A1, 2A3A1A2A1, 2A7A1A6A1: KYBD
2A2A1A3DS1, 2A3A1A6DS1: ER-TFTV070A1-3
2A2A1A3RV1: IFEI BRT
2A2A1A3SW1: MODE
2A2A1A3SW2: SOURCE
2A2A1A3W1J1: SMR-06V-B
2A2A1A4: JETT PLACARD BL
2A2A1W1P3, 2A2A1W1P4, 2A4A1W1P3, 2A4A1W2P4, 2A5A1W1P4, 2A5A1W2P3: M20-1070600
2A2A1W1P5: M20-1070300
2A2A1W1P6: M20-1070400
2A2A1W1P7: SMP-06V-BC
2A3A1: DDI_AMPCD_Controller
2A3A1A1: AMPCD_Button_PCB
2A3A1A2DS1: ER-TFTV101A1-1
2A3A1RV1, 2A3A1RV1SW1: AMPCD BRT
2A3A1SW1: HDG
2A3A1SW2: CRS
2A3A1W1P1: 10-11-2063
2A3A1W1P2: M20-1060600
2A3A1W2P1: 10-11-2043
2A3A1W3P1, 2A3A1W4P1: 10-11-2033
2A4A1: RWR CTRL BL
2A4A1A1: RWR_CONTROL_PANEL
2A4A1SW1: DIS TYPE
2A4A1W1P4, 2A7A1W1P1, 2A7A1W3P1: M20-1070500
2A4A1W2P5: SMP-05V-BC
2A5A1: ECM/DISP BL
2A5A1A1: ECM/DISP
2A5A1SW1: ECM
2A5A1SW2: DISPENSER
2A5A1SW3: AUX REL
2A5A1W1P5: 10-11-2023
2A5A1W1P6, 2A12A1W5J2: SMP-08V-BC
2A5A1W2P4, 2AXXWXP1, 2AXXWXP2: M20-1060400
2A5A1W2P5, 2A5A1W2P6, 2A7A1A1SW2P1, 2A7A1W1P2, 2A7A1W3P2: M20-1060200
2A5A1W3J1: SMR-08V-B
2A6A1, 2A7A1A3, 2A7A1A5: STANDBY_AIRSPEED_VVI
2A7A1: STANDBY_CONTROLLER
2A7A1A1SW1: SARI CAGE
2A7A1A1SW1P1: M20-1060500
2A7A1A1SW2: SARI TEST
2A7A1A2RV1: RWR BRT
2A7A1A2RV1P1, 2A7A1A4SW1P1: M20-1060300
2A7A1A3A1, 2A7A1A4A1, 2A7A1A5A1: UTIL_PHOTOSWITCH
2A7A1A4: STANDBY_ALTIMETER
2A7A1A4DS1, 2A7A1A4DS2: ER-OLEDM0.91-1W-12C
2A7A1A4SW1: STBY ALT ENC
2A7A1A6: (RTD2660H)
2A7A1W1P3, 2A7A1W1P4, 2A7A1W3P3, 2A7A1W3P4: M20-1070200
2A7A1W2P1: M20-1070700
2A8A1A1: F-1020, 12V
2A8A1A2: RUDDER PEDALS
2A8A1M1: PA-18-12-150
2A8A1M1J1: (39-01-2025)
2A8A1SW1: RDR ADJ UP
2A8A1SW2: RDR ADJ DWN
2A8A1W1P1: 39-01-2029
2A9A1, 2A9A2, 2A9A3: B09V6WY1SD
2A10: X502-1
2A10A2: 3.5mm STEREO TO RCA
2A10W1P1: SMR-04V-B
2A10W1P2: RJ11
2A11A1, 2A11A2: USB32HD4
2A12A1W1: 1698-01C
2A12A1W2, 5A11A1W2: ABSIS-CA-G-XXX
2A12A1W3, 2A12A1W4, 5A11A1W3, 5A11A1W4: ABSIS-CA-F-XXX
2A12A1W5J1, 5A11A1W5J1: 39-01-2221
2A12A1W5J3, 2A12A1W5J4: SMP-04V-BC
2A12A1W6J1: NL2MPXX
2A12A5W1: 9291-02HV
2A12A5W2: 1689-03C
2A12A5W3J1: 39-01-2081
2A12A5W3P1: 39-01-3085
2A13: ABSIS BackLightController
2A14A1: ABSIS_ATX_PSU_BREAKOUT
2A14A2: Generic ATX PSU (1000W MIN)
2A15A1: ABSIS_PMS
4A1W12, 4A1W13, 4A1W14, 4A1W18, 4A1W19, 4A13A1W6, 4A13A1W7, 5A11A1W6, 5A11A1W7: ABSIS-CA-B-XXX
4A2A1~: (no value)
4A13A1W8, 5A11A1W8: ABSIS-CA-C-XXX
5A11A1W1: 1698-03C
(0AxAxWx): ABSIS-CA-C-XXX
(0AxAxWxP2): 39-01-2220
(2A12A1W6), (4A13A1W6), (4A13A1W7): (no value)
A10A1: 3.5mm STEREO TO USB
~: (no value)

Connections:
2A1A1_USB: 2A9A3.~
2A2A1A1J1_BLIN: 2A2A1A1.J1 (BL_IN), ~.1
2A2A1A1J2_BLOUT: 2A2A1A1.1, 2A2A1A1.J2 (BL_OUT)
2A2A1A2J1_BLIN: 2A2A1A2.J1 (BL_IN), ~.1
2A2A1A2J2_BLOUT: 2A2A1A2.1, 2A2A1A2.J2 (BL_OUT)
2A2A1A3_HDMI: 2A11A1.4 (HDMI4)
2A4A1A1_HDMI: 2A11A1.3 (HDMI3)
2A4A1_BLIN: 2A4A1A1.J1 (BL_IN)
2A4A1_BLOUT: 2A4A1A1.J2 (BL_OUT)
2A5A1_BLIN: 2A5A1A1.J1 (BL_IN)
2A5A1_BLOUT: 2A5A1A1.J2 (BL_OUT)
2A7A1A6_HDMI: 2A11A2.1 (HDMI1)
2A7A1J3_BLIN: 2A7A1.J3 (BL_IN), ~.1
2A7A1J4_BLOUT: 2A7A1.1, 2A7A1.J4 (BL_OUT)
2A8A1A2_USB: 2A9A3.~
2A9A1_USB: 2A9A1.~, 2A12A5W2.1
2A9A2_USB: 2A9A1.~, 2A9A2.~
2A9A3_USB: 2A9A2.~, 2A9A3.~
2A11A1_USB: 2A9A1.~, 2A11A1.5 (USB)
2A11A2_USB: 2A9A1.~, 2A11A2.5 (USB)
2A13_USB: 2A9A1.~
2A15A1_USB: 2A15A1.USB
2A15_USB: 2A9A1.~
4A12_USB: 2A9A2.~, 2A12A1W1.1
5A12_USB: 2A9A2.~, 5A11A1W1.1
+3.3V_J1-10: 2A7A1A4.10 (+3.3V)
+3.3V_J6-10: 2A7A1.10 (COIL4)
+5V_J1-12: 2A7A1A4.12 (+5V)
+5V_J3-2: 2A3A1.2 (+5V)
+5V_J3-9: 2A2A1.9 (+5V), 2A4A1.9 (+5V), 2A5A1.9 (+5V)
+5V_J3-11: 2A2A1.11 (+5V), 2A4A1.11 (+5V), 2A5A1.11 (+5V)
+5V_J4-9: 2A2A1.9 (+5V), 2A4A1.9 (+5V), 2A5A1.9 (+5V)
+5V_J4-11: 2A2A1.11 (+5V), 2A4A1.11 (+5V), 2A5A1.11 (+5V)
+5V_J5-7: 2A7A1.7 (+5V)
+5V_J6-12: 2A7A1.12 (+5V)
+5V_J7-2: 2A3A1.2 (+5V)
+5V_J7-7: 2A7A1.7 (+5V)
+5V_J8-1: 2A7A1.1
+12V_ACC_1+: 2A8A1A1.4 (V+)
+12V_ACC_1-: 2A8A1A1.5 (0V)
A0_J3-7: 2A2A1.7 (A0), 2A4A1.7 (A0), 2A5A1.7 (A0)
A0_J7-3: 2A3A1.3 (A0)
A1_J3-5: 2A2A1.5 (A1), 2A4A1.5 (A1), 2A5A1.5 (A1)
A1_J7-1: 2A3A1.1 (12V_PWM)
A2_J3-3: 2A2A1.3 (+5V), 2A4A1.3 (+5V), 2A5A1.3 (+5V)
A3_J3-1: 2A2A1.1 (+12V), 2A4A1.1 (+12V), 2A5A1.1 (+12V)
A10A1_USB: 2A9A1.~, A10A1.1
AMPCD_OFF: 2A3A1RV1SW1.2, 2A3A1W2P1.1
AMPCD_ROT_+5V: 2A3A1RV1.1, 2A3A1W2P1.2
AMPCD_ROT_A: 2A3A1RV1.2, 2A3A1W2P1.3
AMPCD_ROT_GND: 2A3A1RV1.3, 2A3A1RV1SW1.1, 2A3A1W2P1.4
AUXR_ENBL: 2A5A1SW3.1 (A), 2A5A1W3J1.7
BTKA+: 2A12A1W6J1.T, (2A12A1W6).1
BTKA+_LC: (0AxAxWx).T
BTKA-: 2A12A1W6J1.S, ~.1
BTKA-_LC: (0AxAxWx).S
BTKAR_+5V: 2A10W1P1.1, 2A10W1P2.5, (0AxAxWxP2).13
BTKAR_A: 2A10W1P1.2, 2A10W1P2.4, (0AxAxWxP2).14
BTKAR_GND: 2A10W1P1.3, 2A10W1P2.2, 2A10W1P2.3, (0AxAxWxP2).15
BTKA_+12V: ~.1
BTKA_GND: ~.1
CH_A_J1-6: 2A7A1A4.6 (CH_A)
CH_A_J2-1: 2A7A1A4.1 (+5V)
CH_A_J6-6: 2A7A1.6 (GND)
CH_A_J9-1: 2A7A1.1
CH_B_J1-8: 2A7A1A4.8 (CH_B)
CH_B_J2-3: 2A7A1A4.3 (CH_B)
CH_B_J6-8: 2A7A1.8 (LED_DOUT)
CH_B_J9-3: 2A7A1.3 (MC)
COIL1_J1-7: 2A7A1A4.7 (COIL1)
COIL1_J5-1: 2A7A1.1
COIL1_J6-7: 2A7A1.7 (+5V)
COIL1_J7-1: 2A7A1.1
COIL2_J1-9: 2A7A1A4.9 (COIL2)
COIL2_J5-2: 2A7A1.2 (BL_IN)
COIL2_J6-9: 2A7A1.9 (COIL3)
COIL2_J7-2: 2A7A1.2 (BL_IN)
COIL3_J1-3: 2A7A1A4.3 (CH_B)
COIL3_J5-9: 2A7A1.9 (COIL3)
COIL3_J6-3: 2A7A1.3 (MC)
COIL3_J7-9: 2A7A1.9 (COIL3)
COIL4_J1-5: 2A7A1A4.5 (COIL4)
COIL4_J5-10: 2A7A1.10 (COIL4)
COIL4_J6-5: 2A7A1.5 (GND)
COIL4_J7-10: 2A7A1.10 (COIL4)
CRS+: 2A3A1SW2.1, 2A3A1W4P1.1
CRS-: 2A3A1SW2.3, 2A3A1W4P1.3
CRS_GND: 2A3A1SW2.2, 2A3A1W4P1.2
D2-SDA_J3-2: 2A2A1.2 (+3.3V), 2A4A1.2 (+3.3V), 2A5A1.2 (+3.3V)
D4-A6_J3-6: 2A2A1.6 (D4/D6), 2A4A1.6 (D4/D6), 2A5A1.6 (D4/D6)
D4_A4_J4-1: 2A3A1.1 (12V_PWM)
D7_J4-3: 2A3A1.3 (A0)
D7_J4-4: 2A2A1.4 (D7), 2A4A1.4 (D7), 2A5A1.4 (D7)
D8-A8_J4-6: 2A2A1.6 (D4/D6), 2A4A1.6 (D4/D6), 2A5A1.6 (D4/D6)
D8_J5-1: 2A3A1.1 (12V_PWM)
D14-MISO_J4-3: 2A2A1.3 (+5V), 2A4A1.3 (+5V), 2A5A1.3 (+5V)
D15-SCK_J4-1: 2A2A1.1 (+12V), 2A4A1.1 (+12V), 2A5A1.1 (+12V)
D16-MOSI_J4-5: 2A2A1.5 (A1), 2A4A1.5 (A1), 2A5A1.5 (A1)
DISP_BYPASS: 2A5A1SW2.1, 2A5A1W3J1.5
DISP_OFF: 2A5A1SW2.3, 2A5A1W3J1.6
ECM_BIT: 2A5A1SW1.3, 2A5A1W3J1.2
ECM_GND: 2A5A1SW1.C (COM), 2A5A1SW2.2, 2A5A1SW3.2 (B), 2A5A1W3J1.8
ECM_REC: 2A5A1SW1.4, 2A5A1W3J1.3
ECM_STBY: 2A5A1SW1.2, 2A5A1W3J1.1
ECM_XMIT: 2A5A1SW1.5, 2A5A1W3J1.4
GND_J1-14: 2A7A1A4.14 (GND)
GND_J2-2: 2A7A1A4.2 (+3.3V)
GND_J3-6: 2A3A1.6 (GND)
GND_J3-8: 2A2A1.8 (GND), 2A4A1.8 (GND), 2A5A1.8 (GND)
GND_J3-10: 2A2A1.10 (GND), 2A4A1.10 (GND), 2A5A1.10 (GND)
GND_J3-12: 2A2A1.12 (GND), 2A4A1.12 (GND), 2A5A1.12 (GND)
GND_J4-2: 2A3A1.2 (+5V)
GND_J4-10: 2A2A1.10 (GND), 2A4A1.10 (GND), 2A5A1.10 (GND)
GND_J4-12: 2A2A1.12 (GND), 2A4A1.12 (GND), 2A5A1.12 (GND)
GND_J5-2: 2A3A1.2 (+5V)
GND_J5-5: 2A7A1.5 (GND)
GND_J5-6: 2A7A1.6 (GND)
GND_J6-14: 2A7A1.14 (GND)
GND_J7-4: 2A3A1.4 (GND)
GND_J7-5: 2A7A1.5 (GND)
GND_J7-6: 2A7A1.6 (GND)
GND_J8-3: 2A7A1.3 (MC)
GND_J9-2: 2A7A1.2 (BL_IN)
GND_J9-4: 2A7A1.4 (LED_DIN)
GND_J10-2: 2A7A1.2 (BL_IN)
HDG+: 2A3A1SW1.1, 2A3A1W3P1.1
HDG-: 2A3A1SW1.3, 2A3A1W3P1.3
HDG_GND: 2A3A1SW1.2, 2A3A1W3P1.2
IRQ_J3-5: 2A3A1.5 (IRQ)
LC<>ABSIS_PSU_PWR: (0AxAxWx).1
LC<>BL1: (0AxAxWx).1
LC<>BL2: (0AxAxWx).1
LC<>UIP_USB_HUB: (0AxAxWx).1
LC_ABSIS_PWR: 4A13A1W8.1
LC_BL_CH1: 4A13A1W7.1
LC_BL_CH2: 4A13A1W6.1
LED_DIN_J1-13: 2A7A1A4.13 (LED_DIN)
LED_DIN_J5-4: 2A7A1.4 (LED_DIN)
LED_DIN_J6-13: 2A7A1.13 (LED_DIN)
LED_DIN_J7-4: 2A7A1.4 (LED_DIN)
LED_DOUT_J1-1: 2A7A1A4.1 (+5V)
LED_DOUT_J5-8: 2A7A1.8 (LED_DOUT)
LED_DOUT_J6-1: 2A7A1.1
LED_DOUT_J7-8: 2A7A1.8 (LED_DOUT)
LIP_BL_CH1: (4A13A1W7).1
LIP_BL_CH2: (4A13A1W6).1
NC-SPARE_8: (0AxAxWxP2).8
NC-SPARE_16: (0AxAxWxP2).16
NC-SPARE_17: (0AxAxWxP2).17
NC-SPARE_18: (0AxAxWxP2).18
NC-SPARE_19: (0AxAxWxP2).19
NC-SPARE_20: (0AxAxWxP2).20
NC-SPARE_21: (0AxAxWxP2).21
NC-SPARE_22: (0AxAxWxP2).22
NC_SPARE: 2AXXWXP1.8, 2AXXWXP2.8
unnamed: 2A2A1.J1 (BUS_IN), ~.1
unnamed: 2A2A1A1.J3 (INPUTS), ~.1
unnamed: 2A2A1A2.J3 (INPUTS), ~.1
unnamed: 2A2A1A3.1 (+5V), ~.1
unnamed: 2A2A1A3.2 (+5V), ~.2
unnamed: 2A2A1A3.3 (GND), ~.3
unnamed: 2A2A1A3.4 (GND), ~.4
unnamed: 2A2A1A3.CON1 (TFT_DATA), ~.1
unnamed: 2A2A1A3.HDMI (HMDI), ~.1
unnamed: 2A2A1A3.J1 (BLC_IN), ~.1
unnamed: 2A2A1A3.J2 (BLC_OUT), ~.1
unnamed: 2A2A1A3.J6 (KEYBOARD), ~.1
unnamed: 2A2A1A3.~ (LED_BL), ~.1
unnamed: 2A2A1A3A1.1, ~.1
unnamed: 2A2A1A3DS1.P1 (CON1), ~.1
unnamed: 2A2A1A3DS1.P2 (LED_BL), ~.1
unnamed: 2A2A1A4.J1 (BLC_IN), ~.1
unnamed: 2A2A1W1P3.1, 2A2A1W1P5.1
unnamed: 2A2A1W1P3.2, 2A2A1W1P5.2
unnamed: 2A2A1W1P3.3, 2A2A1W1P5.3
unnamed: 2A2A1W1P3.4, 2A2A1W1P6.1
unnamed: 2A2A1W1P3.5, 2A2A1W1P5.5
unnamed: 2A2A1W1P3.6, 2A2A1W1P5.6
unnamed: 2A2A1W1P3.7, 2A2A1W1P6.2
unnamed: 2A2A1W1P3.8, 2A2A1W1P5.4
unnamed: 2A2A1W1P4.1, 2A2A1W1P6.3
unnamed: 2A2A1W1P4.2, 2A2A1W1P6.4
unnamed: 2A2A1W1P4.3, 2A2A1W1P6.5
unnamed: 2A2A1W1P4.4, 2A2A1W1P6.6
unnamed: 2A2A1W1P4.5, 2A2A1W1P7.1
unnamed: 2A2A1W1P4.6, 2A2A1W1P7.2
unnamed: 2A2A1W1P4.7, 2A2A1W1P7.3
unnamed: 2A2A1W1P4.8, 2A2A1W1P7.4
unnamed: 2A2A1W1P4.10, 2A2A1W1P6.7, 2A2A1W1P6.8
unnamed: 2A2A1W1P4.11, 2A2A1W1P7.5
unnamed: 2A2A1W1P4.12, 2A2A1W1P7.6
unnamed: 2A3A1.J1 (BUS_IN), ~.1
unnamed: 2A3A1.J2 (BUS_OUT), ~.1
unnamed: 2A3A1A1.1 (+12V_PWM), ~.1
unnamed: 2A3A1A1.2 (+5V), ~.2
unnamed: 2A3A1A1.3 (SDA), ~.3
unnamed: 2A3A1A1.4 (SCL), ~.4
unnamed: 2A3A1A1.5 (IRQ), ~.5
unnamed: 2A3A1A1.6 (GND), ~.6
unnamed: 2A3A1A2A1.1, ~.1
unnamed: 2A3A1A2DS1.P1 (CON1), ~.1
unnamed: 2A3A1A2DS1.P2 (LED_BL), ~.1
unnamed: 2A3A1A6DS1.P1 (CON1), ~.1
unnamed: 2A3A1A6DS1.P2 (LED_BL), ~.1
unnamed: 2A3A1W1P1.1, 2A3A1W1P2.1
unnamed: 2A3A1W1P1.2, 2A3A1W1P2.2
unnamed: 2A3A1W1P1.3, 2A3A1W1P2.3
unnamed: 2A3A1W1P1.4, 2A3A1W1P2.4
unnamed: 2A3A1W1P1.5, 2A3A1W1P2.5
unnamed: 2A3A1W1P1.6, 2A3A1W1P2.6
unnamed: 2A4A1.J1 (BUS_IN), 4A2A1~.1
unnamed: 2A4A1.J2 (BUS_OUT), 4A2A1~.1
unnamed: 2A4A1A1.1 (+5V), ~.1
unnamed: 2A4A1A1.2 (+5V), ~.2
unnamed: 2A4A1A1.3 (GND), ~.3
unnamed: 2A4A1A1.4 (GND), ~.4
unnamed: 2A4A1A1.CON1 (TFT_DATA), ~.1
unnamed: 2A4A1A1.HDMI (HMDI), ~.1
unnamed: 2A4A1A1.J6 (KEYBOARD), ~.1
unnamed: 2A4A1A1.~ (LED_BL), ~.1
unnamed: 2A4A1W1P3.1, 2A4A1W1P4.1
unnamed: 2A4A1W1P3.2, 2A4A1W1P4.2
unnamed: 2A4A1W1P3.3, 2A4A1W1P4.3
unnamed: 2A4A1W1P3.4, 2A4A1W1P4.4
unnamed: 2A4A1W1P3.5, 2A4A1W1P4.6
unnamed: 2A4A1W1P3.6, 2A4A1W1P4.8
unnamed: 2A4A1W1P3.7, 2A4A1W1P4.10
unnamed: 2A4A1W1P3.8, 2A4A1W1P4.7
unnamed: 2A4A1W1P3.9, 2A4A1W1P4.5
unnamed: 2A4A1W1P3.10, 2A4A1W1P4.9
unnamed: 2A4A1W2P4.1, 2A4A1W2P5.1
unnamed: 2A4A1W2P4.2, 2A4A1W2P5.2
unnamed: 2A4A1W2P4.3, 2A4A1W2P5.3
unnamed: 2A4A1W2P4.4, 2A4A1W2P5.4
unnamed: 2A4A1W2P4.10, 2A4A1W2P5.5
unnamed: 2A5A1.J1 (BUS_IN), 4A2A1~.1
unnamed: 2A5A1.J2 (BUS_OUT), 4A2A1~.1
unnamed: 2A5A1W1P4.1, 2A5A1W1P5.1
unnamed: 2A5A1W1P4.2, 2A5A1W1P6.1
unnamed: 2A5A1W1P4.3, 2A5A1W1P6.2
unnamed: 2A5A1W1P4.4, 2A5A1W1P6.3
unnamed: 2A5A1W1P4.5, 2A5A1W1P6.4
unnamed: 2A5A1W1P4.6, 2A5A1W1P6.5
unnamed: 2A5A1W1P4.7, 2A5A1W1P6.6
unnamed: 2A5A1W1P4.8, 2A5A1W1P6.7
unnamed: 2A5A1W1P4.10, 2A5A1W1P5.2, 2A5A1W1P6.8
unnamed: 2A5A1W2P3.1, 2A5A1W2P4.1
unnamed: 2A5A1W2P3.2, 2A5A1W2P4.2
unnamed: 2A5A1W2P3.3, 2A5A1W2P4.3
unnamed: 2A5A1W2P3.4, 2A5A1W2P5.1
unnamed: 2A5A1W2P3.5, 2A5A1W2P4.4
unnamed: 2A5A1W2P3.8, 2A5A1W2P6.2
unnamed: 2A5A1W2P3.9, 2A5A1W2P6.1
unnamed: 2A7A1.1, 2A7A1.2 (BL_IN)
unnamed: 2A7A1A1SW1.A, 2A7A1A1SW1P1.1
unnamed: 2A7A1A1SW1.B, 2A7A1A1SW1P1.3
unnamed: 2A7A1A1SW1.C, 2A7A1A1SW1P1.2
unnamed: 2A7A1A1SW1.S1, 2A7A1A1SW1P1.5
unnamed: 2A7A1A1SW1.S2, 2A7A1A1SW1P1.4
unnamed: 2A7A1A1SW2.1, 2A7A1A1SW2P1.1
unnamed: 2A7A1A1SW2.2, 2A7A1A1SW2P1.2
unnamed: 2A7A1A2RV1.1, 2A7A1A2RV1P1.1
unnamed: 2A7A1A2RV1.2, 2A7A1A2RV1P1.2
unnamed: 2A7A1A2RV1.3, 2A7A1A2RV1P1.3
unnamed: 2A7A1A4.1 (+5V), 2A7A1A4A1.1, 2A7A1A4DS1.1, 2A7A1A4DS2.1
unnamed: 2A7A1A4.2 (+3.3V), 2A7A1A4A1.2, 2A7A1A4DS1.2, 2A7A1A4DS2.2
unnamed: 2A7A1A4.3 (CH_B), 2A7A1A4A1.3, 2A7A1A4DS1.3, 2A7A1A4DS2.3
unnamed: 2A7A1A4.4 (SD0), 2A7A1A4DS1.4, 2A7A1A4DS2.4
unnamed: 2A7A1A4SW1.A, 2A7A1A4SW1P1.1
unnamed: 2A7A1A4SW1.B, 2A7A1A4SW1P1.3
unnamed: 2A7A1A4SW1.C, 2A7A1A4SW1P1.2
unnamed: 2A7A1A6.1 (+5V), ~.1
unnamed: 2A7A1A6.2 (+5V), ~.2
unnamed: 2A7A1A6.3 (GND), ~.3
unnamed: 2A7A1A6.4 (GND), ~.4
unnamed: 2A7A1A6.CON1 (TFT_DATA), ~.1
unnamed: 2A7A1A6.HDMI (HMDI), ~.1
unnamed: 2A7A1A6.J6 (KEYBOARD), ~.1
unnamed: 2A7A1A6.~ (LED_BL), ~.1
unnamed: 2A7A1A6A1.1, ~.1
unnamed: 2A7A1W1P1.1, 2A7A1W1P4.1
unnamed: 2A7A1W1P1.2, 2A7A1W1P4.2
unnamed: 2A7A1W1P1.3, 2A7A1W1P3.3
unnamed: 2A7A1W1P1.4, 2A7A1W1P3.1
unnamed: 2A7A1W1P1.5, 2A7A1W1P1.6, 2A7A1W1P2.2
unnamed: 2A7A1W1P1.7, 2A7A1W1P2.1
unnamed: 2A7A1W1P1.8, 2A7A1W1P3.2
unnamed: 2A7A1W1P1.9, 2A7A1W1P4.3
unnamed: 2A7A1W1P1.10, 2A7A1W1P4.4
unnamed: 2A7A1W3P1.1, 2A7A1W3P4.1
unnamed: 2A7A1W3P1.2, 2A7A1W3P4.2
unnamed: 2A7A1W3P1.3, 2A7A1W3P3.3
unnamed: 2A7A1W3P1.4, 2A7A1W3P3.1
unnamed: 2A7A1W3P1.5, 2A7A1W3P1.6, 2A7A1W3P2.2
unnamed: 2A7A1W3P1.7, 2A7A1W3P2.1
unnamed: 2A7A1W3P1.8, 2A7A1W3P3.2
unnamed: 2A7A1W3P1.9, 2A7A1W3P4.3
unnamed: 2A7A1W3P1.10, 2A7A1W3P4.4
unnamed: 2A8A1A1.1 (FWD), 2A8A1SW1.1
unnamed: 2A8A1A1.2 (0V), 2A8A1SW1.2, 2A8A1SW2.1
unnamed: 2A8A1A1.3 (REV), 2A8A1SW2.2
unnamed: 2A8A1A1.6 (M1), 2A8A1W1P1.1
unnamed: 2A8A1A1.7 (M2), 2A8A1W1P1.2
unnamed: 2A8A1A2.1, ~.1
unnamed: 2A8A1M1.1 (+), 2A8A1M1J1.1
unnamed: 2A8A1M1.2 (-), 2A8A1M1J1.2
unnamed: 2A9A1.~, ~.1, ~.2
unnamed: 2A9A2.~, ~.1, ~.2
unnamed: 2A9A3.~, ~.1, ~.2
unnamed: 2A10.J1 (POWER_IN), ~.1
unnamed: 2A10.J2 (GND), ~.1
unnamed: 2A10.J3 (RCON), ~.1
unnamed: 2A10.J4 (SPEAKER+), ~.1
unnamed: 2A10.J5 (SPEAKER-), ~.1
unnamed: 2A10.J6 (REMOTE), ~.1
unnamed: 2A10.J7 (LINE_IN_L), ~.1
unnamed: 2A10.J8 (LINE_IN_R), ~.1
unnamed: 2A10A2.1, ~.1
unnamed: 2A12A1W2.1, ~.1
unnamed: 2A12A1W3.1, ~.1
unnamed: 2A12A1W4.1, ~.1
unnamed: 2A12A1W5J1.1, 2A12A1W5J2.1
unnamed: 2A12A1W5J1.2, 2A12A1W5J2.2
unnamed: 2A12A1W5J1.3, 2A12A1W5J2.3
unnamed: 2A12A1W5J1.4, 2A12A1W5J2.4
unnamed: 2A12A1W5J1.5, 2A12A1W5J2.5
unnamed: 2A12A1W5J1.6, 2A12A1W5J2.6
unnamed: 2A12A1W5J1.7, 2A12A1W5J2.7
unnamed: 2A12A1W5J1.8, 2A12A1W5J2.8
unnamed: 2A12A1W5J1.9, 2A12A1W5J3.1
unnamed: 2A12A1W5J1.10, 2A12A1W5J3.2
unnamed: 2A12A1W5J1.11, 2A12A1W5J3.3
unnamed: 2A12A1W5J1.12, 2A12A1W5J3.4
unnamed: 2A12A1W5J1.13, 2A12A1W5J4.1
unnamed: 2A12A1W5J1.14, 2A12A1W5J4.2
unnamed: 2A12A1W5J1.15, 2A12A1W5J4.3
unnamed: 2A12A1W5J1.16, 2A12A1W5J4.4
unnamed: 2A12A5W1.1 (AC_P), ~.1
unnamed: 2A12A5W1.2 (AC_N), ~.2
unnamed: 2A12A5W3J1.1, 2A12A5W3P1.1
unnamed: 2A12A5W3J1.2, 2A12A5W3P1.2
unnamed: 2A12A5W3J1.3, 2A12A5W3P1.3
unnamed: 2A12A5W3J1.4, 2A12A5W3P1.4
unnamed: 2A12A5W3J1.5, 2A12A5W3P1.5
unnamed: 2A12A5W3J1.6, 2A12A5W3P1.6
unnamed: 2A12A5W3J1.7, 2A12A5W3P1.7
unnamed: 2A12A5W3J1.8, 2A12A5W3P1.8
unnamed: 2A14A1.1 (PS_ON), ~.1
unnamed: 2A14A1.2 (+5VSB), ~.2
unnamed: 2A14A1.3 (PWR_OK), ~.3
unnamed: 2A14A1.4 (GND), ~.4
unnamed: 2A15A1.1 (OUT1+), ~.1
unnamed: 2A15A1.2 (+5VSB), ~.2
unnamed: 2A15A1.3 (MASTER_ON), ~.3
unnamed: 2A15A1.4 (DISP_ON), ~.4
unnamed: 2A15A1.5 (OUT3+), ~.5
unnamed: 2A15A1.6 (MAINT_MODE), ~.6
unnamed: 2A15A1.7 (GND), ~.7
unnamed: 2A15A1.8 (NC), ~.8
unnamed: 2AXXWXP1.1, 2AXXWXP2.1
unnamed: 2AXXWXP1.2, 2AXXWXP2.2
unnamed: 2AXXWXP1.3, 2AXXWXP2.3
unnamed: 2AXXWXP1.4, 2AXXWXP2.4
unnamed: 4A1W12.1, ~.1
unnamed: 4A1W13.1, ~.1
unnamed: 4A1W14.1, ~.1
unnamed: 4A1W18.1, ~.1
unnamed: 4A1W19.1, ~.1
unnamed: 5A11A1W2.1, ~.1
unnamed: 5A11A1W3.1, ~.1
unnamed: 5A11A1W4.1, ~.1
unnamed: A10A1.2, ~.1
PUSH_J9-5: 2A7A1.5 (GND)
PUSH_J10-1: 2A7A1.1
RC_ABSIS_PWR: 5A11A1W8.1
RC_BL_CH1: 5A11A1W7.1
RC_BL_CH2: 5A11A1W6.1
RWR_BRT_J8-2: 2A7A1.2 (BL_IN)
RWR_DIS_A: 2A4A1SW1.3
RWR_DIS_F: 2A4A1SW1.5
RWR_DIS_I: 2A4A1SW1.2
RWR_DIS_U: 2A4A1SW1.4
RWR_GND: 2A4A1SW1.C (COM)
SCL_J1-2: 2A7A1A4.2 (+3.3V)
SCL_J3-4: 2A3A1.4 (GND)
SCL_J6-2: 2A7A1.2 (BL_IN)
SDA_J1-4: 2A7A1A4.4 (SD0)
SDA_J3-3: 2A3A1.3 (A0)
SDA_J6-4: 2A7A1.4 (LED_DIN)
SIMPWR_BLM_A: (0AxAxWxP2).9
SIMPWR_BLM_B: (0AxAxWxP2).10
SIMPWR_BLM_GND: (0AxAxWxP2).12
SIMPWR_BLM_PUSH: (0AxAxWxP2).11
SIMPWR_DISP: 2AXXWXP1.4, 2AXXWXP2.4, (0AxAxWxP2).4
SIMPWR_GND: 2AXXWXP1.7, 2AXXWXP2.7, (0AxAxWxP2).7
SIMPWR_MAINT: 2AXXWXP1.6, 2AXXWXP2.6, (0AxAxWxP2).6
SIMPWR_MASTER: 2AXXWXP1.3, 2AXXWXP2.3, (0AxAxWxP2).3
SIMPWR_PCPWR: 2AXXWXP1.1, 2AXXWXP2.1, (0AxAxWxP2).1
SIMPWR_PCRESET: 2AXXWXP1.2, 2AXXWXP2.2, (0AxAxWxP2).2
SIMPWR_PFLT: 2AXXWXP1.5, 2AXXWXP2.5, (0AxAxWxP2).5
TBD_USB: 2A9A2.~
VR_+5V: 2A2A1A3RV1.1, 2A2A1A3W1J1.5
VR_AUTO: 2A2A1A3SW1.3, 2A2A1A3W1J1.2
VR_A_IFEI: 2A2A1A3RV1.2, 2A2A1A3W1J1.4
VR_GND: 2A2A1A3RV1.3, 2A2A1A3SW1.2, 2A2A1A3SW2.2 (B), 2A2A1A3W1J1.6
VR_LDDI: 2A2A1A3SW2.1 (A), 2A2A1A3W1J1.3
VR_MAN: 2A2A1A3SW1.1, 2A2A1A3W1J1.1
ZERO_DETECT_J1-11: 2A7A1A4.11 (ZERO_DETECT)
ZERO_DETECT_J5-3: 2A7A1.3 (MC)
ZERO_DETECT_J6-11: 2A7A1.11 (ZERO_DETECT)
ZERO_DETECT_J7-3: 2A7A1.3 (MC)
~12V~_J3-1: 2A3A1.1 (12V_PWM)
~D3_SCL~_J3-4: 2A2A1.4 (D7), 2A4A1.4 (D7), 2A5A1.4 (D7)
~D6-A7~_J4-2: 2A2A1.2 (+3.3V), 2A4A1.2 (+3.3V), 2A5A1.2 (+3.3V)
~D9-A9~_J4-8: 2A2A1.8 (GND), 2A4A1.8 (GND), 2A5A1.8 (GND)
~D10-A10~_J4-7: 2A2A1.7 (A0), 2A4A1.7 (A0), 2A5A1.7 (A0)
~D10~_A10_J5-3: 2A3A1.3 (A0)

Notes on the sheet:
2X 10AWG
LIP -> LC BULKHEAD
BACKLIGHTING PANELS
2A12A2
6X FL2
LIP -> RC BULKHEAD
2A12A1
DRAFT - DO NOT USE
1. REFERENCE ABSIS-SPEC-001 FOR ABSIS CABLE SPECIFICATION. FL2 TERMINATE UNUSED CONDUCTORS BY FOLDING BACK CONDUCTORS AND HEAT SHRINKING.
NOTES: (UNLESS OTHERWISE SPECIFIED)
GND_J3-12
+5V_J3-11
GND_J3-10
+5V_J3-9
GND_J3-8
A0_J3-7
D4-A6_J3-6
A1_J3-5
~D3_SCL~_J3-4
A2_J3-3
D2-SDA_J3-2
A3_J3-1
GND_J4-12
+5V_J4-11
GND_J4-10
+5V_J4-9
~D9-A9~_J4-8
~D10-A10~_J4-7
D8-A8_J4-6
D16-MOSI_J4-5
D7_J4-4
D14-MISO_J4-3
~D6-A7~_J4-2
D15-SCK_J4-1
OFF
HUD
VIDEO RECORD
UP_SW
DOWN_SW
QTY_SW
ZONE_SW
MODE_SW
ET_SW
GND
LI_SW
LO_SW
CTR_SW
RI_SW
RO_SW
VR_MAN
VR_AUTO
VR_LDDI
VR_A_IFEI
VR_+5V
VR_GND
RENUMBER CABLES
~12V~_J3-1
+5V_J3-2
SDA_J3-3
SCL_J3-4
IRQ_J3-5
GND_J3-6
A1_J7-1
+5V_J7-2
A0_J7-3
GND_J7-4
D8_J5-1
GND_J5-2
~D10~_A10_J5-3
D4_A4_J4-1
GND_J4-2
D7_J4-3
RWR_A_DMR
RWR_LIMIT_SW
RWR_+5V
SPECIAL_SW
RWR_GND
RWR_OFFSET_SW
BIT_SW
RWR_A_AUDIO
POWER_SW
RWR_DIS_N
RWR CONTROL
ECM_OFF
ECM_JETT_SW
AXR_NORM
ECM_GND
ECM/DISP
RWR_DIS_I
RWR_DIS_A
RWR_DIS_U
RWR_DIS_F
ECM_STBY
ECM_BIT
ECM_REC
ECM_XMIT
DISP_BYPASS
DISP_OFF
AUXR_ENBL
COIL3_J5-9
COIL4_J5-10
+5V_J5-7
GND_J5-6
LED_DIN_J5-4
COIL1_J5-2
COIL2_J5-1
CH_A_J2-1
GND_J2-2
CH_B_J2-3
RWR_BRT_+5V
RWR_BRT_A
RWR_BRT_GND
SARI_CH_A
SARI_GND
SARI_CH_B
SARI_CAGE
SARI_TEST
+5V_J1-1
LED_DIN_J2-1
LED_DOUT_J2-2
ZERO_DETECT_J2-3
COIL1_J3-1
COIL2_J3-2
COIL3_J3-4
COIL4_J3-4
COIL1_J5-1
COIL2_J5-2
ZERO_DETECT_J5-3
GND_J5-5
LED_DOUT_J5-8
LED_DOUT_J6-1
SCL_J6-2
COIL3_J6-3
SDA_J6-4
COIL4_J6-5
CH_A_J6-6
COIL1_J6-7
CH_B_J6-8
COIL2_J6-9
+3.3V_J6-10
ZERO_DETECT_J6-11
+5V_J6-12
LED_DIN_J6-13
GND_J6-14
LED_DOUT_J1-1
SCL_J1-2
COIL3_J1-3
SDA_J1-4
COIL4_J1-5
CH_A_J1-6
COIL1_J1-7
CH_B_J1-8
COIL2_J1-9
+3.3V_J1-10
ZERO_DETECT_J1-11
+5V_J1-12
LED_DIN_J1-13
GND_J1-14
AMPCD DISPLAY
IFEI DISPLAY
TO R UIP BULKHEAD
INTERNAL DISPLAYS
GANTRY+12V
GANTRY-
RUDDER PEDALS & GANTRY
CONFIGURE AMP AS FOLLOWS: * INFRASONIC FILTER - OFF * INPUT SENSITIVITY - .2V * BASS BOOST - 0dB * LPF FREQ - 200Hz OR LESS
2X 10 AWG W/
M4 RING TERMINALS
M6 RING TERMINAL
STBY INST DISPLAY
L DDI
R DDI
AMPCD
IFEI
STBY INST
EXPANSION #1
EXPANSION #2
PSU
BUTTKICKER AMP
HDMI TO USB #1
HDMI TO USB #2
AUDIO TO AMP
RUDDER PEDALS
LC USB HUB
RC USB HUB
UIP USB HUB
LIP ABSIS BUS MASTER
LIP USB HUB #2
(2AXXW)
USB HUBS
HDMI TO USB
2A12A3
2A12A4
BL CONTROLLER
PMS
L LIP -> L UIP BULKHEAD
R LIP -> R UIP BULKHEAD
BACKLIGHT CONTROLLER
NC_SPARE
LIP USB HUB #3
