Exprezz0/F-18C_Simulator/ECAD/interconnects/OH_Right_Console.sch

## KiCad design ECAD/interconnects/OH_Right_Console.sch (2023-01-02)

Schematic: OH_Right_Console.sch

Parts:
5A1A: ABSIS HID BUS MASTER
5A1W1, 5A1W2, 5A1W3, 5A1W4, 5A1W5, 5A1W6, 5A1W7, 5A1W8, 5A1W9: ABSIS-CA-A-XXX
5A1W10: ABSIS-CA-A-XXX ***MODIFIED***
5A1W10P2, 5A1W10P3: PP-002D-01
5A1W11, 5A1W12, 5A1W13, 5A1W14, 5A1W15, 5A1W16, 5A1W17, 5A1W18, 5A1W19, 5A1W20, 5A11A1W6, 5A11A1W7: ABSIS-CA-B-XXX
5A1W21, 5A1W22, 5A1W23, 5A1W24, 5A11A1W10: USB MICRO B TO A
5A2, 5A5A1, 5A6A1, 5A7A1, 5A8A1, 5A9A1, 5A10: ABSIS_ALE
5A2A1D1: HOOK IND #1
5A2A1D2: HOOK IND #2
5A2A1R1, 5A2A1R2: 82
5A2A1SW1, 5A10A1SW2: HOOK
5A2A1W1J1, 5A2A2W1J1: SMR-04V-B
5A2A2SW1: WING FOLD UNLOCK
5A2A2SW2: WNG FOLD HOLD
5A2A2SW3: WNG FLD SPREAD
5A2A3: AV COOL
5A2A3SW1: AV COOL SW
5A2A3W1J1: SMR-02V-B
5A2A4: RADAR ALT
5A2A4A1: STANDBY_AIRSPEED_VVI
5A2A4D1: GREEN LED
5A2A4D2: RED LED
5A2A4M1: OFF SERVO
5A2A4RV1: WARN HT POT
5A2A4SW1: PUSH TEST
5A2A4W1P1, 5A2A4W2P1, 5A2A4W3P1, 5A2A4W6P3, 5A2A4W6P4: M20-1060200
5A2A4W4P1, 5A2A4W5P1: M20-1060300
5A2A4W6P1: M20-1070500
5A2A4W6P2: M20-1060400
5A2A7: LDG CHKLST
5A2W1P3, 5A2W1P4, 5A5A1W1P3, 5A5A1W2P4, 5A6A1P3, 5A6A1P4, 5A7A1W1P3, 5A7A1W2P4, 5A8A1W1P3, 5A8A1W2P4, 5A9A1W1P3, 5A9A1W2P4, 5A10W1P3, 5A10W1P4: M20-1070600
5A2W1P6: M20-1070400
5A2W1P7: SMP-02V-BC
5A2W1P8, 5A2W1P9: SMP-04V-BC
5A3A1: CAUTION
5A4A1, 5A4A1A1: DUAL_NEEDLE_GAUGE
5A4A1SW1: L GEN
5A4A1SW2: BATT
5A4A1SW3: R GEN
5A5A1A1, 5A7A1A1, 5A10A1: ABSIS_ALE_Relay_Module
5A5A1L1P1, 5A5A1Y1P1, 5A7A1L1P1, 5A10A2L1P1, 5A10W2P1: PHR-2
5A5A1RV1: TEMP SUIT
5A5A1RV2: TEMP CABIN
5A5A1SW1, 5A6A1SW2, 5A9A1SW1: MODE
5A5A1SW2: CABIN PRESS
5A5A1SW3: PITOT
5A5A1SW4: ENG
5A5A1SW5: BLEED AIR
5A5A1SW6: BLEED AIR AUG
5A5A1Y1: BLEED AIR SOLENOID
5A5A2RV1: DEFOG
5A5A2SW1: WINDSHIELD
5A5A2W1J1, 5A10A2W1J1: SMR-05V-B
5A6A1RV1: CONSOLES
5A6A1RV2: INST PNL
5A6A1RV3: FLOOD
5A6A1RV4: WAR/CAUT
5A6A1RV5: CHART
5A6A1SW1: LT TEST
5A6A1SW3: TIME
5A6A1SW4: TOGGLE
5A6A1SW5: GAME
5A7A1L1: LTD/R ARM
5A7A1SW1: FLIR
5A7A1SW2: LTD/R
5A7A1SW3: LST/NFLR
5A7A1SW4: RADAR
5A7A1SW5: INS
5A8A1SW1: VIEW
5A9A1RV1: VOLUME
5A9A1SW2: CHANNEL
5A9A1SW3: ON/OFF
5A10A1SW1: LDG GEAR
5A10A1SW3: FCS CH 4
5A10A1SW4: FCS CH 3
5A10A1SW5: FCS BIT
5A10A1W1J1: SMR-06V-B
5A10A2L1: CANOPY OPEN
5A10A2SW1: CANOPY
5A10A2SW2: AUX1
5A10A2SW3: AUX2
5A10W1P5, 5A10W1P6: SMP-05V-BC
5A10W1P7: SMP-06V-BC
5A10W2J1: 3814
5A11A1W1: 1681-02C
5A11A1W2: ABSIS-CA-G-XXX
5A11A1W3, 5A11A1W4: ABSIS-CA-F-XXX
5A11A1W5J1: 39-01-2221
5A11A1W8: ABSIS-CA-C-XXX
5A12A1, 5A12A2: B09V6WY1SD
(0AxAxWx): ABSIS-CA-C-XXX
(5A11A1W1): (1681-02C)
(5A11A1W6), (5A11A1W7): (no value)
P3, P4: M20-1070600
P5: M20-1060600
P6: M20-1070200
~: (no value)

Connections:
5A1A_USB: 5A11A1W10.1, 5A12A1.~
5A2A4J3_BLIN: 5A2A4.J3 (BL_IN), ~.1
5A2A4J4_BLOUT: 5A2A4.1 (+5V), 5A2A4.J4 (BL_OUT)
5A4A1J1_BLIN: 5A4A1.J1 (BLC_IN), 5A4A1A1.J1 (BL_IN), ~.1
5A4A1J3_BLOUT: 5A4A1.1, 5A4A1.J3 (BL_OUT), 5A4A1A1.1, 5A4A1A1.J3 (BL_OUT)
5A5A1_USB: 5A1W21.1, 5A12A1.~
5A7A1_USB: 5A1W22.1, 5A12A2.~
5A8A1_USB: 5A1W24.1, 5A12A2.~
5A10_USB: 5A1W23.1, 5A12A2.~
5A12A1_USB: 5A11A1W1.1, (5A11A1W1).1
5A12A2_USB: 5A12A1.~, 5A12A2.~
+5V: 5A1W10P2.1, 5A1W10P3.1
+5V_J3-9: 5A2.9 (+5V), 5A4A1.9 (+5V), 5A5A1A1.9 (+5V), 5A6A1.9 (+5V), 5A7A1A1.9 (+5V), 5A8A1.9 (+5V), 5A9A1.9 (+5V), 5A10A1.9 (+5V)
+5V_J3-11: 5A2.11 (+5V), 5A4A1.11 (+5V), 5A5A1A1.11 (+5V), 5A6A1.11 (+5V), 5A7A1A1.11 (+5V), 5A8A1.11 (+5V), 5A9A1.11 (+5V), 5A10A1.11 (+5V)
+5V_J4-9: 5A2.9 (+5V), 5A4A1.9 (+5V), 5A5A1A1.9 (+5V), 5A6A1.9 (+5V), 5A7A1A1.9 (+5V), 5A8A1.9 (+5V), 5A9A1.9 (+5V), 5A10A1.9 (+5V)
+5V_J4-11: 5A2.11 (+5V), 5A4A1.11 (+5V), 5A5A1A1.11 (+5V), 5A6A1.11 (+5V), 5A7A1A1.11 (+5V), 5A8A1.11 (+5V), 5A9A1.11 (+5V), 5A10A1.11 (+5V)
+5V_J5-7: 5A2A4.7 (+5V), 5A2A4A1.1 (+5V)
+5V_J15-2: 5A2A4.2 (+5V)
+5V_J17-1: 5A2A4.1 (+5V)
A0_J3-7: 5A2.7 (A0), 5A4A1.7 (A0), 5A5A1A1.7 (A0), 5A6A1.7 (A0), 5A7A1A1.7 (A0), 5A8A1.7 (A0), 5A9A1.7 (A0), 5A10A1.7 (A0)
A1_J3-5: 5A2.5 (A1), 5A4A1.5 (A1), 5A5A1A1.5 (A1), 5A6A1.5 (A1), 5A7A1A1.5 (A1), 5A8A1.5 (A1), 5A9A1.5 (A1), 5A10A1.5 (A1)
A2_J3-3: 5A2.3 (+5V), 5A4A1.3 (+5V), 5A5A1A1.3 (+5V), 5A6A1.3 (+5V), 5A7A1A1.3 (+5V), 5A8A1.3 (+5V), 5A9A1.3 (+5V), 5A10A1.3 (+5V)
A3_J3-1: 5A2.1 (+12V), 5A4A1.1, 5A5A1A1.1 (+), 5A6A1.1 (+12V), 5A7A1A1.1 (+), 5A8A1.1 (+12V), 5A9A1.1 (+12V), 5A10A1.1 (+)
AIN_J17-2: 5A2A4.2 (+5V)
AVC_GND: 5A2A3SW1.1 (A), 5A2A3W1J1.2
AVC_SW: 5A2A3SW1.2 (B), 5A2A3W1J1.1
BA_AUG: 5A5A1SW6.2, 5A5A1W2P4.3
BA_LOFF: 5A5A1SW5.4, 5A5A1W2P4.6
BA_OFF: 5A5A1SW5.3, 5A5A1W2P4.5
BA_ROFF: 5A5A1SW5.2, 5A5A1W2P4.4
BL_CH1: 5A11A1W7.1, (5A11A1W7).1
BL_CH2: 5A11A1W6.1, (5A11A1W6).1
CH1_+: 5A5A1A1.1 (+), 5A5A1L1P1.1, 5A7A1A1.1 (+), 5A7A1L1.1 (-), 5A7A1L1P1.1, 5A10A1.1 (+), 5A10A2L1.1 (-), 5A10A2L1P1.1
CH1_-: 5A5A1A1.2 (+3.3V), 5A5A1L1P1.2, 5A7A1A1.2 (+3.3V), 5A7A1L1.2 (+), 5A7A1L1P1.2, 5A10A1.2 (+3.3V), 5A10A2L1.2 (+), 5A10A2L1P1.2
CH2_+: 5A5A1A1.1 (+), 5A5A1Y1.2, 5A5A1Y1P1.1
CH2_-: 5A5A1A1.2 (+3.3V), 5A5A1Y1.1, 5A5A1Y1P1.2
CH_1: 5A9A1SW2.2, 5A9A1W2P4.2
CH_2: 5A9A1SW2.3, 5A9A1W2P4.3
CH_3: 5A9A1SW2.4, 5A9A1W2P4.4
CH_4: 5A9A1SW2.5, 5A9A1W2P4.5
CH_5: 5A9A1SW2.6, 5A9A1W2P4.6
CH_6: 5A9A1SW2.7, 5A9A1W2P4.7
CH_Z1-5: 5A9A1SW2.1, 5A9A1W2P4.1
CH_ZALL: 5A9A1SW2.8, 5A9A1W2P4.8
CN_AUX1: 5A10A2SW2.2, 5A10A2W1J1.3
CN_AUX2: 5A10A2SW3.2, 5A10A2W1J1.4
CN_CLOSE: 5A10A2SW1.3, 5A10A2W1J1.2
CN_GND: 5A10A2SW1.2, 5A10A2SW2.1, 5A10A2SW3.1, 5A10A2W1J1.5
CN_OPEN: 5A10A2SW1.1, 5A10A2W1J1.1
COIL1_J5-2: 5A2A4.2 (+5V), 5A2A4A1.1 (+5V)
COIL2_J5-1: 5A2A4.1 (+5V), 5A2A4A1.2 (COIL2)
COIL3_J5-9: 5A2A4.9 (COIL3), 5A2A4A1.3 (COIL3)
COIL4_J5-10: 5A2A4.10 (COIL4), 5A2A4A1.4 (COIL4)
CP_NORM: 5A5A1SW2.1, 5A5A1W1P3.5
CP_RAM: 5A5A1SW2.3, 5A5A1W1P3.6
D2-SDA_J3-2: 5A2.2 (+3.3V), 5A4A1.2 (+3.3V), 5A5A1A1.2 (+3.3V), 5A6A1.2 (+3.3V), 5A7A1A1.2 (+3.3V), 5A8A1.2 (+3.3V), 5A9A1.2 (+3.3V), 5A10A1.2 (+3.3V)
D4-A6_J3-6: 5A2.6 (D4/D6), 5A4A1.6 (D4/D6), 5A5A1A1.6 (D4/A6), 5A6A1.6 (D4/D6), 5A7A1A1.6 (D4/A6), 5A8A1.6 (D4/D6), 5A9A1.6 (D4/D6), 5A10A1.6 (D4/A6)
D7_J4-4: 5A2.4 (D7), 5A4A1.4 (D7), 5A5A1A1.4 (D7), 5A6A1.4 (D7), 5A7A1A1.4 (D7), 5A8A1.4 (D7), 5A9A1.4 (D7), 5A10A1.4 (D7)
D8-A8_J4-6: 5A2.6 (D4/D6), 5A4A1.6 (D4/D6), 5A5A1A1.6 (D4/A6), 5A6A1.6 (D4/D6), 5A7A1A1.6 (D4/A6), 5A8A1.6 (D4/D6), 5A9A1.6 (D4/D6), 5A10A1.6 (D4/A6)
D14-MISO_J4-3: 5A2.3 (+5V), 5A4A1.3 (+5V), 5A5A1A1.3 (+5V), 5A6A1.3 (+5V), 5A7A1A1.3 (+5V), 5A8A1.3 (+5V), 5A9A1.3 (+5V), 5A10A1.3 (+5V)
D15-SCK_J4-1: 5A2.1 (+12V), 5A4A1.1, 5A5A1A1.1 (+), 5A6A1.1 (+12V), 5A7A1A1.1 (+), 5A8A1.1 (+12V), 5A9A1.1 (+12V), 5A10A1.1 (+)
D16-MOSI_J4-5: 5A2.5 (A1), 5A4A1.5 (A1), 5A5A1A1.5 (A1), 5A6A1.5 (A1), 5A7A1A1.5 (A1), 5A8A1.5 (A1), 5A9A1.5 (A1), 5A10A1.5 (A1)
DF_+5V: 5A5A2RV1.1, 5A5A2W1J1.4
DF_A: 5A5A2RV1.2, 5A5A2W1J1.2
DF_ANTIICE: 5A5A2SW1.1, 5A5A2W1J1.1
DF_GND: 5A5A2RV1.3, 5A5A2SW1.2, 5A5A2W1J1.5
DF_RAIN: 5A5A2SW1.3, 5A5A2W1J1.3
ECS_+5V: 5A5A1RV1.1, 5A5A1RV2.1, 5A5A1W2P4.9
ECS_GND1: 5A5A1SW1.2, 5A5A1SW2.2, 5A5A1SW3.2 (B), 5A5A1SW4.2, 5A5A1SW6.1, 5A5A1W1P3.8
ECS_GND2: 5A5A1RV1.3, 5A5A1RV2.3, 5A5A1SW5.C (COM), 5A5A1W2P4.10
ENG_ON: 5A5A1SW4.1, 5A5A1W2P4.1
ENG_TEST: 5A5A1SW4.3, 5A5A1W2P4.2
FLIR_OFF: 5A7A1SW1.3, 5A7A1W1P3.3
FLIR_ON: 5A7A1SW1.1, 5A7A1W1P3.1
GME_FREEZE: 5A6A1SW5.3, 5A8A1W2P4.8
GME_PAUSE: 5A6A1SW5.1, 5A8A1W2P4.7
GND: 5A1W10P2.2, 5A1W10P3.2
GND_J3-8: 5A2.8 (GND), 5A4A1.8 (GND), 5A5A1A1.8 (GND), 5A6A1.8 (GND), 5A7A1A1.8 (GND), 5A8A1.8 (GND), 5A9A1.8 (GND), 5A10A1.8 (GND)
GND_J3-10: 5A2.10 (GND), 5A4A1.10 (GND), 5A5A1A1.10 (GND), 5A6A1.10 (GND), 5A7A1A1.10 (GND), 5A8A1.10 (GND), 5A9A1.10 (GND), 5A10A1.10 (GND)
GND_J3-12: 5A2.12 (GND), 5A4A1.12 (GND), 5A5A1A1.12 (GND), 5A6A1.12 (GND), 5A7A1A1.12 (GND), 5A8A1.12 (GND), 5A9A1.12 (GND), 5A10A1.12 (GND)
GND_J4-10: 5A2.10 (GND), 5A4A1.10 (GND), 5A5A1A1.10 (GND), 5A6A1.10 (GND), 5A7A1A1.10 (GND), 5A8A1.10 (GND), 5A9A1.10 (GND), 5A10A1.10 (GND)
GND_J4-12: 5A2.12 (GND), 5A4A1.12 (GND), 5A5A1A1.12 (GND), 5A6A1.12 (GND), 5A7A1A1.12 (GND), 5A8A1.12 (GND), 5A9A1.12 (GND), 5A10A1.12 (GND)
GND_J5-5: 5A2A4.5 (GND)
GND_J5-6: 5A2A4.6 (GND), 5A2A4A1.2 (COIL2)
GND_J15-1: 5A2A4.1 (+5V)
GND_J16-2: 5A2A4.2 (+5V)
GND_J17-3: 5A2A4.3 (GND)
GRN_GND_J13-2: 5A2A4.2 (+5V)
GRN_LED_J13-1: 5A2A4.1 (+5V)
HOOK_GND: 5A2A1D1.1 (K), 5A2A1D2.1 (K), 5A2A1SW1.2, 5A2A1W1J1.4
HOOK_SW: 5A2A1SW1.1, 5A2A1W1J1.1
HT_CTR: 5A6A1SW2.3, 5A8A1W2P4.2
HT_FRZE: 5A6A1SW2.1, 5A8A1W2P4.1
INS_CV: 5A7A1SW5.2, 5A7A1W2P4.2
INS_GB: 5A7A1SW5.7, 5A7A1W2P4.7
INS_GND: 5A7A1SW5.3, 5A7A1W2P4.3
INS_GYRO: 5A7A1SW5.6, 5A7A1W2P4.6
INS_IFA: 5A7A1SW5.5, 5A7A1W2P4.5
INS_NAV: 5A7A1SW5.4, 5A7A1W2P4.4
INS_TEST: 5A7A1SW5.8, 5A7A1W2P4.8
KY_+5V: 5A9A1RV1.1, 5A9A1W1P3.9
KY_GND1: 5A9A1RV1.3, 5A9A1SW1.COM, 5A9A1SW3.3, 5A9A1W1P3.8
KY_GND2: 5A9A1SW2.COM, 5A9A1W2P4.10
KY_VOL: 5A9A1RV1.2, 5A9A1W1P3.7
LC<>ABSIS_PSU_PWR: (0AxAxWx).1
LC<>BL1: (0AxAxWx).1
LC<>BL2: (0AxAxWx).1
LC<>UIP_USB_HUB: (0AxAxWx).1
LED_DIN_J5-4: 5A2A4.4 (LED_DIN), 5A2A4A1.1 (+5V)
LED_DOUT_J5-8: 5A2A4.8 (LED_DOUT), 5A2A4A1.2 (COIL2)
LST_ON: 5A7A1SW3.1 (A), 5A7A1W2P4.1
LTDR_ARM: 5A7A1SW2.1 (A), 5A7A1W1P3.4
MODE_C: 5A9A1SW1.2, 5A9A1W1P3.2
MODE_LD: 5A9A1SW1.3, 5A9A1W1P3.3
MODE_P: 5A9A1SW1.1, 5A9A1W1P3.1
MODE_RV: 5A9A1SW1.4, 5A9A1W1P3.4
M_AUTO: 5A5A1SW1.1, 5A5A1W1P3.1
M_OFF: 5A5A1SW1.3, 5A5A1W1P3.3
NC_J5-3: 5A2A4.3 (GND)
unnamed: 5A1A.J1 (POWER), ~.1
unnamed: 5A1A.J2 (BUS_#1), ~.1
unnamed: 5A1A.USB, ~.1
unnamed: 5A1W1.1, ~.1
unnamed: 5A1W2.1, ~.1
unnamed: 5A1W3.1, ~.1
unnamed: 5A1W4.1, ~.1
unnamed: 5A1W5.1, ~.1
unnamed: 5A1W6.1, ~.1
unnamed: 5A1W7.1, ~.1
unnamed: 5A1W8.1, ~.1
unnamed: 5A1W9.1, ~.1
unnamed: 5A1W11.1, ~.1
unnamed: 5A1W12.1, ~.1
unnamed: 5A1W13.1, ~.1
unnamed: 5A1W14.1, ~.1
unnamed: 5A1W15.1, ~.1
unnamed: 5A1W16.1, ~.1
unnamed: 5A1W17.1, ~.1
unnamed: 5A1W18.1, ~.1
unnamed: 5A1W19.1, ~.1
unnamed: 5A1W20.1, ~.1
unnamed: 5A2A1D1.2 (A), 5A2A1R1.1
unnamed: 5A2A1D2.2 (A), 5A2A1R2.1
unnamed: 5A2A3.J1 (BLC_IN), ~.1
unnamed: 5A2A3.J2 (BLC_OUT), ~.1
unnamed: 5A2A4.1 (+5V), 5A2A4.2 (+5V)
unnamed: 5A2A4D1.1 (K), 5A2A4W2P1.2
unnamed: 5A2A4D1.2 (A), 5A2A4W2P1.1
unnamed: 5A2A4D2.1 (K), 5A2A4W3P1.2
unnamed: 5A2A4D2.2 (A), 5A2A4W3P1.1
unnamed: 5A2A4M1.1 (PWM), 5A2A4W5P1.3
unnamed: 5A2A4M1.2 (+), 5A2A4W5P1.2
unnamed: 5A2A4M1.3 (-), 5A2A4W5P1.1
unnamed: 5A2A4RV1.1, 5A2A4W4P1.1
unnamed: 5A2A4RV1.2, 5A2A4W4P1.2
unnamed: 5A2A4RV1.3, 5A2A4W4P1.3
unnamed: 5A2A4SW1.1, 5A2A4W1P1.1
unnamed: 5A2A4SW1.2, 5A2A4W1P1.2
unnamed: 5A2A4W6P1.1, 5A2A4W6P2.2
unnamed: 5A2A4W6P1.2, 5A2A4W6P2.1
unnamed: 5A2A4W6P1.4, 5A2A4W6P4.1
unnamed: 5A2A4W6P1.6, 5A2A4W6P3.2
unnamed: 5A2A4W6P1.7, 5A2A4W6P3.1
unnamed: 5A2A4W6P1.8, 5A2A4W6P4.2
unnamed: 5A2A4W6P1.9, 5A2A4W6P2.3
unnamed: 5A2A4W6P1.10, 5A2A4W6P2.4
unnamed: 5A2A7.J1 (BLC_IN), ~.1
unnamed: 5A2A7.J2 (BLC_OUT), ~.1
unnamed: 5A2W1P3.1, 5A2W1P6.1
unnamed: 5A2W1P3.2, 5A2W1P6.2
unnamed: 5A2W1P3.3, 5A2W1P6.3
unnamed: 5A2W1P3.4, 5A2W1P6.4
unnamed: 5A2W1P3.5, 5A2W1P6.5
unnamed: 5A2W1P3.6, 5A2W1P6.6
unnamed: 5A2W1P3.7, 5A2W1P6.7
unnamed: 5A2W1P3.8, 5A2W1P7.2
unnamed: 5A2W1P4.1, 5A2W1P6.8
unnamed: 5A2W1P4.2, 5A2W1P8.1
unnamed: 5A2W1P4.3, 5A2W1P8.2
unnamed: 5A2W1P4.4, 5A2W1P8.3
unnamed: 5A2W1P4.5, 5A2W1P7.1
unnamed: 5A2W1P4.6, 5A2W1P9.1
unnamed: 5A2W1P4.7, 5A2W1P9.2
unnamed: 5A2W1P4.8, 5A2W1P9.3
unnamed: 5A2W1P4.10, 5A2W1P8.4
unnamed: 5A2W1P4.12, 5A2W1P9.4
unnamed: 5A3A1.J1 (BLC_IN), ~.1
unnamed: 5A3A1.J2 (BLC_OUT), ~.1
unnamed: 5A4A1.J1 (BLC_IN), ~.1
unnamed: 5A4A1.J2 (BLC_OUT), ~.1
unnamed: 5A4A1SW1.1 (A), 5A5A1W1P3.1
unnamed: 5A4A1SW1.2 (B), 5A4A1SW2.2, 5A4A1SW3.2 (B), 5A5A1W1P3.8
unnamed: 5A4A1SW2.1, 5A5A1W1P3.2
unnamed: 5A4A1SW2.3, 5A5A1W1P3.3
unnamed: 5A4A1SW3.1 (A), 5A5A1W1P3.4
unnamed: 5A5A1.J1 (BLC_IN), ~.1
unnamed: 5A5A1.J2 (BLC_OUT), ~.1
unnamed: 5A5A1A1.1 (+), 5A5A1A1.2 (+3.3V)
unnamed: 5A5A1A1.2 (+3.3V), 5A5A1A1.3 (+5V)
unnamed: 5A6A1.J1 (BLC_IN), ~.1
unnamed: 5A6A1.J2 (BLC_OUT), ~.1
unnamed: 5A6A1P3.1, 5A6A1SW1.1 (A)
unnamed: 5A6A1P3.2, 5A6A1SW2.1
unnamed: 5A6A1P3.3, 5A6A1RV4.2
unnamed: 5A6A1P3.4, 5A6A1SW2.3
unnamed: 5A6A1P3.5, 5A6A1RV5.2
unnamed: 5A6A1P3.8, 5A6A1RV4.3, 5A6A1RV5.3, 5A6A1SW1.2 (B), 5A6A1SW2.2
unnamed: 5A6A1P3.9, 5A6A1RV4.1, 5A6A1RV5.1
unnamed: 5A6A1P4.2, 5A6A1RV1.2
unnamed: 5A6A1P4.6, 5A6A1RV2.2
unnamed: 5A6A1P4.7, 5A6A1RV3.2
unnamed: 5A6A1P4.9, 5A6A1RV1.1, 5A6A1RV2.1, 5A6A1RV3.1
unnamed: 5A6A1P4.10, 5A6A1RV1.3, 5A6A1RV2.3, 5A6A1RV3.3
unnamed: 5A7A1.J1 (BLC_IN), ~.1
unnamed: 5A7A1.J2 (BLC_OUT), ~.1
unnamed: 5A7A1A1.1 (+), 5A7A1A1.2 (+3.3V)
unnamed: 5A8A1.J1 (BLC_IN), ~.1
unnamed: 5A8A1.J2 (BLC_OUT), ~.1
unnamed: 5A9A1.J1 (BLC_IN), ~.1
unnamed: 5A9A1.J2 (BLC_OUT), ~.1
unnamed: 5A10A1.1 (+), 5A10A1.2 (+3.3V)
unnamed: 5A10W1P3.1, 5A10W1P7.1
unnamed: 5A10W1P3.2, 5A10W1P7.2
unnamed: 5A10W1P3.3, 5A10W1P7.3
unnamed: 5A10W1P3.4, 5A10W1P7.4
unnamed: 5A10W1P3.5, 5A10W1P7.5
unnamed: 5A10W1P3.8, 5A10W1P7.6
unnamed: 5A10W1P4.1, 5A10W1P5.1
unnamed: 5A10W1P4.2, 5A10W1P5.2
unnamed: 5A10W1P4.3, 5A10W1P5.3
unnamed: 5A10W1P4.4, 5A10W1P6.1
unnamed: 5A10W1P4.5, 5A10W1P6.2
unnamed: 5A10W1P4.6, 5A10W1P6.3
unnamed: 5A10W1P4.7, 5A10W1P6.4
unnamed: 5A10W1P4.9, 5A10W1P5.4
unnamed: 5A10W1P4.10, 5A10W1P5.5
unnamed: 5A10W1P4.12, 5A10W1P6.5
unnamed: 5A10W2J1.1, 5A10W2P1.1
unnamed: 5A10W2J1.2, 5A10W2P1.2
unnamed: 5A11A1W2.1, ~.1
unnamed: 5A11A1W3.1, ~.1
unnamed: 5A11A1W4.1, ~.1
unnamed: 5A11A1W8.1, ~.1
unnamed: 5A12A1.~, ~.1, ~.2
unnamed: 5A12A2.~, ~.1, ~.2
OFF: 5A9A1SW3.4, 5A9A1W1P3.6
PITOT_ON: 5A5A1SW3.1 (A), 5A5A1W1P3.7
PUSH_J16-1: 5A2A4.1 (+5V)
RC_FCS3: 5A10A1SW4.2, 5A10A1W1J1.4
RC_FCS4: 5A10A1SW3.2, 5A10A1W1J1.3
RC_FCSBIT: 5A10A1SW5.1 (A), 5A10A1W1J1.5
RC_GND: 5A10A1SW1.1, 5A10A1SW2.1, 5A10A1SW3.1, 5A10A1SW4.1, 5A10A1SW5.2 (B), 5A10A1W1J1.6
RC_HOOK: 5A10A1SW2.2, 5A10A1W1J1.2
RC_LG: 5A10A1SW1.2, 5A10A1W1J1.1
RDR_EMERG: 5A7A1W1P3.7
RDR_OPR: 5A7A1W1P3.6
RDR_STBY: 5A7A1W1P3.5
RED_GND_J14-2: 5A2A4.2 (+5V)
RED_LED_J14-1: 5A2A4.1 (+5V)
SC_GND: 5A6A1SW2.2, 5A6A1SW3.2, 5A6A1SW4.2, 5A6A1SW5.2, 5A8A1W2P4.10
SNSR_GND1: 5A7A1SW1.2, 5A7A1SW2.2 (B), 5A7A1SW4.COM, 5A7A1W1P3.8
SNSR_GND2: 5A7A1SW3.2 (B), 5A7A1SW5.COM, 5A7A1W2P4.10
TC_A: 5A5A1RV2.2, 5A5A1W2P4.8
TD: 5A9A1SW3.1, 5A9A1W1P3.5
TIME_FAST: 5A6A1SW3.1, 5A8A1W2P4.3
TIME_REAL: 5A6A1SW3.3, 5A8A1W2P4.4
TOG_LABL: 5A6A1SW4.3, 5A8A1W2P4.6
TOG_NVG: 5A6A1SW4.1, 5A8A1W2P4.5
TS_A: 5A5A1RV1.2, 5A5A1W2P4.7
VIEW_CHASE: 5A8A1SW1.2, 5A8A1W1P3.1
VIEW_ENMY: 5A8A1SW1.6, 5A8A1W1P3.5
VIEW_EXT: 5A8A1SW1.3, 5A8A1W1P3.2
VIEW_FLBY: 5A8A1SW1.4, 5A8A1W1P3.3
VIEW_GND: 5A8A1SW1.COM, 5A8A1W1P3.8
VIEW_HUD: 5A8A1SW1.7, 5A8A1W1P3.6
VIEW_MAP: 5A8A1SW1.8, 5A8A1W1P3.7
VIEW_WPN: 5A8A1SW1.5, 5A8A1W1P3.4
WF_GND: 5A2A2SW1.2 (B), 5A2A2SW2.2, 5A2A2SW3.2, 5A2A2W1J1.4
WF_HOLD: 5A2A2SW2.1, 5A2A2W1J1.2
WF_SPREAD: 5A2A2SW3.1, 5A2A2W1J1.3
WF_UNLOCK: 5A2A2SW1.1 (A), 5A2A2W1J1.1
~D3_SCL~_J3-4: 5A2.4 (D7), 5A4A1.4 (D7), 5A5A1A1.4 (D7), 5A6A1.4 (D7), 5A7A1A1.4 (D7), 5A8A1.4 (D7), 5A9A1.4 (D7), 5A10A1.4 (D7)
~D6-A7~_J4-2: 5A2.2 (+3.3V), 5A4A1.2 (+3.3V), 5A5A1A1.2 (+3.3V), 5A6A1.2 (+3.3V), 5A7A1A1.2 (+3.3V), 5A8A1.2 (+3.3V), 5A9A1.2 (+3.3V), 5A10A1.2 (+3.3V)
~D9-A9~_J4-8: 5A2.8 (GND), 5A4A1.8 (GND), 5A5A1A1.8 (GND), 5A6A1.8 (GND), 5A7A1A1.8 (GND), 5A8A1.8 (GND), 5A9A1.8 (GND), 5A10A1.8 (GND)
~D10-A10~_J4-7: 5A2.7 (A0), 5A4A1.7 (A0), 5A5A1A1.7 (A0), 5A6A1.7 (A0), 5A7A1A1.7 (A0), 5A8A1.7 (A0), 5A9A1.7 (A0), 5A10A1.7 (A0)
~DATA~_J15-3: 5A2A4.3 (GND)
~HOOK_IND_1: 5A2A1R1.2, 5A2A1W1J1.2
~HOOK_IND_2: 5A2A1R2.2, 5A2A1W1J1.3

Notes on the sheet:
LIP -> RC BULKHEAD
5A11A1
ALE PLUG REFERENCE ("DUPONT") NOTE: ALL WIRES ARE 26AWG UNLESS OTHERWISE SPECIFIED. ALE P1/P2: 2x6: M20-1070600 (F CRIMP: M20-1160042) ALE P3: 1x6: M20-1060600 (F CRIMP: M20-1160042) ALE P4: 2x2: M20-1070200 (F CRIMP: M20-1160042) USE IWISS SN-28B OR SIMILAR FOR CRIMPING TERMINALS ABSIS TO SEPARATE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
ABSIS-CA-A-XXX CABLE (RS485 BUS CABLE) ("MOLEX MINI-FIT JR") PN: ABSIS-CA-A-XXX (WHERE "XXX" IS WIRE LENGTH IN MM) CONNECTORS: 2X 39-01-3065 (5557-06R-BL) (F CRIMP: 12X 39-00-0211) CONDUCTORS: 6X 16AWG STRANDED/BRAIDED CONDUCTORS, WHITE INSULATION MATES WITH: TYPE-E ABSIS-CA-B-XXX CABLE (BL BUS CAB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
D15-SCK_J4-1
~D6-A7~_J4-2
D14-MISO_J4-3
D7_J4-4
D16-MOSI_J4-5
D8-A8_J4-6
~D10-A10~_J4-7
~D9-A9~_J4-8
+5V_J4-9
GND_J4-10
+5V_J4-11
GND_J4-12
A3_J3-1
D2-SDA_J3-2
A2_J3-3
~D3_SCL~_J3-4
A1_J3-5
D4-A6_J3-6
A0_J3-7
GND_J3-8
+5V_J3-9
GND_J3-10
+5V_J3-11
GND_J3-12
CONNECT NORMALLY OPEN
HOOK LEVER
WING FOLD
AV COOL
HYD PRESS GAUGE
COIL1
COIL2
COIL3
COIL4
COIL5
COIL6
COIL7
COIL8
~HOOK_IND_1
~HOOK_IND_2
HOOK_SW
HOOK_GND
WF_GND
WF_SPREAD
WF_HOLD
WF_UNLOCK
AVC_SW
AVC_GND
DUAL ROW DUPONT M20-1070200 - 4 POS M20-1070300 - 6 POS M20-1070400 - 8 POS M20-1070500 - 10 POS M20-1070600 - 12 POS M20-1070700 - 14 POS M20-1070800 - 16 POS M20-1070900 - 18 POS M20-1071000 - 20 POS M20-1071100 - 22 POS M20-1071200 - 24 POS SINGLE ROW DUPONT M20-1060200 - 2 POS M20-1060300 - 3 P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
BATT GAUGE
ELEC PANEL
ECS PANEL
INTR LT PANEL
SNSR PANEL
NORM
OFF
ORIDE
TEST
NITE
NVG
DAY
FRZE
CTR
FAST
REAL
LABL
PAUSE
FREEZE
SIM CNTL PANEL
KY58 PANEL
SAFE
STBY
AUTO
MAN
DUMP
R CRKT BRKR
HOLD
HID INPUT
CANOPY
DEFOG PANEL
DF_ANTIICE
DF_RAIN
DF_A
DF_+5V
DF_GND
CN_OPEN
CN_CLOSE
CN_AUX1
CN_AUX2
CN_GND
RC_LG
RC_HOOK
RC_FCS4
RC_FCS3
RC_FCSBIT
RC_GND
CH1_+
CH1_-
BACKLIGHTING PANELS
***5A1W10 MODIFIED*** +5V/GND LINES ONLY REMOVE SECOND CONNECTOR TERMINATE AS SHOWN TO CREATE P2/P3
1. REFERENCE ABSIS-SPEC-001 FOR ABSIS CABLE SPECIFICATION. FL2 TERMINATE UNUSED CONDUCTORS BY FOLDING BACK CONDUCTORS AND HEAT SHRINKING.
NOTES: (UNLESS OTHERWISE SPECIFIED)
DRAFT - DO NOT USE
GND_J5-6
GND_J5-5
GND_J5-4
GND_J5-3
GND_J5-2
GND_J5-1
GND_J6-4
+5V_J6-3
+3.3V_J6-2
+12V_J6-1
+5V_J6-20
GND_J6-19
+5V_J6-18
GND_J6-17
D23_J6-16
D22_J6-15
D25_J6-14
D24_J6-13
D27_J6-12
D26_J6-11
D29_J6-10
D28_J6-9
D31_J6-8
D30_J6-7
D33_J6-6
D32_J6-5
D35_J6-4
D34_J6-3
D37_J6-2
D36_J6-1
GND_J4-20
+5V_J4-19
GND_J4-18
+5V_J4-17
A8_J4-16
A7_J4-15
A9_J4-14
A10_J4-12
A6_J4-13
A5_J4-11
A11_J4-10
A4_J4-9
A12_J4-8
A3_J4-7
A13_J4-6
A2_J4-5
A14_J4-4
A1_J4-3
A15_J4-2
A0_J4-1
+5V_J5-20
GND_J5-19
+5V_J5-18
GND_J5-17
D39_J5-16
D38_J5-15
D41_J5-14
D40_J5-13
D43_J5-12
D42_J5-11
D45_J5-10
D44_J5-9
D47_J5-8
D46_J5-7
D49_J5-6
D48_J5-5
D51_J5-4
D50_J5-3
D53_J5-2
D52_J5-1
GND_J3-22
GND_J3-21
GND_J3-20
~D4_J3-19
D21_J3-18
~D5_J3-17
D20_J3-16
~D6_J3-15
D19_J3-14
~D7_J3-13
D18_J3-12
~D8_J3-11
D17_J3-10
~D9_J3-9
D16_J3-8
D10_J3-7
D15_J3-6
D11_J3-5
D14_J3-4
D12_J3-3
~D3_J3-2
~D13_J3-1
GND_J7-4
+5V_J7-3
