Exprezz0/F-18C_Simulator/ECAD/interconnects/OH_Upper_Instrument_Panel.sch

## KiCad design ECAD/interconnects/OH_Upper_Instrument_Panel.sch (2023-01-02)

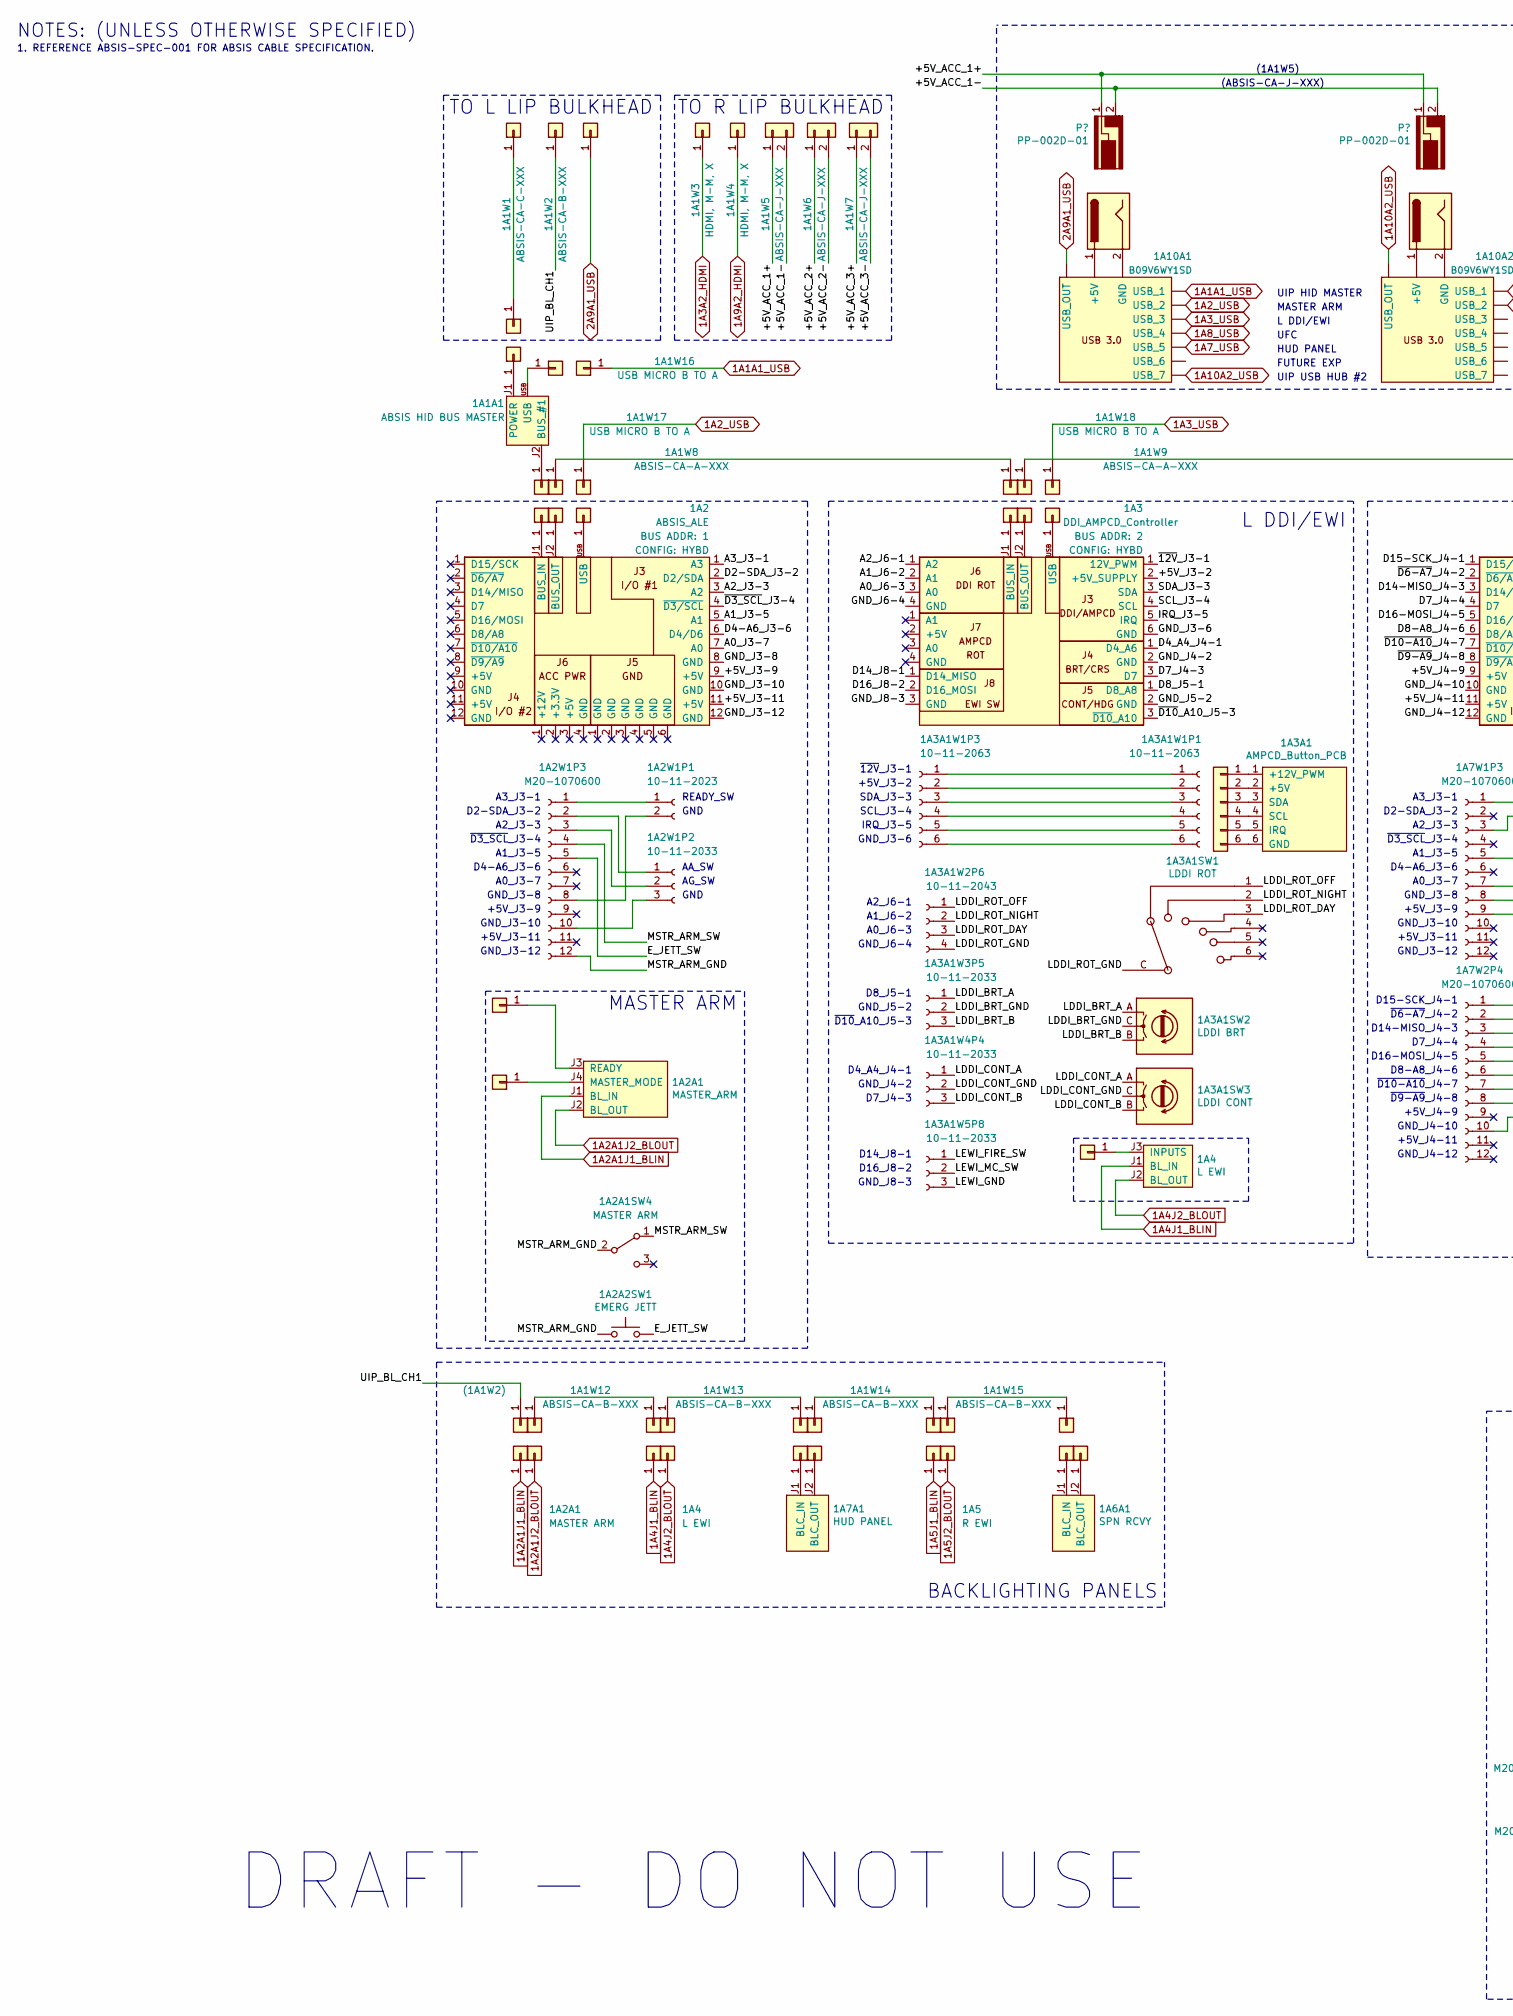
[picture p357: schematic OH_Upper_Instrument_Panel.sch, part in row 1, column 1]

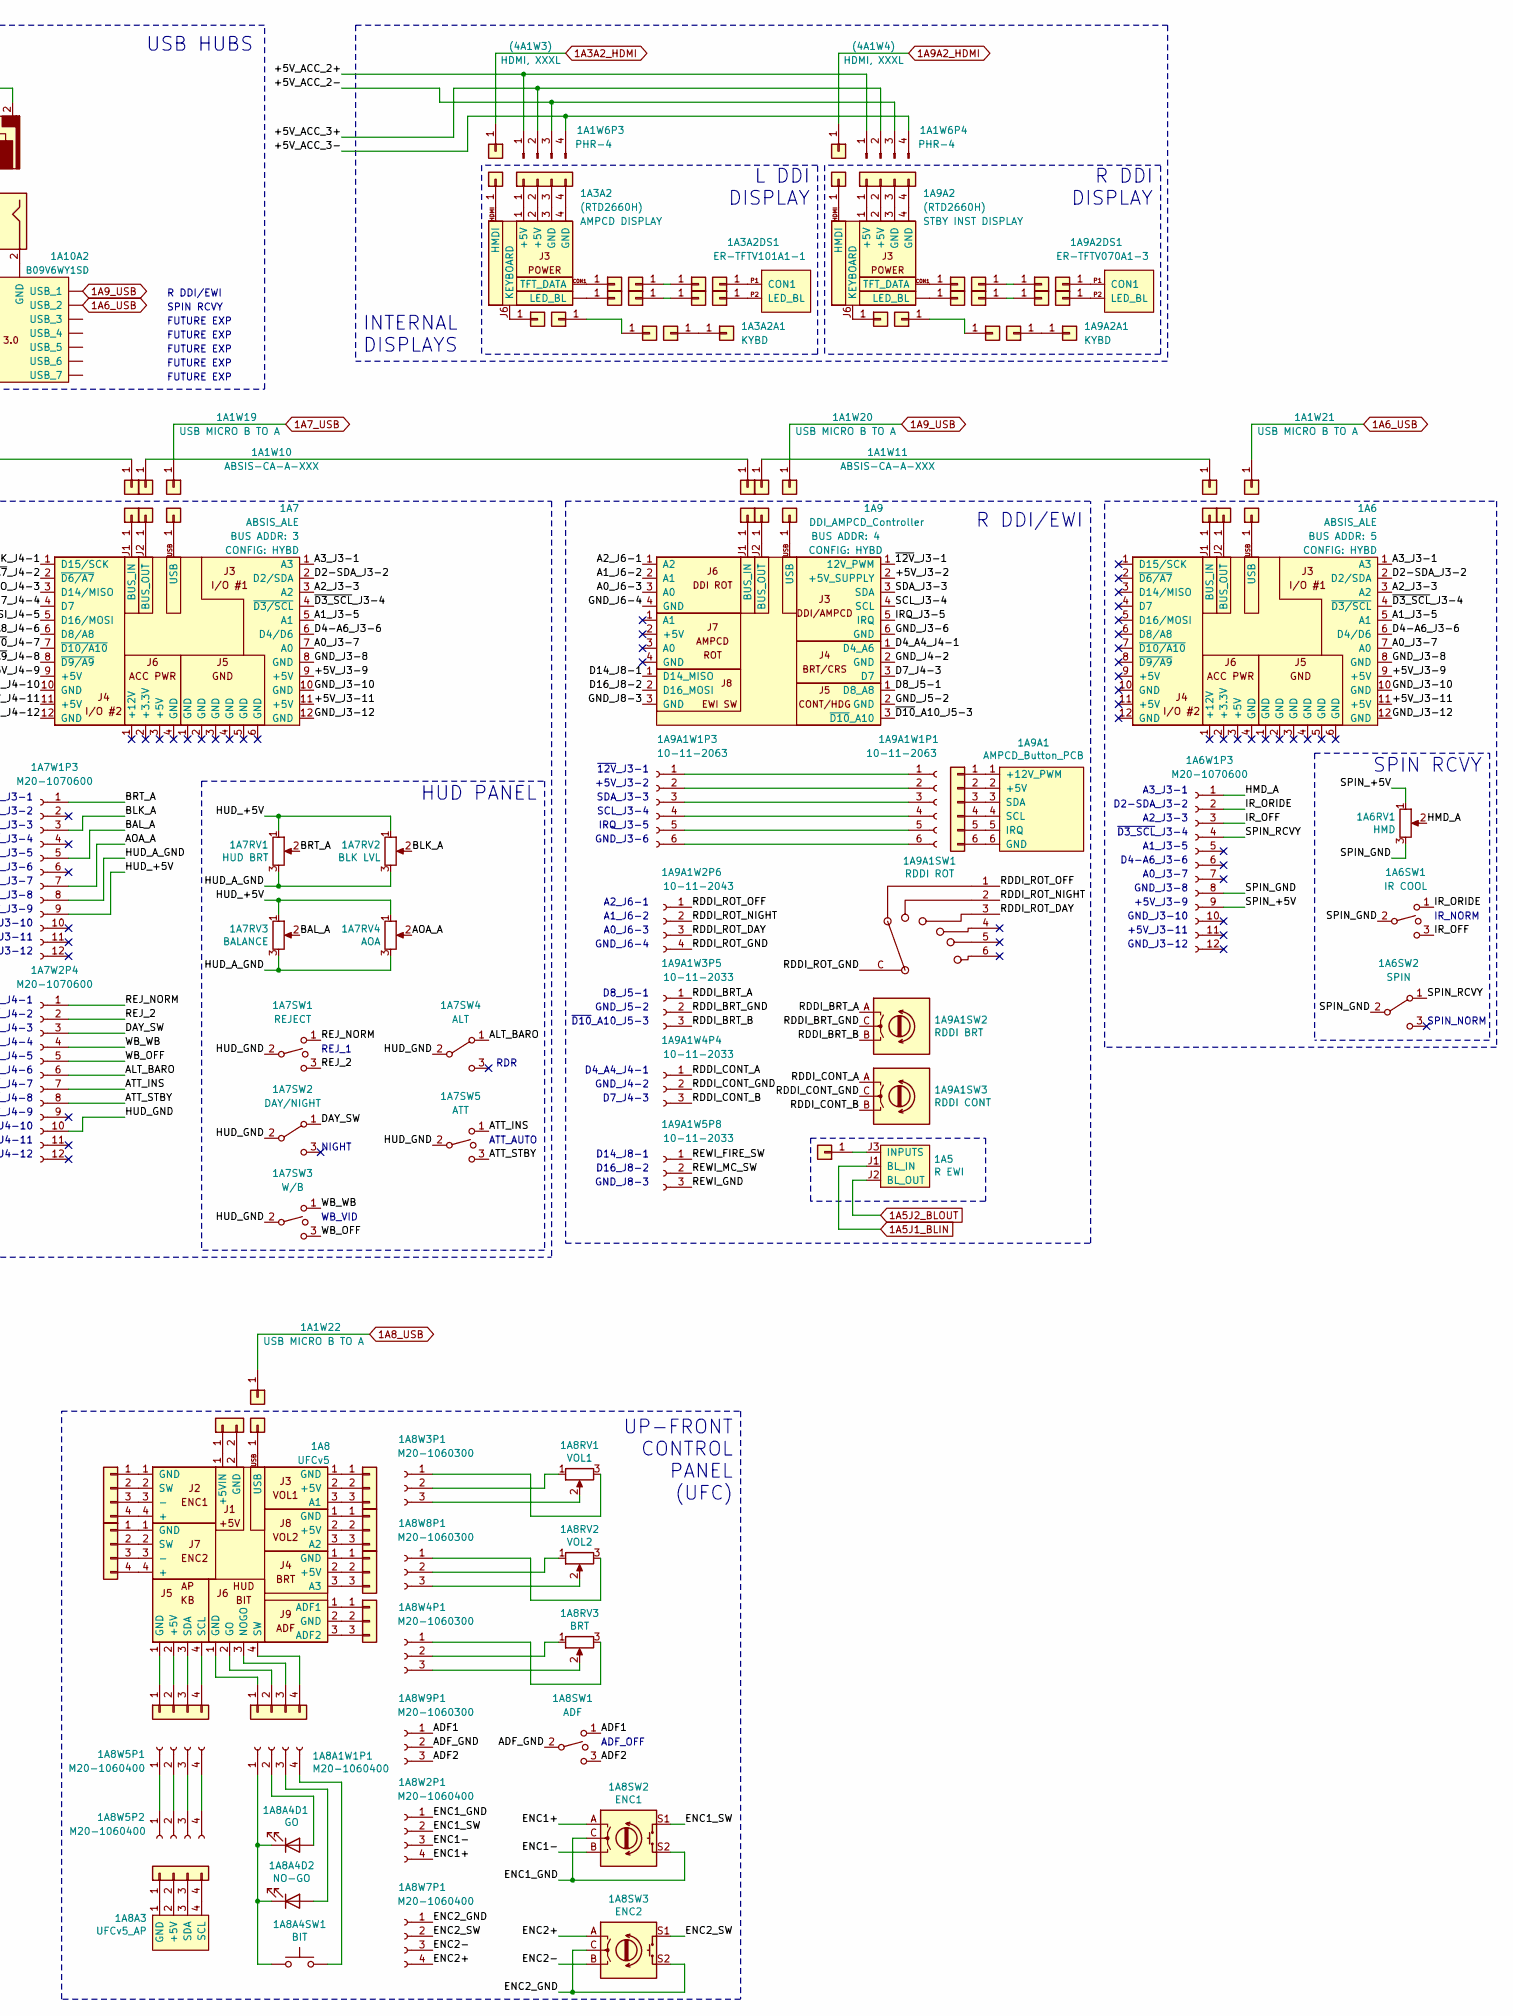
[picture p358: schematic OH_Upper_Instrument_Panel.sch, part in row 1, column 2]

Parts:
1A1A1: ABSIS HID BUS MASTER
1A1W1: ABSIS-CA-C-XXX
1A1W2, 1A1W12, 1A1W13, 1A1W14, 1A1W15: ABSIS-CA-B-XXX
1A1W3, 1A1W4: HDMI, M-M, X
1A1W5, 1A1W6, 1A1W7: ABSIS-CA-J-XXX
1A1W6P3, 1A1W6P4: PHR-4
1A1W8, 1A1W9, 1A1W10, 1A1W11: ABSIS-CA-A-XXX
1A1W16, 1A1W17, 1A1W18, 1A1W19, 1A1W20, 1A1W21, 1A1W22: USB MICRO B TO A
1A2, 1A6, 1A7: ABSIS_ALE
1A2A1: MASTER_ARM
1A2A1SW4: MASTER ARM
1A2A2SW1: EMERG JETT
1A2W1P1: 10-11-2023
1A2W1P2, 1A3A1W3P5, 1A3A1W4P4, 1A3A1W5P8, 1A9A1W3P5, 1A9A1W4P4, 1A9A1W5P8: 10-11-2033
1A2W1P3, 1A6W1P3, 1A7W1P3, 1A7W2P4: M20-1070600
1A3, 1A9: DDI_AMPCD_Controller
1A3A1, 1A9A1: AMPCD_Button_PCB
1A3A1SW1: LDDI ROT
1A3A1SW2: LDDI BRT
1A3A1SW3: LDDI CONT
1A3A1W1P1, 1A3A1W1P3, 1A9A1W1P1, 1A9A1W1P3: 10-11-2063
1A3A1W2P6, 1A9A1W2P6: 10-11-2043
1A3A2, 1A9A2: (RTD2660H)
1A3A2A1, 1A9A2A1: KYBD
1A3A2DS1: ER-TFTV101A1-1
1A4: L EWI
1A5: R EWI
1A6A1: SPN RCVY
1A6RV1: HMD
1A6SW1: IR COOL
1A6SW2: SPIN
1A7A1: HUD PANEL
1A7RV1: HUD BRT
1A7RV2: BLK LVL
1A7RV3: BALANCE
1A7RV4: AOA
1A7SW1: REJECT
1A7SW2: DAY/NIGHT
1A7SW3: W/B
1A7SW4: ALT
1A7SW5: ATT
1A8: UFCv5
1A8A1W1P1, 1A8W2P1, 1A8W5P1, 1A8W5P2, 1A8W7P1: M20-1060400
1A8A3: UFCv5_AP
1A8A4D1: GO
1A8A4D2: NO-GO
1A8A4SW1: BIT
1A8RV1: VOL1
1A8RV2: VOL2
1A8RV3: BRT
1A8SW1: ADF
1A8SW2: ENC1
1A8SW3: ENC2
1A8W3P1, 1A8W4P1, 1A8W8P1, 1A8W9P1: M20-1060300
1A9A1SW1: RDDI ROT
1A9A1SW2: RDDI BRT
1A9A1SW3: RDDI CONT
1A9A2DS1: ER-TFTV070A1-3
1A10A1, 1A10A2: B09V6WY1SD
4A2A1~: (no value)
(1A1W2): (no value)
(4A1W3), (4A1W4): HDMI, XXXL
~: (no value)

Connections:
1A1A1_USB: 1A1W16.1, 1A10A1.~
1A2A1J1_BLIN: 1A2A1.J1 (BL_IN), ~.1
1A2A1J2_BLOUT: 1A2A1.1, 1A2A1.J2 (BL_OUT)
1A2_USB: 1A1W17.1, 1A10A1.~
1A3A2_HDMI: 1A1W3.1, (4A1W3).1
1A3_USB: 1A1W18.1, 1A10A1.~
1A4J1_BLIN: 1A4.J1 (BL_IN), ~.1
1A4J2_BLOUT: 1A4.1, 1A4.J2 (BL_OUT)
1A5J1_BLIN: 1A5.J1 (BL_IN), ~.1
1A5J2_BLOUT: 1A5.1, 1A5.J2 (BL_OUT)
1A6_USB: 1A1W21.1, 1A10A2.~
1A7_USB: 1A1W19.1, 1A10A1.~
1A8_USB: 1A1W22.1, 1A10A1.~
1A9A2_HDMI: 1A1W4.1, (4A1W4).1
1A9_USB: 1A1W20.1, 1A10A2.~
1A10A2_USB: 1A10A1.~, 1A10A2.~
2A9A1_USB: 1A10A1.~
+5V_ACC_1+: 1A1W5.1
+5V_ACC_1-: 1A1W5.2
+5V_ACC_2+: 1A1W6.1, 1A1W6P3.1, 1A1W6P4.1
+5V_ACC_2-: 1A1W6.2, 1A1W6P3.3, 1A1W6P4.3
+5V_ACC_3+: 1A1W6P3.2, 1A1W6P4.2, 1A1W7.1
+5V_ACC_3-: 1A1W6P3.4, 1A1W6P4.4, 1A1W7.2
+5V_J3-2: 1A3.2 (+5V), 1A9.2 (+5V)
+5V_J3-9: 1A2.9 (+5V), 1A6.9 (+5V), 1A7.9 (+5V)
+5V_J3-11: 1A2.11 (+5V), 1A6.11 (+5V), 1A7.11 (+5V)
+5V_J4-9: 1A7.9 (+5V)
+5V_J4-11: 1A7.11 (+5V)
A0_J3-7: 1A2.7 (A0), 1A6.7 (A0), 1A7.7 (A0)
A0_J6-3: 1A3.3 (A0), 1A9.3 (A0)
A1_J3-5: 1A2.5 (A1), 1A6.5 (A1), 1A7.5 (A1)
A1_J6-2: 1A3.2 (+5V), 1A9.2 (+5V)
A2_J3-3: 1A2.3 (+5V), 1A6.3 (+5V), 1A7.3 (+5V)
A2_J6-1: 1A3.1 (12V_PWM), 1A9.1 (12V_PWM)
A3_J3-1: 1A2.1 (+12V), 1A6.1 (+12V), 1A7.1 (+12V)
ADF1: 1A8SW1.1, 1A8W9P1.1
ADF2: 1A8SW1.3, 1A8W9P1.3
ADF_GND: 1A8SW1.2, 1A8W9P1.2
ALT_BARO: 1A7SW4.1 (A), 1A7W2P4.6
AOA_A: 1A7RV4.2, 1A7W1P3.7
ATT_INS: 1A7SW5.1, 1A7W2P4.7
ATT_STBY: 1A7SW5.3, 1A7W2P4.8
BAL_A: 1A7RV3.2, 1A7W1P3.5
BLK_A: 1A7RV2.2, 1A7W1P3.3
BRT_A: 1A7RV1.2, 1A7W1P3.1
D2-SDA_J3-2: 1A2.2 (+3.3V), 1A6.2 (+3.3V), 1A7.2 (+3.3V)
D4-A6_J3-6: 1A2.6 (D4/D6), 1A6.6 (D4/D6), 1A7.6 (D4/D6)
D4_A4_J4-1: 1A3.1 (12V_PWM), 1A9.1 (12V_PWM)
D7_J4-3: 1A3.3 (A0), 1A9.3 (A0)
D7_J4-4: 1A7.4 (D7)
D8-A8_J4-6: 1A7.6 (D4/D6)
D8_J5-1: 1A3.1 (12V_PWM), 1A9.1 (12V_PWM)
D14-MISO_J4-3: 1A7.3 (+5V)
D14_J8-1: 1A3.1 (12V_PWM), 1A9.1 (12V_PWM)
D15-SCK_J4-1: 1A7.1 (+12V)
D16-MOSI_J4-5: 1A7.5 (A1)
D16_J8-2: 1A3.2 (+5V), 1A9.2 (+5V)
DAY_SW: 1A7SW2.1 (A), 1A7W2P4.3
ENC1+: 1A8SW2.A, 1A8W2P1.4
ENC1-: 1A8SW2.B, 1A8W2P1.3
ENC1_GND: 1A8SW2.C, 1A8SW2.S2, 1A8W2P1.1
ENC1_SW: 1A8SW2.S1, 1A8W2P1.2
ENC2+: 1A8SW3.A, 1A8W7P1.4
ENC2-: 1A8SW3.B, 1A8W7P1.3
ENC2_GND: 1A8SW3.C, 1A8SW3.S2, 1A8W7P1.1
ENC2_SW: 1A8SW3.S1, 1A8W7P1.2
E_JETT_SW: 1A2A2SW1.2, 1A2W1P3.5
GND_J3-6: 1A3.6 (GND), 1A9.6 (GND)
GND_J3-8: 1A2.8 (GND), 1A6.8 (GND), 1A7.8 (GND)
GND_J3-10: 1A2.10 (GND), 1A6.10 (GND), 1A7.10 (GND)
GND_J3-12: 1A2.12 (GND), 1A6.12 (GND), 1A7.12 (GND)
GND_J4-2: 1A3.2 (+5V), 1A9.2 (+5V)
GND_J4-10: 1A7.10 (GND)
GND_J4-12: 1A7.12 (GND)
GND_J5-2: 1A3.2 (+5V), 1A9.2 (+5V)
GND_J6-4: 1A3.4 (GND), 1A9.4 (GND)
GND_J8-3: 1A3.3 (A0), 1A9.3 (A0)
HMD_A: 1A6RV1.2, 1A6W1P3.1
HUD_+5V: 1A7RV1.1, 1A7RV2.1, 1A7RV3.1, 1A7RV4.1, 1A7W1P3.9
HUD_A_GND: 1A7RV1.3, 1A7RV2.3, 1A7RV3.3, 1A7RV4.3, 1A7W1P3.8
HUD_GND: 1A7SW1.2, 1A7SW2.2 (B), 1A7SW3.2, 1A7SW4.2 (B), 1A7SW5.2, 1A7W2P4.10
IRQ_J3-5: 1A3.5 (IRQ), 1A9.5 (IRQ)
IR_OFF: 1A6SW1.3, 1A6W1P3.3
IR_ORIDE: 1A6SW1.1, 1A6W1P3.2
LDDI_BRT_A: 1A3A1SW2.A, 1A3A1W3P5.1
LDDI_BRT_B: 1A3A1SW2.B, 1A3A1W3P5.3
LDDI_BRT_GND: 1A3A1SW2.C, 1A3A1W3P5.2
LDDI_CONT_A: 1A3A1SW3.A, 1A3A1W4P4.1
LDDI_CONT_B: 1A3A1SW3.B, 1A3A1W4P4.3
LDDI_CONT_GND: 1A3A1SW3.C, 1A3A1W4P4.2
LDDI_ROT_DAY: 1A3A1SW1.3, 1A3A1W2P6.3
LDDI_ROT_GND: 1A3A1SW1.C (COM), 1A3A1W2P6.4
LDDI_ROT_NIGHT: 1A3A1SW1.2, 1A3A1W2P6.2
LDDI_ROT_OFF: 1A3A1SW1.1, 1A3A1W2P6.1
LEWI_FIRE_SW: 1A3A1W5P8.1
LEWI_GND: 1A3A1W5P8.3
LEWI_MC_SW: 1A3A1W5P8.2
MSTR_ARM_GND: 1A2A1SW4.2 (B), 1A2A2SW1.1, 1A2W1P3.12
MSTR_ARM_SW: 1A2A1SW4.1 (A), 1A2W1P3.4
unnamed: 1A1W12.1, ~.1
unnamed: 1A1W13.1, ~.1
unnamed: 1A1W14.1, ~.1
unnamed: 1A1W15.1, ~.1
unnamed: 1A2W1P1.1, 1A2W1P3.1
unnamed: 1A2W1P1.2, 1A2W1P3.8
unnamed: 1A2W1P2.1, 1A2W1P3.2
unnamed: 1A2W1P2.2, 1A2W1P3.3
unnamed: 1A2W1P2.3, 1A2W1P3.10
unnamed: 1A3.J1 (BUS_IN), ~.1
unnamed: 1A3.J2 (BUS_OUT), ~.1
unnamed: 1A3A1.1 (+12V_PWM), ~.1
unnamed: 1A3A1.2 (+5V), ~.2
unnamed: 1A3A1.3 (SDA), ~.3
unnamed: 1A3A1.4 (SCL), ~.4
unnamed: 1A3A1.5 (IRQ), ~.5
unnamed: 1A3A1.6 (GND), ~.6
unnamed: 1A3A1W1P1.1, 1A3A1W1P3.1
unnamed: 1A3A1W1P1.2, 1A3A1W1P3.2
unnamed: 1A3A1W1P1.3, 1A3A1W1P3.3
unnamed: 1A3A1W1P1.4, 1A3A1W1P3.4
unnamed: 1A3A1W1P1.5, 1A3A1W1P3.5
unnamed: 1A3A1W1P1.6, 1A3A1W1P3.6
unnamed: 1A3A2.1 (+5V), ~.1
unnamed: 1A3A2.2 (+5V), ~.2
unnamed: 1A3A2.3 (GND), ~.3
unnamed: 1A3A2.4 (GND), ~.4
unnamed: 1A3A2.CON1 (TFT_DATA), ~.1
unnamed: 1A3A2.HDMI (HMDI), ~.1
unnamed: 1A3A2.J6 (KEYBOARD), ~.1
unnamed: 1A3A2.~ (LED_BL), ~.1
unnamed: 1A3A2A1.1, ~.1
unnamed: 1A3A2DS1.P1 (CON1), ~.1
unnamed: 1A3A2DS1.P2 (LED_BL), ~.1
unnamed: 1A4.J3 (INPUTS), ~.1
unnamed: 1A5.J3 (INPUTS), ~.1
unnamed: 1A6A1.J1 (BLC_IN), 4A2A1~.1
unnamed: 1A6A1.J2 (BLC_OUT), 4A2A1~.1
unnamed: 1A7A1.J1 (BLC_IN), 4A2A1~.1
unnamed: 1A7A1.J2 (BLC_OUT), 4A2A1~.1
unnamed: 1A8.1 (+5VIN), ~.1
unnamed: 1A8.2 (+5V), ~.2
unnamed: 1A8.3 (-), ~.3
unnamed: 1A8.4 (+), ~.4
unnamed: 1A8.USB, 4A2A1~.1
unnamed: 1A8A1W1P1.1, 1A8A4D1.1 (K), 1A8A4D2.1 (K), 1A8A4SW1.1
unnamed: 1A8A1W1P1.2, 1A8A4D1.2 (A)
unnamed: 1A8A1W1P1.3, 1A8A4D2.2 (A)
unnamed: 1A8A1W1P1.4, 1A8A4SW1.2
unnamed: 1A8A3.1 (GND), ~.1
unnamed: 1A8A3.2 (+5V), ~.2
unnamed: 1A8A3.3 (SDA), ~.3
unnamed: 1A8A3.4 (SCL), ~.4
unnamed: 1A8RV1.1, 1A8W3P1.2
unnamed: 1A8RV1.2, 1A8W3P1.3
unnamed: 1A8RV1.3, 1A8W3P1.1
unnamed: 1A8RV2.1, 1A8W8P1.2
unnamed: 1A8RV2.2, 1A8W8P1.3
unnamed: 1A8RV2.3, 1A8W8P1.1
unnamed: 1A8RV3.1, 1A8W4P1.2
unnamed: 1A8RV3.2, 1A8W4P1.3
unnamed: 1A8RV3.3, 1A8W4P1.1
unnamed: 1A8W5P1.1, 1A8W5P2.1
unnamed: 1A8W5P1.2, 1A8W5P2.2
unnamed: 1A8W5P1.3, 1A8W5P2.3
unnamed: 1A8W5P1.4, 1A8W5P2.4
unnamed: 1A9.J1 (BUS_IN), ~.1
unnamed: 1A9.J2 (BUS_OUT), ~.1
unnamed: 1A9A1.1 (+12V_PWM), ~.1
unnamed: 1A9A1.2 (+5V), ~.2
unnamed: 1A9A1.3 (SDA), ~.3
unnamed: 1A9A1.4 (SCL), ~.4
unnamed: 1A9A1.5 (IRQ), ~.5
unnamed: 1A9A1.6 (GND), ~.6
unnamed: 1A9A1W1P1.1, 1A9A1W1P3.1
unnamed: 1A9A1W1P1.2, 1A9A1W1P3.2
unnamed: 1A9A1W1P1.3, 1A9A1W1P3.3
unnamed: 1A9A1W1P1.4, 1A9A1W1P3.4
unnamed: 1A9A1W1P1.5, 1A9A1W1P3.5
unnamed: 1A9A1W1P1.6, 1A9A1W1P3.6
unnamed: 1A9A2.1 (+5V), ~.1
unnamed: 1A9A2.2 (+5V), ~.2
unnamed: 1A9A2.3 (GND), ~.3
unnamed: 1A9A2.4 (GND), ~.4
unnamed: 1A9A2.CON1 (TFT_DATA), ~.1
unnamed: 1A9A2.HDMI (HMDI), ~.1
unnamed: 1A9A2.J6 (KEYBOARD), ~.1
unnamed: 1A9A2.~ (LED_BL), ~.1
unnamed: 1A9A2A1.1, ~.1
unnamed: 1A9A2DS1.P1 (CON1), ~.1
unnamed: 1A9A2DS1.P2 (LED_BL), ~.1
unnamed: 1A10A1.~, ~.1, ~.2
unnamed: 1A10A2.~, ~.1, ~.2
RDDI_BRT_A: 1A9A1SW2.A, 1A9A1W3P5.1
RDDI_BRT_B: 1A9A1SW2.B, 1A9A1W3P5.3
RDDI_BRT_GND: 1A9A1SW2.C, 1A9A1W3P5.2
RDDI_CONT_A: 1A9A1SW3.A, 1A9A1W4P4.1
RDDI_CONT_B: 1A9A1SW3.B, 1A9A1W4P4.3
RDDI_CONT_GND: 1A9A1SW3.C, 1A9A1W4P4.2
RDDI_ROT_DAY: 1A9A1SW1.3, 1A9A1W2P6.3
RDDI_ROT_GND: 1A9A1SW1.C (COM), 1A9A1W2P6.4
RDDI_ROT_NIGHT: 1A9A1SW1.2, 1A9A1W2P6.2
RDDI_ROT_OFF: 1A9A1SW1.1, 1A9A1W2P6.1
REJ_2: 1A7SW1.3, 1A7W2P4.2
REJ_NORM: 1A7SW1.1, 1A7W2P4.1
REWI_FIRE_SW: 1A9A1W5P8.1
REWI_GND: 1A9A1W5P8.3
REWI_MC_SW: 1A9A1W5P8.2
SCL_J3-4: 1A3.4 (GND), 1A9.4 (GND)
SDA_J3-3: 1A3.3 (A0), 1A9.3 (A0)
SPIN_+5V: 1A6RV1.1, 1A6W1P3.9
SPIN_GND: 1A6RV1.3, 1A6SW1.2, 1A6SW2.2 (B), 1A6W1P3.8
SPIN_RCVY: 1A6SW2.1 (A), 1A6W1P3.4
UIP_BL_CH1: 1A1W2.1, (1A1W2).1
WB_OFF: 1A7SW3.3, 1A7W2P4.5
WB_WB: 1A7SW3.1, 1A7W2P4.4
~12V~_J3-1: 1A3.1 (12V_PWM), 1A9.1 (12V_PWM)
~D3_SCL~_J3-4: 1A2.4 (D7), 1A6.4 (D7), 1A7.4 (D7)
~D6-A7~_J4-2: 1A7.2 (+3.3V)
~D9-A9~_J4-8: 1A7.8 (GND)
~D10-A10~_J4-7: 1A7.7 (A0)
~D10~_A10_J5-3: 1A3.3 (A0), 1A9.3 (A0)

Notes on the sheet:
DRAFT - DO NOT USE
1. REFERENCE ABSIS-SPEC-001 FOR ABSIS CABLE SPECIFICATION.
NOTES: (UNLESS OTHERWISE SPECIFIED)
GND_J3-12
+5V_J3-11
GND_J3-10
+5V_J3-9
GND_J3-8
A0_J3-7
D4-A6_J3-6
A1_J3-5
~D3_SCL~_J3-4
A2_J3-3
D2-SDA_J3-2
A3_J3-1
READY_SW
GND
AA_SW
AG_SW
MASTER ARM
~12V~_J3-1
+5V_J3-2
SDA_J3-3
SCL_J3-4
IRQ_J3-5
GND_J3-6
D8_J5-1
GND_J5-2
~D10~_A10_J5-3
D4_A4_J4-1
GND_J4-2
D7_J4-3
A2_J6-1
A1_J6-2
A0_J6-3
GND_J6-4
D14_J8-1
D16_J8-2
GND_J8-3
L DDI/EWI
R DDI/EWI
GND_J4-12
+5V_J4-11
GND_J4-10
+5V_J4-9
~D9-A9~_J4-8
~D10-A10~_J4-7
D8-A8_J4-6
D16-MOSI_J4-5
D7_J4-4
D14-MISO_J4-3
~D6-A7~_J4-2
D15-SCK_J4-1
ATT_AUTO
WB_VID
REJ_1
NIGHT
RDR
HUD PANEL
IR_NORM
SPIN_NORM
SPIN RCVY
BACKLIGHTING PANELS
UIP HID MASTER
UIP USB HUB #2
(1A1W5)
USB HUBS
UFC
(ABSIS-CA-J-XXX)
L DDI DISPLAY
INTERNAL DISPLAYS
R DDI DISPLAY
ADF_OFF
UP-FRONT CONTROL PANEL (UFC)
FUTURE EXP
TO R LIP BULKHEAD
TO L LIP BULKHEAD
