Exprezz0/F-18C_Simulator/ECAD/PCBs/OH_Specific/Backlighting_Type B/ECS Panel PCB V2.sch

## KiCad design ECAD/PCBs/OH_Specific/Backlighting_Type B/ECS Panel PCB V2.sch (2023-01-02)

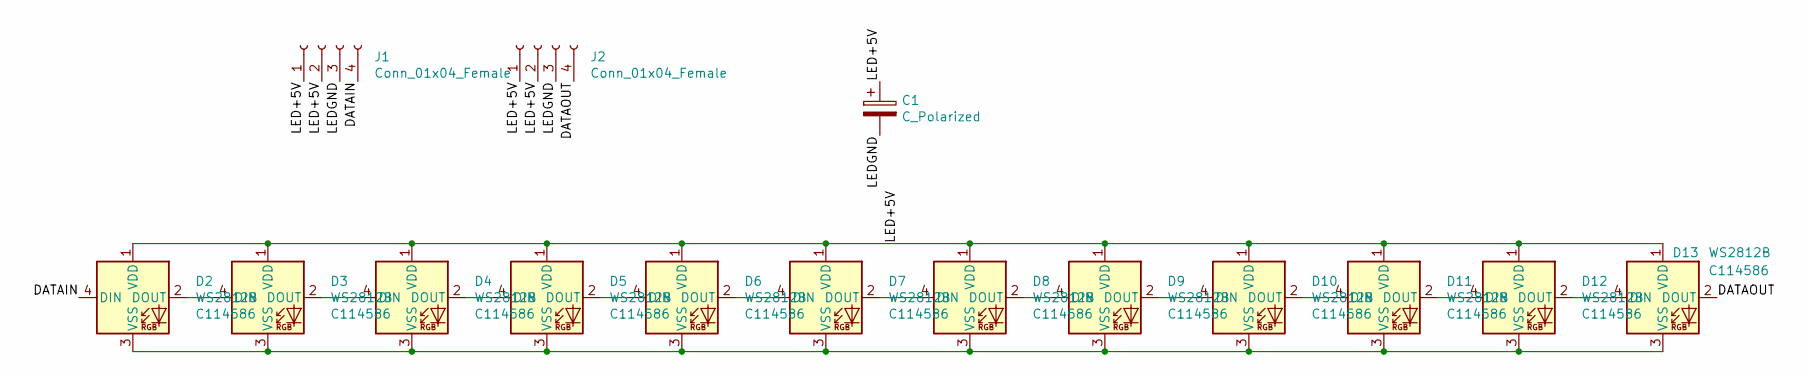
[picture p359: schematic ECS Panel PCB V2.sch]

Parts:
C1: C_Polarized; CP_Elec_8x10
D2, D3, D4, D5, D6, D7, D8, D9, D10, D11, D12, D13: WS2812B; LED_WS2812B_PLCC4_5.0x5.0mm_P3.2mm; LCSC Part Number C114586
J1, J2: Conn_01x04_Female; Molex_Mini-Fit_Jr_5566-04A_2x02_P4.20mm_Vertical

Connections:
DATAIN: D2.4 (DIN), J1.4
DATAOUT: D13.2 (DOUT), J2.4
LED+5V: C1.1, D2.1 (VDD), D3.1 (VDD), D4.1 (VDD), D5.1 (VDD), D6.1 (VDD), D7.1 (VDD), D8.1 (VDD), D9.1 (VDD), D10.1 (VDD), D11.1 (VDD), D12.1 (VDD), D13.1 (VDD), J1.1, J1.2, J2.1, J2.2
LEDGND: C1.2, J1.3, J2.3
unnamed: D2.2 (DOUT), D3.4 (DIN)
unnamed: D3.2 (DOUT), D4.4 (DIN)
unnamed: D4.2 (DOUT), D5.4 (DIN)
unnamed: D5.2 (DOUT), D6.4 (DIN)
unnamed: D6.2 (DOUT), D7.4 (DIN)
unnamed: D7.2 (DOUT), D8.4 (DIN)
unnamed: D8.2 (DOUT), D9.4 (DIN)
unnamed: D10.2 (DOUT), D11.4 (DIN)
unnamed: D2.3 (VSS), D3.3 (VSS), D4.3 (VSS), D5.3 (VSS), D6.3 (VSS), D7.3 (VSS), D8.3 (VSS), D9.3 (VSS), D10.3 (VSS), D11.3 (VSS), D12.3 (VSS), D13.3 (VSS)
unnamed: D9.2 (DOUT), D10.4 (DIN)
unnamed: D11.2 (DOUT), D12.4 (DIN)
unnamed: D12.2 (DOUT), D13.4 (DIN)
