Exprezz0/F-18C_Simulator/ECAD/PCBs/OH_Specific/Backlighting_Type A/Power_Distro_PCB_V2/Power Distro PCB V2.sch

## KiCad design ECAD/PCBs/OH_Specific/Backlighting_Type A/Power_Distro_PCB_V2/Power Distro PCB V2.sch (2023-01-02)

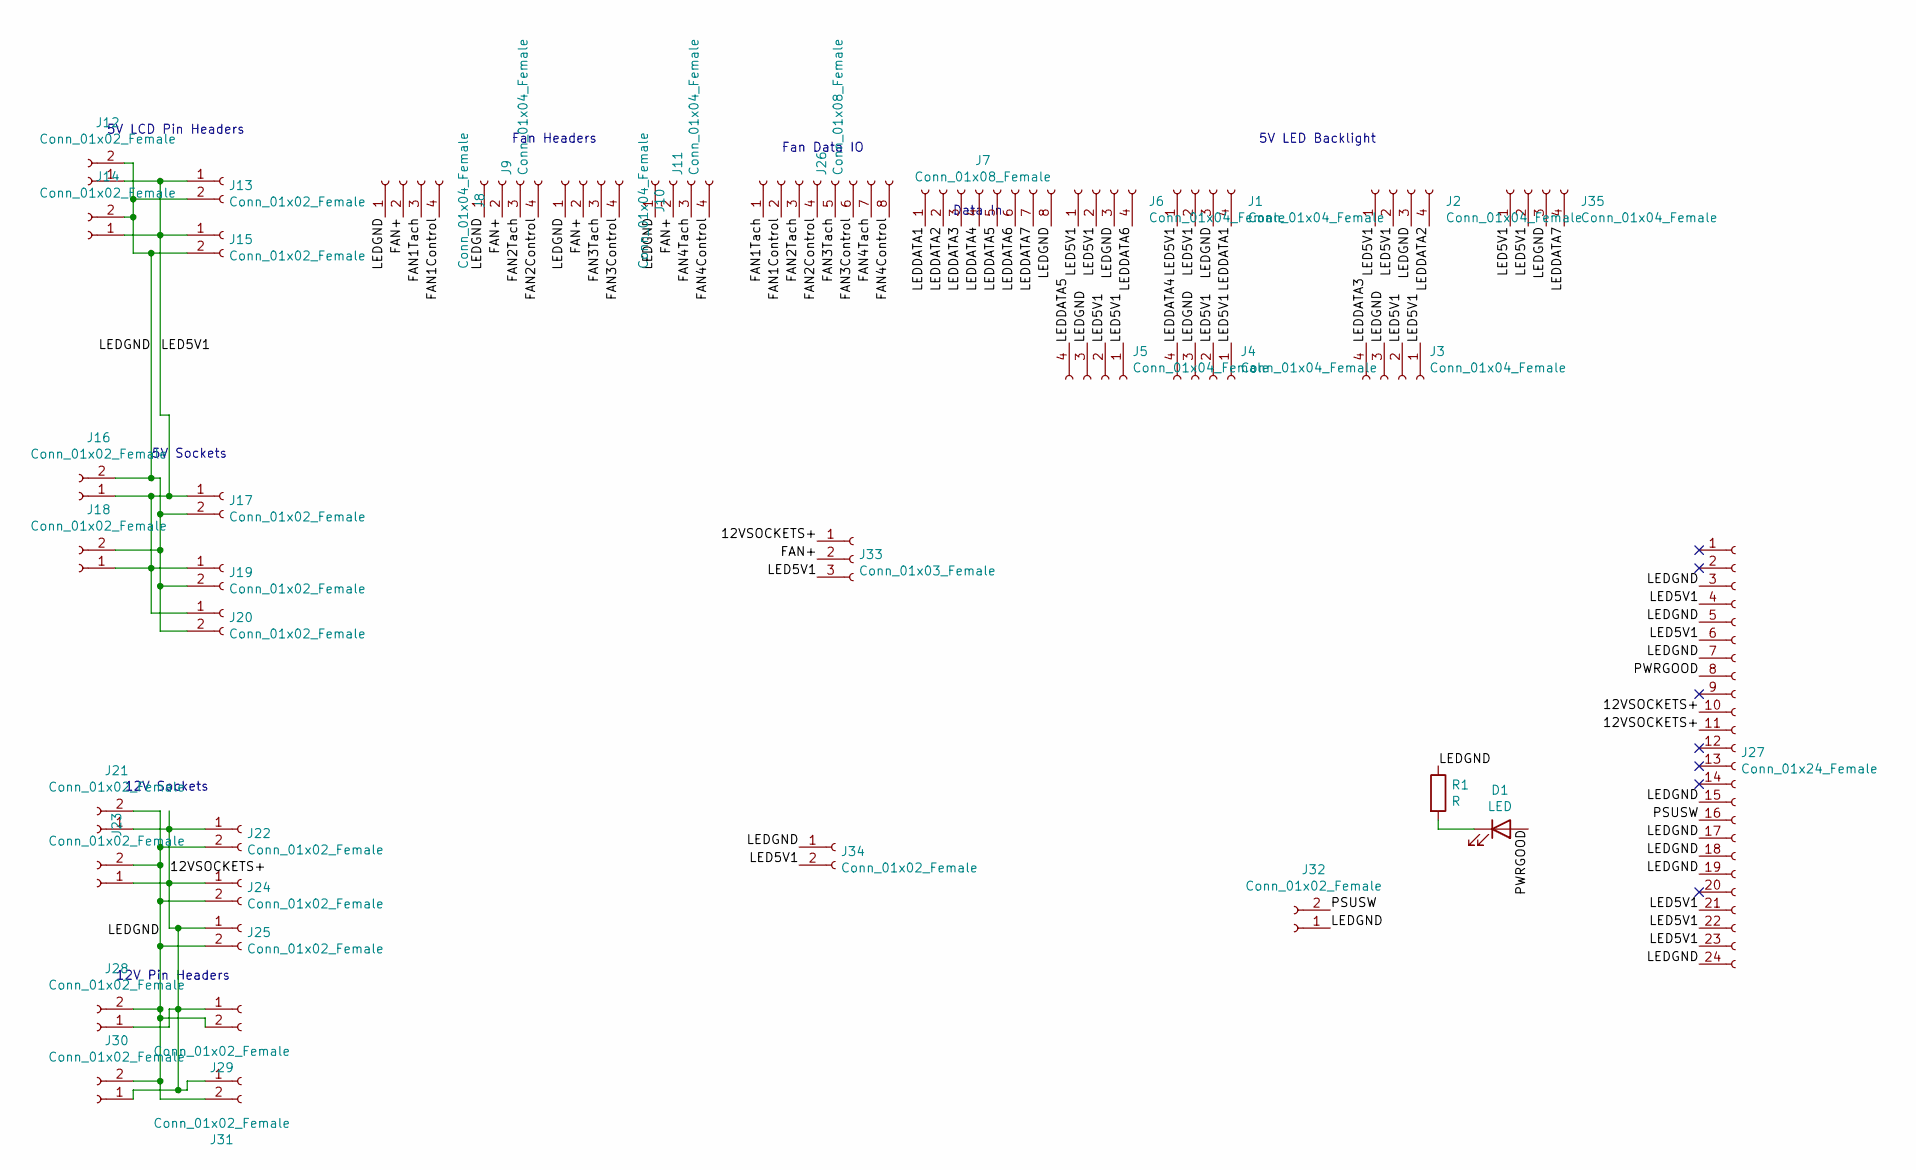
[picture p360: schematic Power Distro PCB V2.sch]

Parts:
D1: LED; LED_D3.0mm
J1, J2, J3, J4, J5, J6, J35: Conn_01x04_Female; Molex_Mini-Fit_Jr_5566-04A_2x02_P4.20mm_Vertical
J7: Conn_01x08_Female; PinHeader_1x08_P2.54mm_Vertical
J8, J9, J10, J11: Conn_01x04_Female; FanPinHeader_1x04_P2.54mm_Vertical
J12, J13, J14, J15, J28, J29, J30, J31, J32: Conn_01x02_Female; Molex_KK-254_AE-6410-02A_1x02_P2.54mm_Vertical
J16, J17, J18, J19, J20, J21, J22, J23, J24, J25: Conn_01x02_Female; BarrelJack_Horizontal
J26: Conn_01x08_Female; PinHeader_2x04_P2.54mm_Vertical
J27: Conn_01x24_Female; Molex_Mini-Fit_Jr_5566-24A_2x12_P4.20mm_Vertical
J33: Conn_01x03_Female; PinHeader_1x03_P2.54mm_Vertical
J34: Conn_01x02_Female; AMASS_XT60-M_1x02_P7.20mm_Vertical
R1: R; R_Axial_DIN0207_L6.3mm_D2.5mm_P7.62mm_Horizontal

Connections:
12VSOCKETS+: J21.1, J22.1, J23.1, J24.1, J25.1, J27.10, J27.11, J28.1, J29.1, J30.1, J31.1, J33.1
FAN1Control: J8.4, J26.2
FAN1Tach: J8.3, J26.1
FAN2Control: J9.4, J26.4
FAN2Tach: J9.3, J26.3
FAN3Control: J10.4, J26.6
FAN3Tach: J10.3, J26.5
FAN4Control: J11.4, J26.8
FAN4Tach: J11.3, J26.7
FAN+: J8.2, J9.2, J10.2, J11.2, J33.2
LED5V1: J1.1, J1.2, J2.1, J2.2, J3.1, J3.2, J4.1, J4.2, J5.1, J5.2, J6.1, J6.2, J12.1, J13.1, J14.1, J15.1, J16.1, J17.1, J18.1, J19.1, J20.1, J27.4, J27.6, J27.21, J27.22, J27.23, J33.3, J34.2, J35.1, J35.2
LEDDATA1: J1.4, J7.1
LEDDATA2: J2.4, J7.2
LEDDATA3: J3.4, J7.3
LEDDATA4: J4.4, J7.4
LEDDATA5: J5.4, J7.5
LEDDATA6: J6.4, J7.6
LEDDATA7: J7.7, J35.4
LEDGND: J1.3, J2.3, J3.3, J4.3, J5.3, J6.3, J7.8, J8.1, J9.1, J10.1, J11.1, J12.2, J13.2, J14.2, J15.2, J16.2, J17.2, J18.2, J19.2, J20.2, J21.2, J22.2, J23.2, J24.2, J25.2, J27.3, J27.5, J27.7, J27.15, J27.17, J27.18, J27.19, J27.24, J28.2, J29.2, J30.2, J31.2, J32.1, J34.1, J35.3, R1.1
unnamed: D1.1 (K), R1.2
PSUSW: J27.16, J32.2
PWRGOOD: D1.2 (A), J27.8

Notes on the sheet:
12V Sockets
5V Sockets
Fan Headers
5V LCD Pin Headers
5V LED Backlight
Data In
Fan Data IO
12V Pin Headers
